spikeon/exoguitar/models/Back/Generator/photos/IMG_5319.JPEG

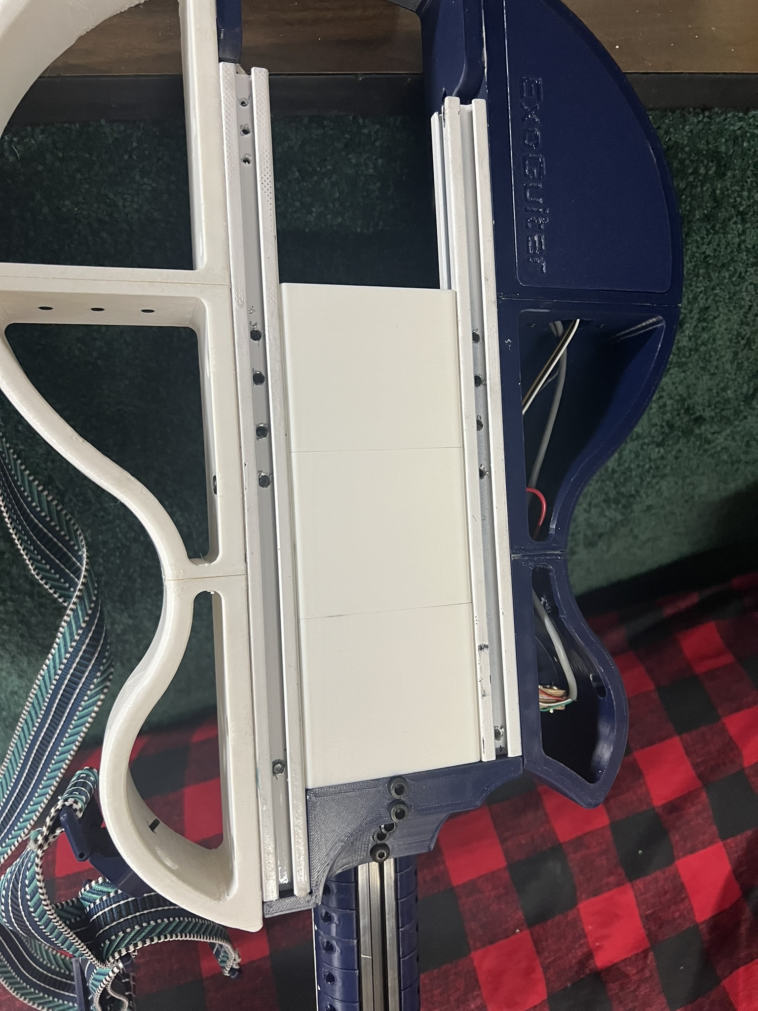
models/Back/Generator/photos/IMG_5319.JPEG
