spikeon/exoguitar/models/Bridge/Alnicov 6 Strings Saddle Headless/photos/IMG_4152.JPEG

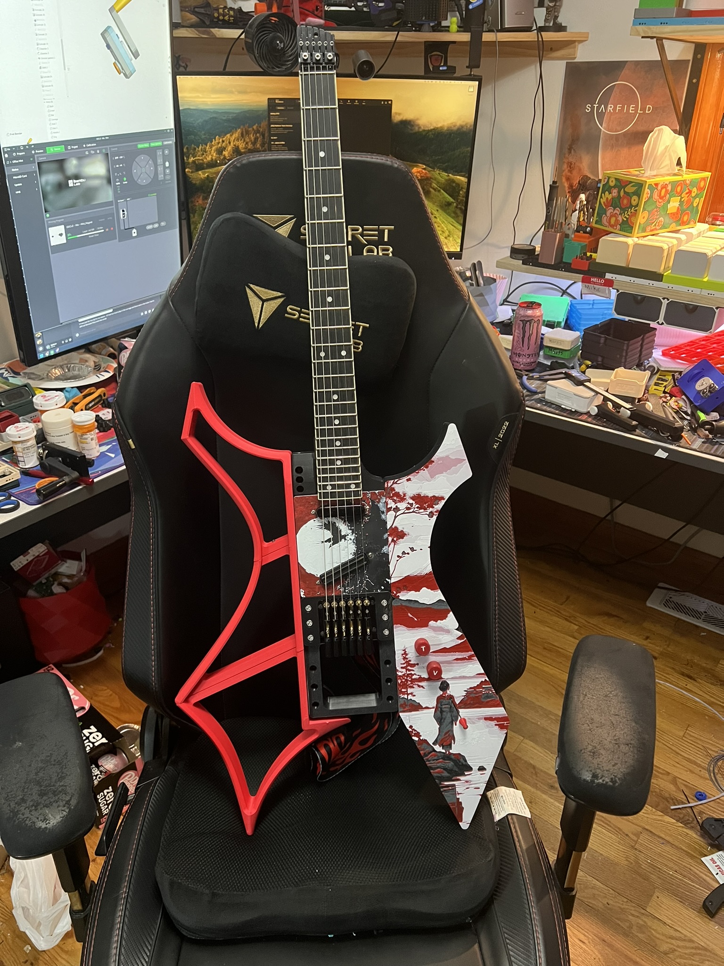
models/Bridge/Alnicov 6 Strings Saddle Headless/photos/IMG_4152.JPEG
