spikeon/exoguitar/models/Bridge/Alnicov 6 Strings Saddle Headless/photos/thumb.wide.png

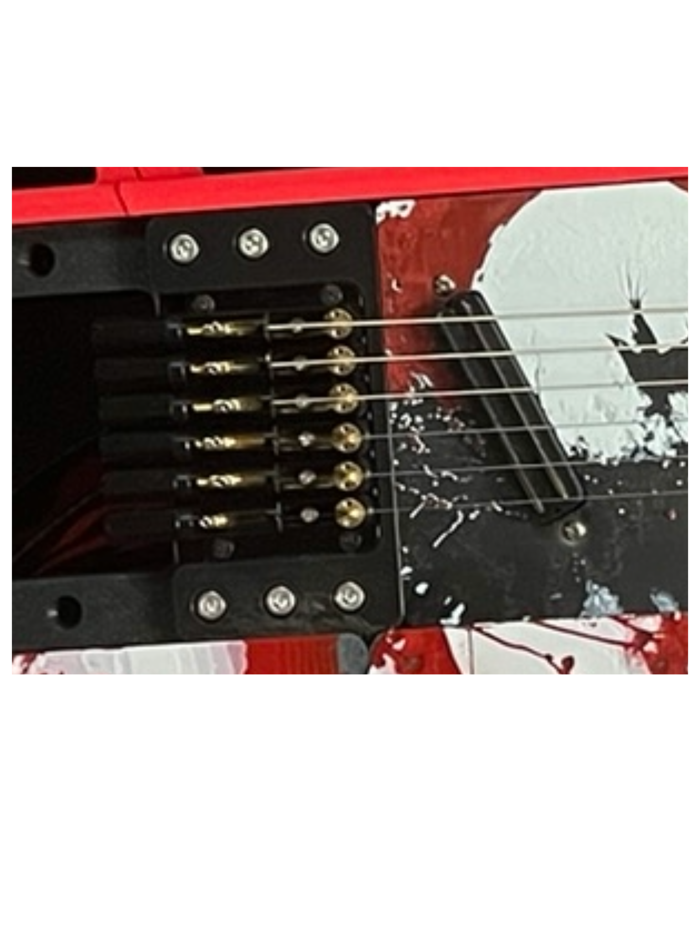
models/Bridge/Alnicov 6 Strings Saddle Headless/photos/thumb.wide.png
