spikeon/exoguitar/models/Bridge/Bearing Bridge/photos/thumb.wide.png

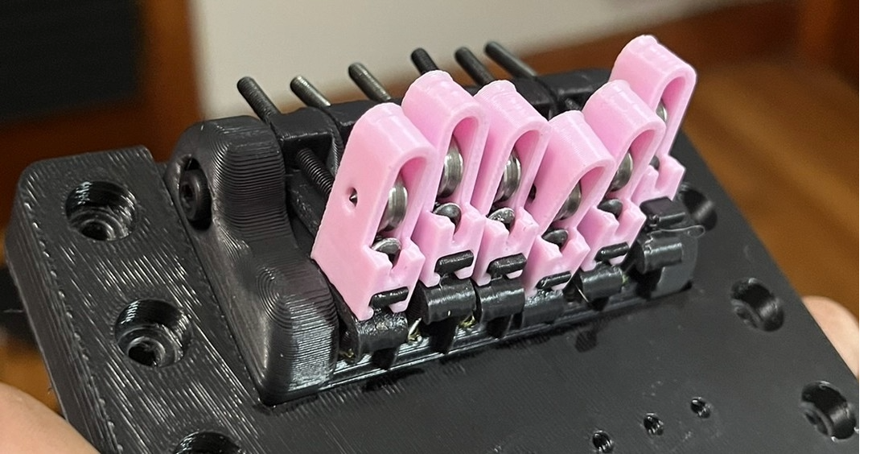
models/Bridge/Bearing Bridge/photos/thumb.wide.png
