spikeon/exoguitar/models/Bridge/Guyker Worm Bridge Plate/photos/thumb.wide.png

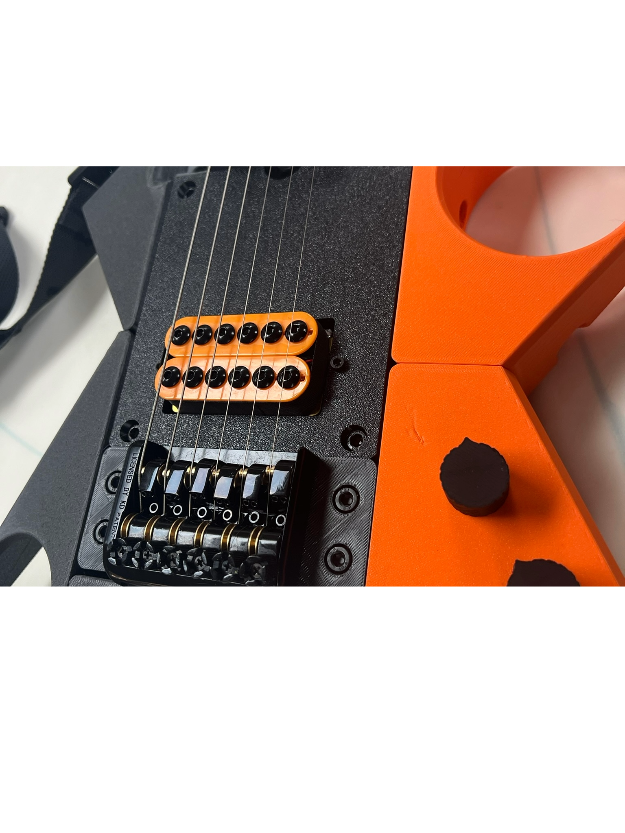
models/Bridge/Guyker Worm Bridge Plate/photos/thumb.wide.png
