spikeon/exoguitar/models/Bridge/Headless Bridge Plate/photos/thumb.wide.png

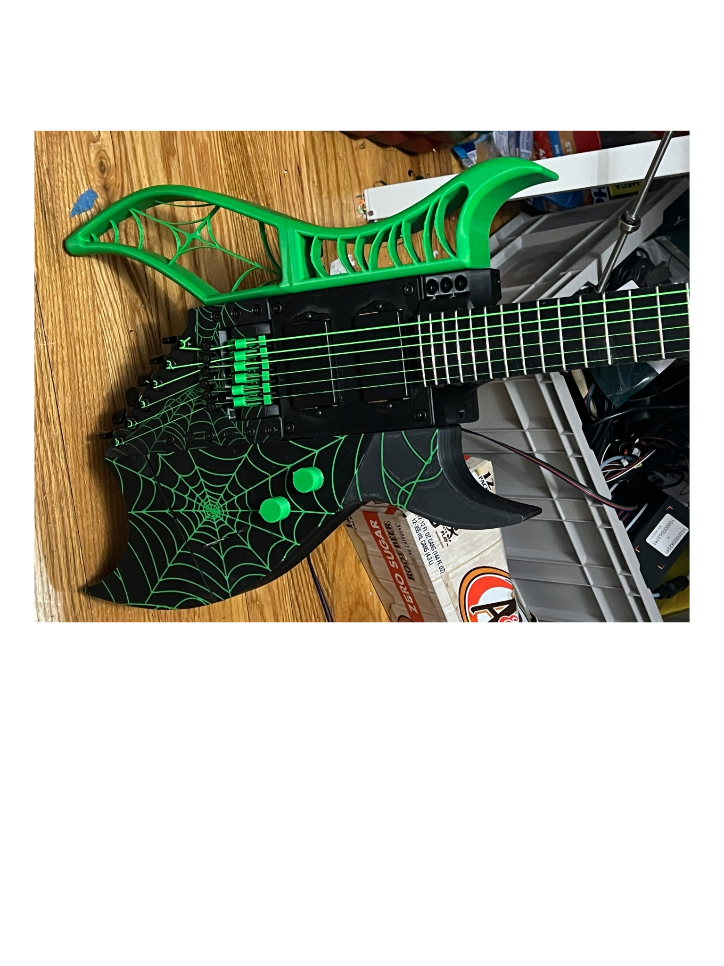
models/Bridge/Headless Bridge Plate/photos/thumb.wide.png
