spikeon/exoguitar/models/Bridge/OVSAL Headless Bridge Plate/photos/IMG_4946.JPEG

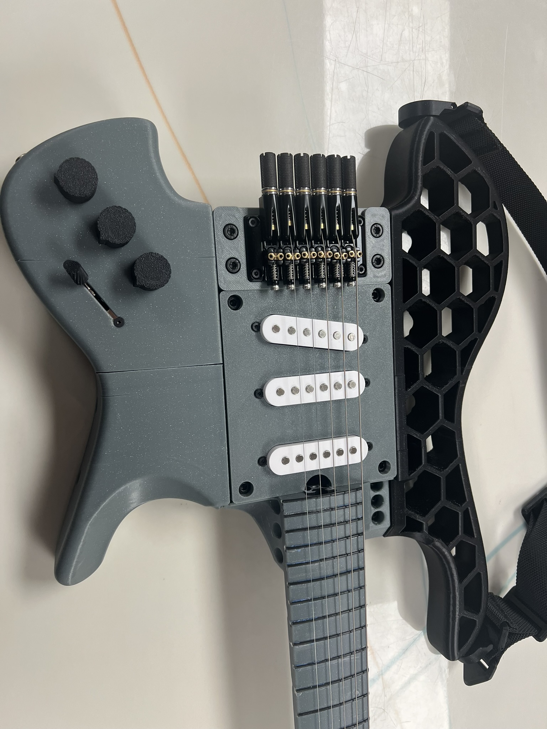
models/Bridge/OVSAL Headless Bridge Plate/photos/IMG_4946.JPEG
