spikeon/exoguitar/models/Bridge/OVSAL Headless Bridge Plate/photos/IMG_4947.JPEG

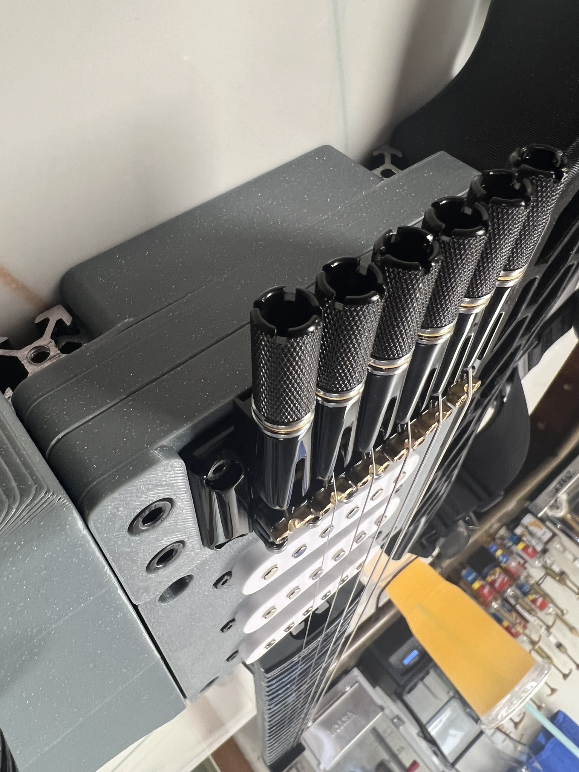
models/Bridge/OVSAL Headless Bridge Plate/photos/IMG_4947.JPEG
