spikeon/exoguitar/models/Bridge/Telecaster Plate/photos/IMG_4955 (1).JPEG

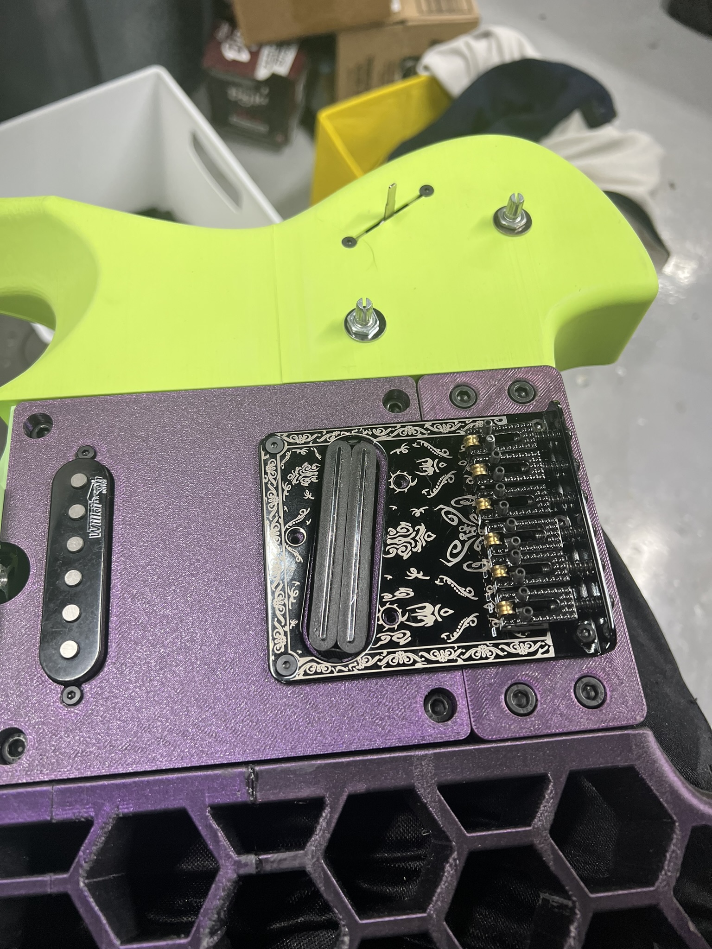
models/Bridge/Telecaster Plate/photos/IMG_4955 (1).JPEG
