spikeon/exoguitar/models/Bridge/Telecaster Plate/photos/IMG_5153.JPEG

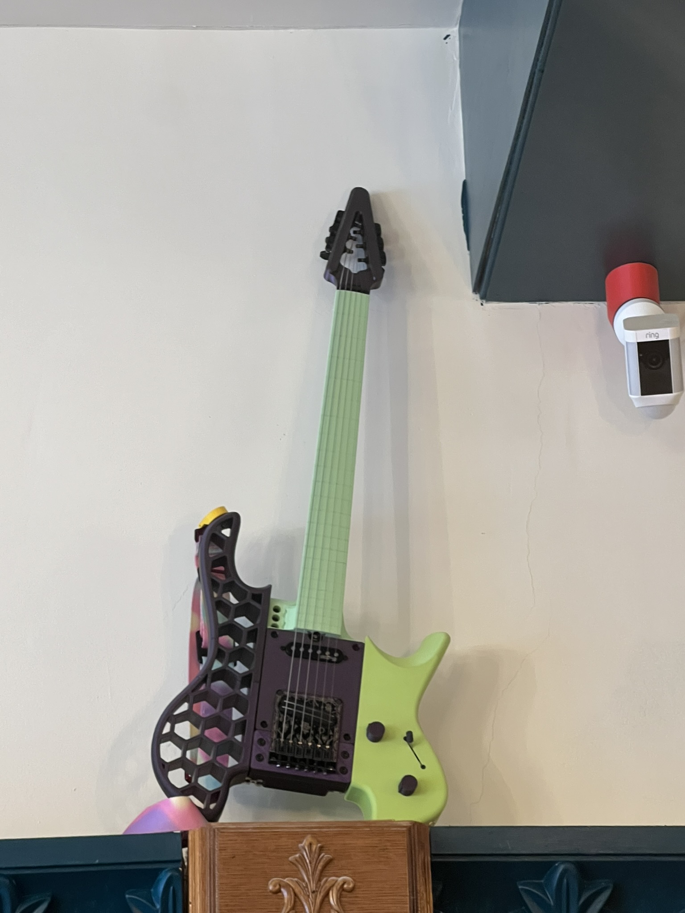
models/Bridge/Telecaster Plate/photos/IMG_5153.JPEG
