spikeon/exoguitar/models/Bridge/Tremelo/photos/IMG_4668.JPEG

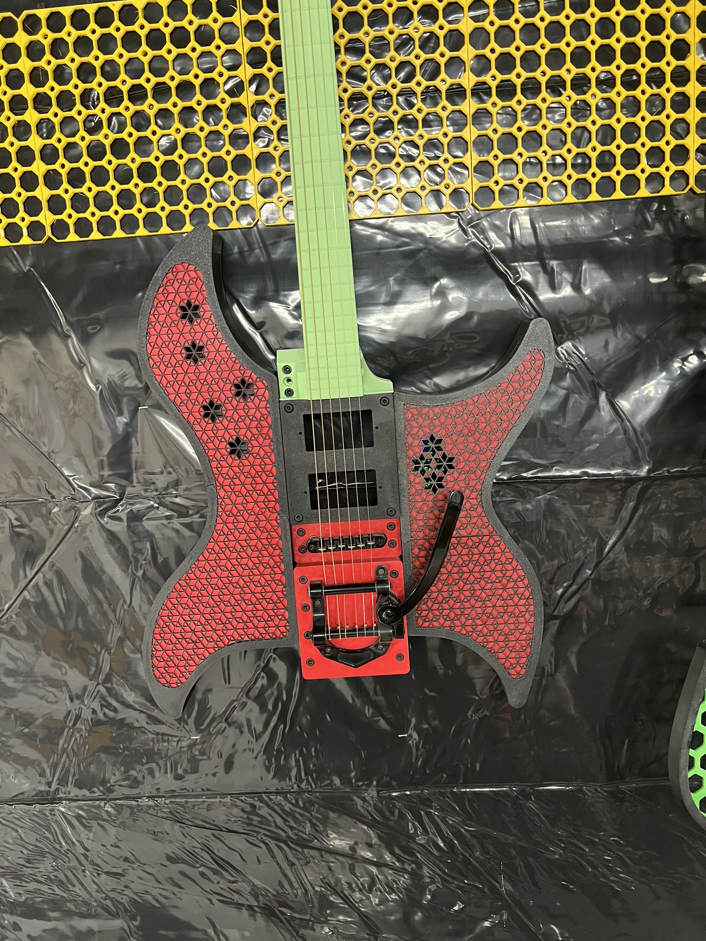
models/Bridge/Tremelo/photos/IMG_4668.JPEG
