spikeon/exoguitar/models/Bridge/Tremelo/photos/IMG_4672.JPEG

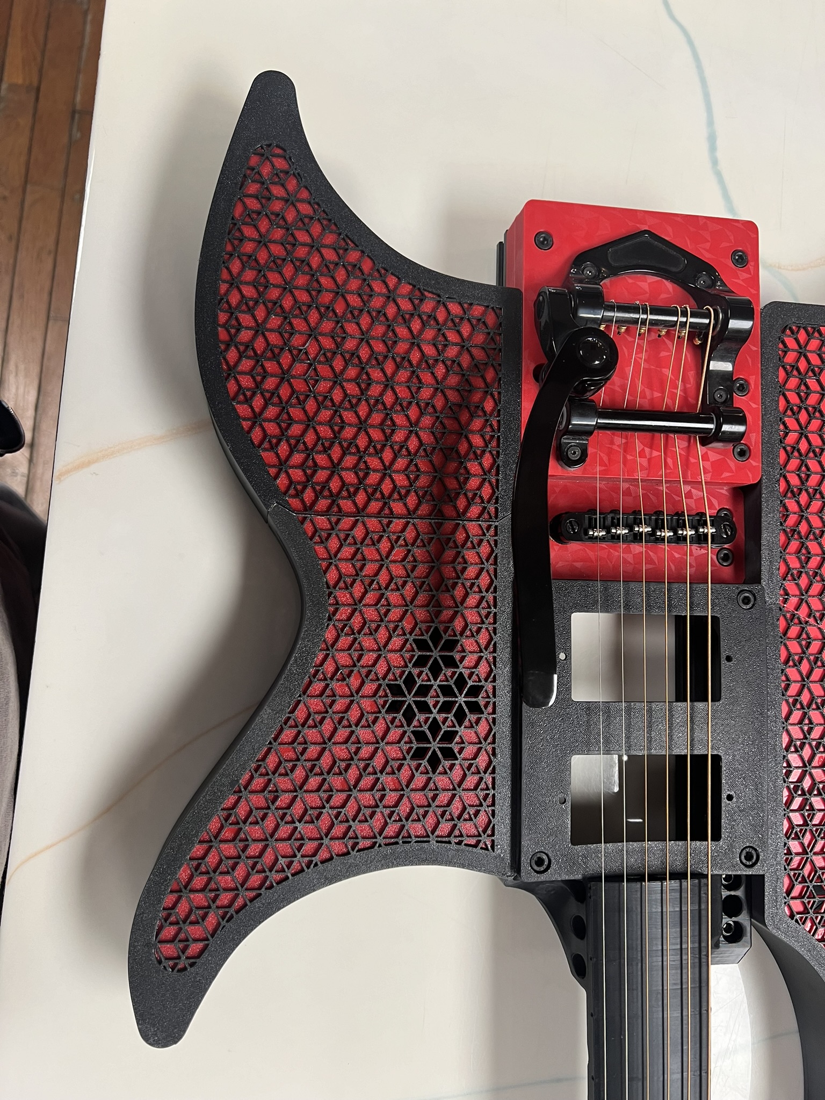
models/Bridge/Tremelo/photos/IMG_4672.JPEG
