spikeon/exoguitar/models/Bridge/Tremelo/photos/IMG_4673.JPEG

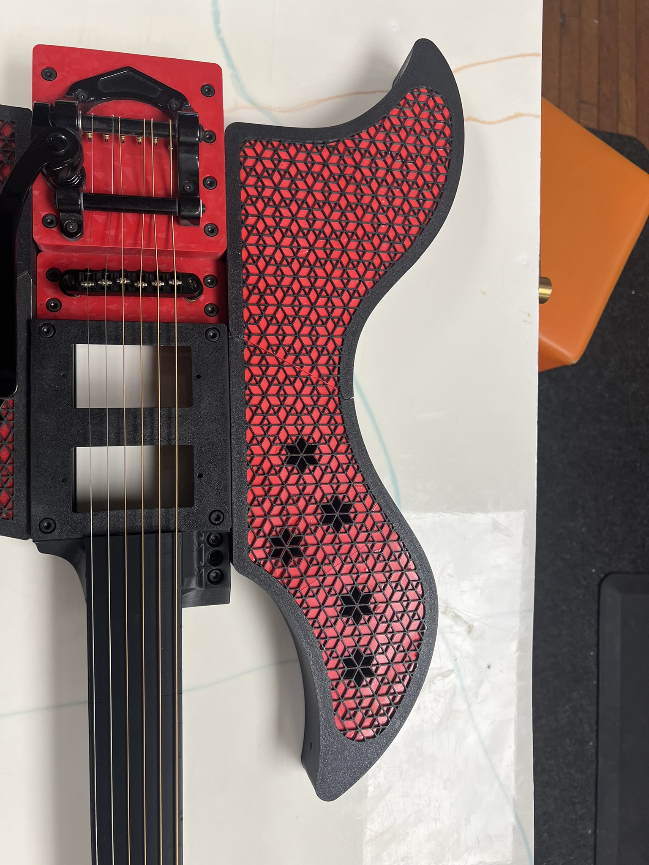
models/Bridge/Tremelo/photos/IMG_4673.JPEG
