spikeon/exoguitar/models/Bridge/Tremelo/photos/thumb.wide.png

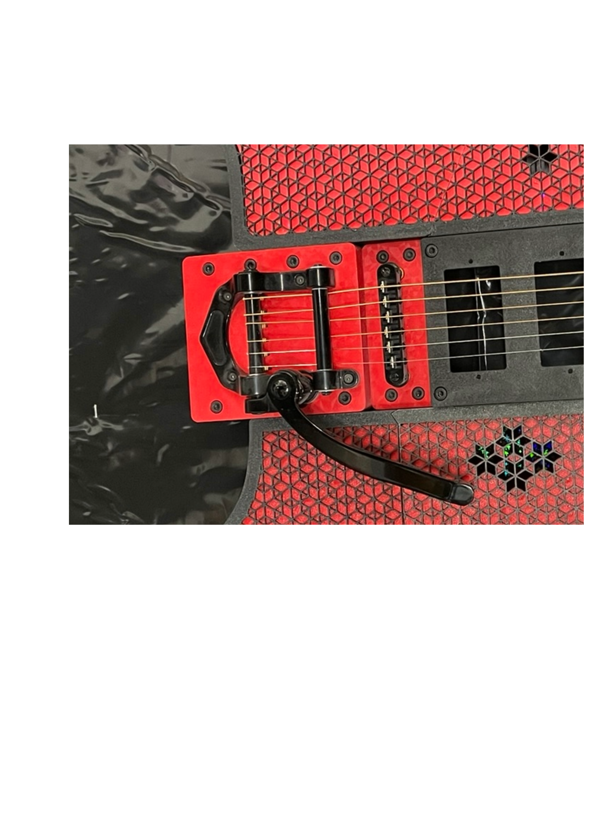
models/Bridge/Tremelo/photos/thumb.wide.png
