spikeon/exoguitar/models/Extras/Sanding Jig/photos/IMG_4849.JPEG

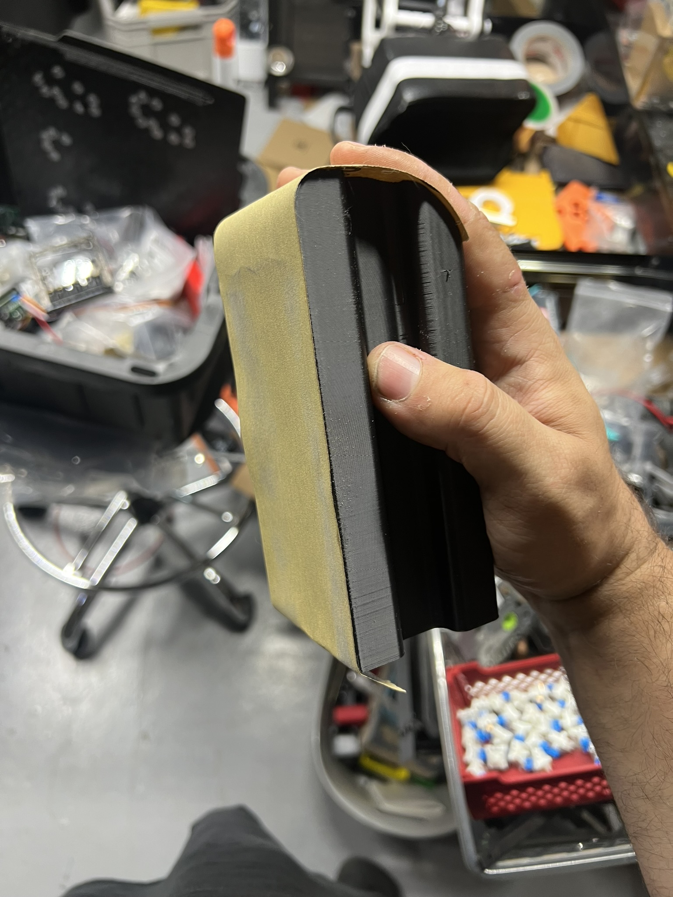
models/Extras/Sanding Jig/photos/IMG_4849.JPEG
