spikeon/exoguitar/models/Extras/Sanding Jig/photos/IMG_4850.JPEG

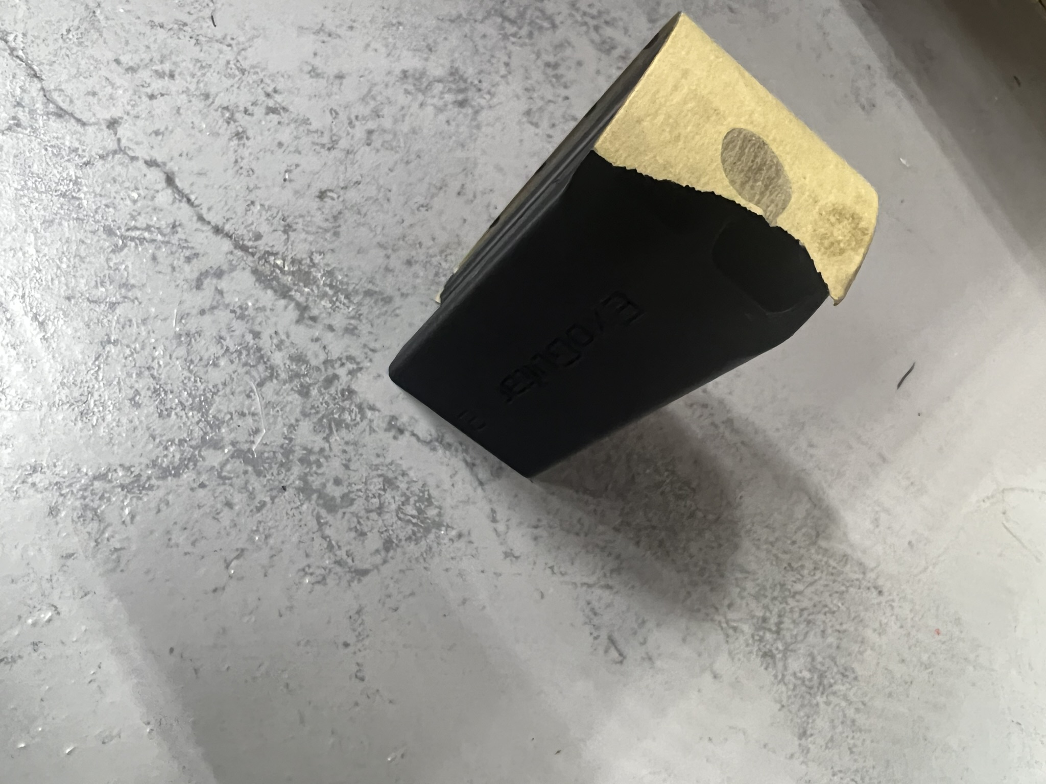
models/Extras/Sanding Jig/photos/IMG_4850.JPEG
