spikeon/exoguitar/models/Extras/Sanding Jig/photos/IMG_4852.JPEG

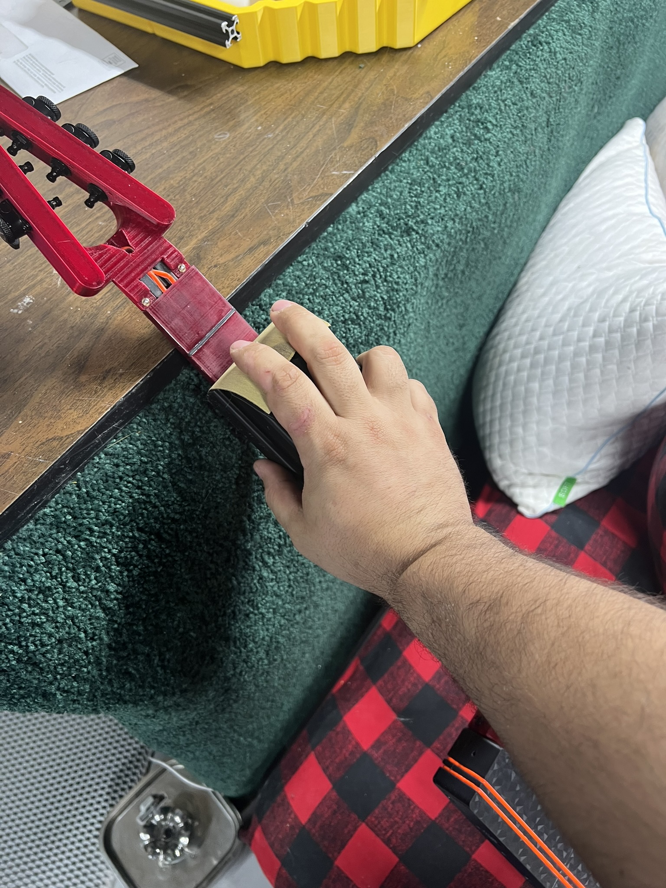
models/Extras/Sanding Jig/photos/IMG_4852.JPEG
