spikeon/exoguitar/models/Extras/Sanding Jig/photos/IMG_4853.JPEG

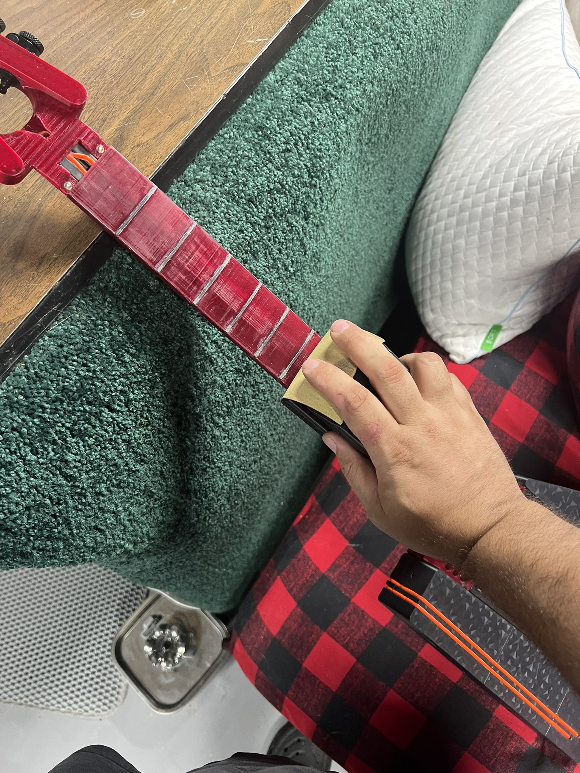
models/Extras/Sanding Jig/photos/IMG_4853.JPEG
