spikeon/exoguitar/models/Face Plates/Acoustic/ExoGuitar - Acoustic Core.png

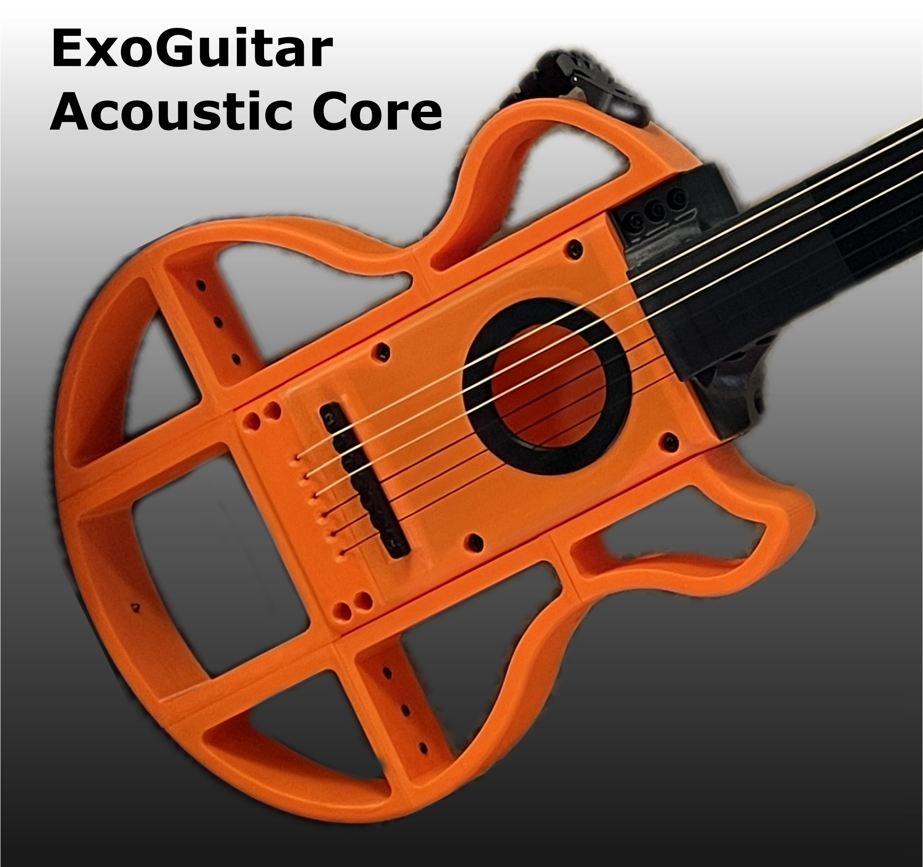
models/Face Plates/Acoustic/ExoGuitar - Acoustic Core.png
