spikeon/exoguitar/models/Face Plates/Dual Humbucker/photos/IMG_5579.JPEG

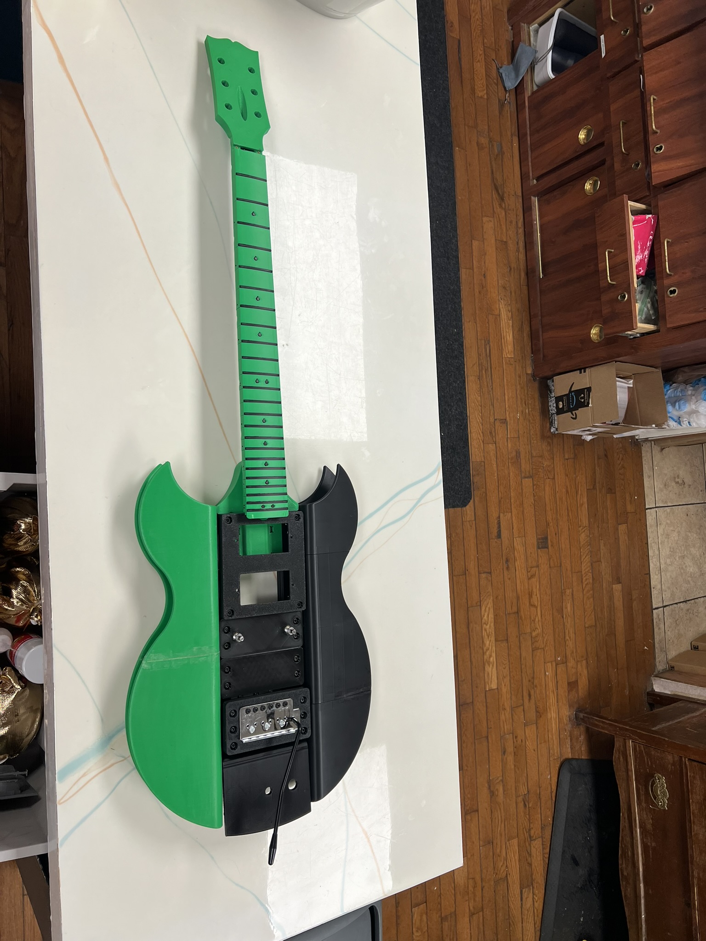
models/Face Plates/Dual Humbucker/photos/IMG_5579.JPEG
