spikeon/exoguitar/models/Face Plates/Dual Humbucker/photos/thumb.wide.png

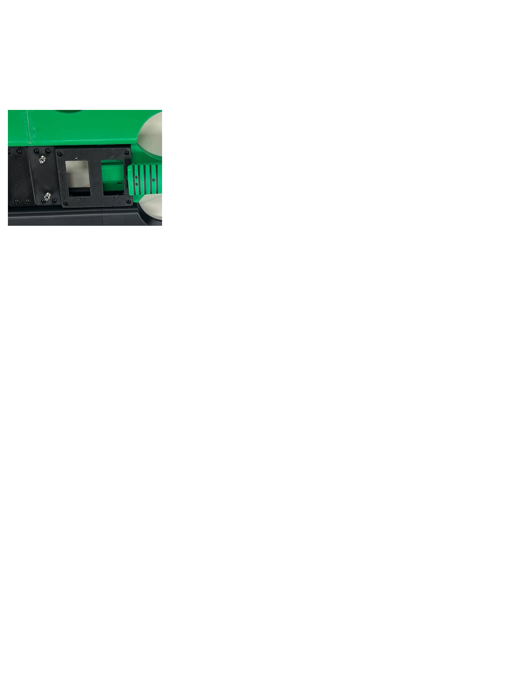
models/Face Plates/Dual Humbucker/photos/thumb.wide.png
