spikeon/exoguitar/models/Face Plates/Dual P90/photos/IMG_5286.JPEG

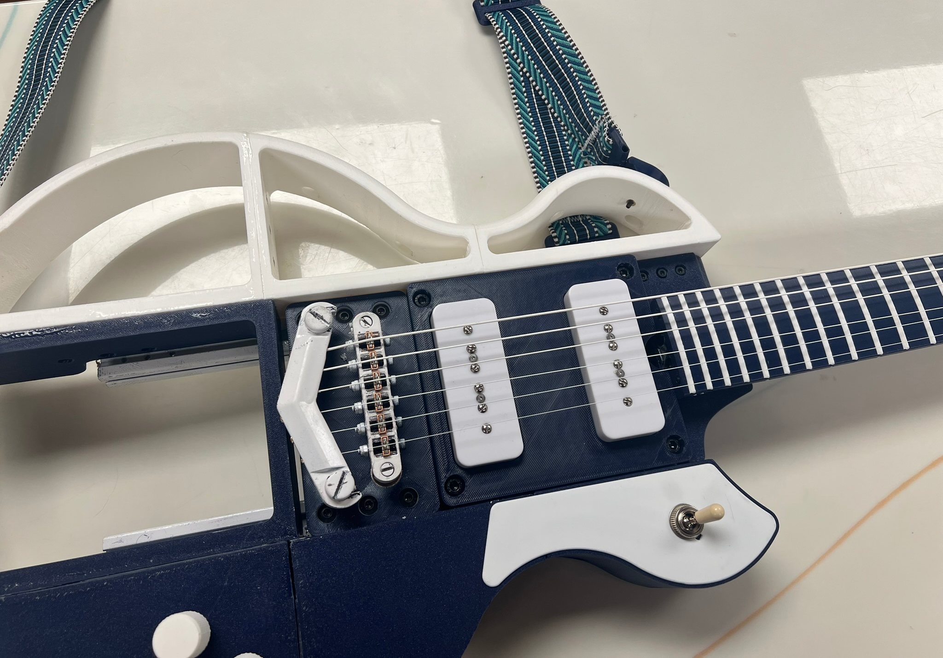
models/Face Plates/Dual P90/photos/IMG_5286.JPEG
