spikeon/exoguitar/models/Face Plates/Dual P90/photos/IMG_5287.JPEG

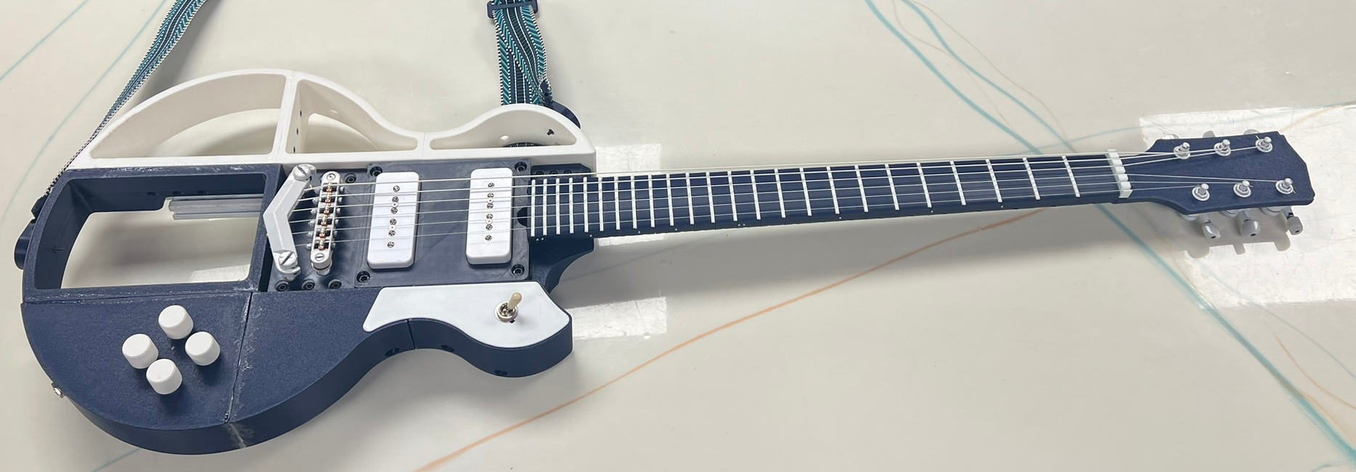
models/Face Plates/Dual P90/photos/IMG_5287.JPEG
