spikeon/exoguitar/models/Face Plates/Dual P90/photos/thumb.wide.JPEG

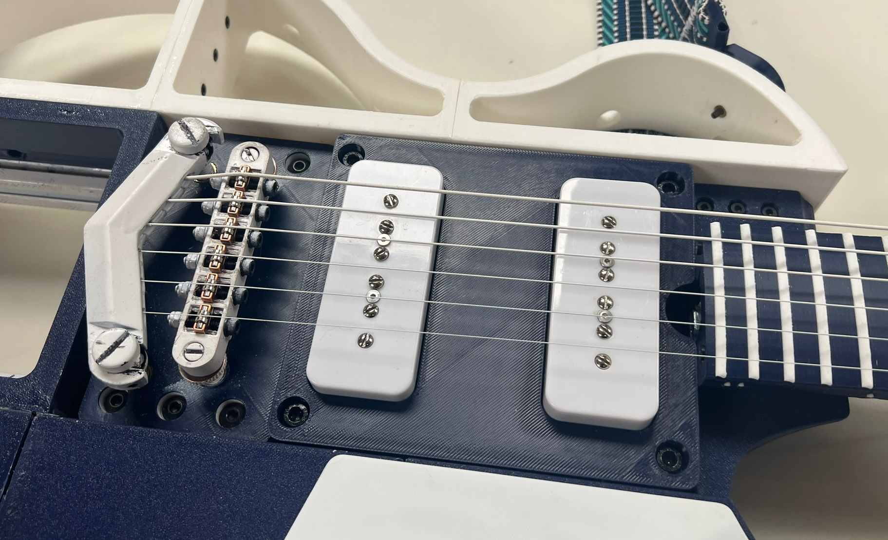
models/Face Plates/Dual P90/photos/thumb.wide.JPEG
