spikeon/exoguitar/models/Face Plates/Dual P90/photos/thumb.wide.png

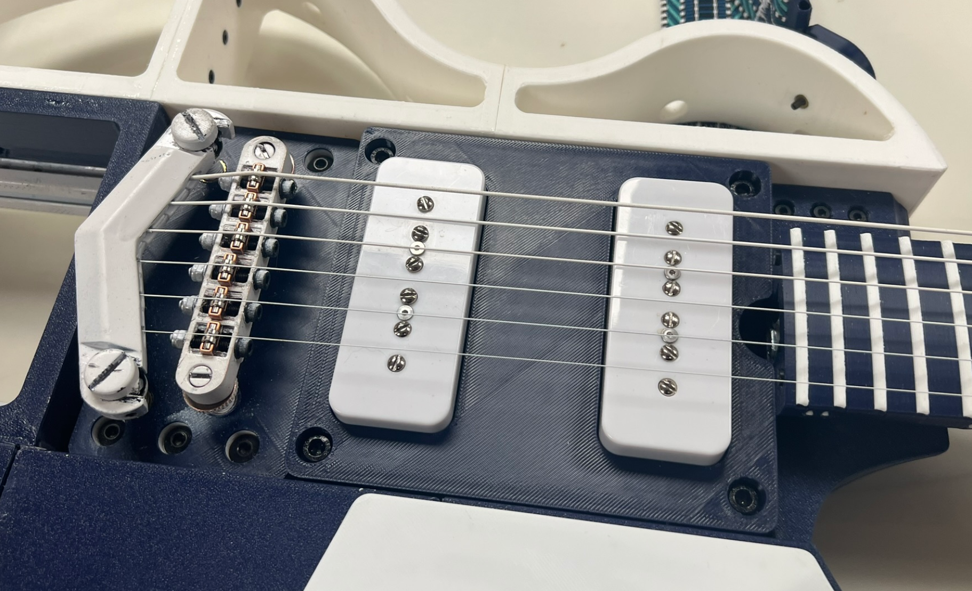
models/Face Plates/Dual P90/photos/thumb.wide.png
