spikeon/exoguitar/models/Face Plates/HSS/IMG_6287.JPEG

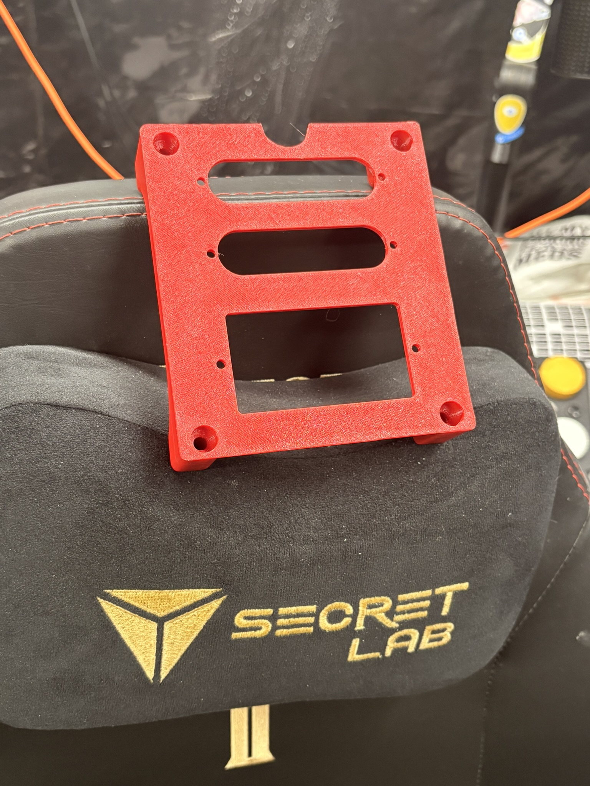
models/Face Plates/HSS/IMG_6287.JPEG
