spikeon/exoguitar/models/Face Plates/Single Humbucker - Bridge/photos/IMG_5298.JPEG

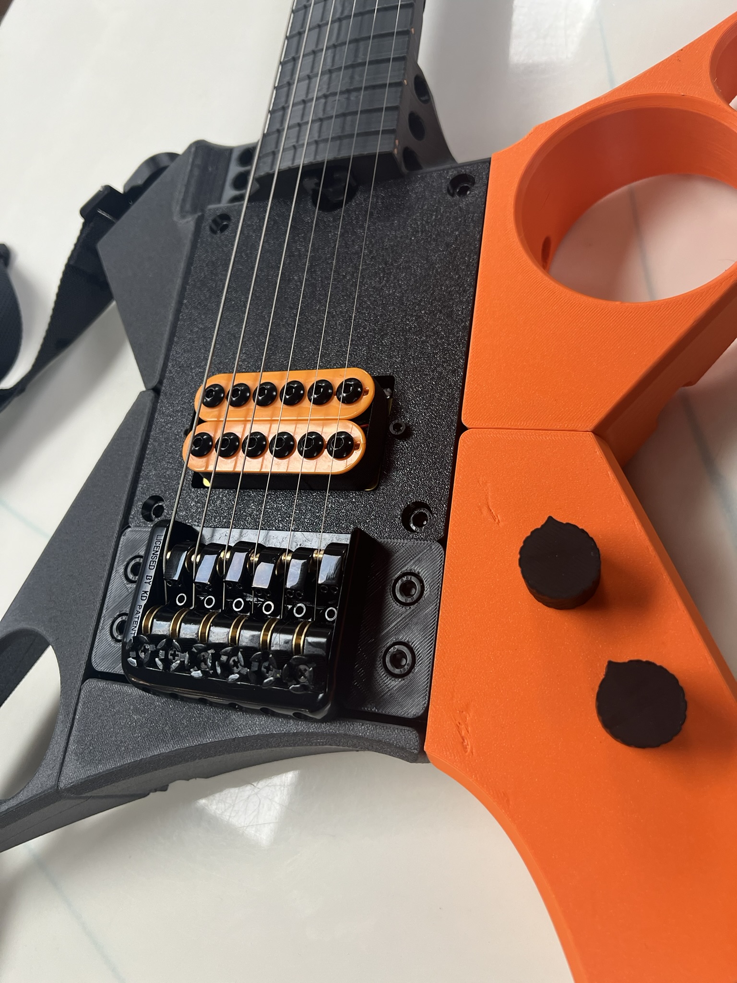
models/Face Plates/Single Humbucker - Bridge/photos/IMG_5298.JPEG
