spikeon/exoguitar/models/Face Plates/Single Humbucker - Centered/photos/IMG_5016.JPEG

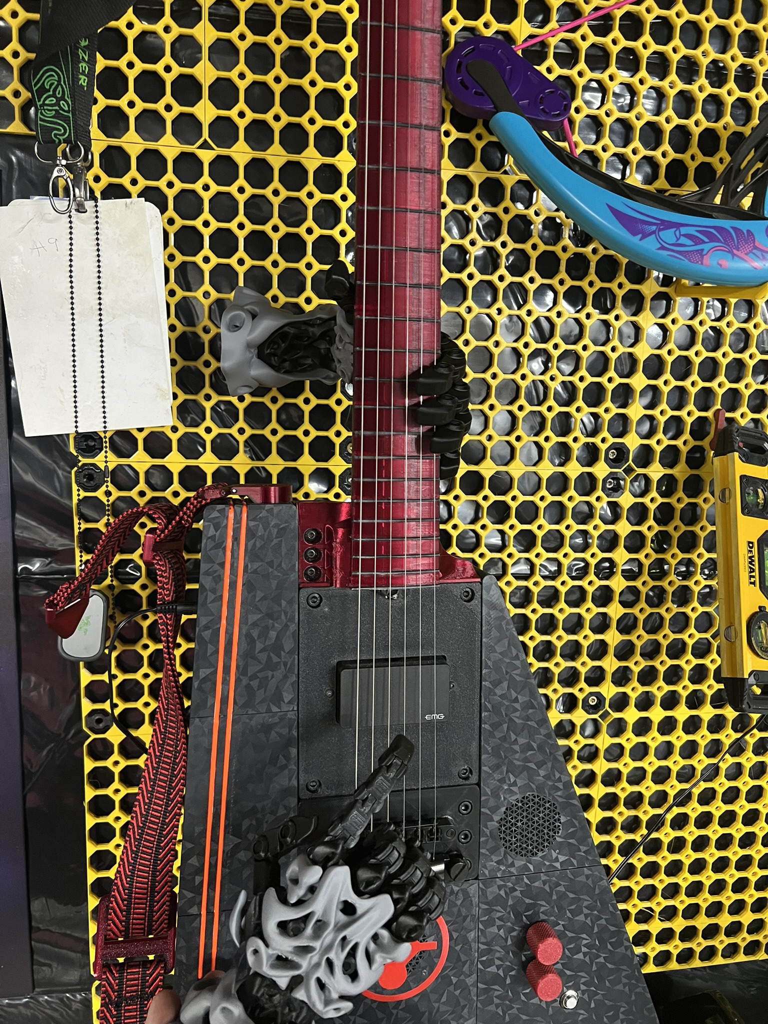
models/Face Plates/Single Humbucker - Centered/photos/IMG_5016.JPEG
