spikeon/exoguitar/models/Face Plates/Single Humbucker - Centered/photos/thumb.wide.png

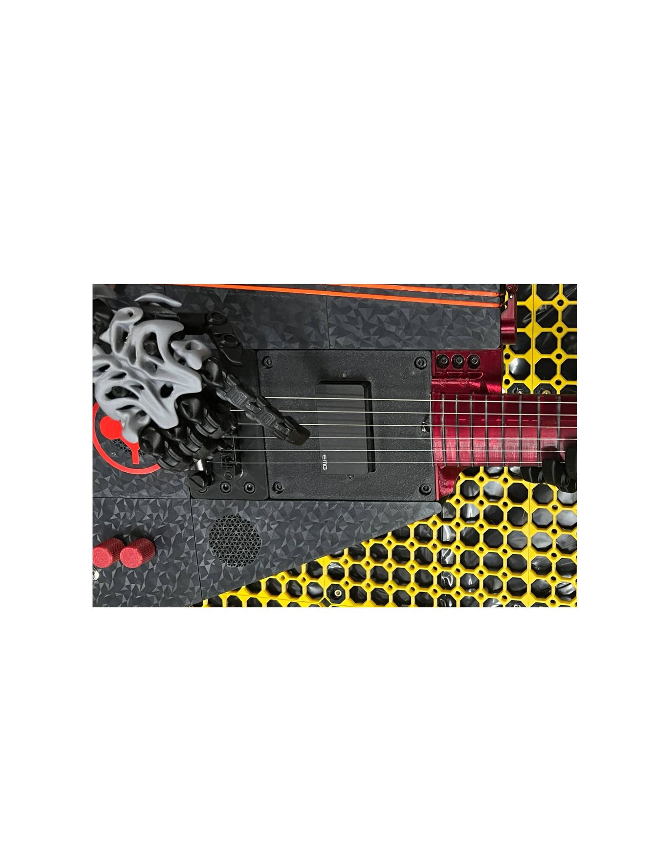
models/Face Plates/Single Humbucker - Centered/photos/thumb.wide.png
