spikeon/exoguitar/models/Face Plates/SSS/photos/IMG_4884.JPEG

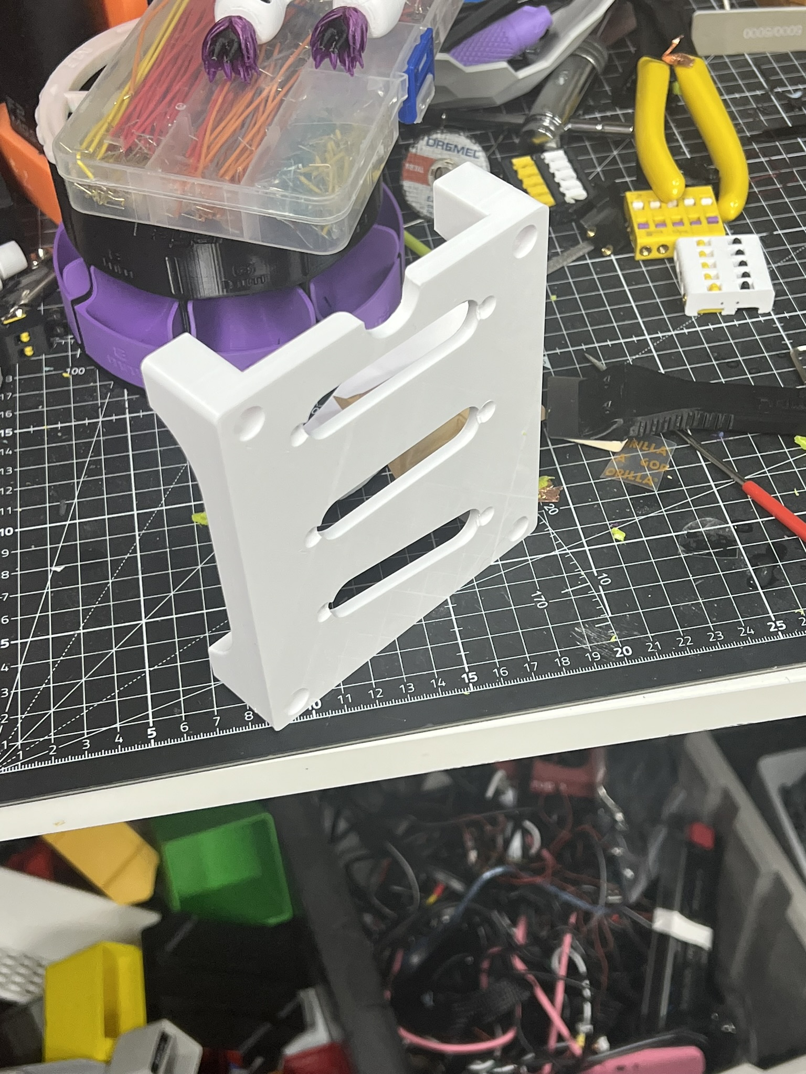
models/Face Plates/SSS/photos/IMG_4884.JPEG
