spikeon/exoguitar/models/Face Plates/Telecaster Plate/photos/IMG_4956.JPEG

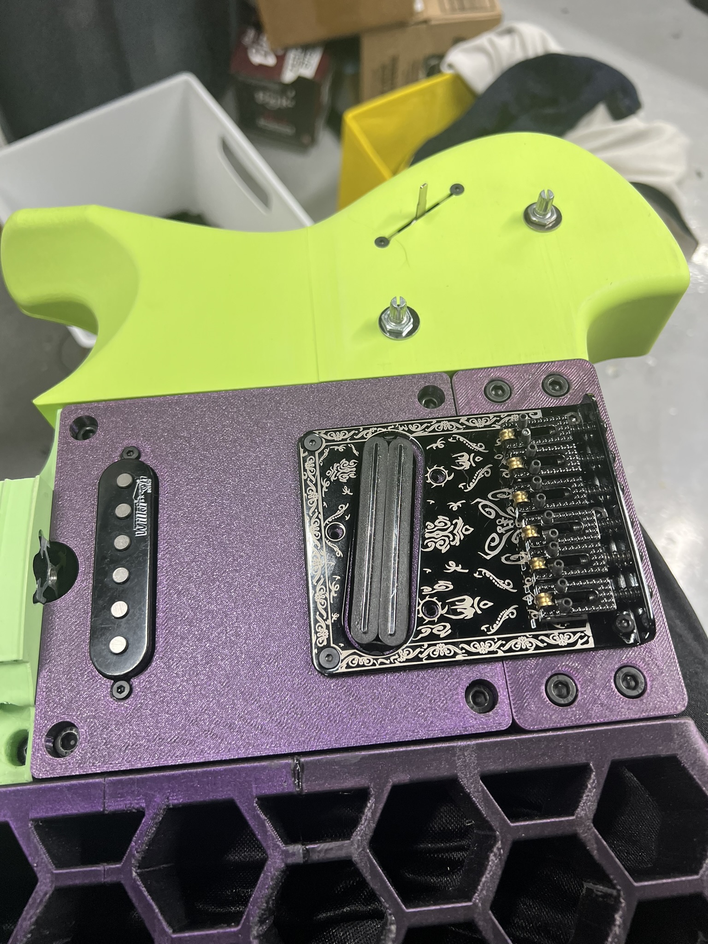
models/Face Plates/Telecaster Plate/photos/IMG_4956.JPEG
