spikeon/exoguitar/models/Face Plates/Telecaster Plate/photos/thumb.wide.png

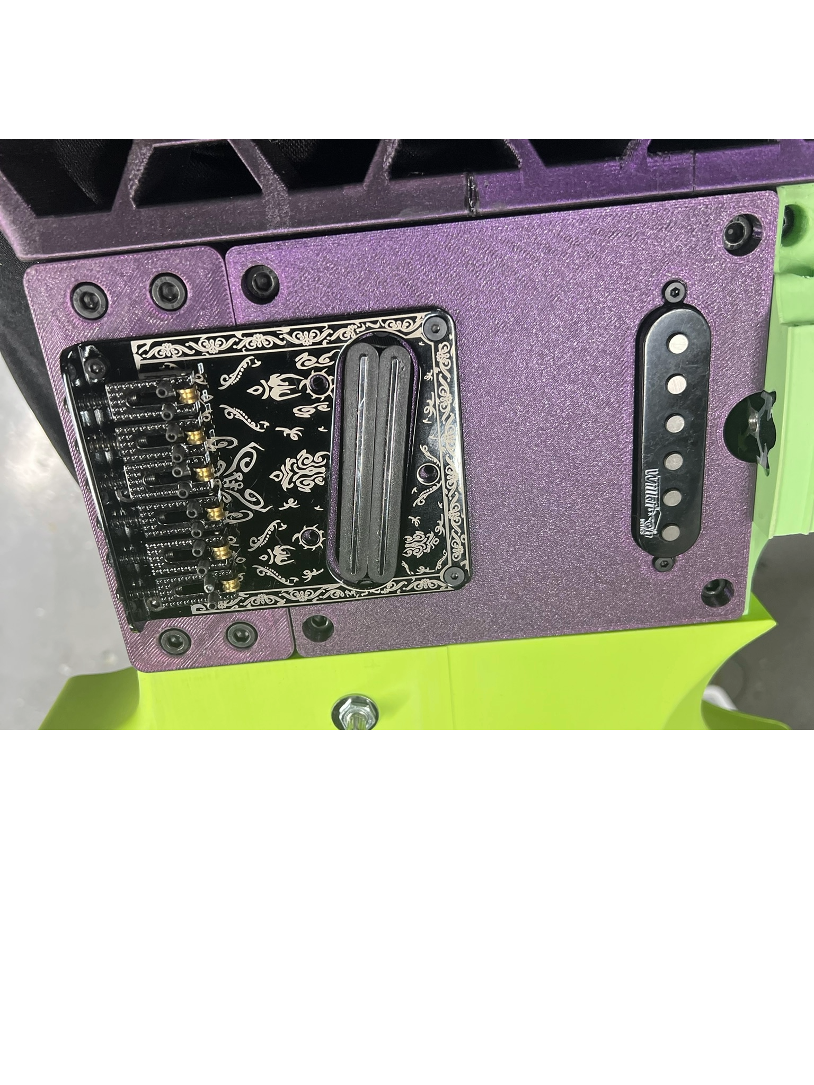
models/Face Plates/Telecaster Plate/photos/thumb.wide.png
