spikeon/exoguitar/models/Face Plates/Telecaster/photos/IMG_4152.png

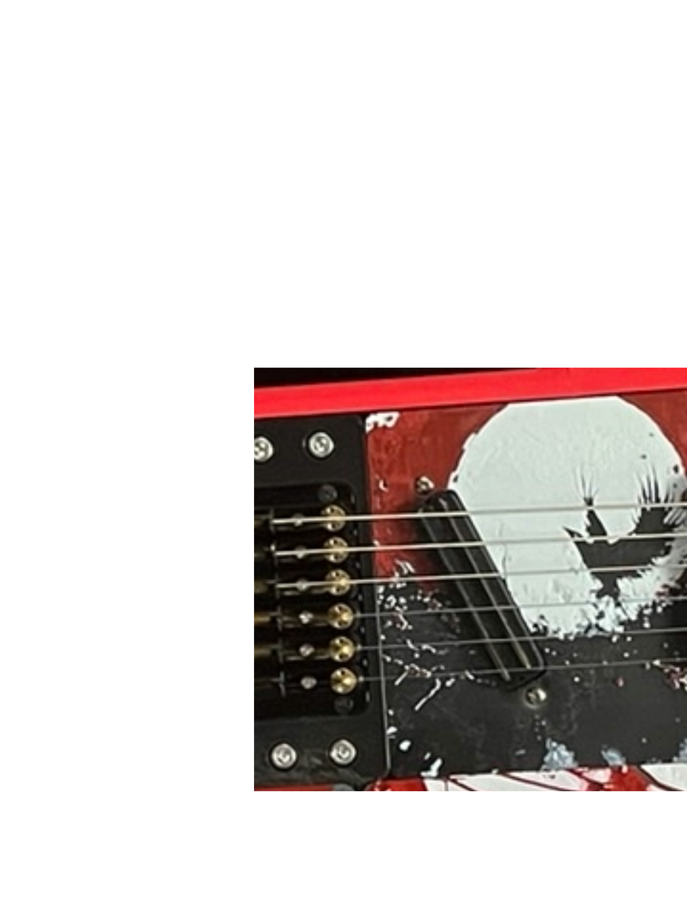
models/Face Plates/Telecaster/photos/IMG_4152.png
