spikeon/exoguitar/models/Face Plates/Telecaster/photos/thumb.wide.png

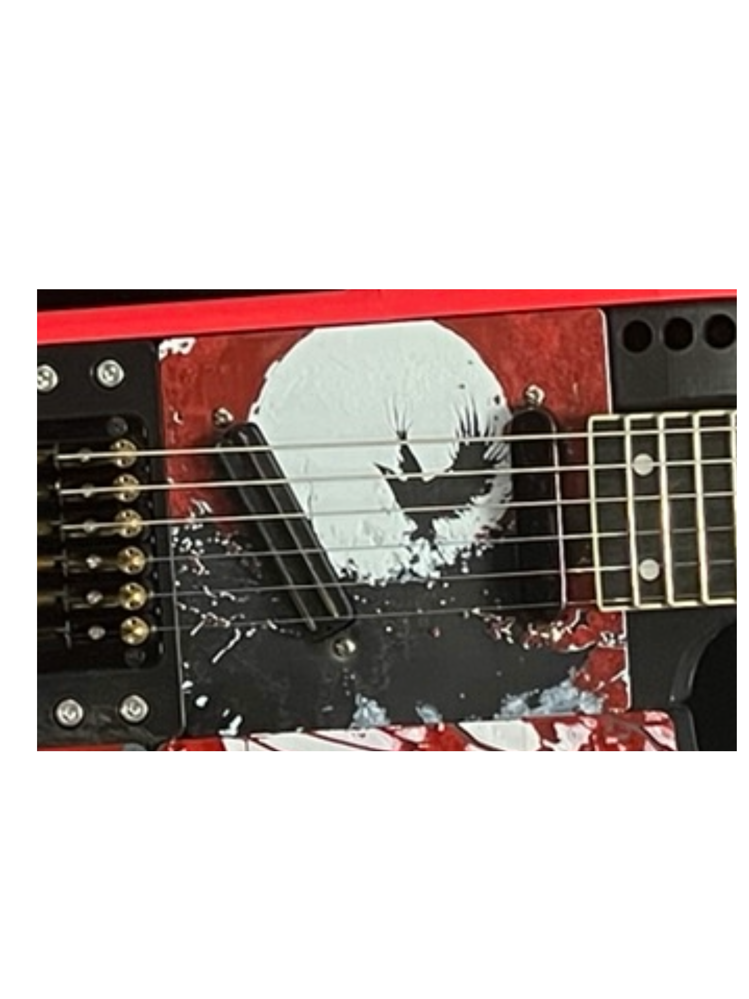
models/Face Plates/Telecaster/photos/thumb.wide.png
