spikeon/exoguitar/models/Head/Arasaka/photos/IMG_4816.JPEG

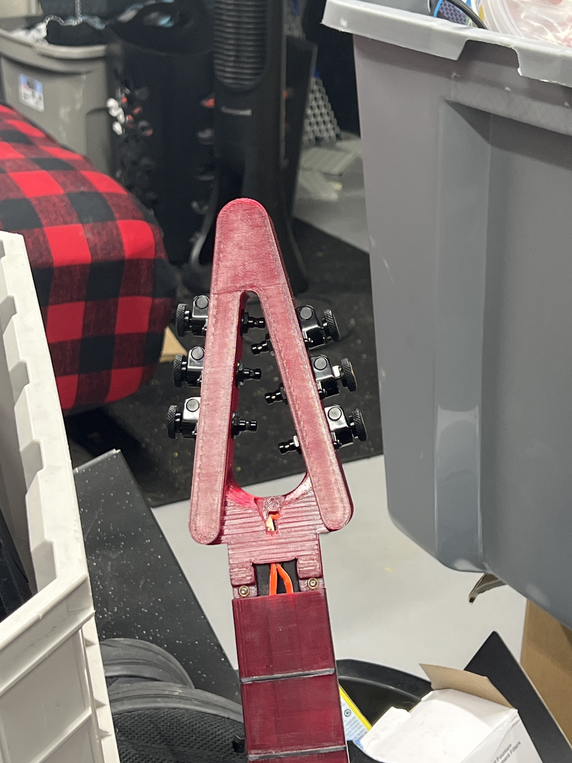
models/Head/Arasaka/photos/IMG_4816.JPEG
