spikeon/exoguitar/models/Head/Arasaka/photos/IMG_4985 (1).JPEG

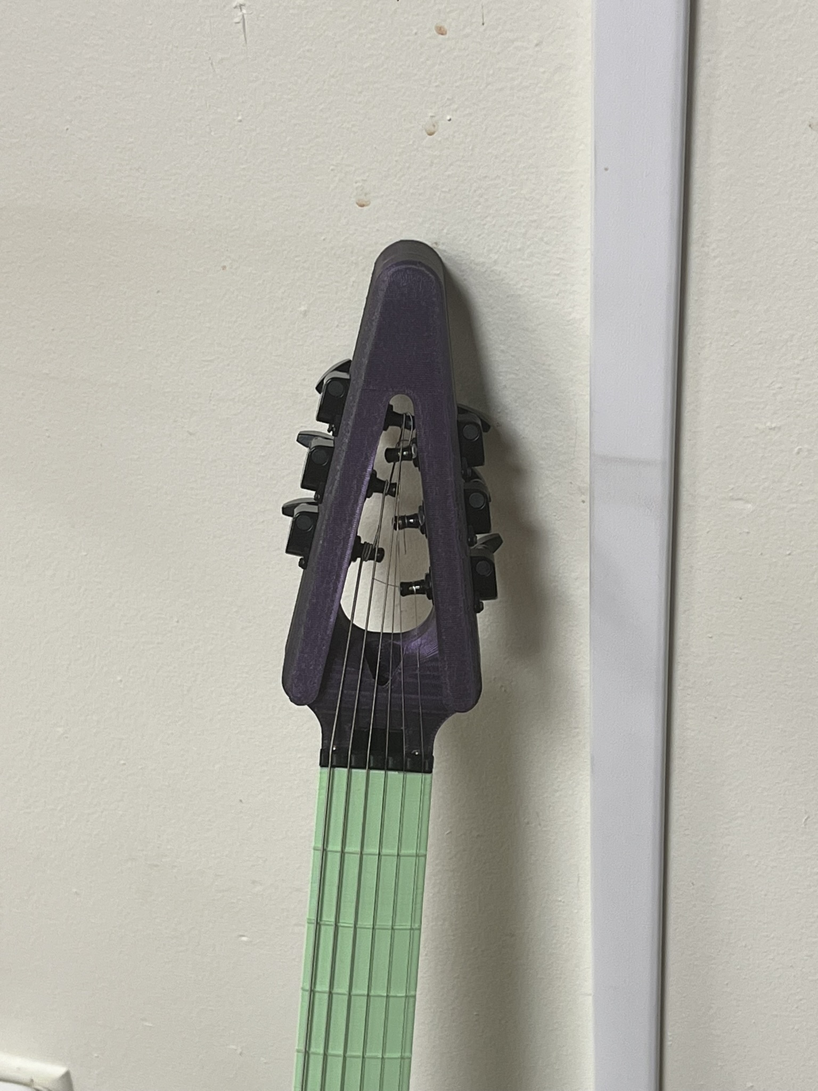
models/Head/Arasaka/photos/IMG_4985 (1).JPEG
