spikeon/exoguitar/models/Head/Arasaka/photos/IMG_4986 (1).JPEG

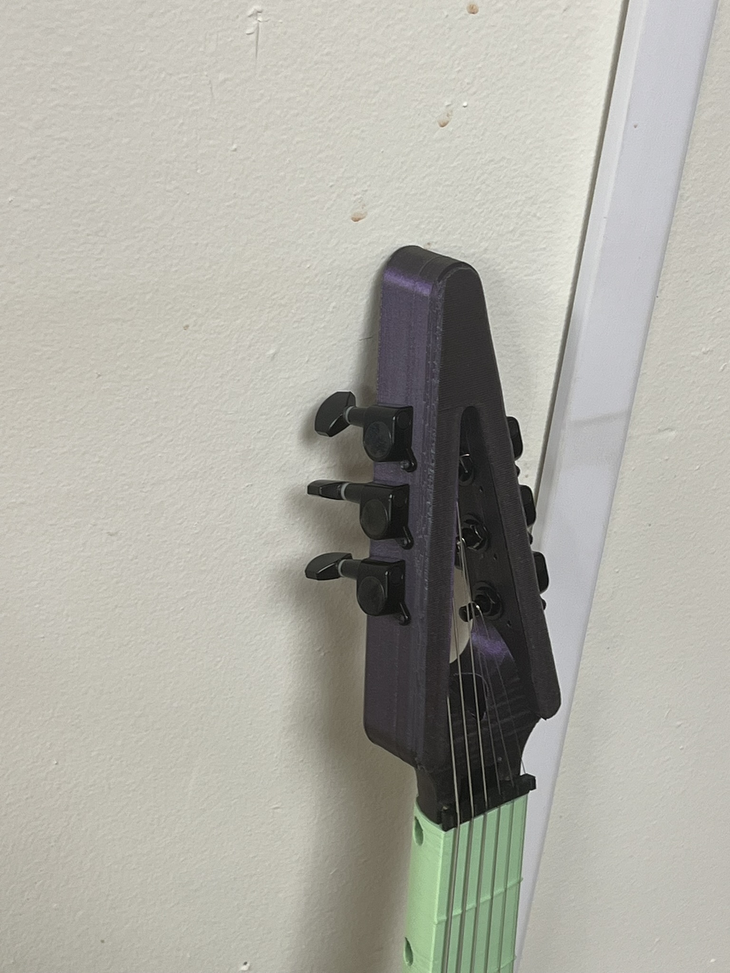
models/Head/Arasaka/photos/IMG_4986 (1).JPEG
