spikeon/exoguitar/models/Head/Arasaka/photos/IMG_5007.JPEG

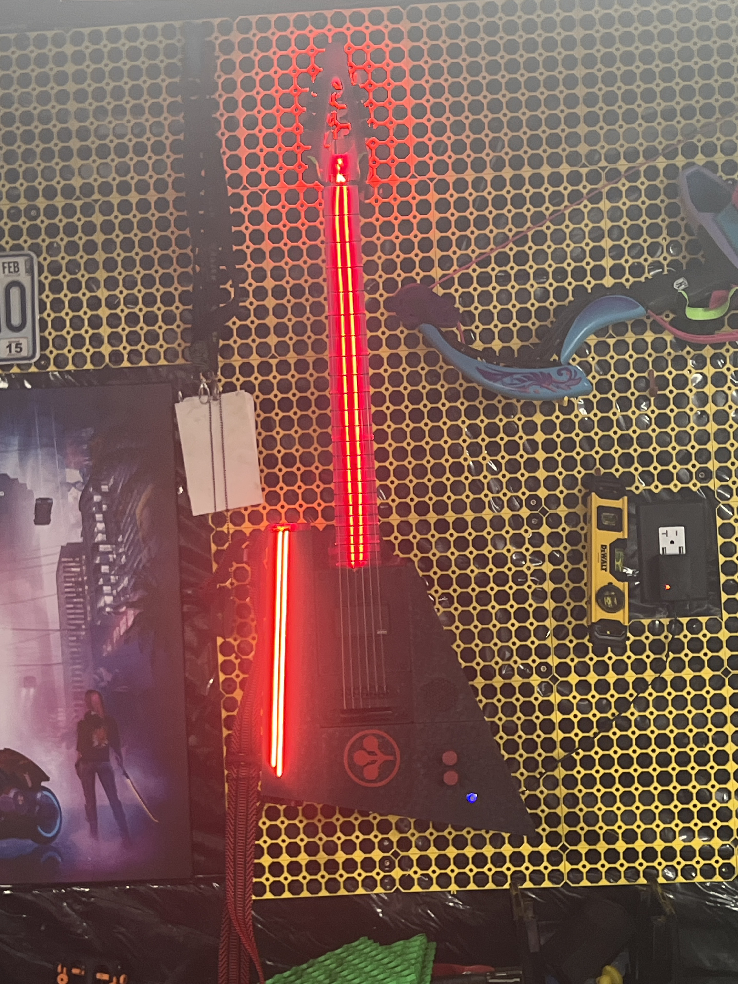
models/Head/Arasaka/photos/IMG_5007.JPEG
