spikeon/exoguitar/models/Head/Arasaka/photos/IMG_5030.JPEG

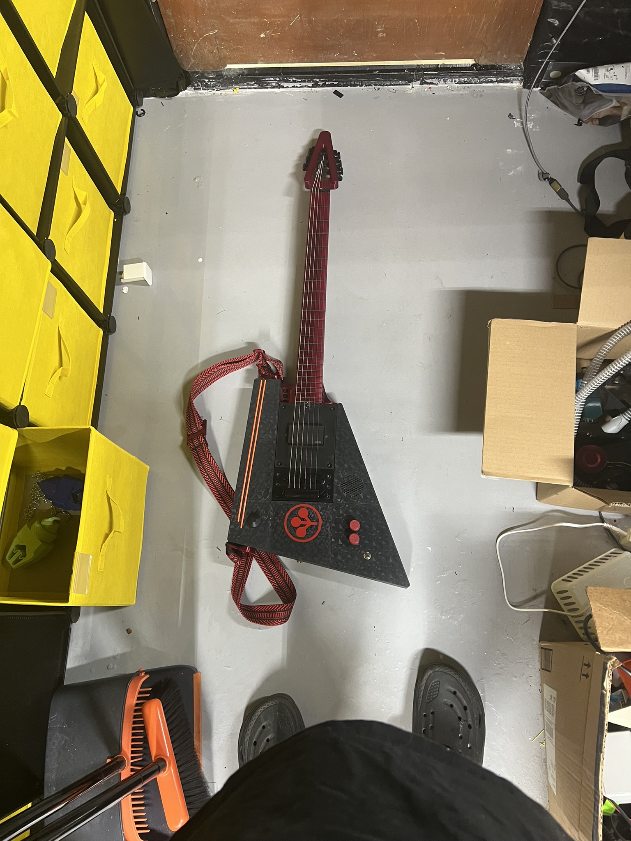
models/Head/Arasaka/photos/IMG_5030.JPEG
