spikeon/exoguitar/models/Head/Arasaka/photos/IMG_5031.JPEG

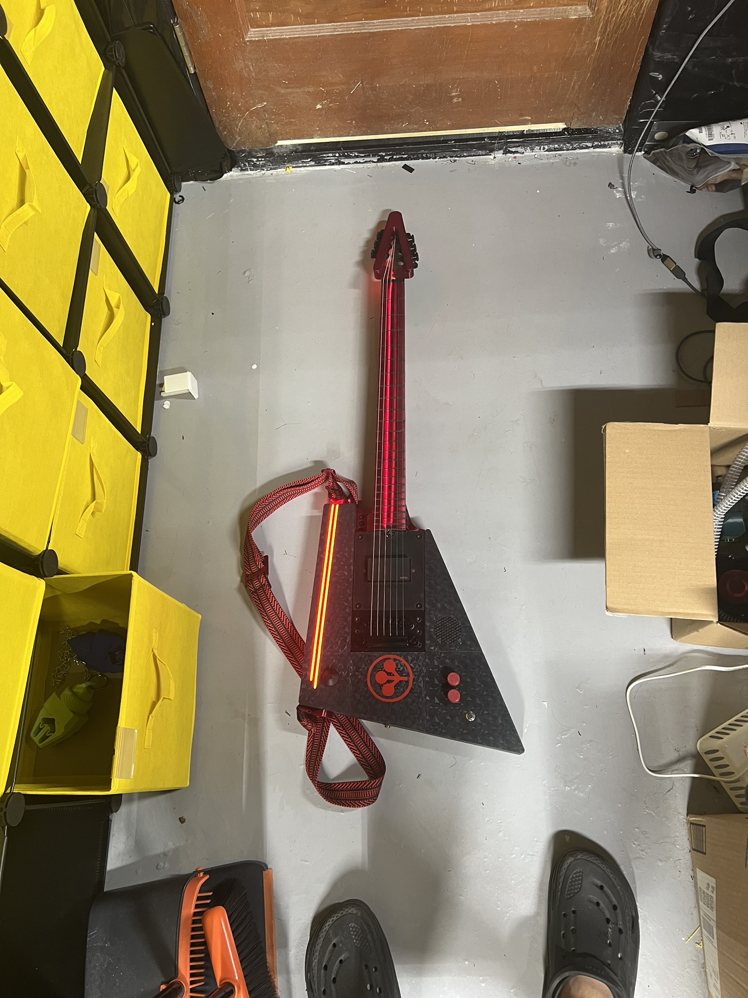
models/Head/Arasaka/photos/IMG_5031.JPEG
