spikeon/exoguitar/models/Head/Arasaka/photos/IMG_5032.JPEG

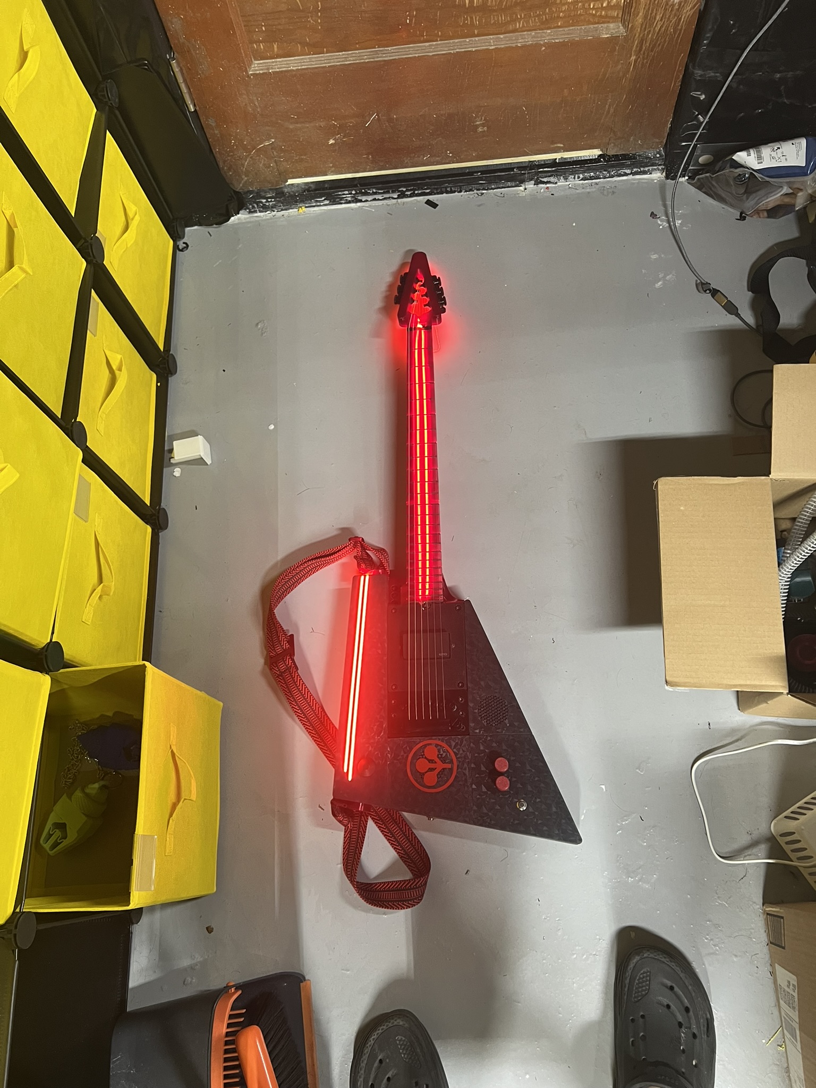
models/Head/Arasaka/photos/IMG_5032.JPEG
