spikeon/exoguitar/models/Head/Arasaka/photos/thumb.tall.png

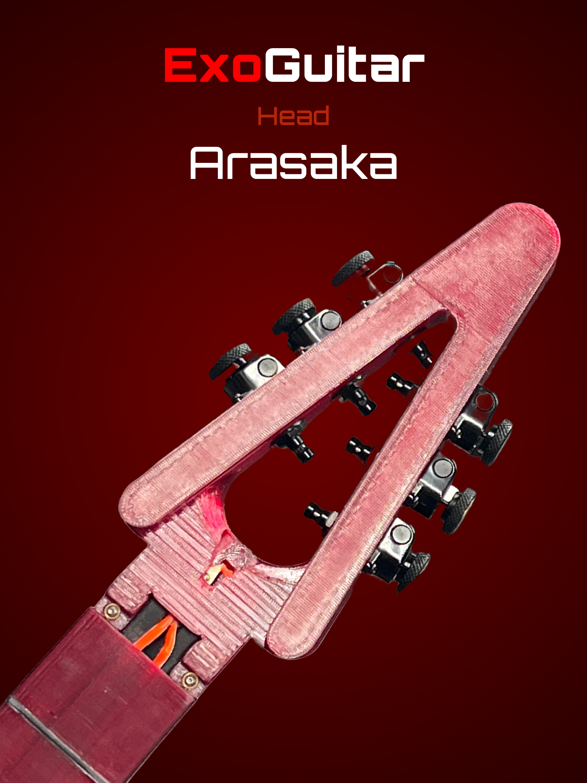
models/Head/Arasaka/photos/thumb.tall.png
