spikeon/exoguitar/models/Head/Arasaka/photos/thumb.wide.png

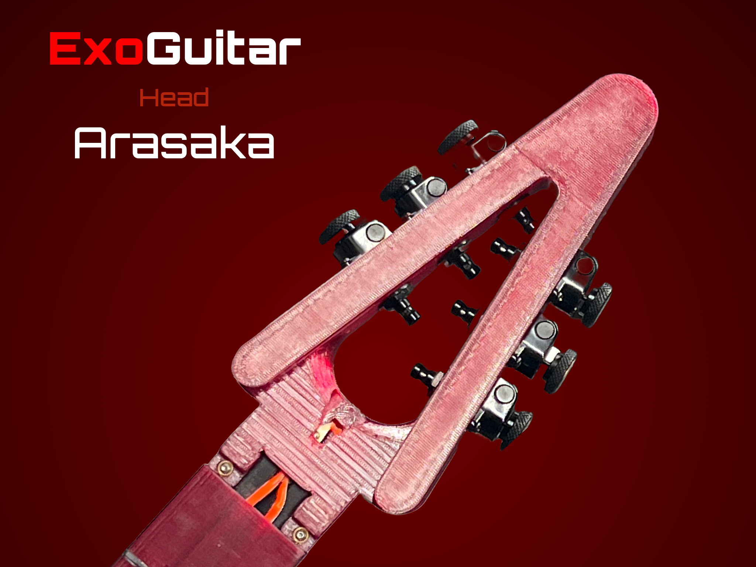
models/Head/Arasaka/photos/thumb.wide.png
