spikeon/exoguitar/models/Head/Firebird/photos/IMG_4457.JPEG

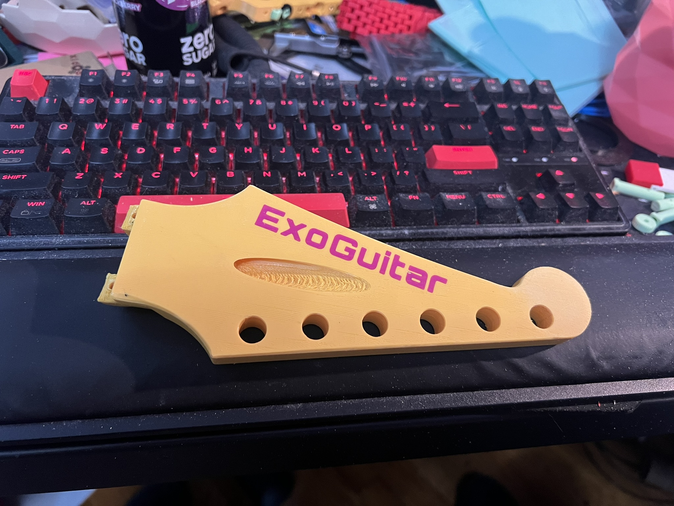
models/Head/Firebird/photos/IMG_4457.JPEG
