spikeon/exoguitar/models/Head/Firebird/photos/IMG_4458.JPEG

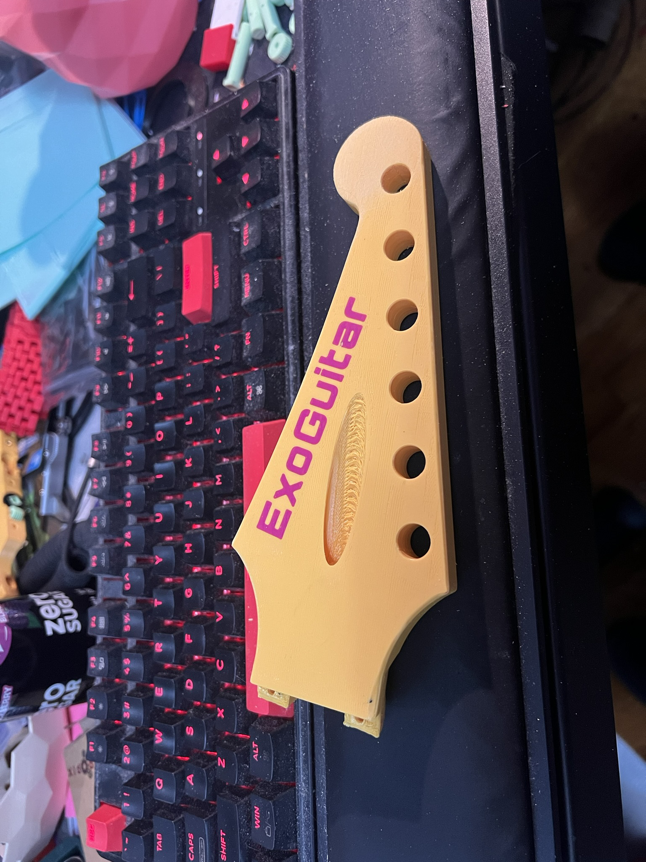
models/Head/Firebird/photos/IMG_4458.JPEG
