spikeon/exoguitar/models/Head/Firebird/photos/IMG_4459.JPEG

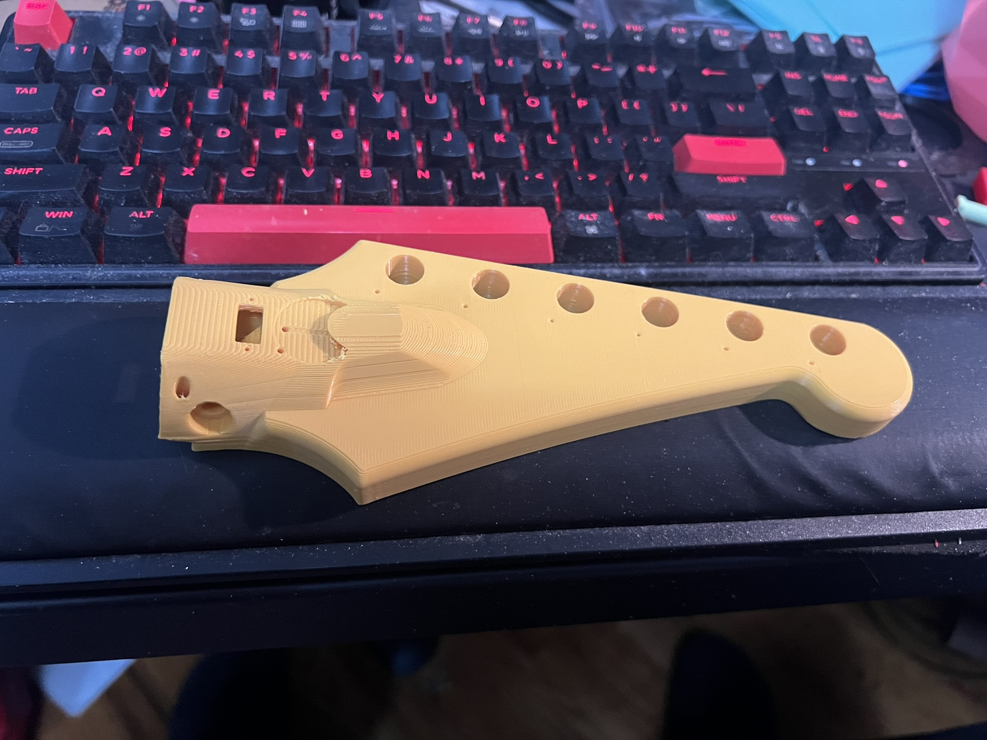
models/Head/Firebird/photos/IMG_4459.JPEG
