spikeon/exoguitar/models/Head/Headless - OVSAL String Lock/photos/IMG_4959.JPEG

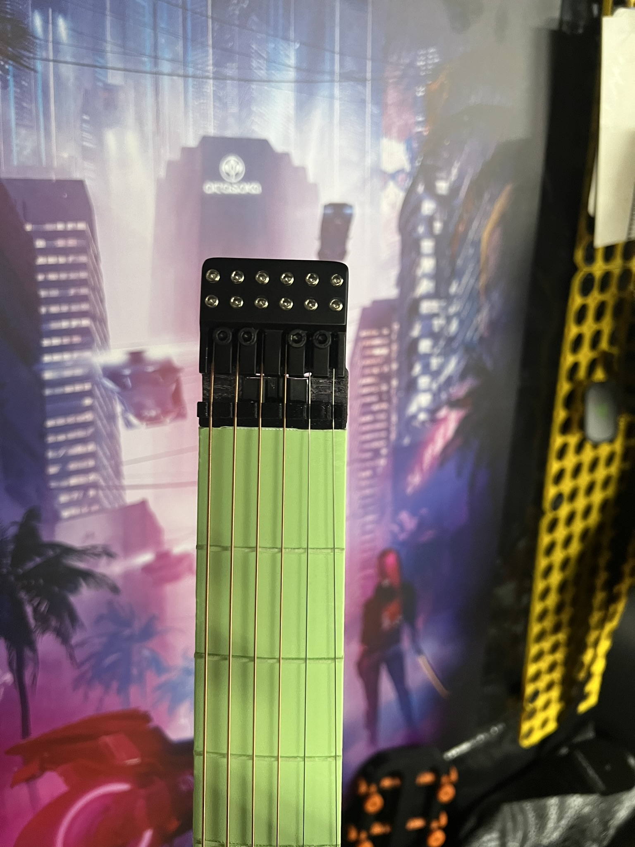
models/Head/Headless - OVSAL String Lock/photos/IMG_4959.JPEG
