spikeon/exoguitar/models/Head/Headless - OVSAL String Lock/photos/IMG_4960.JPEG

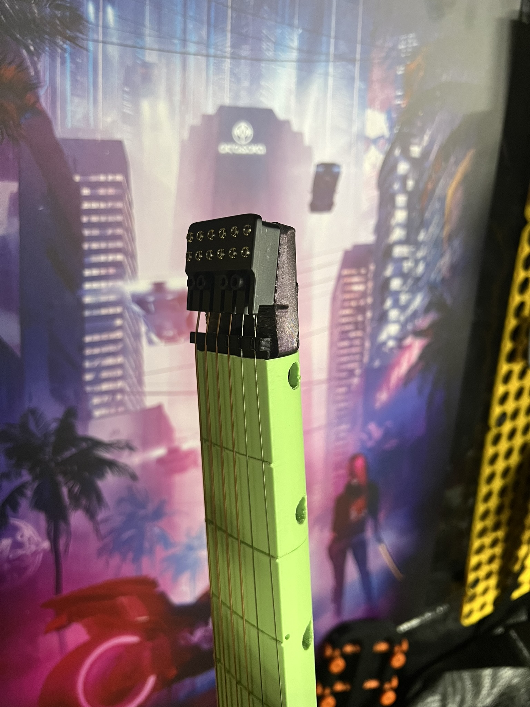
models/Head/Headless - OVSAL String Lock/photos/IMG_4960.JPEG
