spikeon/exoguitar/models/Head/Headless - OVSAL String Lock/photos/IMG_4961.JPEG

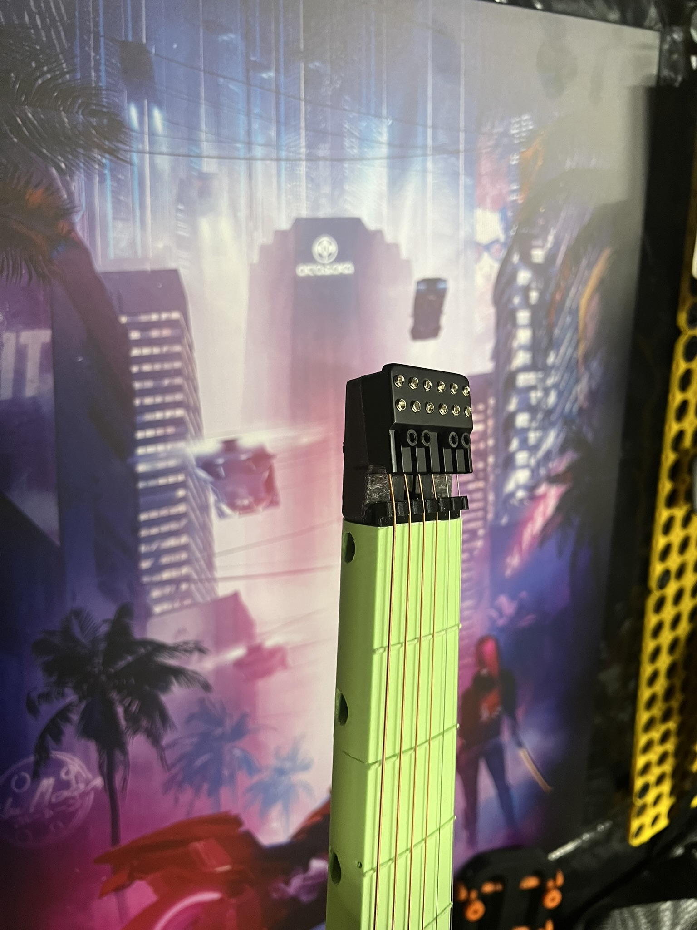
models/Head/Headless - OVSAL String Lock/photos/IMG_4961.JPEG
