spikeon/exoguitar/models/Head/Headless - String Lock/photos/IMG_4943.JPEG

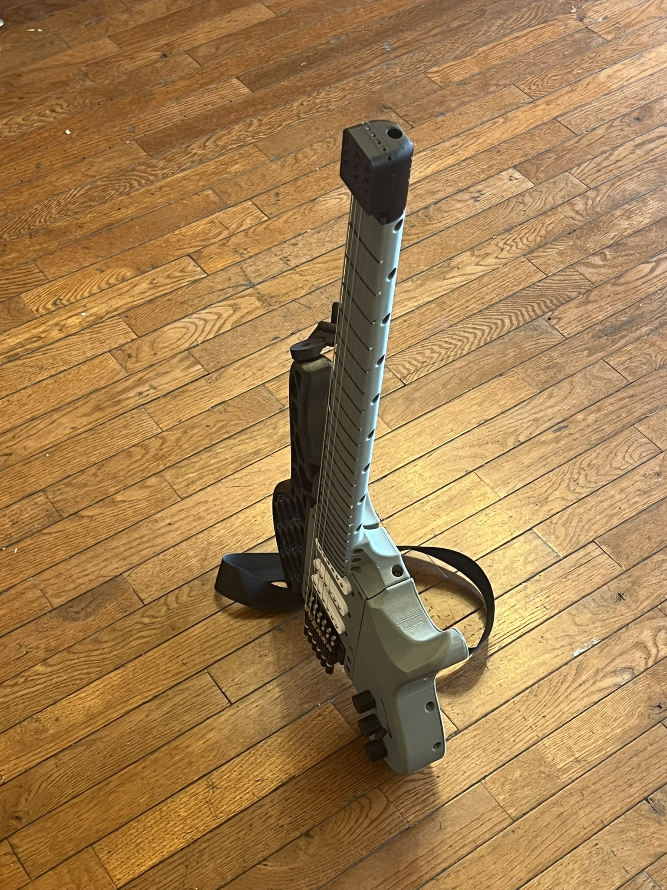
models/Head/Headless - String Lock/photos/IMG_4943.JPEG
