spikeon/exoguitar/models/Head/Headless - String Lock/photos/IMG_4944.JPEG

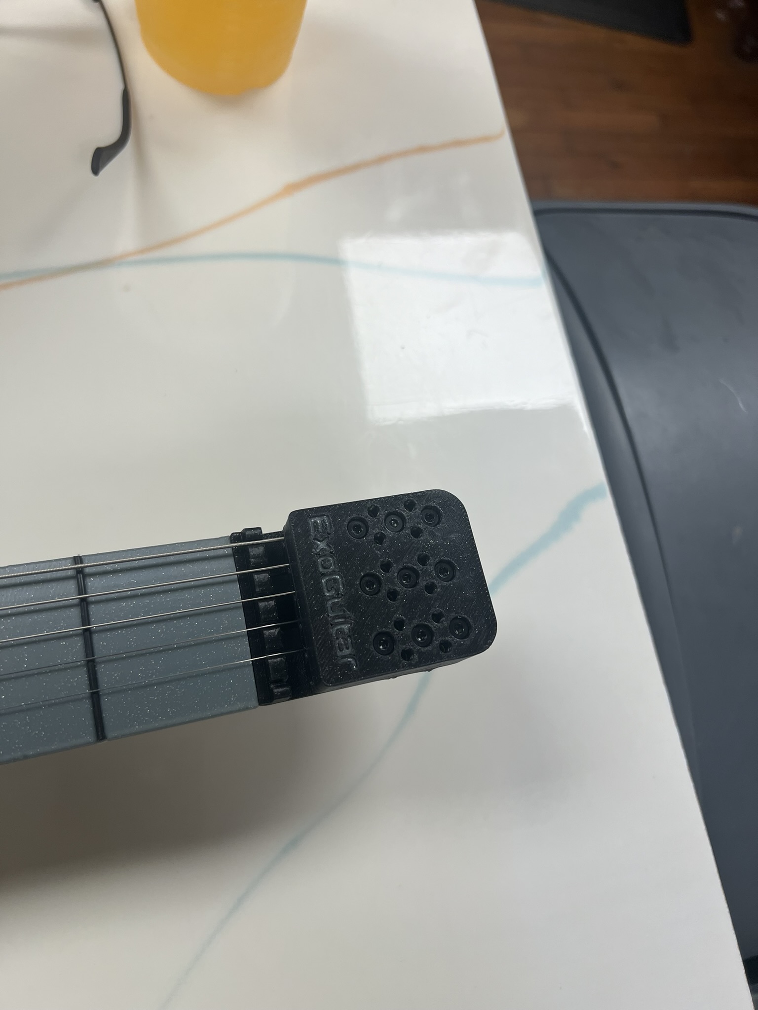
models/Head/Headless - String Lock/photos/IMG_4944.JPEG
