spikeon/exoguitar/models/Head/Headless - String Lock/photos/IMG_4952.JPEG

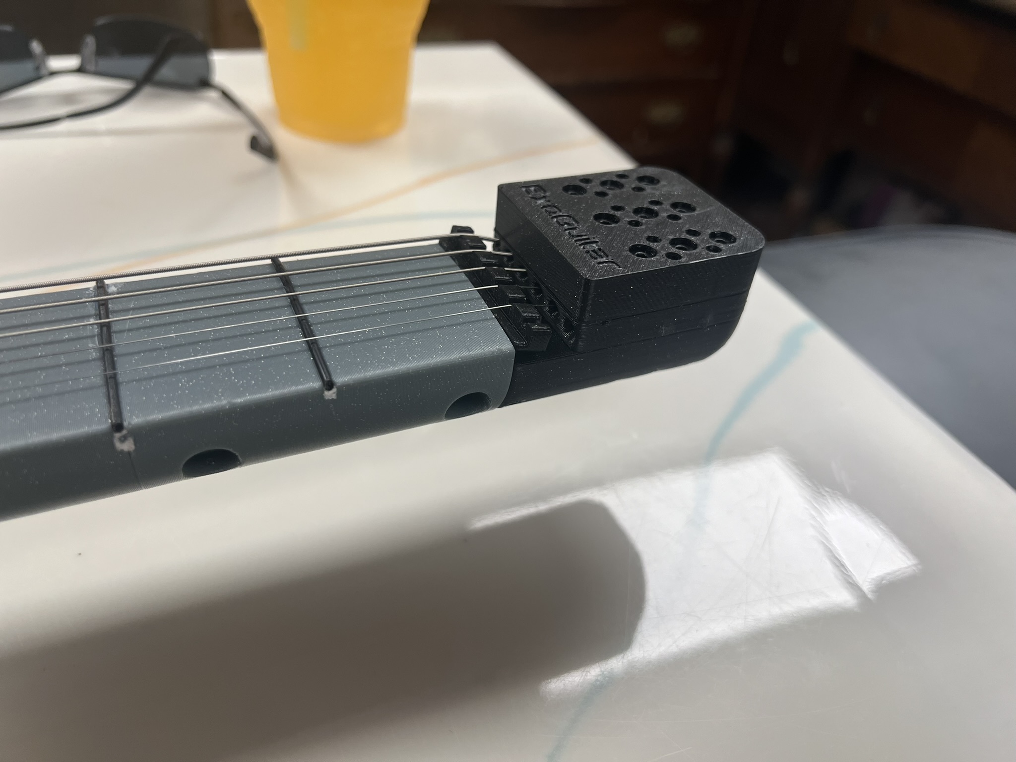
models/Head/Headless - String Lock/photos/IMG_4952.JPEG
