spikeon/exoguitar/models/Head/Headless v2/Face Plates/Plastic X/photos/IMG_5300.JPEG

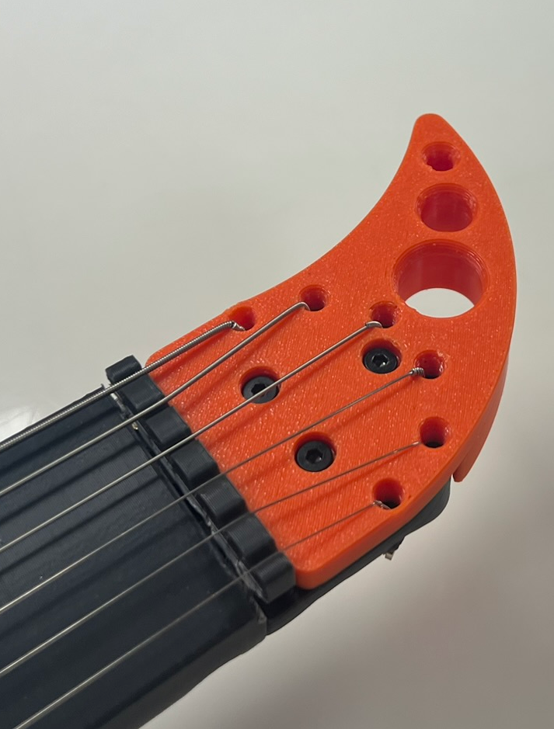
models/Head/Headless v2/Face Plates/Plastic X/photos/IMG_5300.JPEG
