spikeon/exoguitar/models/Head/Headless v2/Face Plates/Plastic X/photos/thumb.tall.png

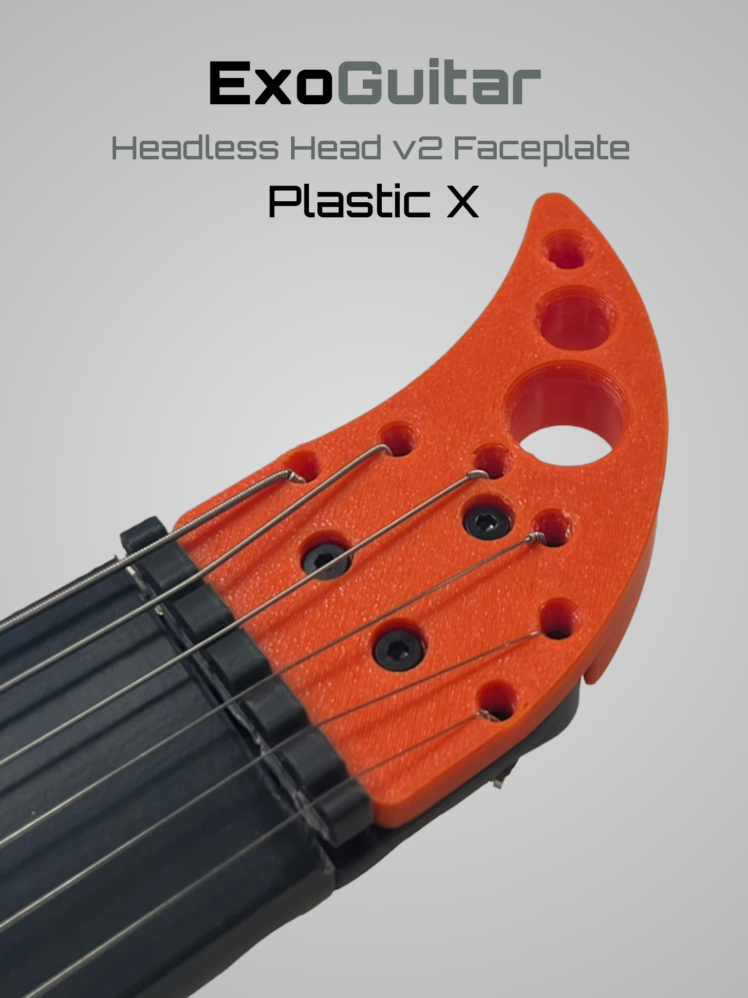
models/Head/Headless v2/Face Plates/Plastic X/photos/thumb.tall.png
