spikeon/exoguitar/models/Head/Headless v2/photos/IMG_5322.JPEG

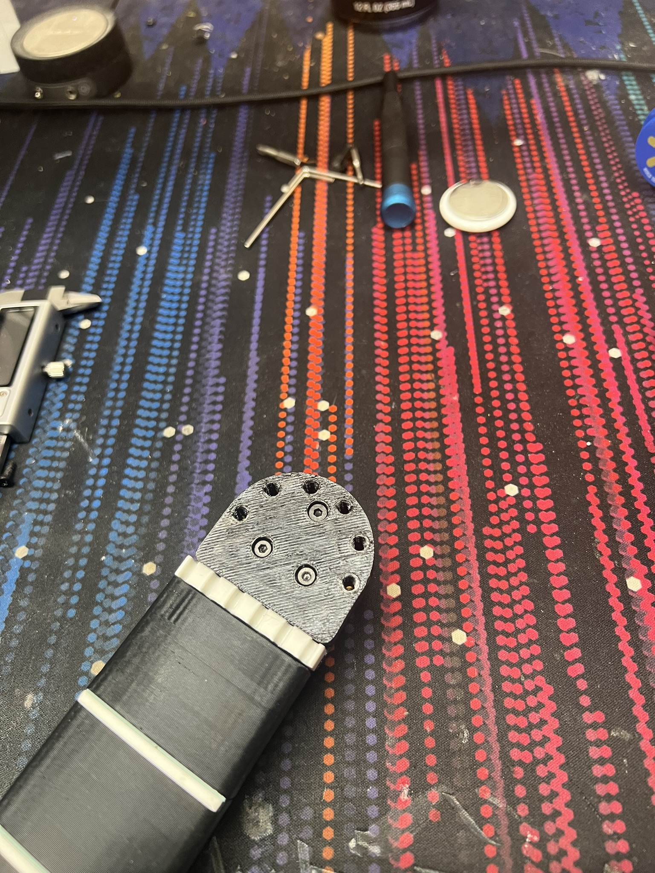
models/Head/Headless v2/photos/IMG_5322.JPEG
