spikeon/exoguitar/models/Head/Headless v2/photos/IMG_5323.JPEG

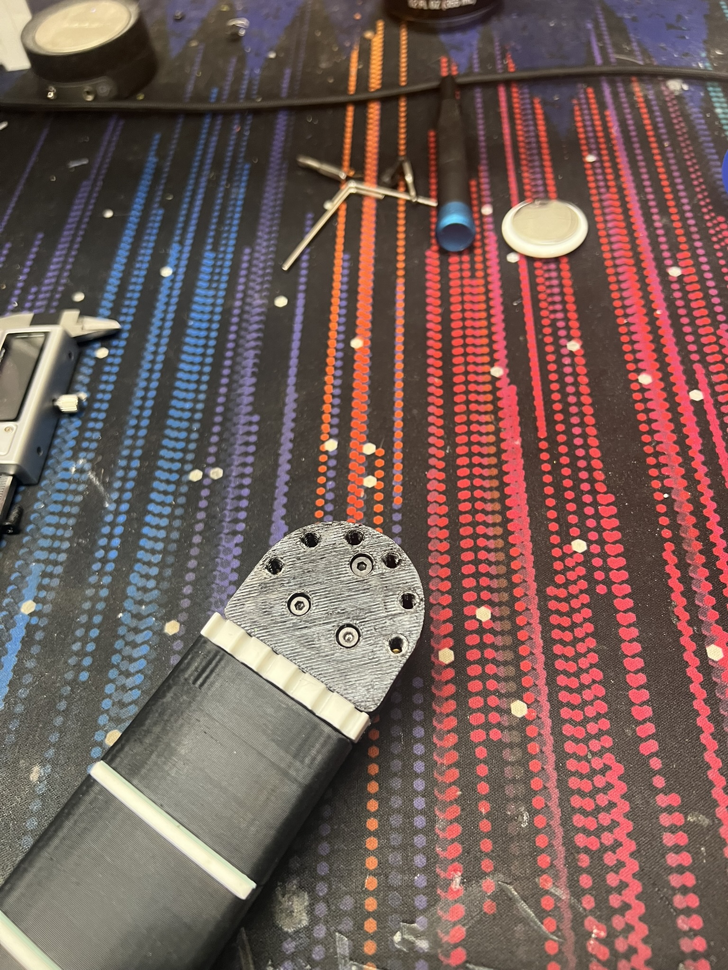
models/Head/Headless v2/photos/IMG_5323.JPEG
