spikeon/exoguitar/models/Head/Headless v2/photos/thumb.tall.png

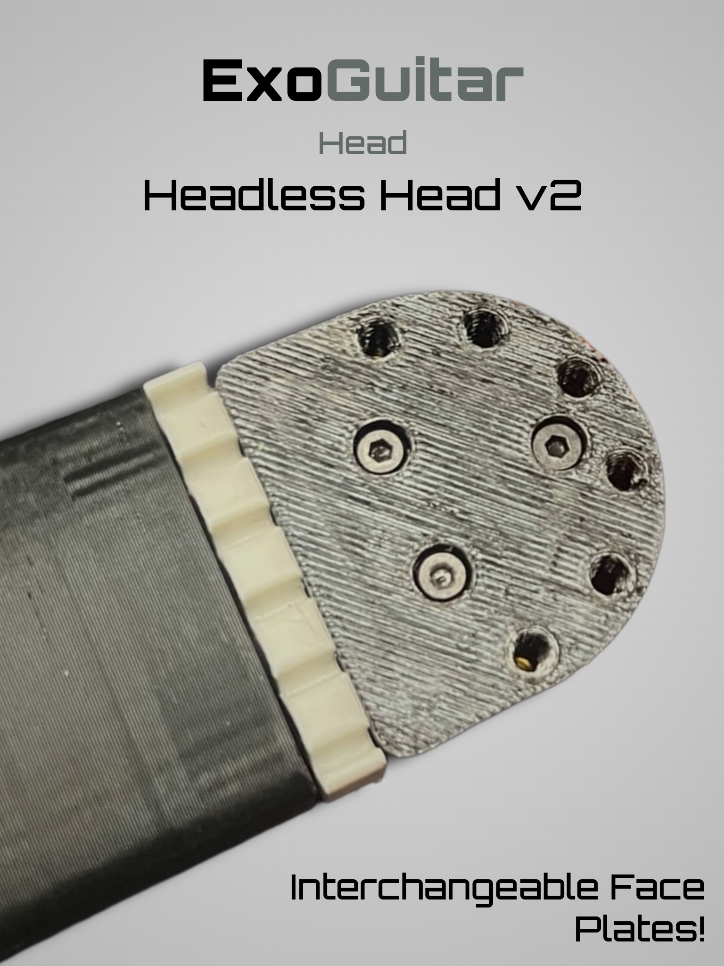
models/Head/Headless v2/photos/thumb.tall.png
