spikeon/exoguitar/models/Head/Headless v2/photos/thumb.wide.png

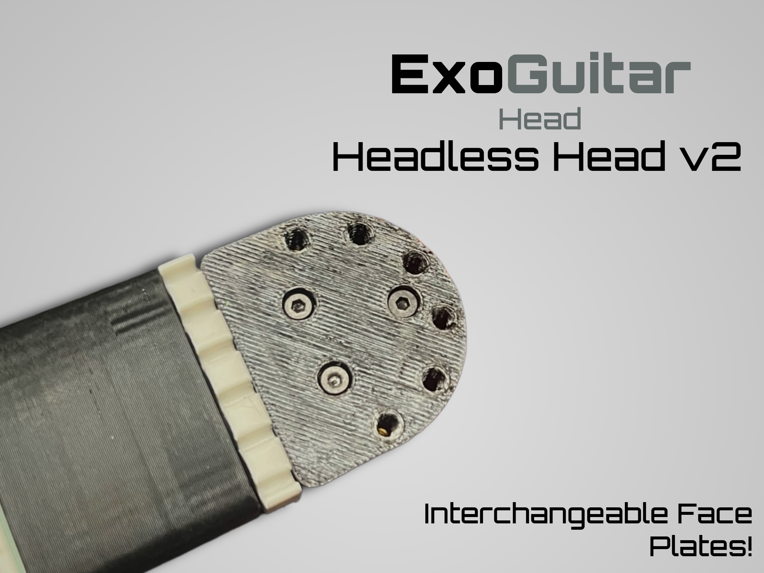
models/Head/Headless v2/photos/thumb.wide.png
