spikeon/exoguitar/models/Head/Headless/photos/IMG_3782.JPEG

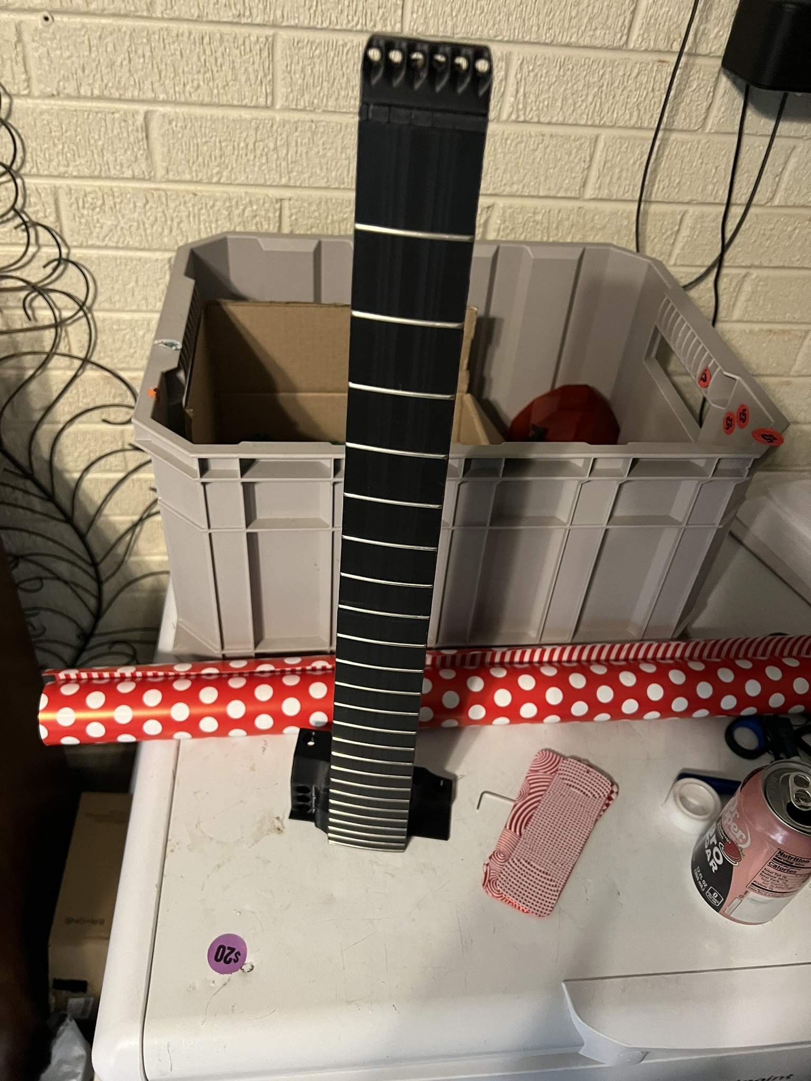
models/Head/Headless/photos/IMG_3782.JPEG
