spikeon/exoguitar/models/Head/Headless/photos/IMG_3788.JPEG

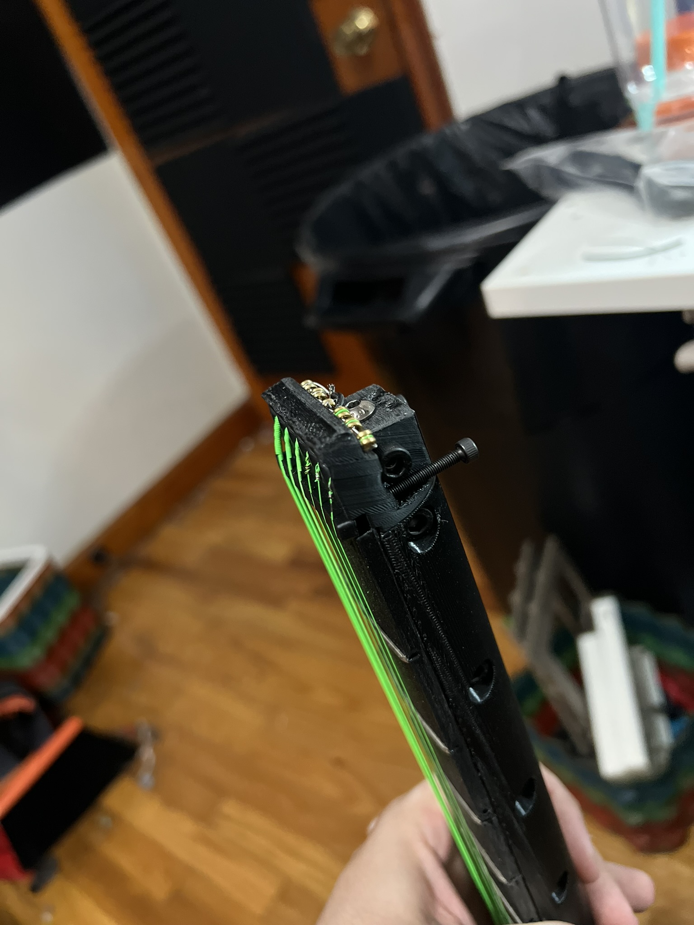
models/Head/Headless/photos/IMG_3788.JPEG
