spikeon/exoguitar/models/Head/Horny/photos/IMG_6310.JPEG

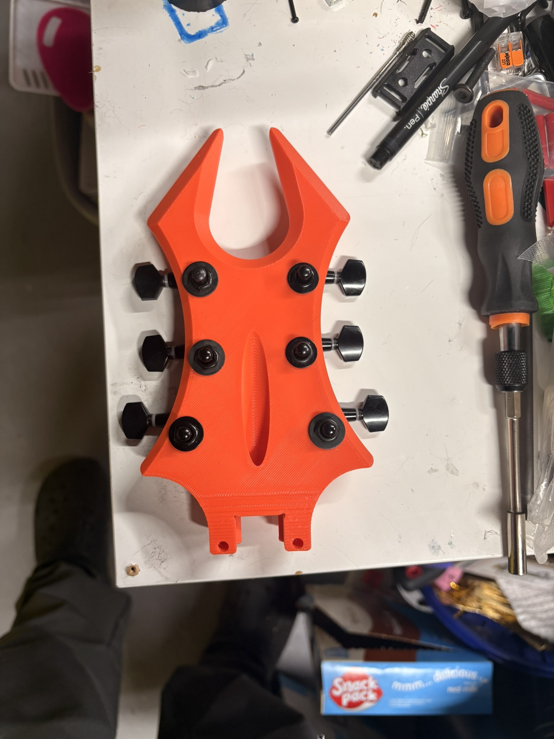
models/Head/Horny/photos/IMG_6310.JPEG
