spikeon/exoguitar/models/Head/Horny/photos/thumb.tall.png

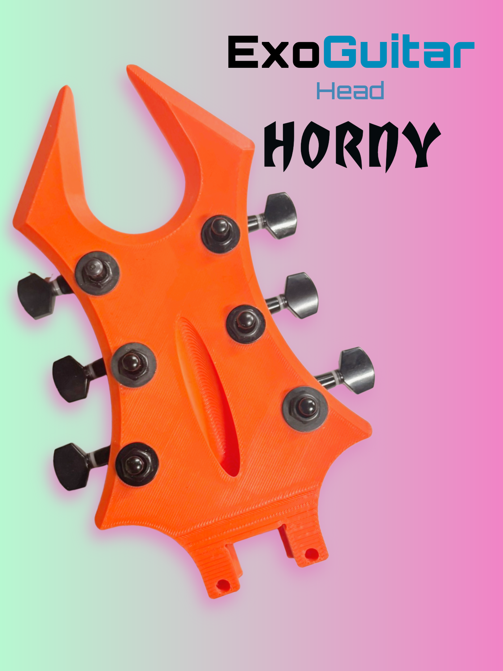
models/Head/Horny/photos/thumb.tall.png
