spikeon/exoguitar/models/Head/Horny/photos/thumb.wide.png

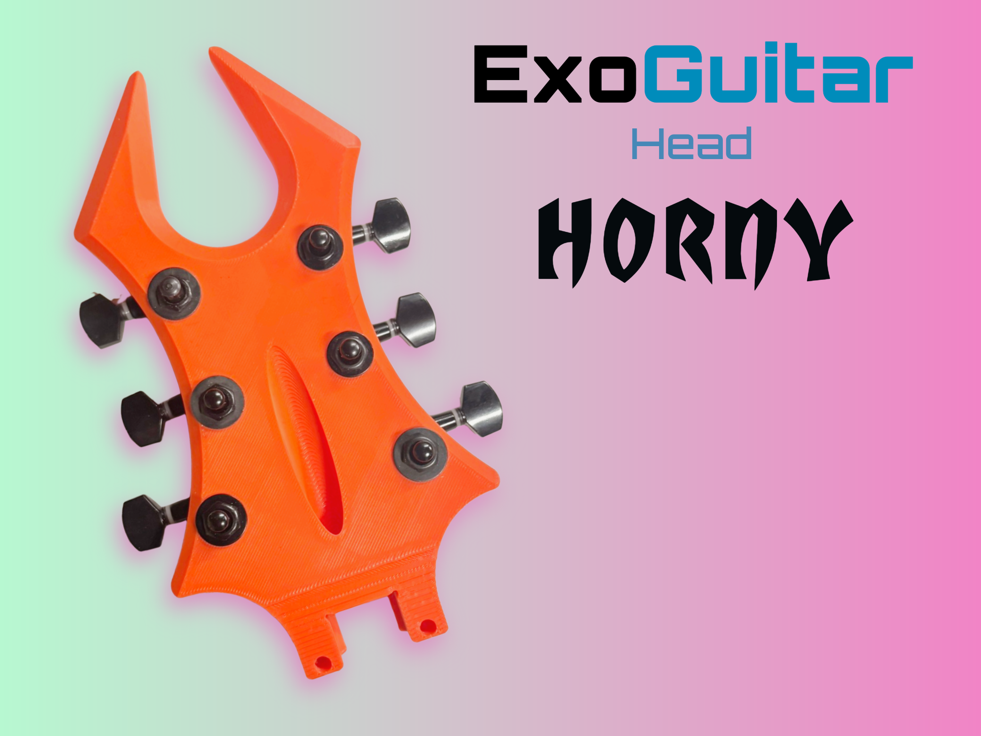
models/Head/Horny/photos/thumb.wide.png
