spikeon/exoguitar/models/Head/Jack's Son/photos/IMG_4430.JPEG

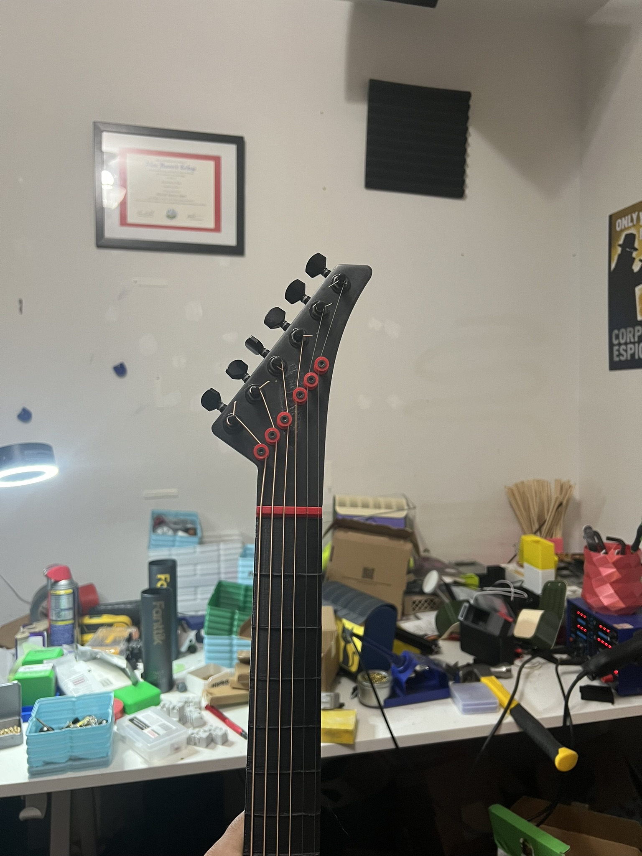
models/Head/Jack's Son/photos/IMG_4430.JPEG
