spikeon/exoguitar/models/Head/Jack's Son/photos/IMG_4431.JPEG

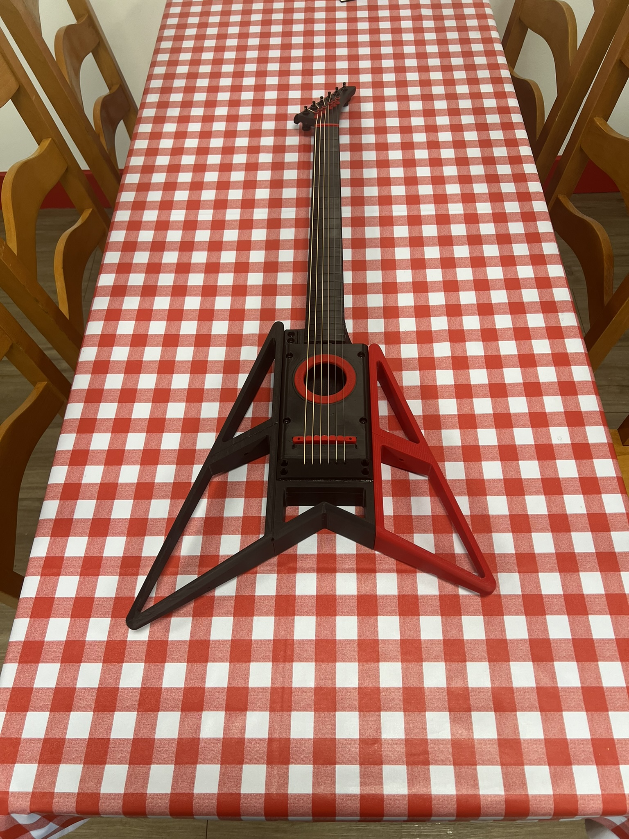
models/Head/Jack's Son/photos/IMG_4431.JPEG
