spikeon/exoguitar/models/Head/Jack's Son/photos/IMG_4436.JPEG

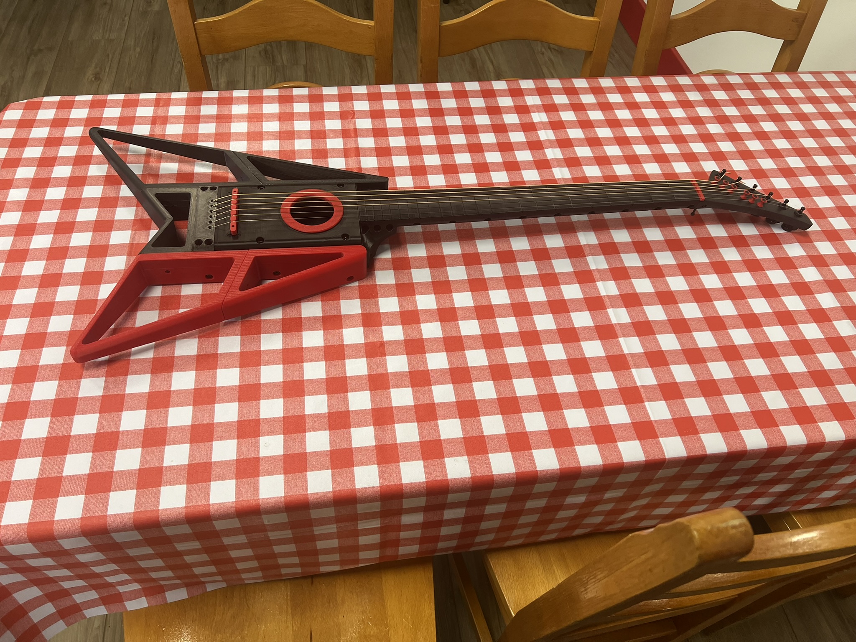
models/Head/Jack's Son/photos/IMG_4436.JPEG
