spikeon/exoguitar/models/Head/Jack's Son/photos/IMG_4437.JPEG

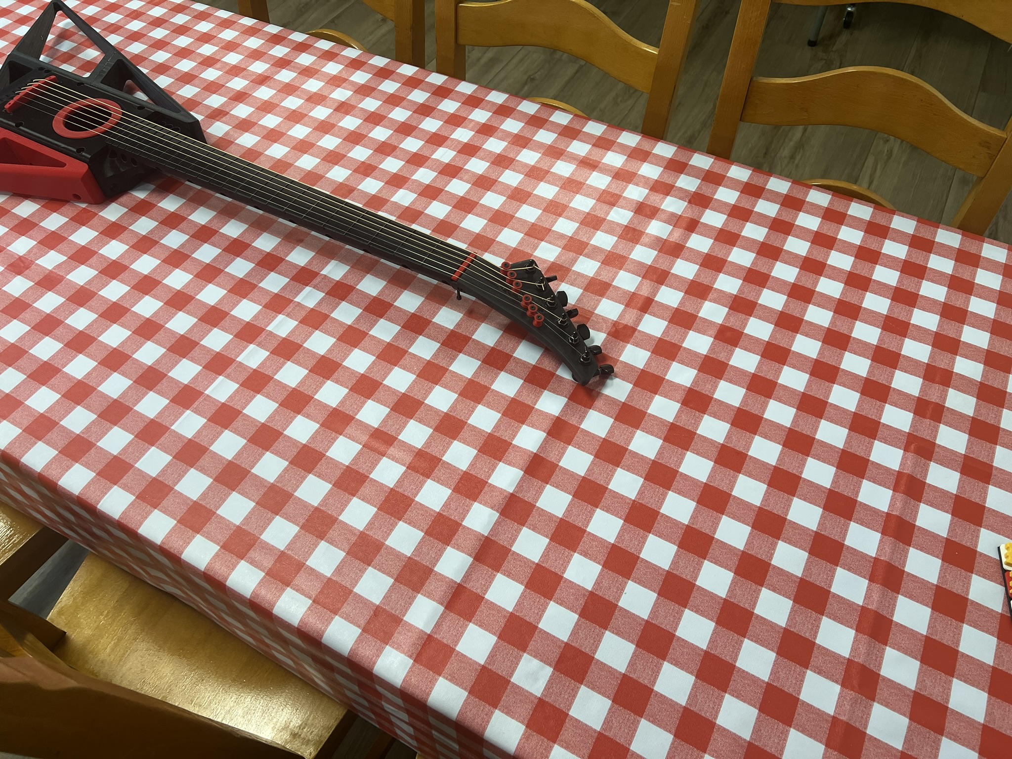
models/Head/Jack's Son/photos/IMG_4437.JPEG
