spikeon/exoguitar/models/Head/Jack's Son/photos/IMG_4438.JPEG

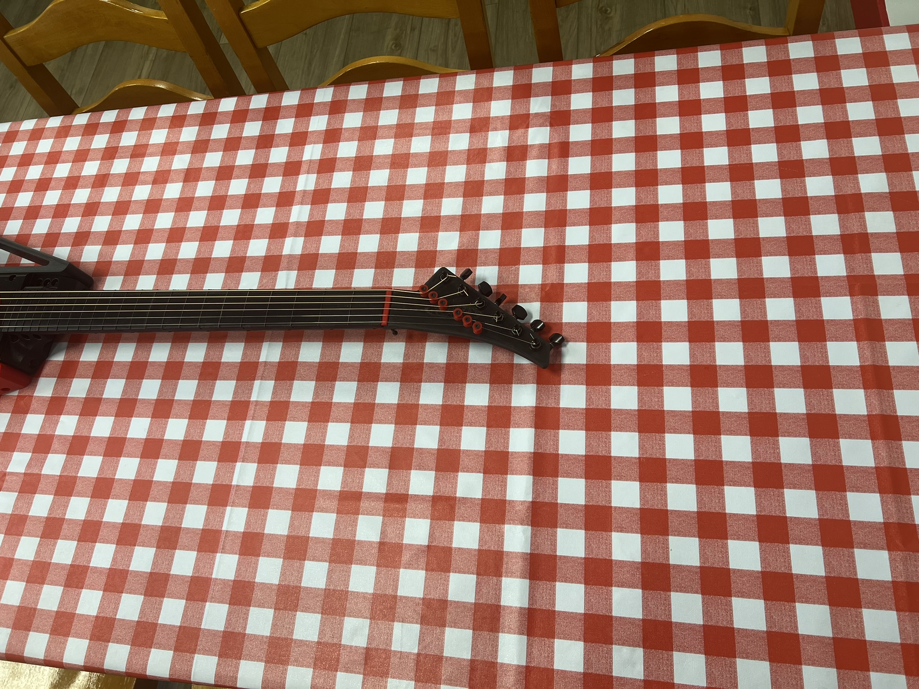
models/Head/Jack's Son/photos/IMG_4438.JPEG
