spikeon/exoguitar/models/Head/Jack's Son/photos/IMG_4439.JPEG

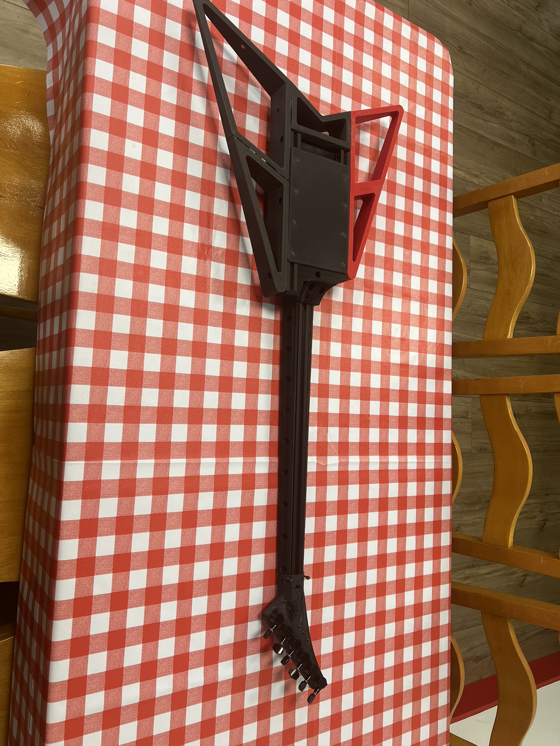
models/Head/Jack's Son/photos/IMG_4439.JPEG
