spikeon/exoguitar/models/Head/King Paul/photos/2025-05-11_6acdf5ecc2dd4.webp

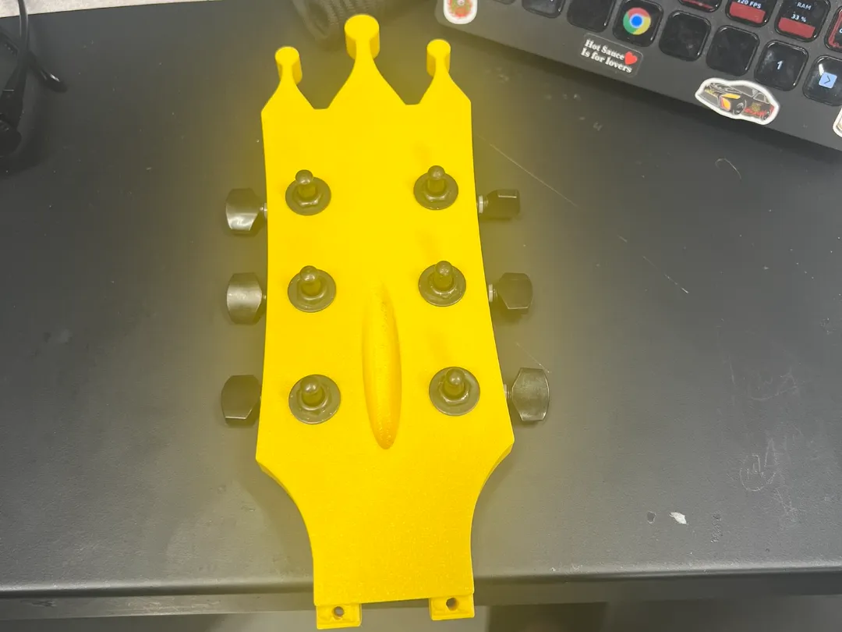
models/Head/King Paul/photos/2025-05-11_6acdf5ecc2dd4.webp
