spikeon/exoguitar/models/Head/Loop/Photos/IMG_4972.JPEG

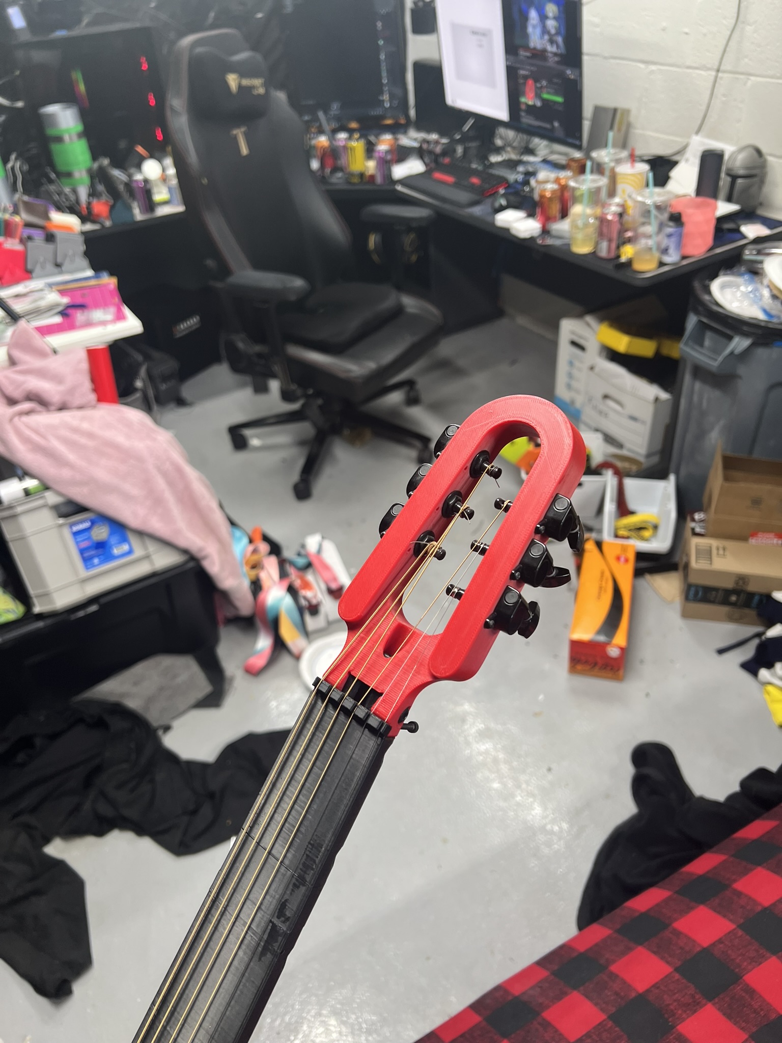
models/Head/Loop/Photos/IMG_4972.JPEG
