spikeon/exoguitar/models/Head/Loop/Photos/IMG_4973.JPEG

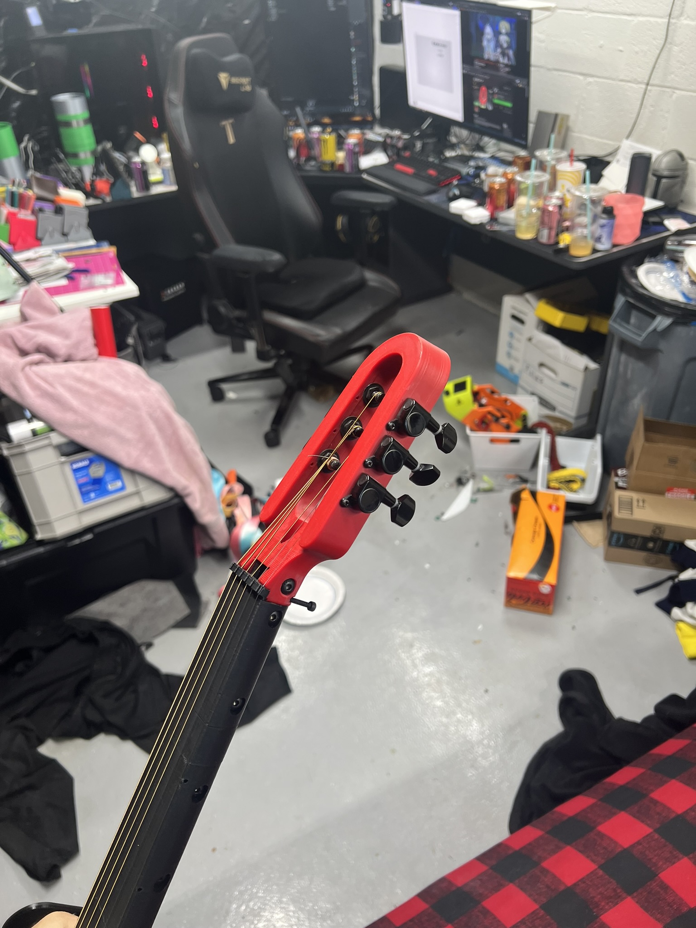
models/Head/Loop/Photos/IMG_4973.JPEG
