spikeon/exoguitar/models/Head/Loop/Photos/IMG_4974.JPEG

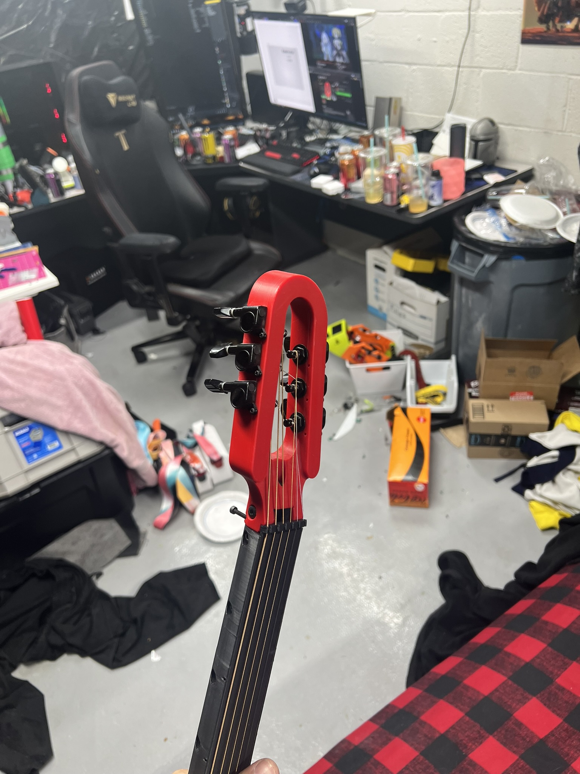
models/Head/Loop/Photos/IMG_4974.JPEG
