spikeon/exoguitar/models/Head/Loop/Photos/IMG_4975.JPEG

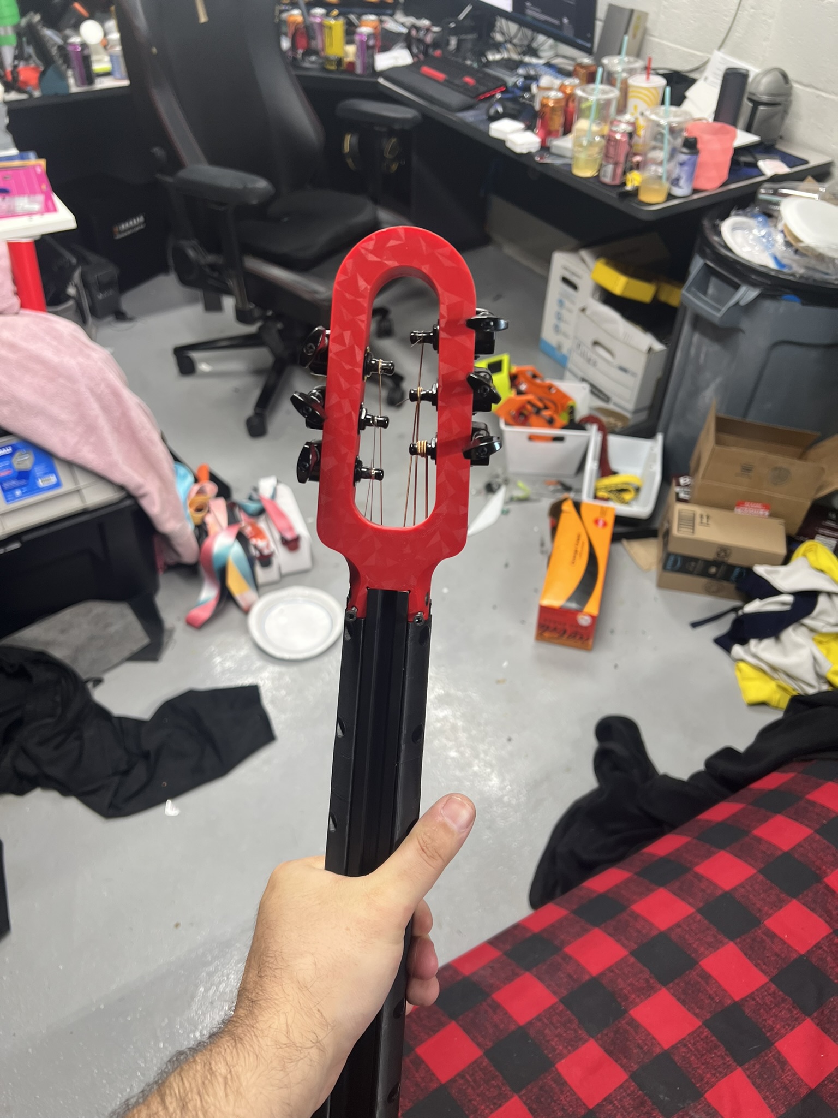
models/Head/Loop/Photos/IMG_4975.JPEG
