spikeon/exoguitar/models/Head/Lowes Paul/photos/IMG_5283.JPEG

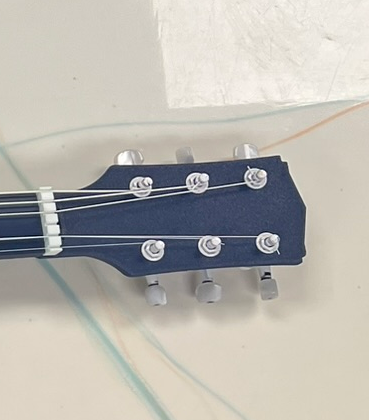
models/Head/Lowes Paul/photos/IMG_5283.JPEG
