spikeon/exoguitar/models/Head/Lowes Paul/photos/thumb.tall.png

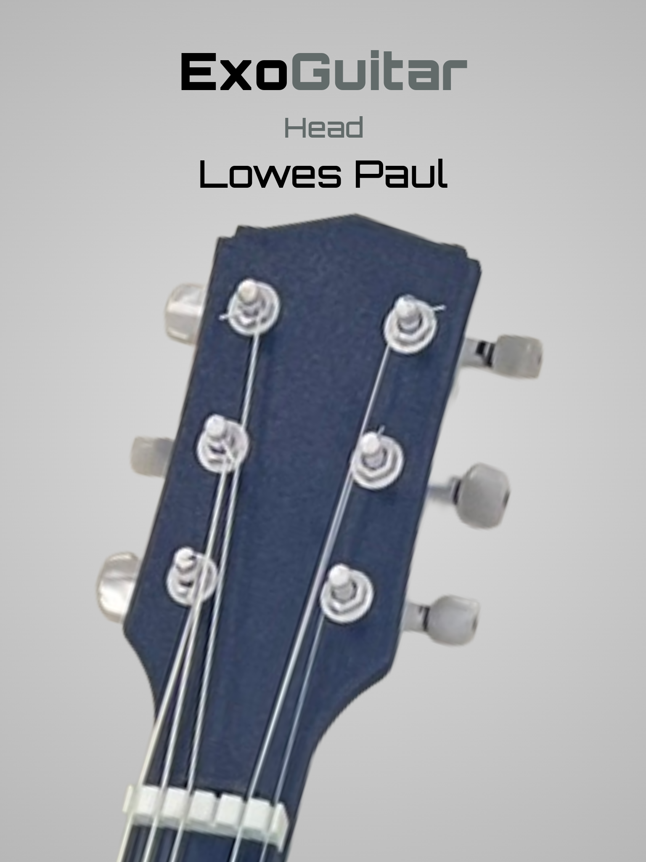
models/Head/Lowes Paul/photos/thumb.tall.png
