spikeon/exoguitar/models/Head/Lowes Paul/photos/thumb.wide.png

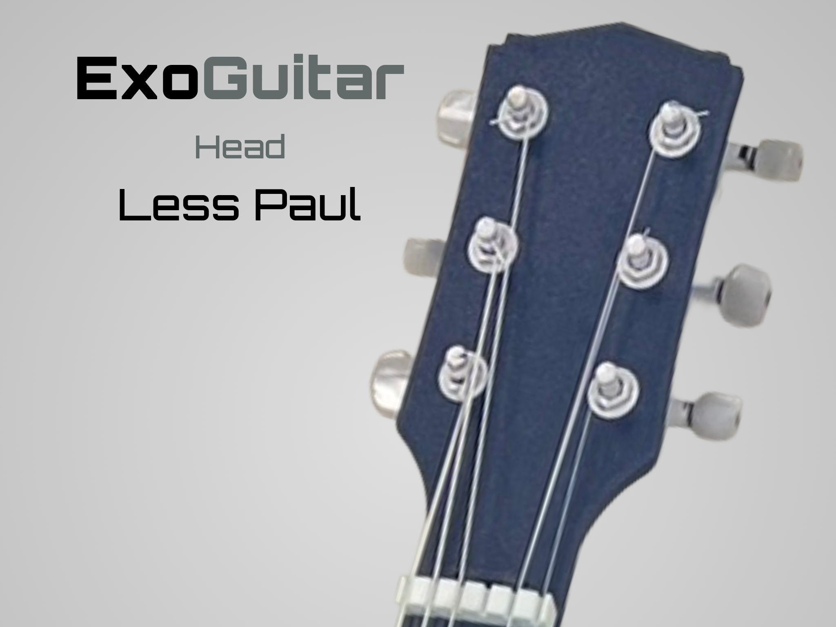
models/Head/Lowes Paul/photos/thumb.wide.png
