spikeon/exoguitar/models/Head/Sharky/photos/IMG_6103.JPEG

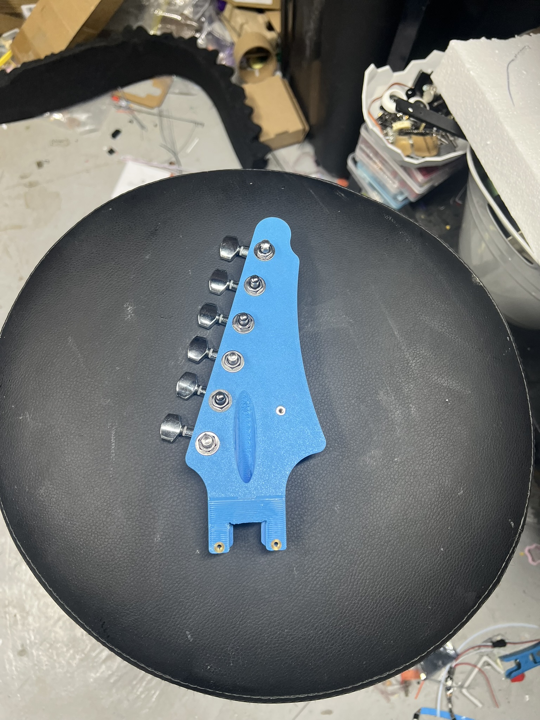
models/Head/Sharky/photos/IMG_6103.JPEG
