spikeon/exoguitar/models/Neck/Neck v3/photos/IMG_8149.jpg

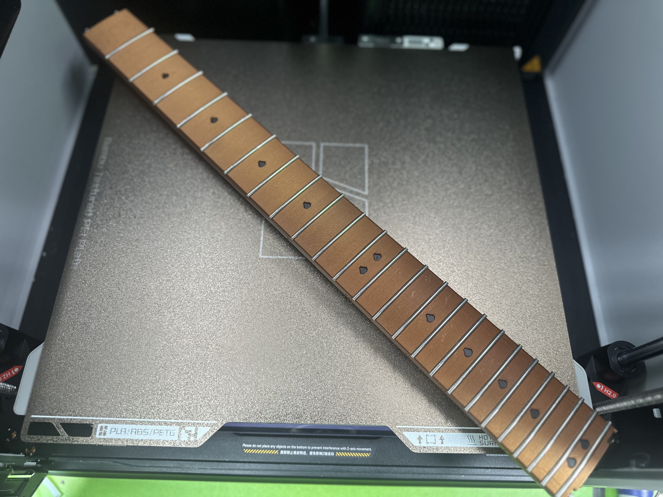
models/Neck/Neck v3/photos/IMG_8149.jpg
