spikeon/exoguitar/models/Neck/Neck v3/photos/thumb.tall.png

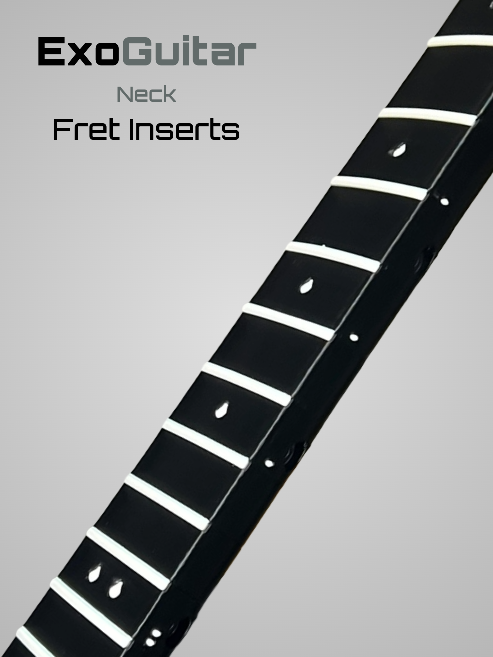
models/Neck/Neck v3/photos/thumb.tall.png
