spikeon/exoguitar/models/Neck/Neck v3/photos/thumb.wide.png

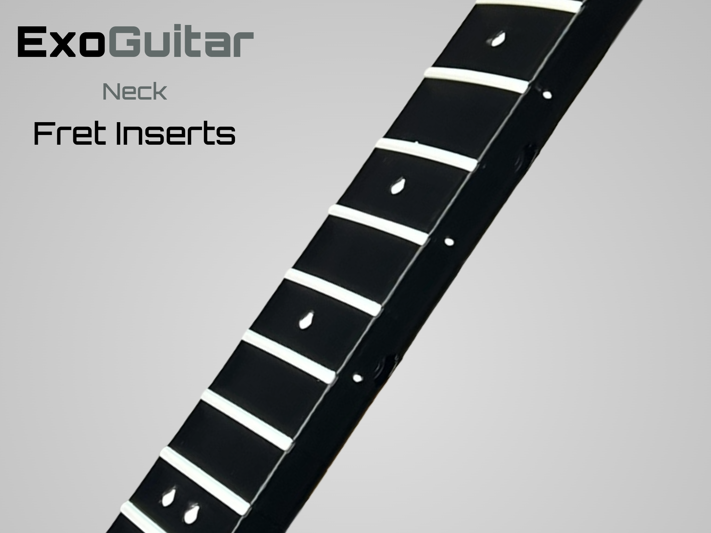
models/Neck/Neck v3/photos/thumb.wide.png
