spikeon/exoguitar/models/Nut/photos/thumb.tall.png

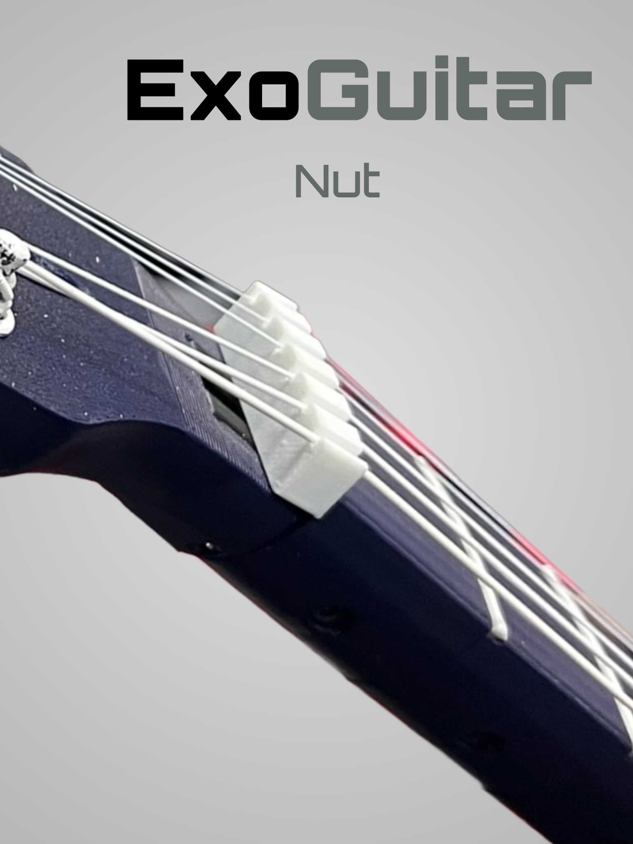
models/Nut/photos/thumb.tall.png
