spikeon/exoguitar/models/Nut/photos/thumb.wide.png

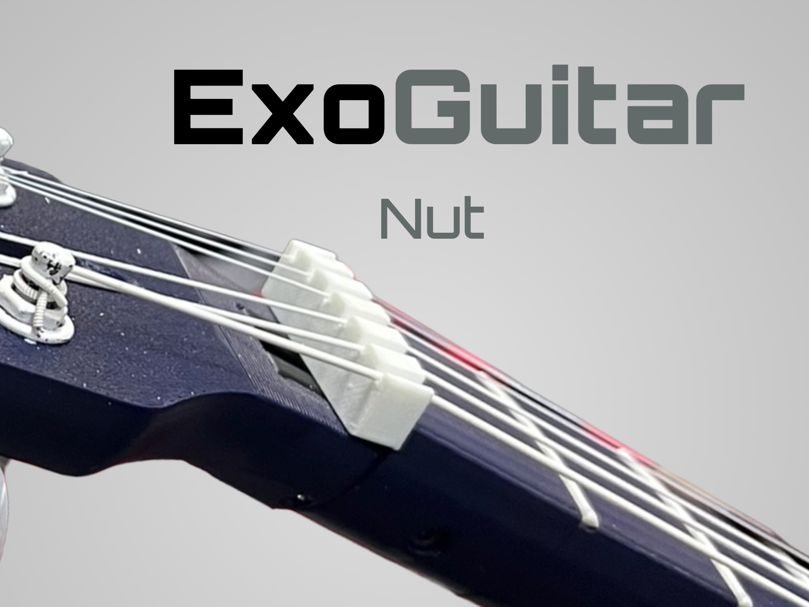
models/Nut/photos/thumb.wide.png
