spikeon/exoguitar/models/Shoulders/Double Cut/photos/thumb.tall.png

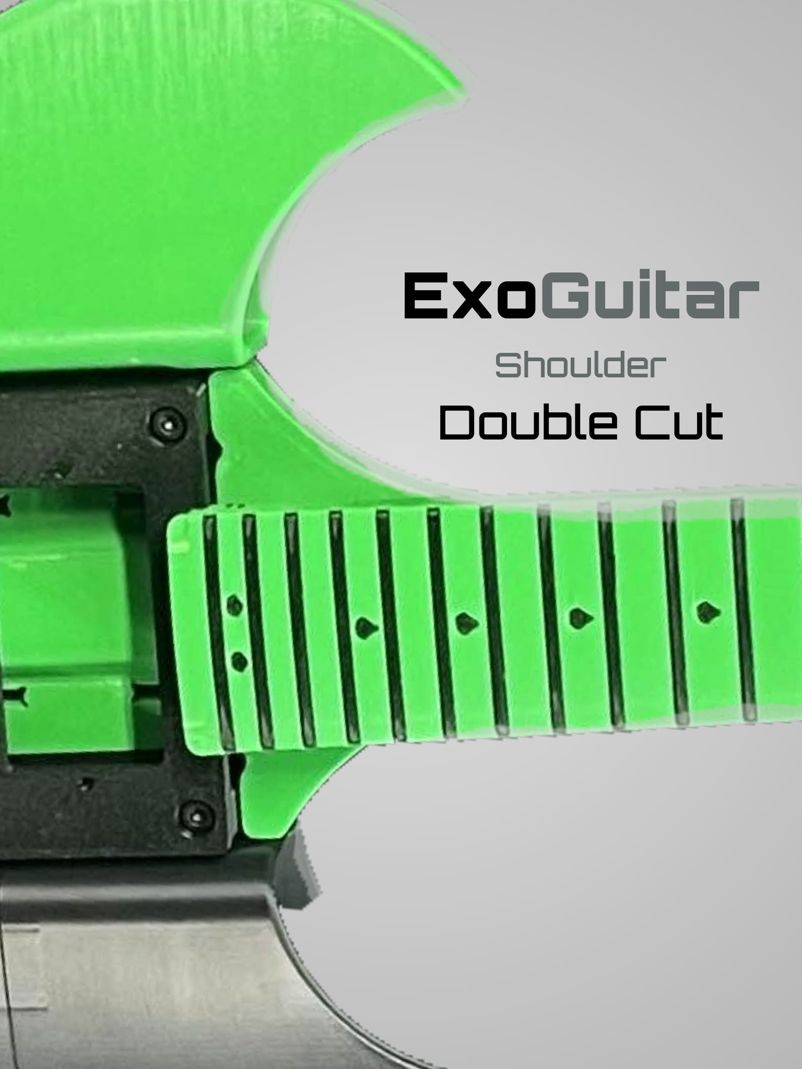
models/Shoulders/Double Cut/photos/thumb.tall.png
