spikeon/exoguitar/models/Shoulders/Double Cut/photos/thumb.wide.png

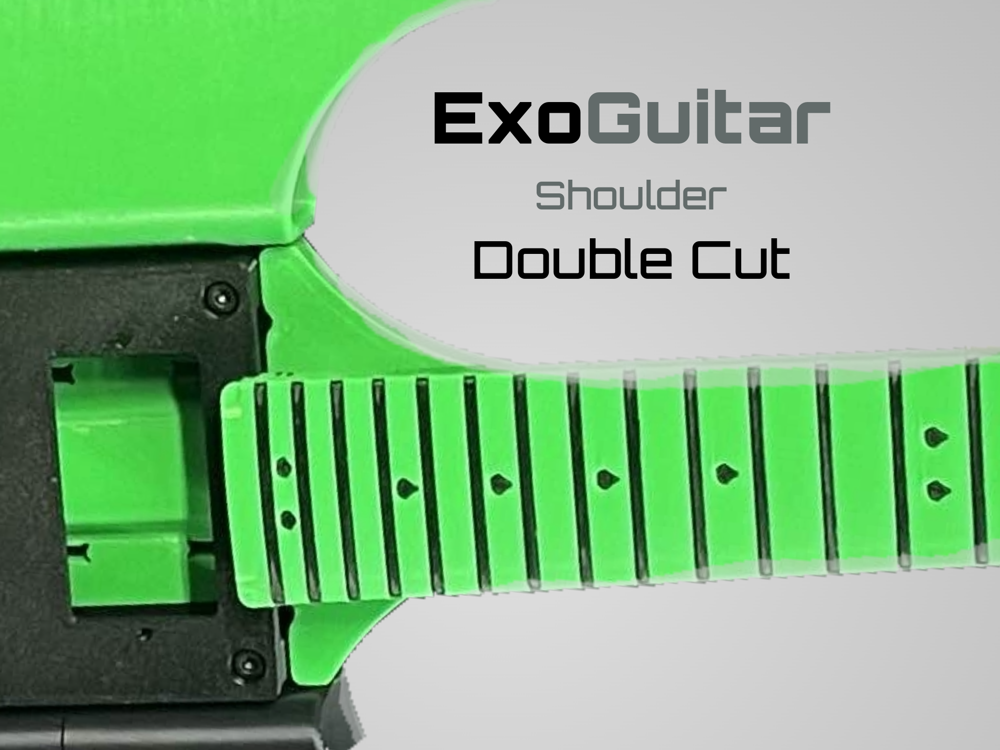
models/Shoulders/Double Cut/photos/thumb.wide.png
