spikeon/exoguitar/models/Shoulders/Single Cut/photos/Shoulder-1-Tall.png

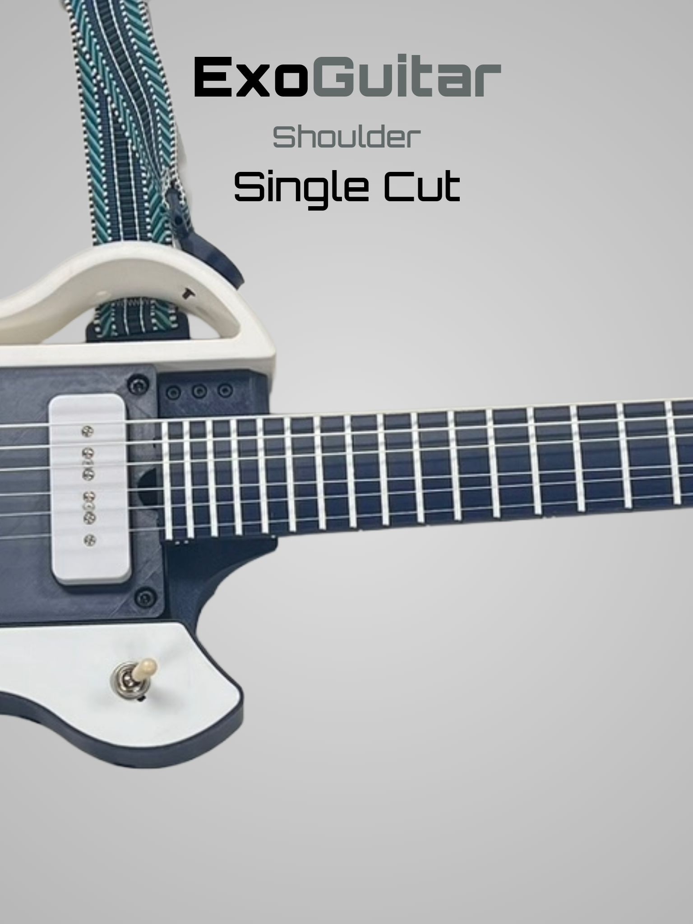
models/Shoulders/Single Cut/photos/Shoulder-1-Tall.png
