spikeon/exoguitar/models/Shoulders/Single Cut/photos/Shoulder-2-Wide.png

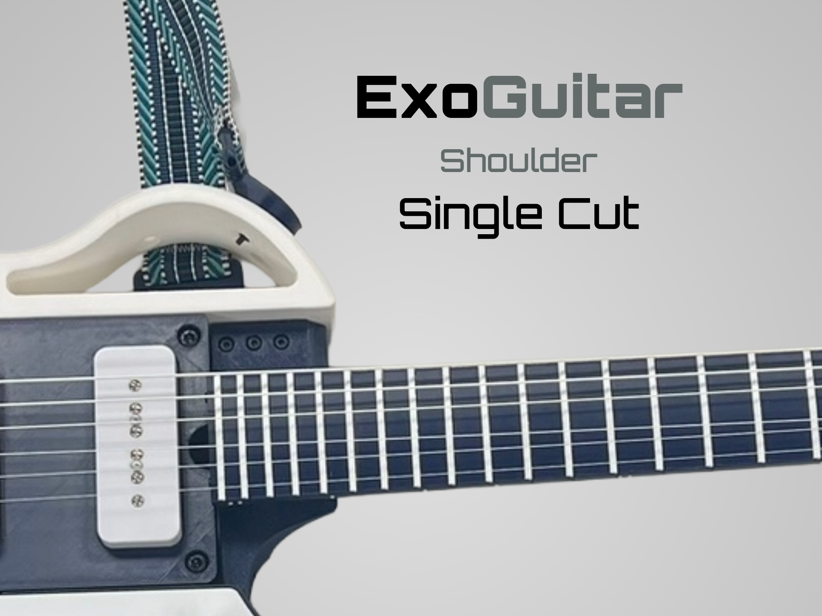
models/Shoulders/Single Cut/photos/Shoulder-2-Wide.png
