spikeon/exoguitar/models/Strap/Clip Strap/photos/IMG_5751 (1).JPEG

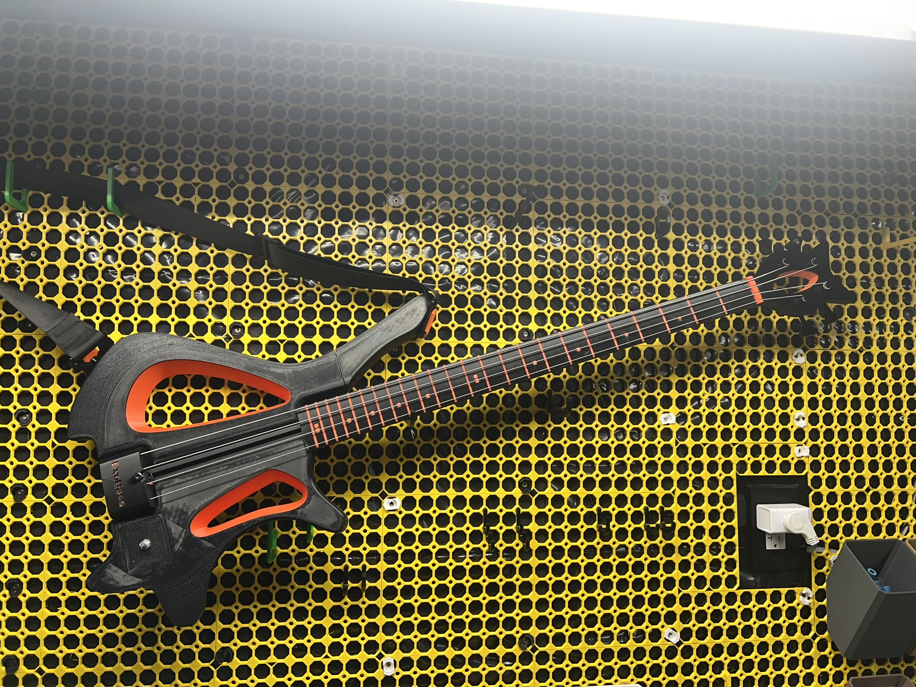
models/Strap/Clip Strap/photos/IMG_5751 (1).JPEG
