spikeon/exoguitar/models/Strap/Clip Strap/photos/IMG_5753.JPEG

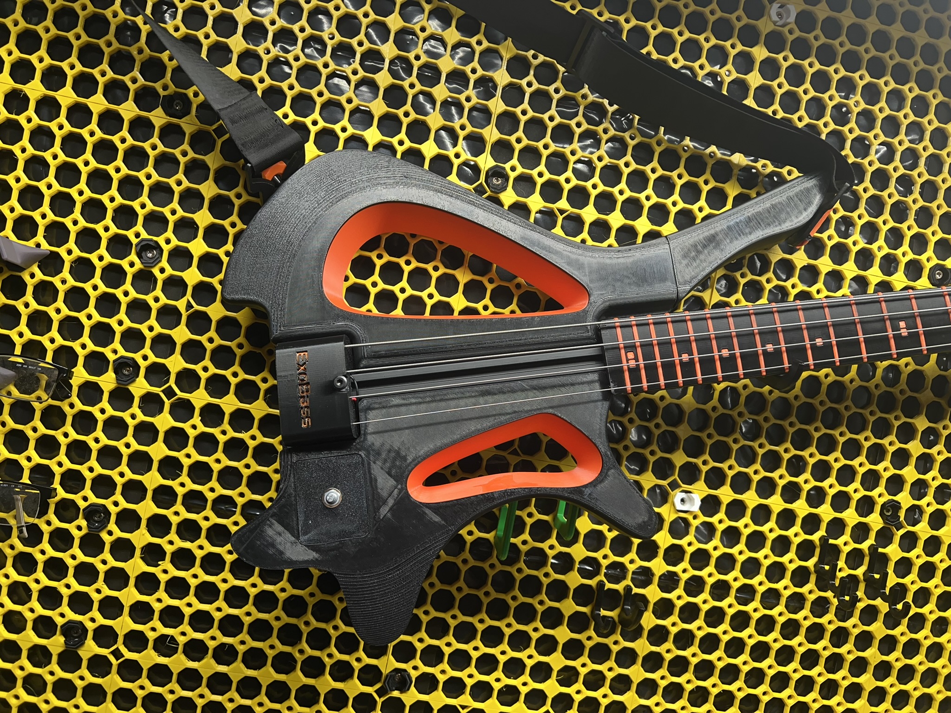
models/Strap/Clip Strap/photos/IMG_5753.JPEG
