spikeon/exoguitar/models/Wing Sets/Arasaka/photos/IMG_4993.JPEG

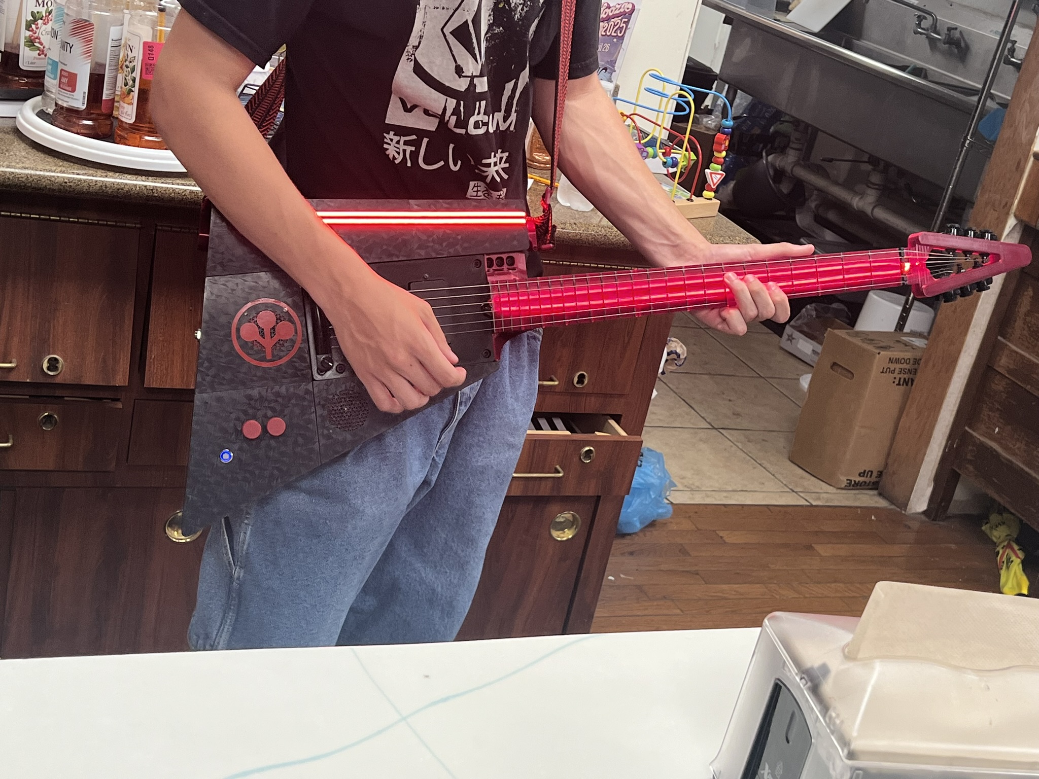
models/Wing Sets/Arasaka/photos/IMG_4993.JPEG
