spikeon/exoguitar/models/Wing Sets/Arasaka/photos/IMG_4995.JPEG

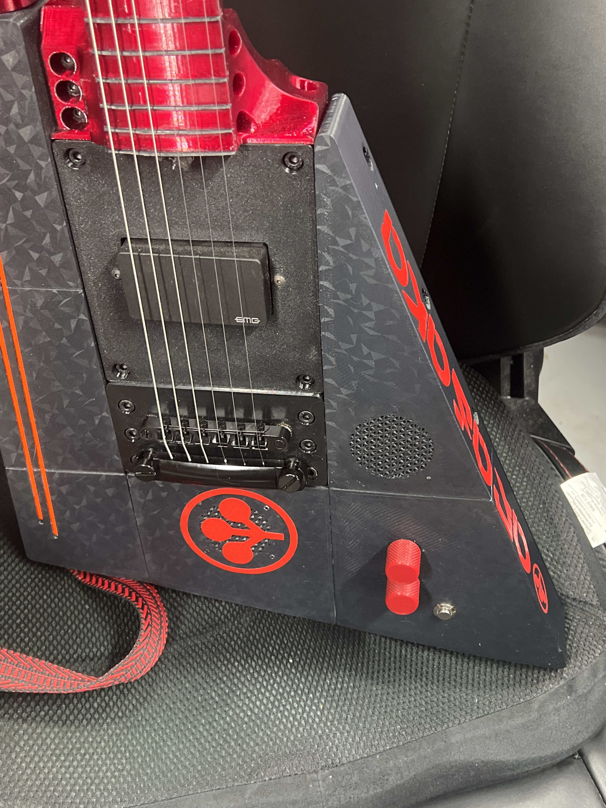
models/Wing Sets/Arasaka/photos/IMG_4995.JPEG
