spikeon/exoguitar/models/Wing Sets/Arasaka/photos/IMG_5017.JPEG

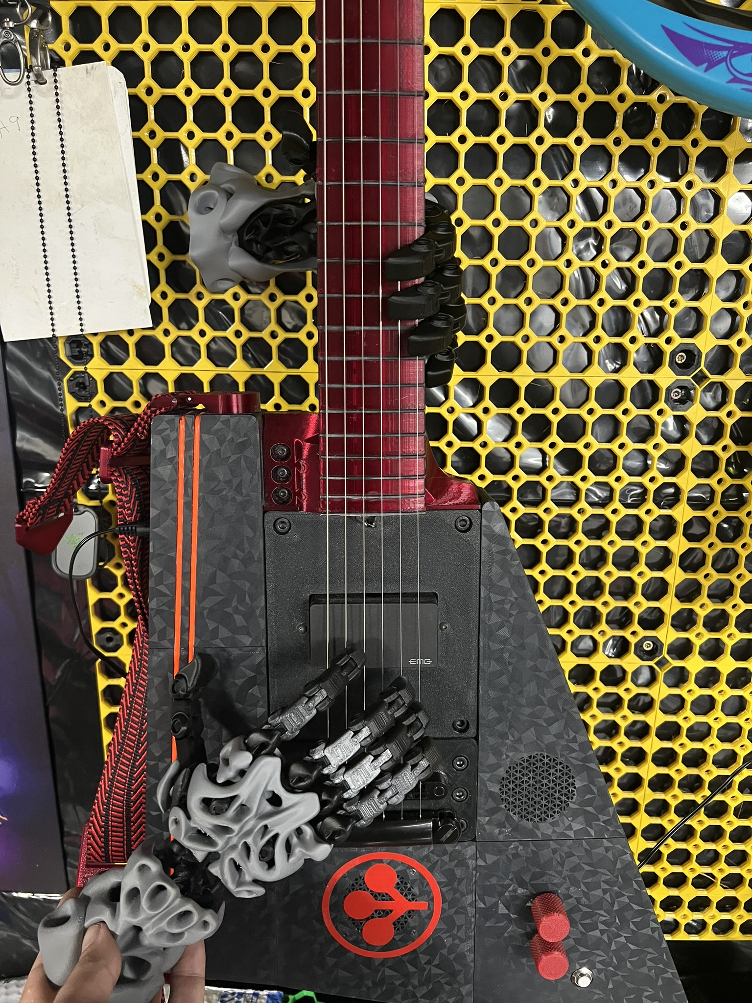
models/Wing Sets/Arasaka/photos/IMG_5017.JPEG
