spikeon/exoguitar/models/Wing Sets/BanjNo/exploded views/Screenshot 2025-02-27 225633.png

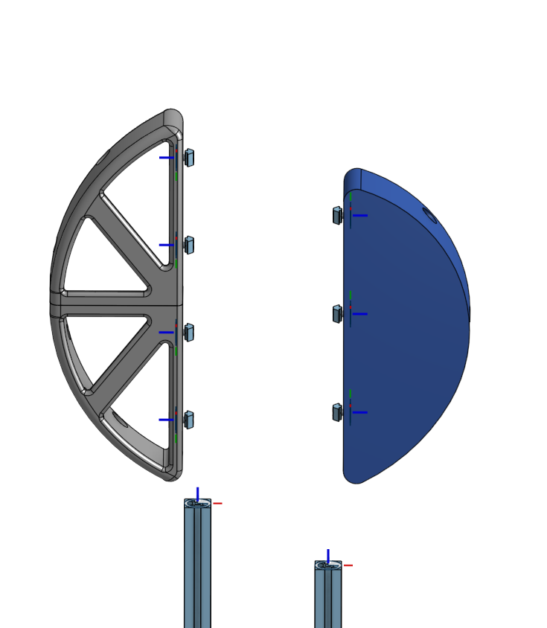
models/Wing Sets/BanjNo/exploded views/Screenshot 2025-02-27 225633.png
