spikeon/exoguitar/models/Wing Sets/BanjNo/pictures/IMG_4247.jpg

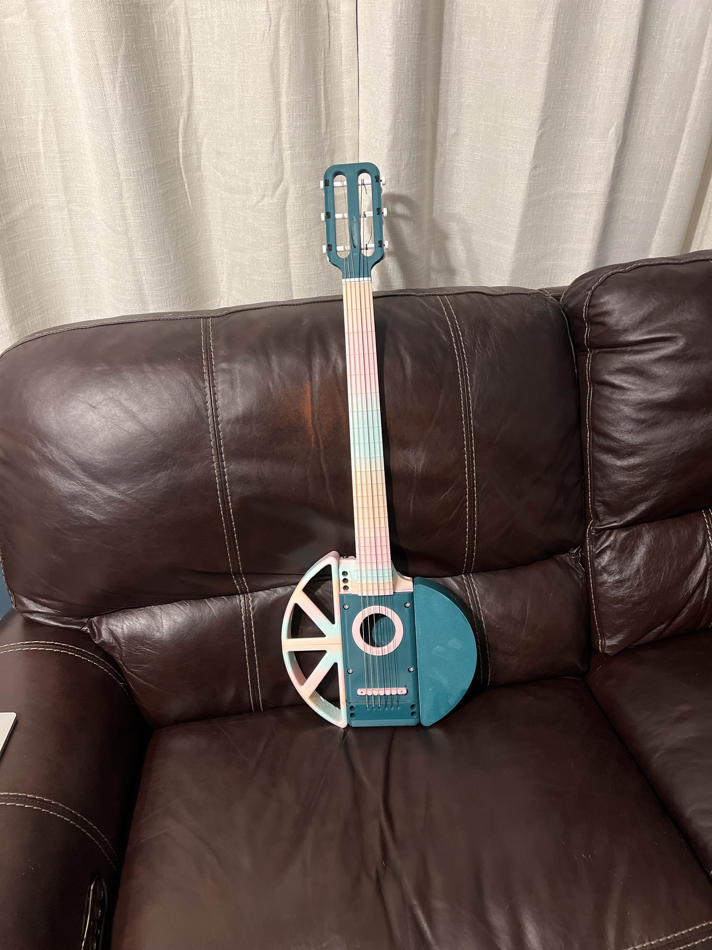
models/Wing Sets/BanjNo/pictures/IMG_4247.jpg
