spikeon/exoguitar/models/Wing Sets/BanjNo/pictures/IMG_4302.JPEG

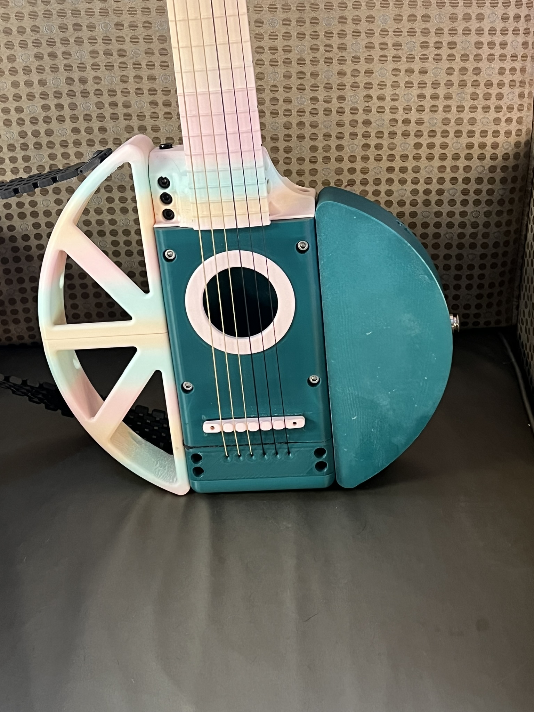
models/Wing Sets/BanjNo/pictures/IMG_4302.JPEG
