spikeon/exoguitar/models/Wing Sets/BanjNo/pictures/IMG_4303.JPEG

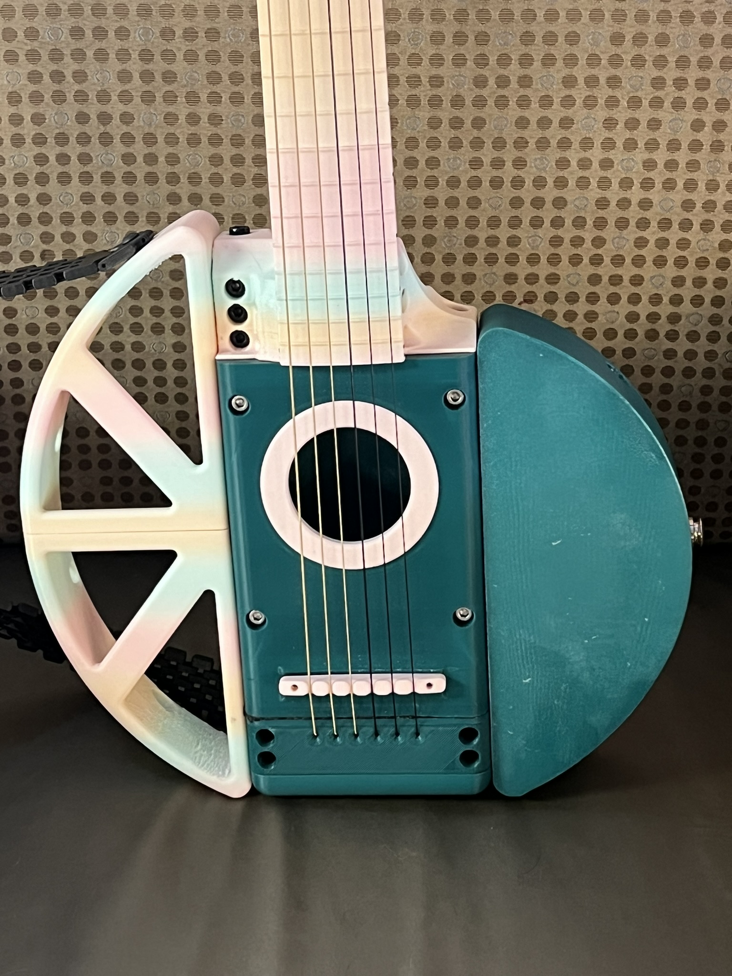
models/Wing Sets/BanjNo/pictures/IMG_4303.JPEG
