spikeon/exoguitar/models/Wing Sets/CigTar/photos/thumb.tall.png

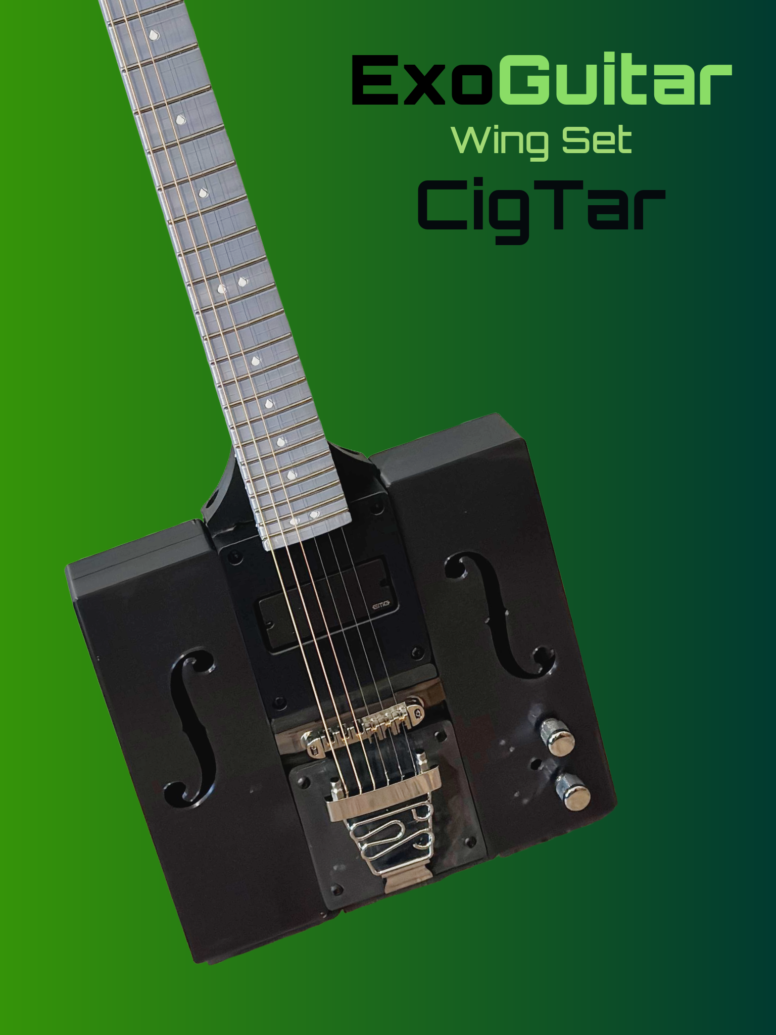
models/Wing Sets/CigTar/photos/thumb.tall.png
