spikeon/exoguitar/models/Wing Sets/CigTar/photos/thumb.wide.png

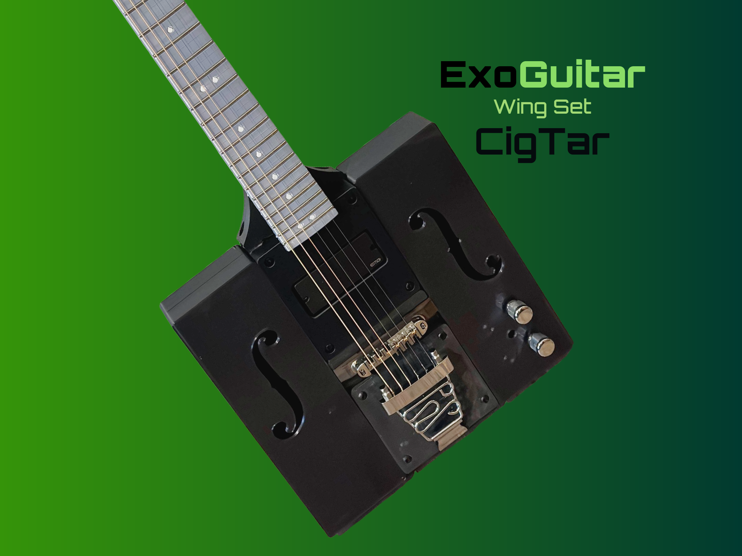
models/Wing Sets/CigTar/photos/thumb.wide.png
