spikeon/exoguitar/models/Wing Sets/Firebird/photos/IMG_4026.jpg

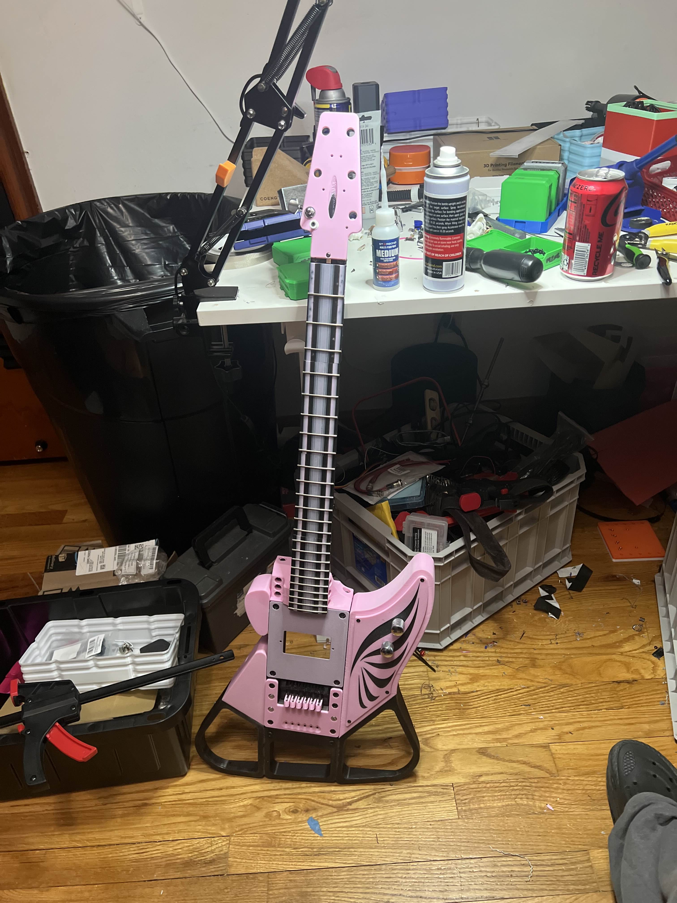
models/Wing Sets/Firebird/photos/IMG_4026.jpg
