spikeon/exoguitar/models/Wing Sets/Firebird/photos/IMG_4041.jpg

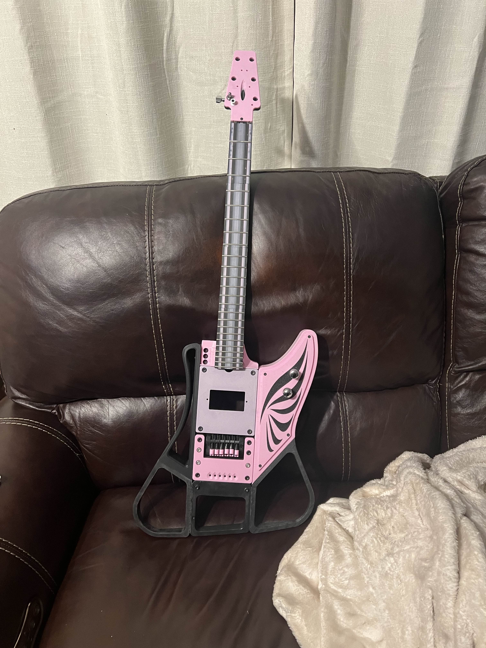
models/Wing Sets/Firebird/photos/IMG_4041.jpg
