spikeon/exoguitar/models/Wing Sets/Heart/photos/IMG_5375.jpg

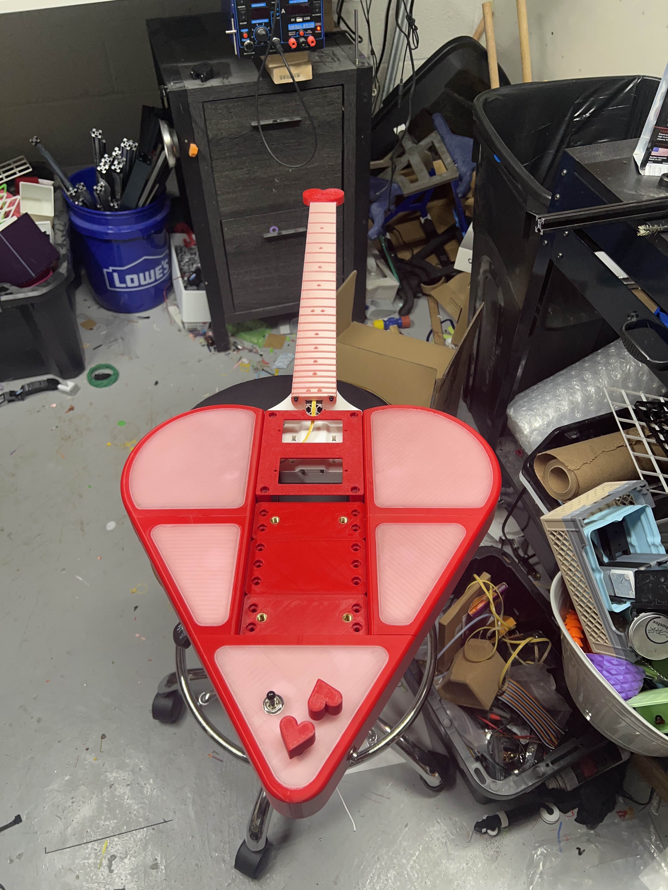
models/Wing Sets/Heart/photos/IMG_5375.jpg
