spikeon/exoguitar/models/Wing Sets/Heart/photos/thumb.tall.png

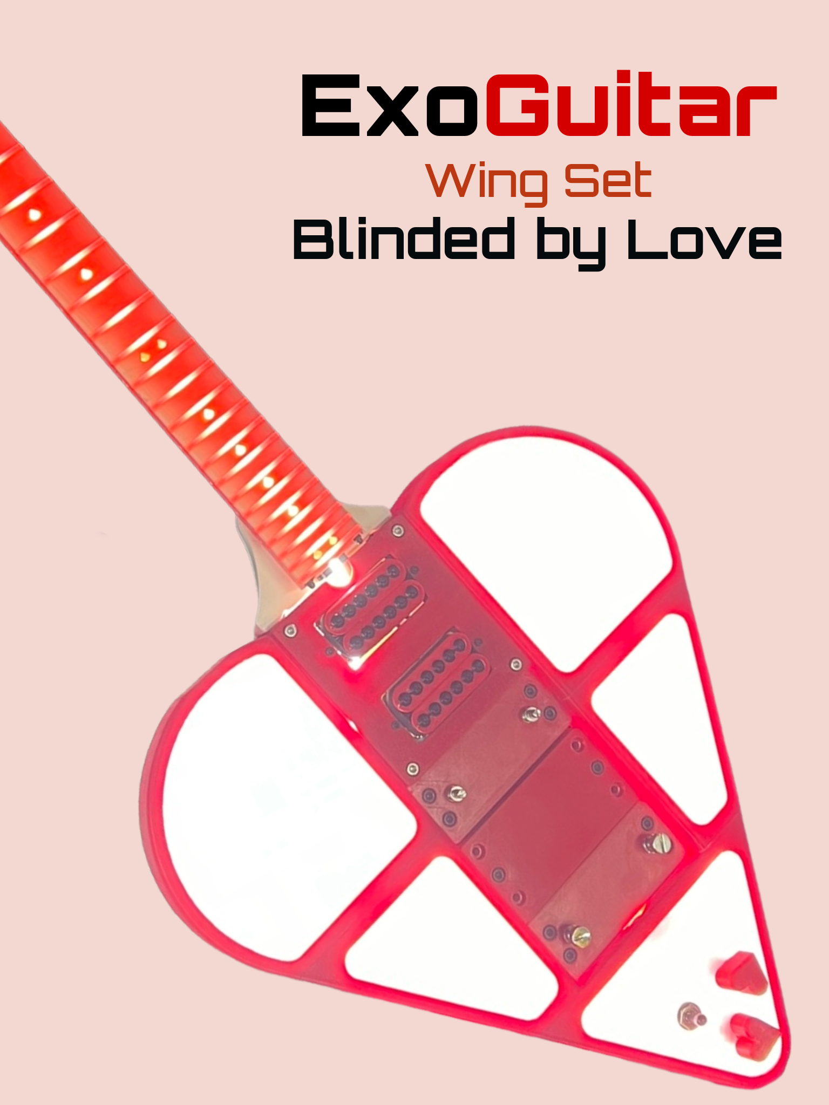
models/Wing Sets/Heart/photos/thumb.tall.png
