spikeon/exoguitar/models/Wing Sets/Heart/photos/thumb.wide.png

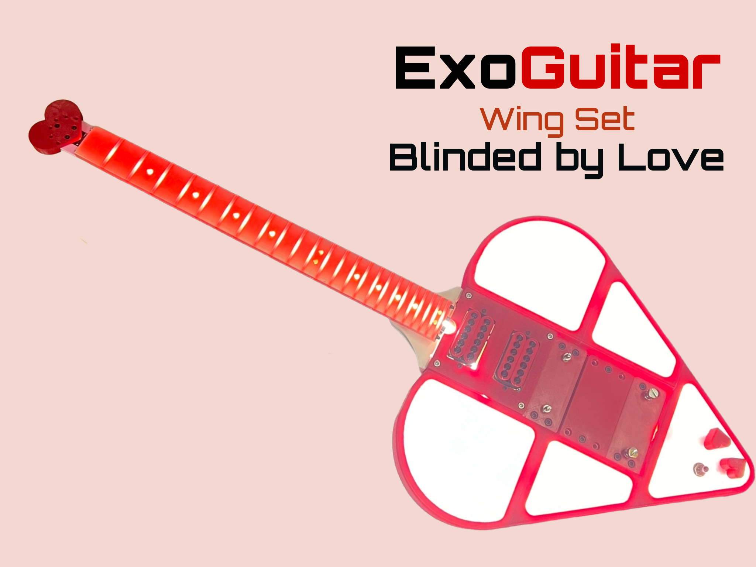
models/Wing Sets/Heart/photos/thumb.wide.png
