spikeon/exoguitar/models/Wing Sets/Ichiban Ezu/photos/IMG_4926.JPEG

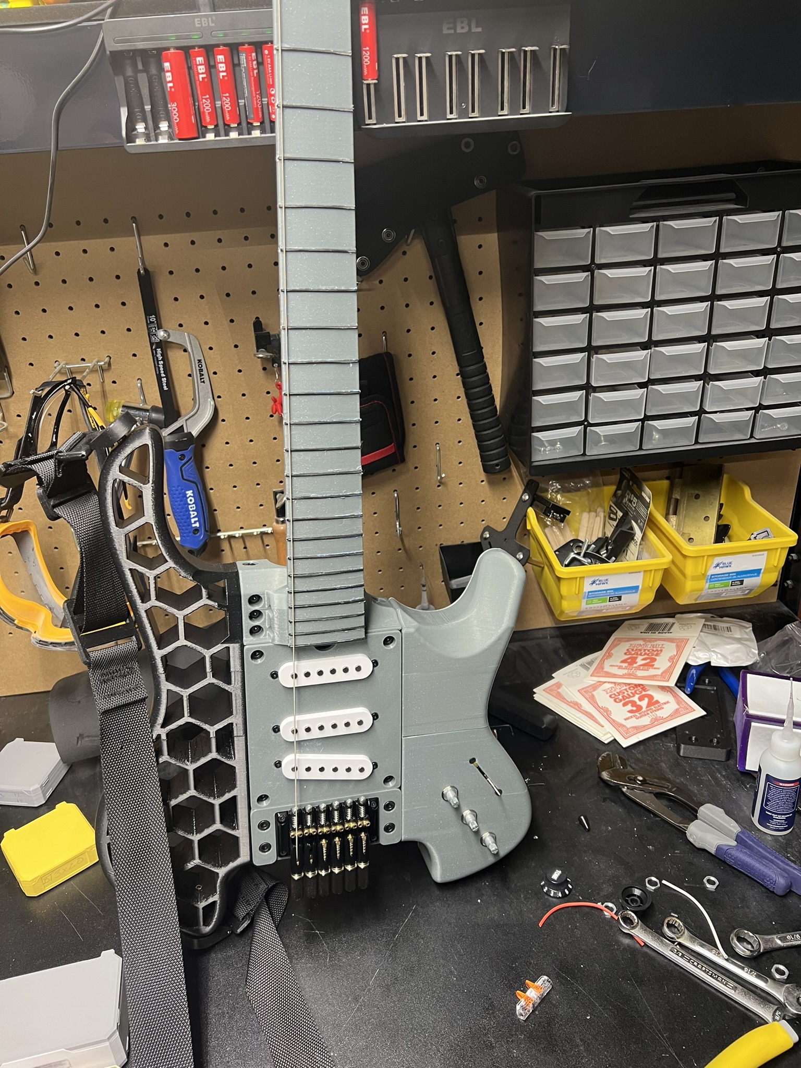
models/Wing Sets/Ichiban Ezu/photos/IMG_4926.JPEG
