spikeon/exoguitar/models/Wing Sets/Ichiban Ezu/photos/IMG_4939.JPEG

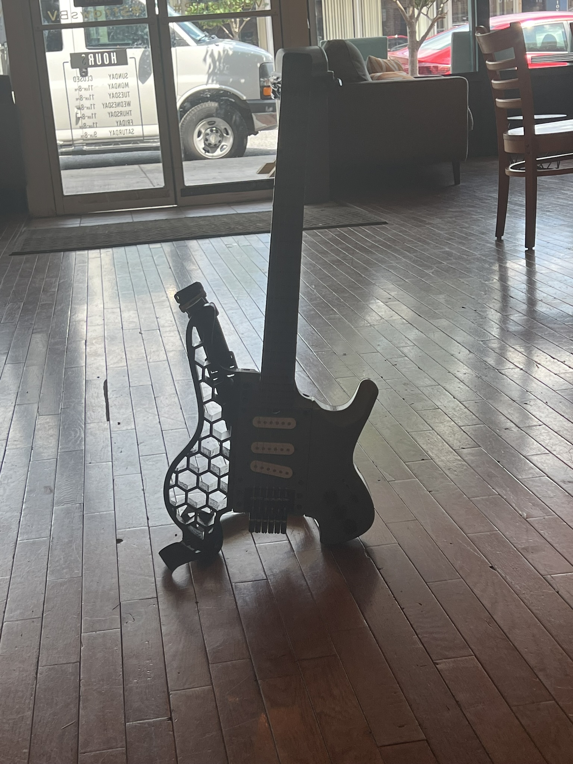
models/Wing Sets/Ichiban Ezu/photos/IMG_4939.JPEG
