spikeon/exoguitar/models/Wing Sets/Ichiban Ezu/photos/IMG_4946.JPEG

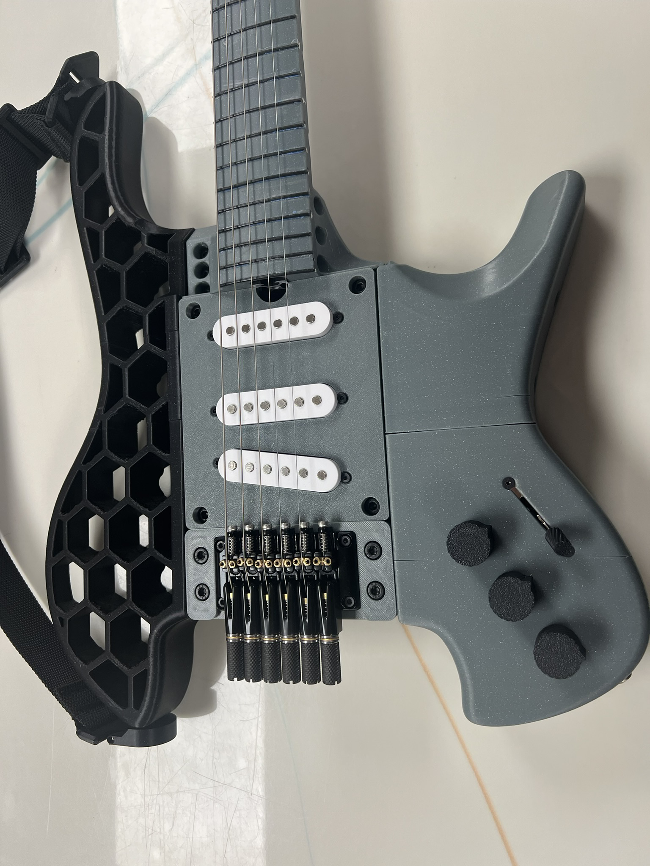
models/Wing Sets/Ichiban Ezu/photos/IMG_4946.JPEG
