spikeon/exoguitar/models/Wing Sets/Ichiban Ezu/photos/IMG_4953.JPEG

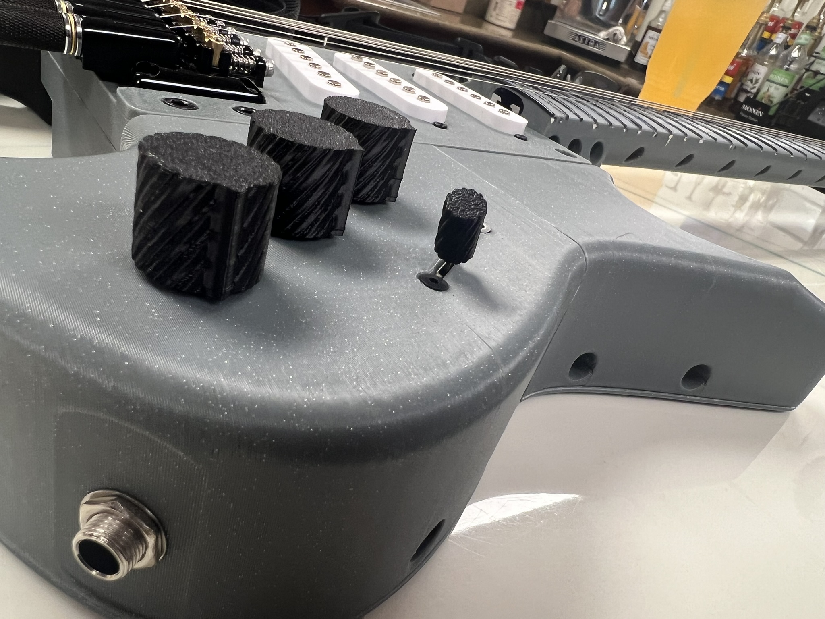
models/Wing Sets/Ichiban Ezu/photos/IMG_4953.JPEG
