spikeon/exoguitar/models/Wing Sets/Ichiban Ezu/photos/IMG_4954 (1).JPEG

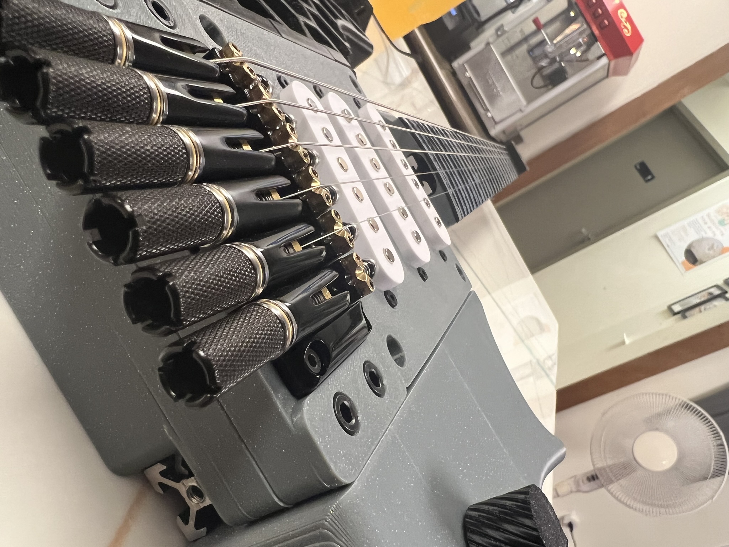
models/Wing Sets/Ichiban Ezu/photos/IMG_4954 (1).JPEG
