spikeon/exoguitar/models/Wing Sets/Jack's Son/pictures/IMG_4432.JPEG

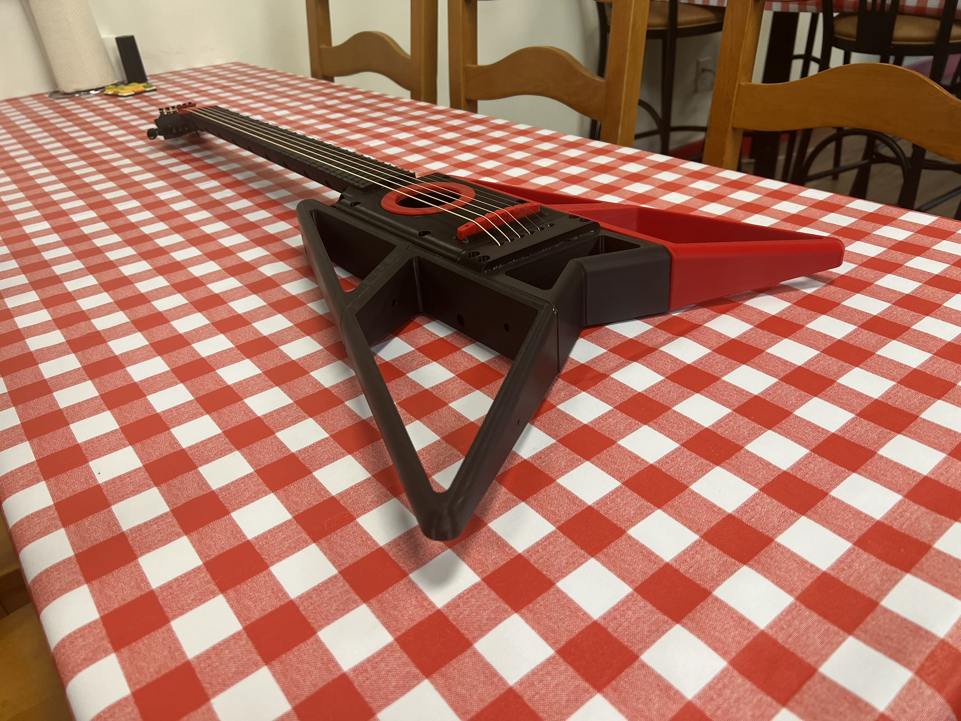
models/Wing Sets/Jack's Son/pictures/IMG_4432.JPEG
