spikeon/exoguitar/models/Wing Sets/Jack's Son/pictures/IMG_4433.JPEG

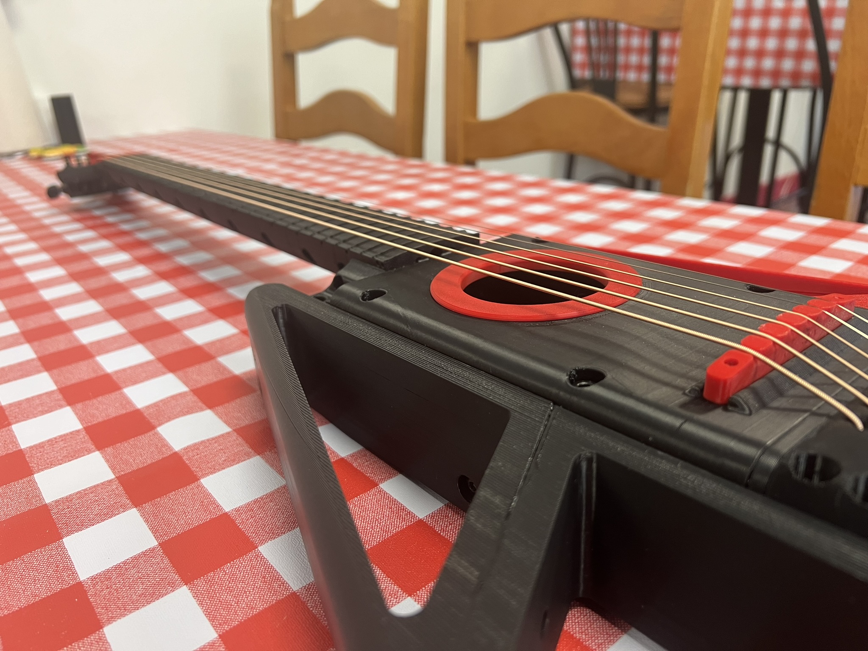
models/Wing Sets/Jack's Son/pictures/IMG_4433.JPEG
