spikeon/exoguitar/models/Wing Sets/Jack's Son/pictures/IMG_4434.JPEG

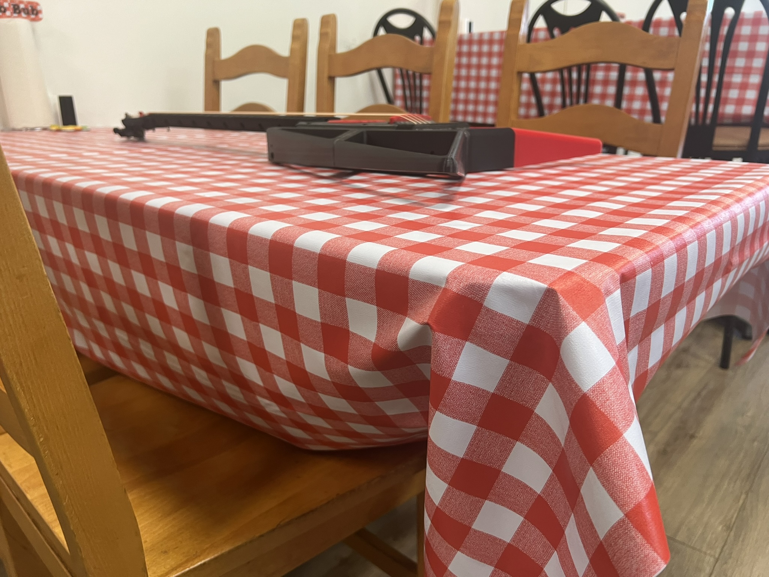
models/Wing Sets/Jack's Son/pictures/IMG_4434.JPEG
