spikeon/exoguitar/models/Wing Sets/Jack's Son/pictures/IMG_4435.JPEG

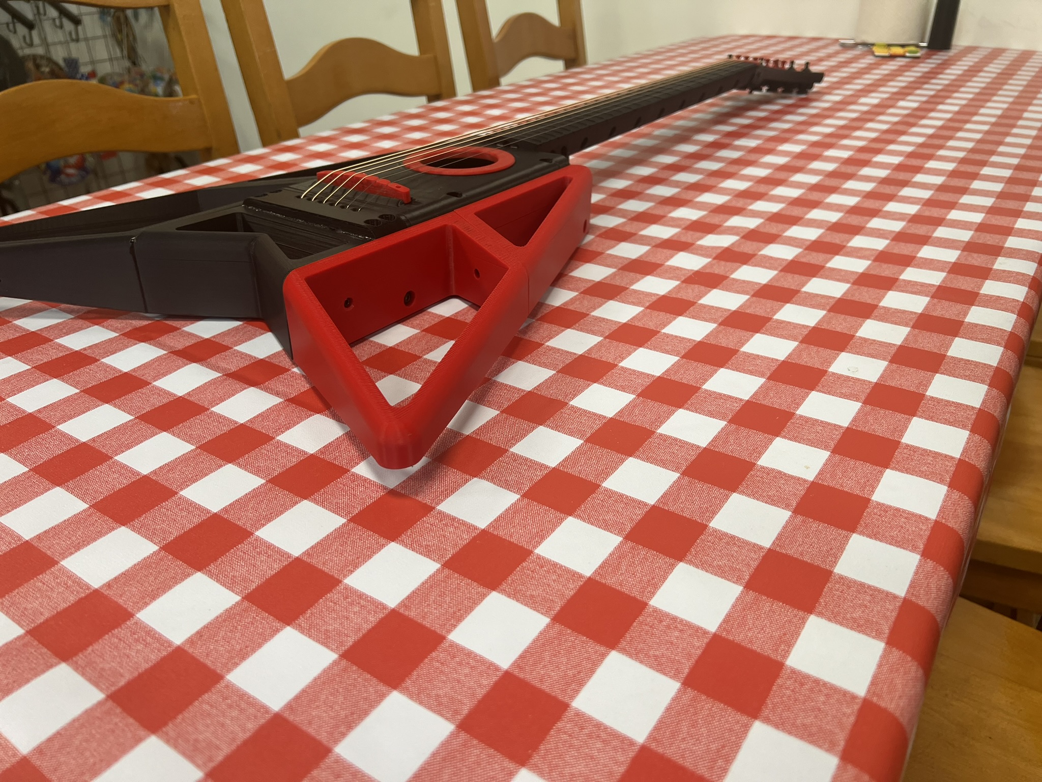
models/Wing Sets/Jack's Son/pictures/IMG_4435.JPEG
