spikeon/exoguitar/models/Wing Sets/Kumiko/photos/IMG_4674.JPEG

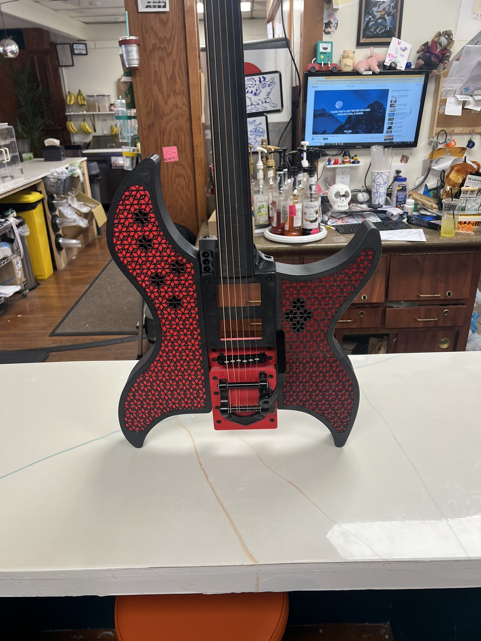
models/Wing Sets/Kumiko/photos/IMG_4674.JPEG
