spikeon/exoguitar/models/Wing Sets/Kumiko/photos/IMG_7210.jpg

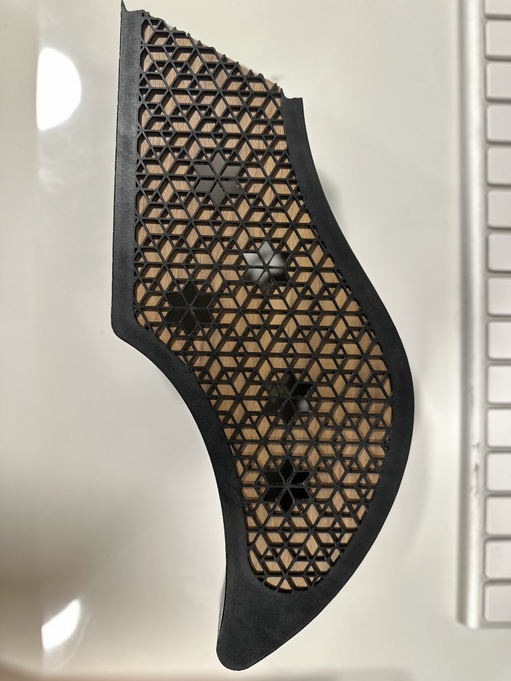
models/Wing Sets/Kumiko/photos/IMG_7210.jpg
