spikeon/exoguitar/models/Wing Sets/Kumiko/photos/IMG_7211.jpg

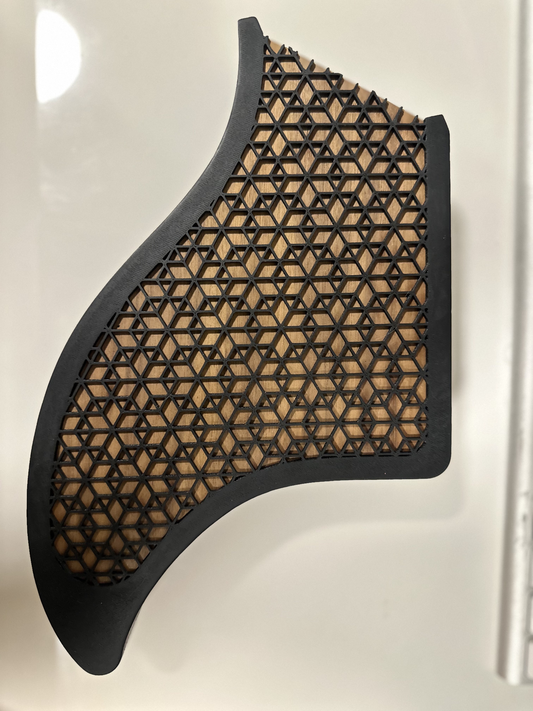
models/Wing Sets/Kumiko/photos/IMG_7211.jpg
