spikeon/exoguitar/models/Wing Sets/Kumiko/photos/IMG_7212.jpg

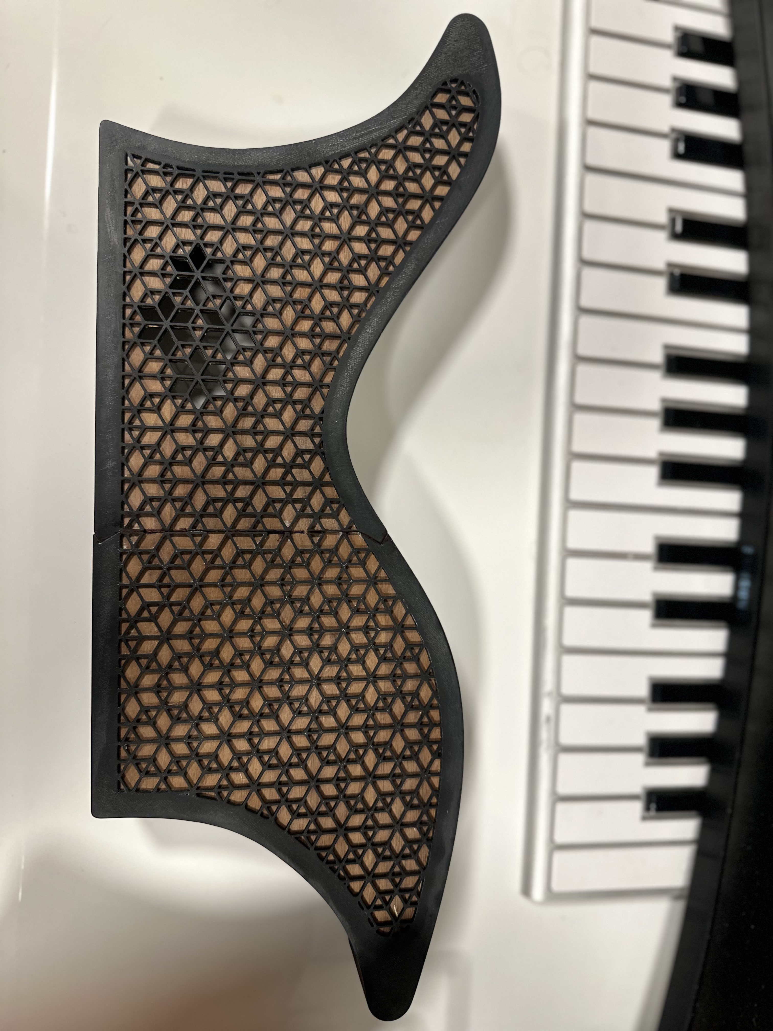
models/Wing Sets/Kumiko/photos/IMG_7212.jpg
