spikeon/exoguitar/models/Wing Sets/Kumiko/photos/IMG_7213.jpg

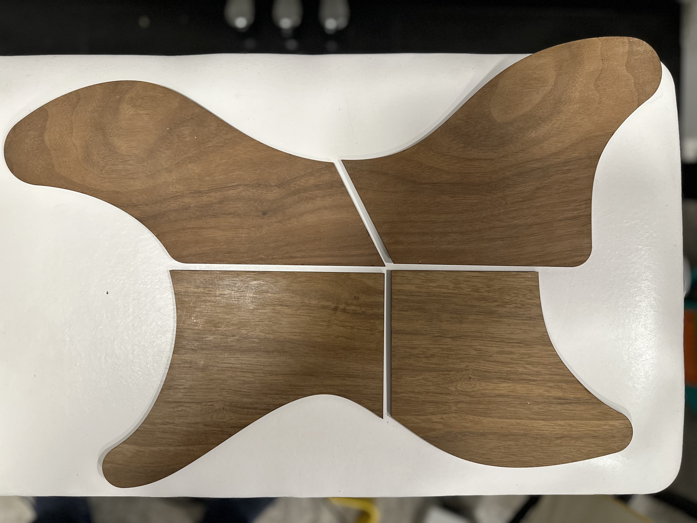
models/Wing Sets/Kumiko/photos/IMG_7213.jpg
