spikeon/exoguitar/models/Wing Sets/Less Paul/photos/IMG_4284.JPEG

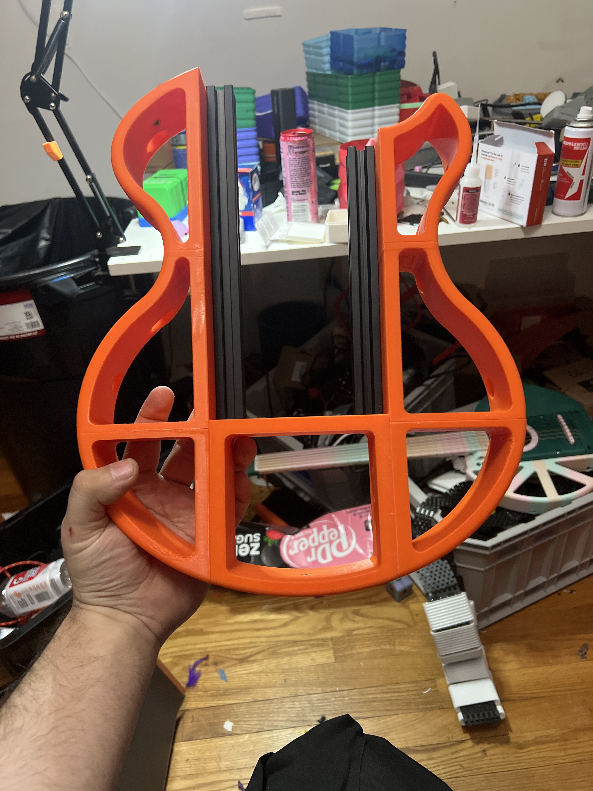
models/Wing Sets/Less Paul/photos/IMG_4284.JPEG
