spikeon/exoguitar/models/Wing Sets/More Paul/photos/IMG_4337.JPEG

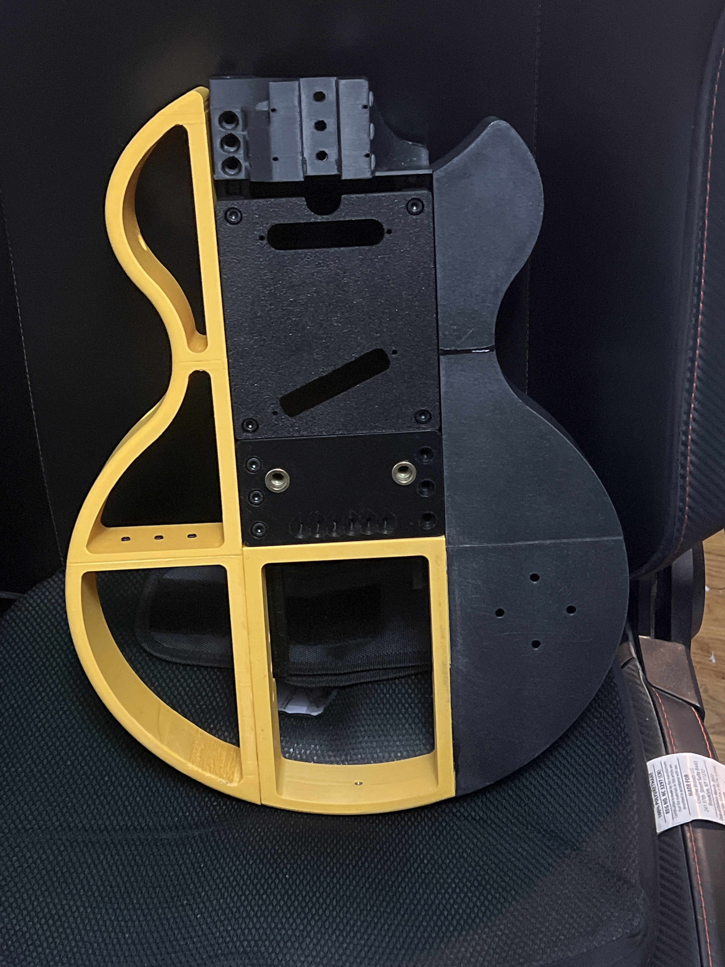
models/Wing Sets/More Paul/photos/IMG_4337.JPEG
