spikeon/exoguitar/models/Wing Sets/More Paul/photos/IMG_4338.JPEG

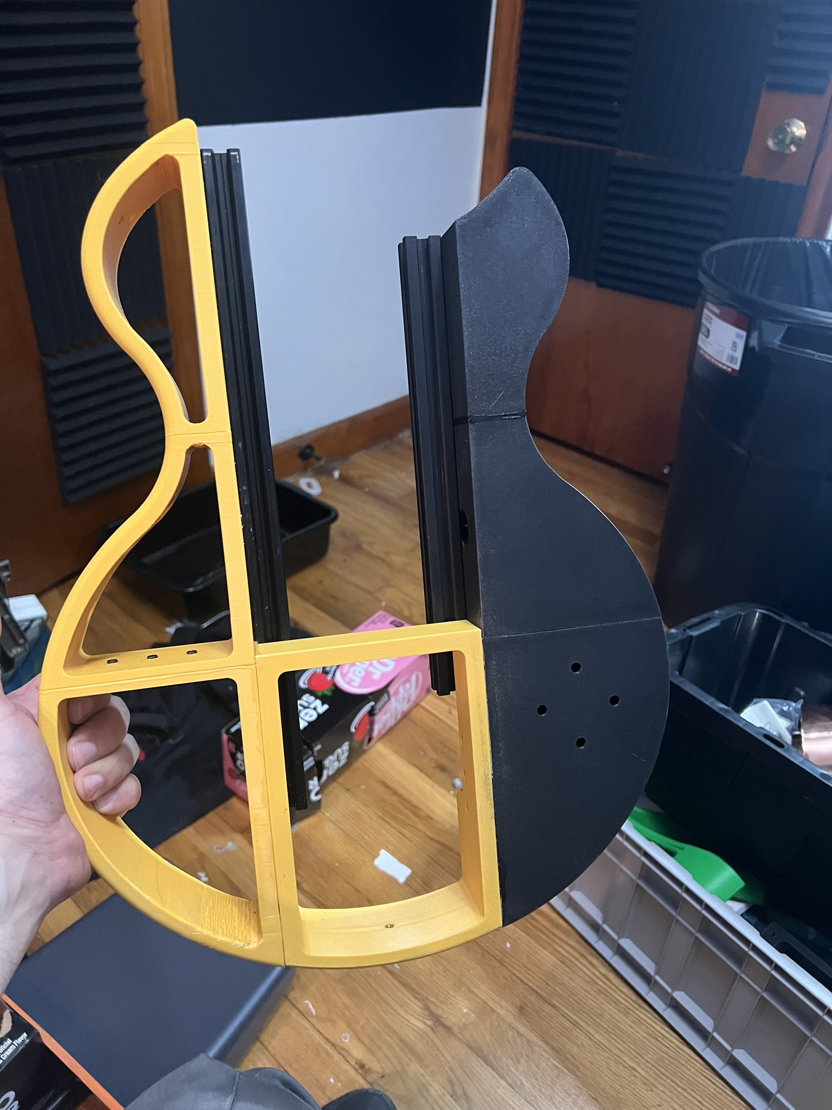
models/Wing Sets/More Paul/photos/IMG_4338.JPEG
