spikeon/exoguitar/models/Wing Sets/More Paul/photos/IMG_4339.JPEG

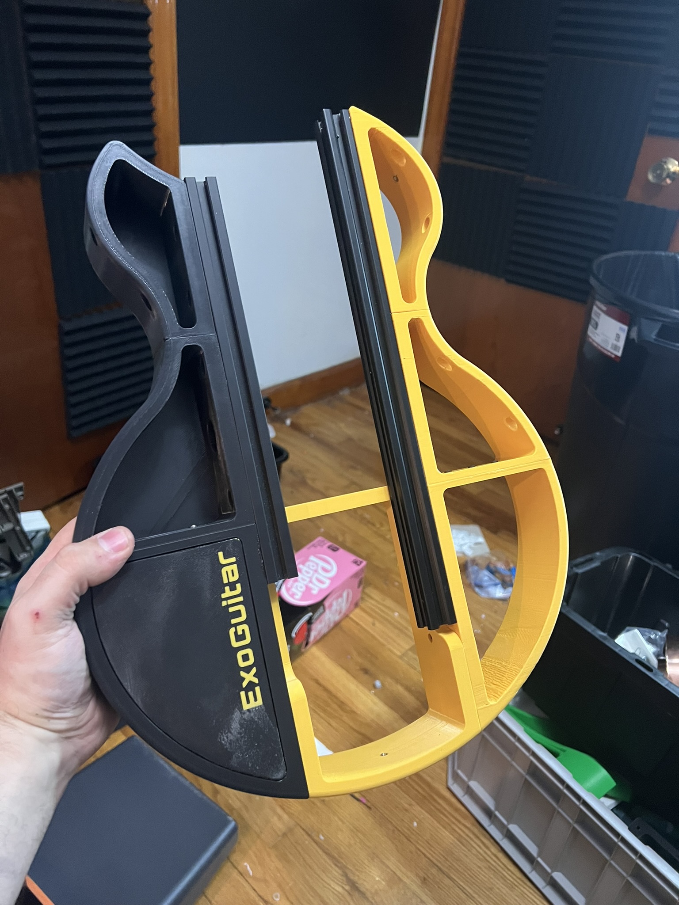
models/Wing Sets/More Paul/photos/IMG_4339.JPEG
