spikeon/exoguitar/models/Wing Sets/More Paul/photos/IMG_4340.JPEG

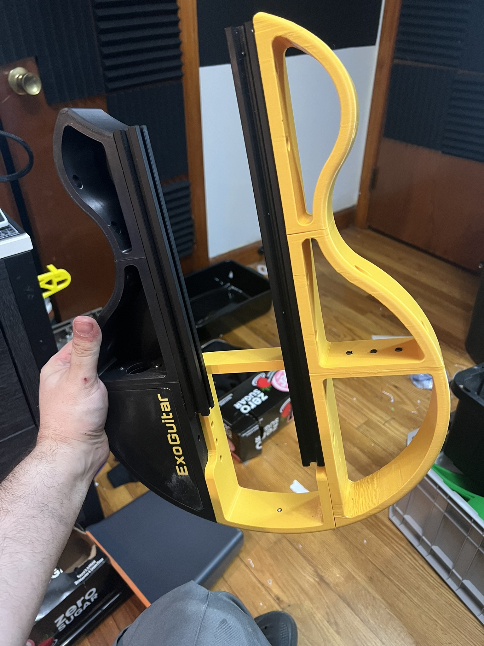
models/Wing Sets/More Paul/photos/IMG_4340.JPEG
