spikeon/exoguitar/models/Wing Sets/More Paul/photos/IMG_4341.JPEG

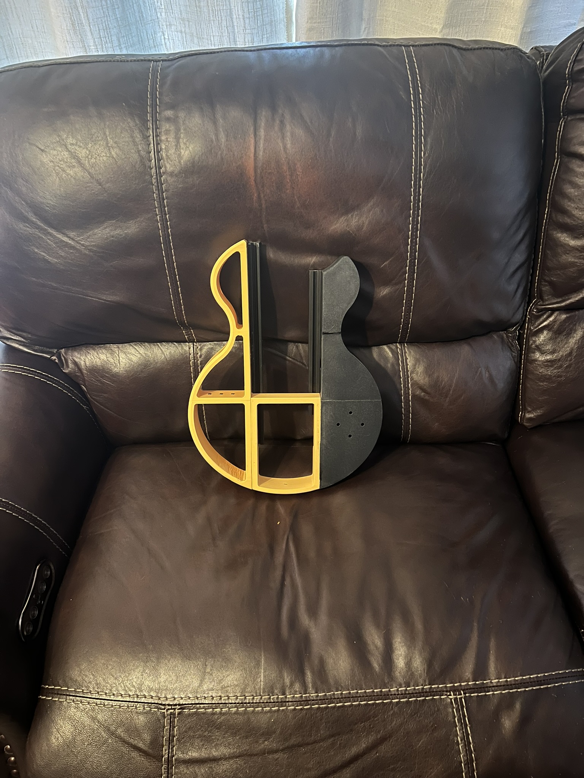
models/Wing Sets/More Paul/photos/IMG_4341.JPEG
