spikeon/exoguitar/models/Wing Sets/More Paul/photos/thumb.tall.png

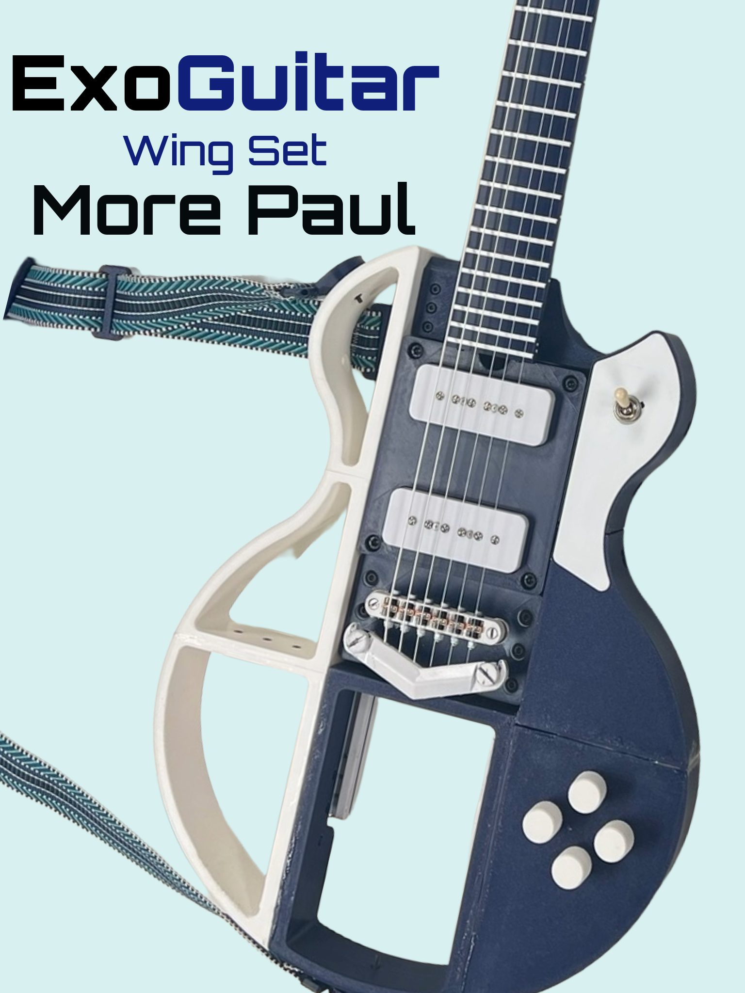
models/Wing Sets/More Paul/photos/thumb.tall.png
