spikeon/exoguitar/models/Wing Sets/More Paul/photos/thumb.wide.png

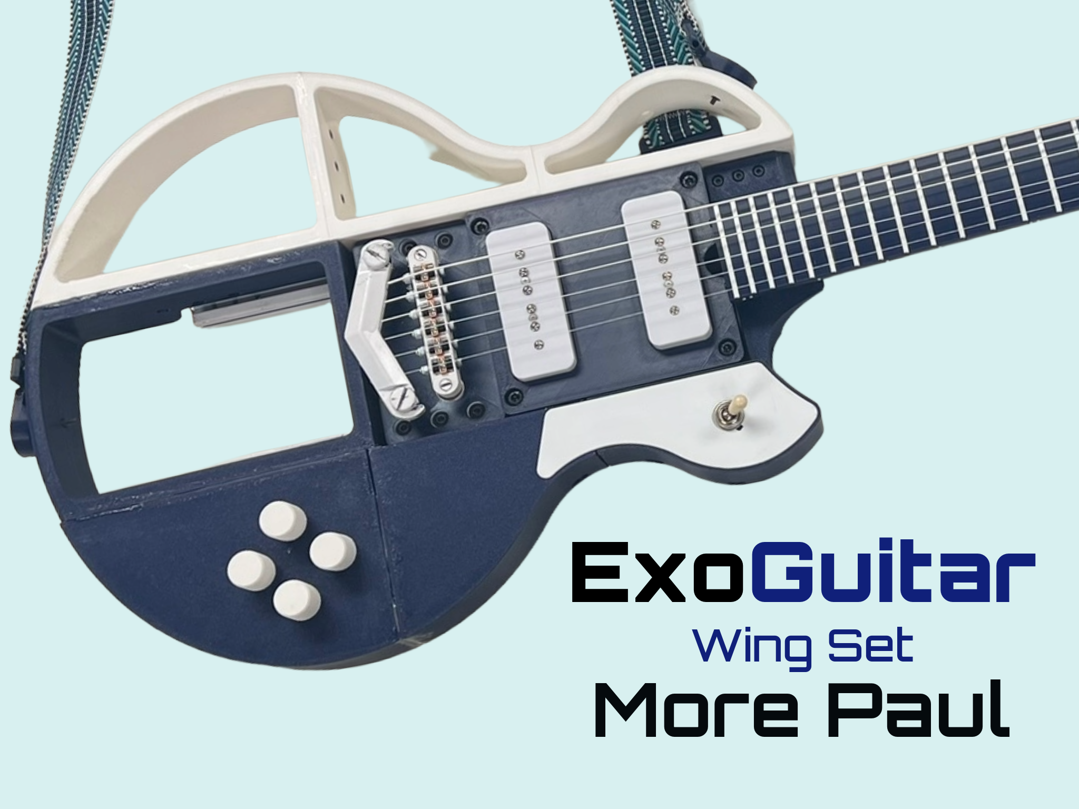
models/Wing Sets/More Paul/photos/thumb.wide.png
