spikeon/exoguitar/models/Wing Sets/Plastic X/photos/IMG_5270.JPEG

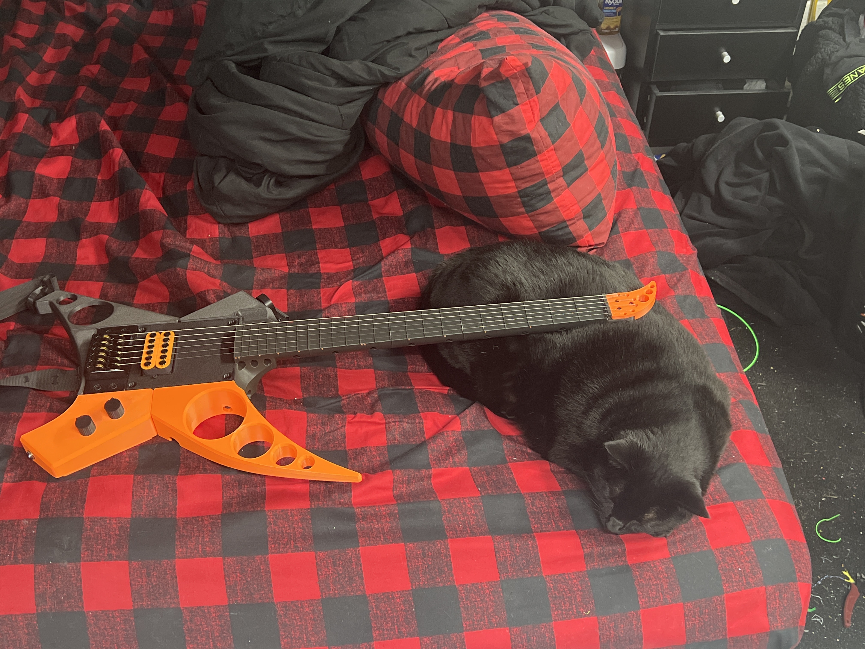
models/Wing Sets/Plastic X/photos/IMG_5270.JPEG
