spikeon/exoguitar/models/Wing Sets/Plastic X/photos/IMG_5296.JPEG

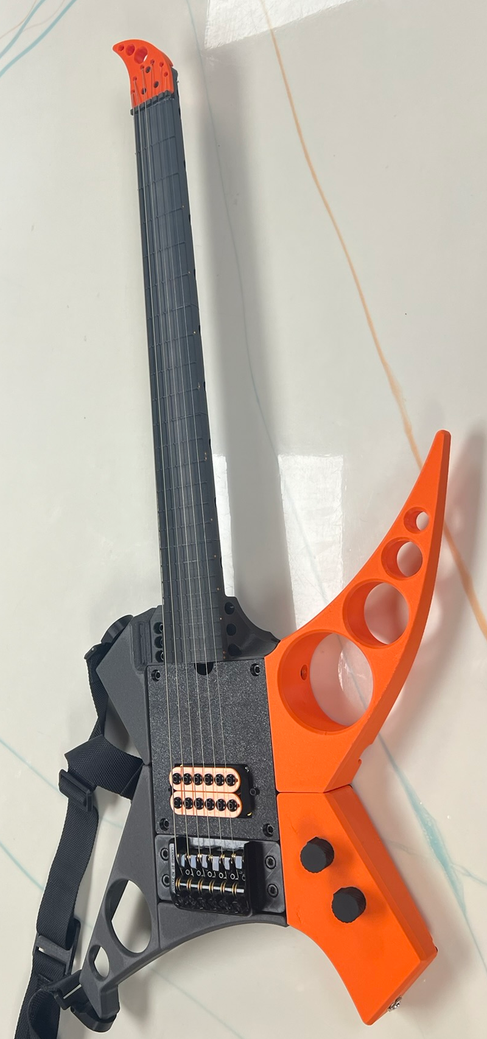
models/Wing Sets/Plastic X/photos/IMG_5296.JPEG
