spikeon/exoguitar/models/Wing Sets/Plastic X/photos/IMG_5297.JPEG

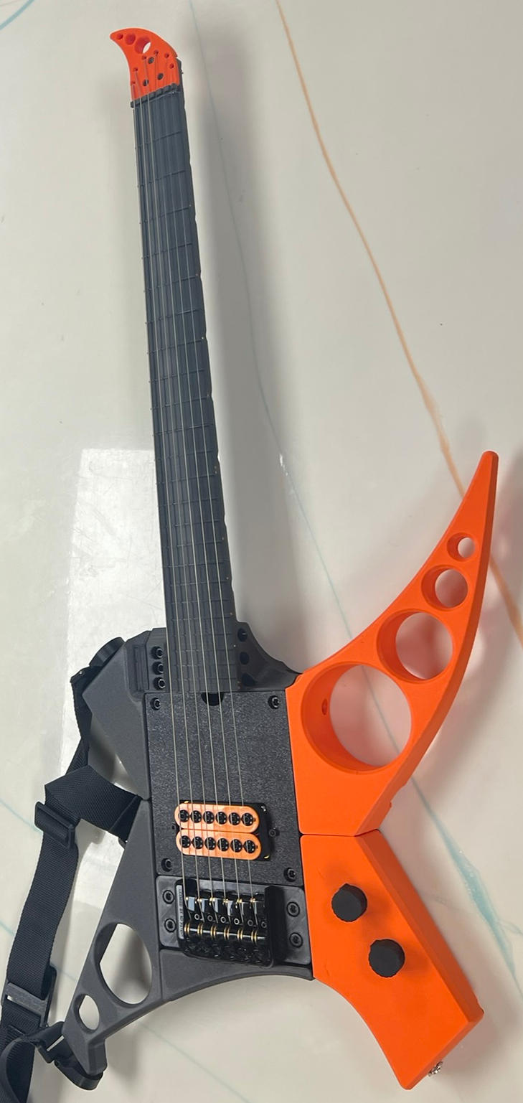
models/Wing Sets/Plastic X/photos/IMG_5297.JPEG
