spikeon/exoguitar/models/Wing Sets/Plastic X/photos/IMG_5299.JPEG

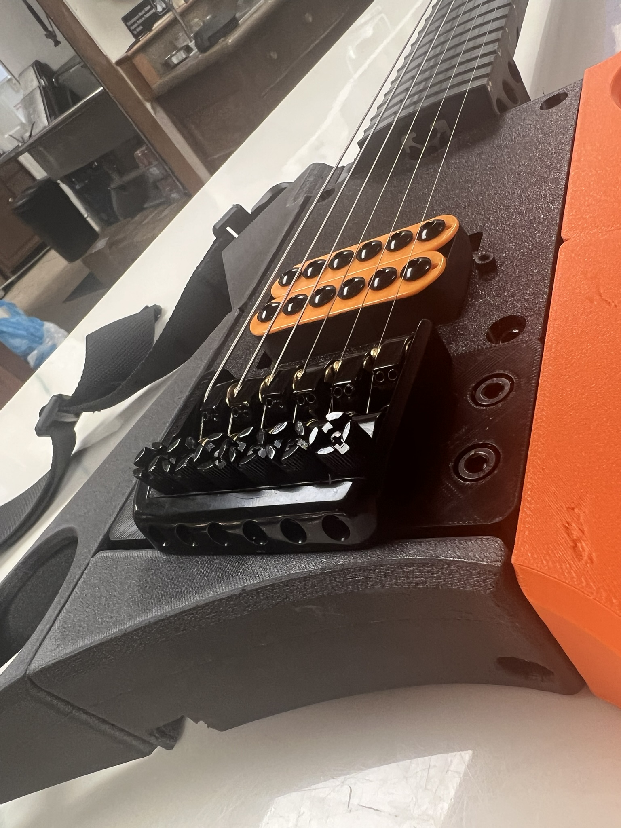
models/Wing Sets/Plastic X/photos/IMG_5299.JPEG
