spikeon/exoguitar/models/Wing Sets/Plastic X/photos/IMG_5302.JPEG

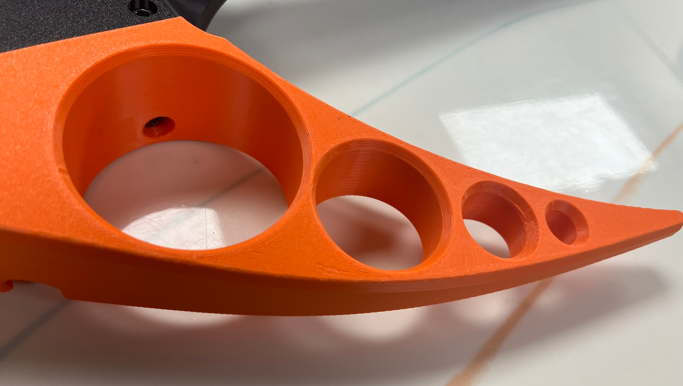
models/Wing Sets/Plastic X/photos/IMG_5302.JPEG
