spikeon/exoguitar/models/Wing Sets/Plastic X/photos/IMG_5303.JPEG

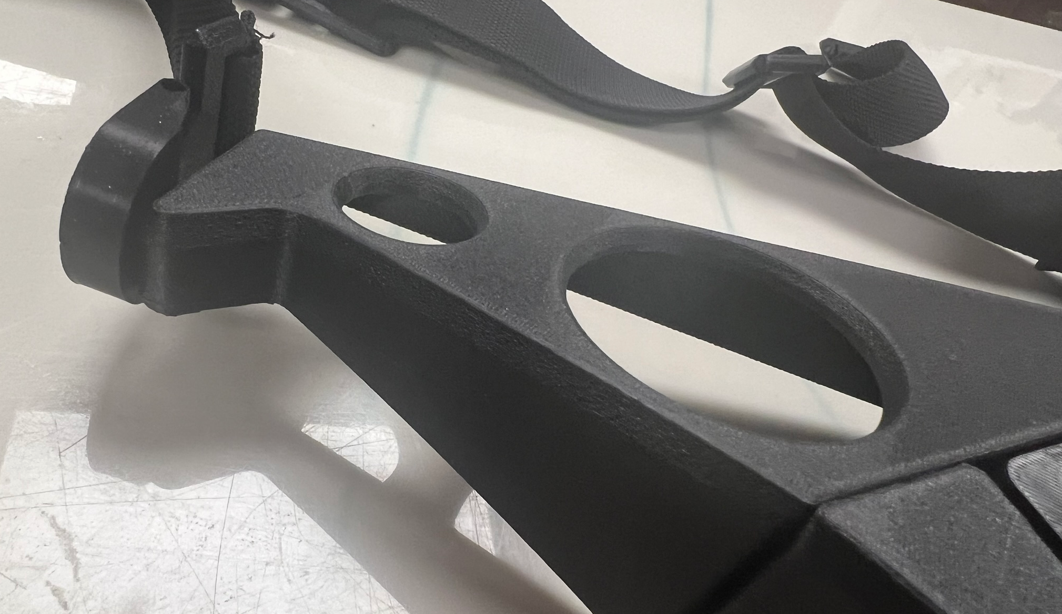
models/Wing Sets/Plastic X/photos/IMG_5303.JPEG
