spikeon/exoguitar/models/Wing Sets/Plastic X/photos/thumb.tall.png

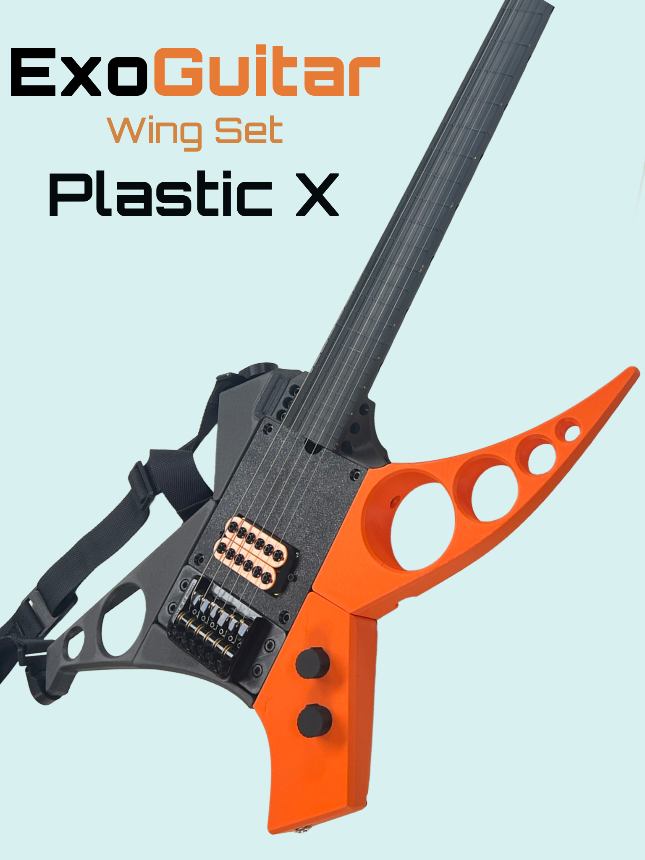
models/Wing Sets/Plastic X/photos/thumb.tall.png
