spikeon/exoguitar/models/Wing Sets/Plastic X/photos/thumb.wide.png

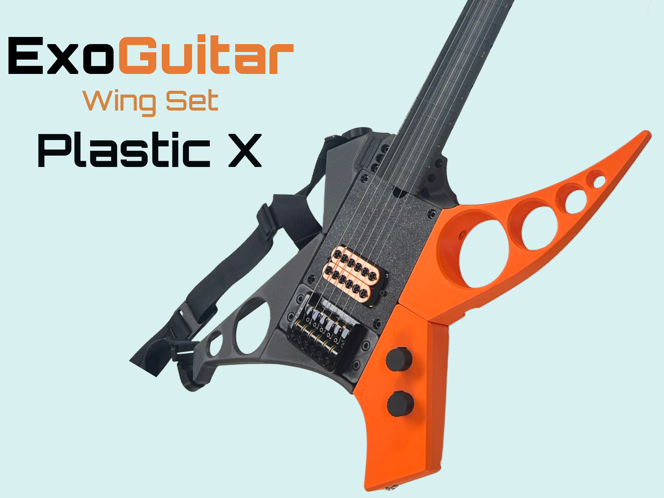
models/Wing Sets/Plastic X/photos/thumb.wide.png
