spikeon/exoguitar/models/Wing Sets/Symmertrical Guitar/photos/IMG_5572.jpg

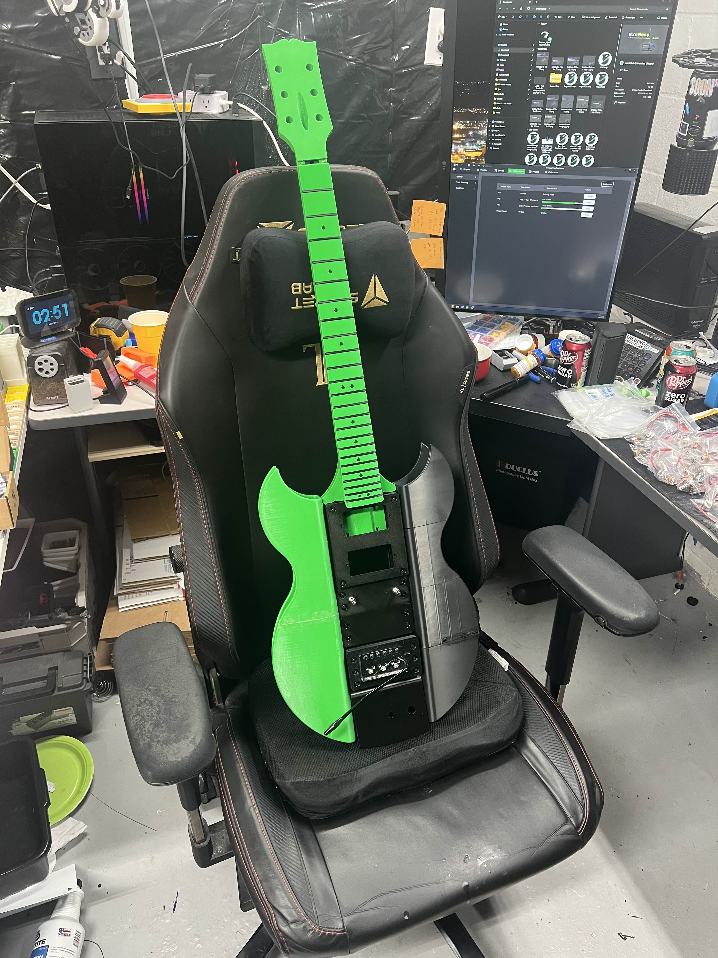
models/Wing Sets/Symmertrical Guitar/photos/IMG_5572.jpg
