spikeon/exoguitar/models/Wing Sets/Symmertrical Guitar/photos/IMG_5573.jpg

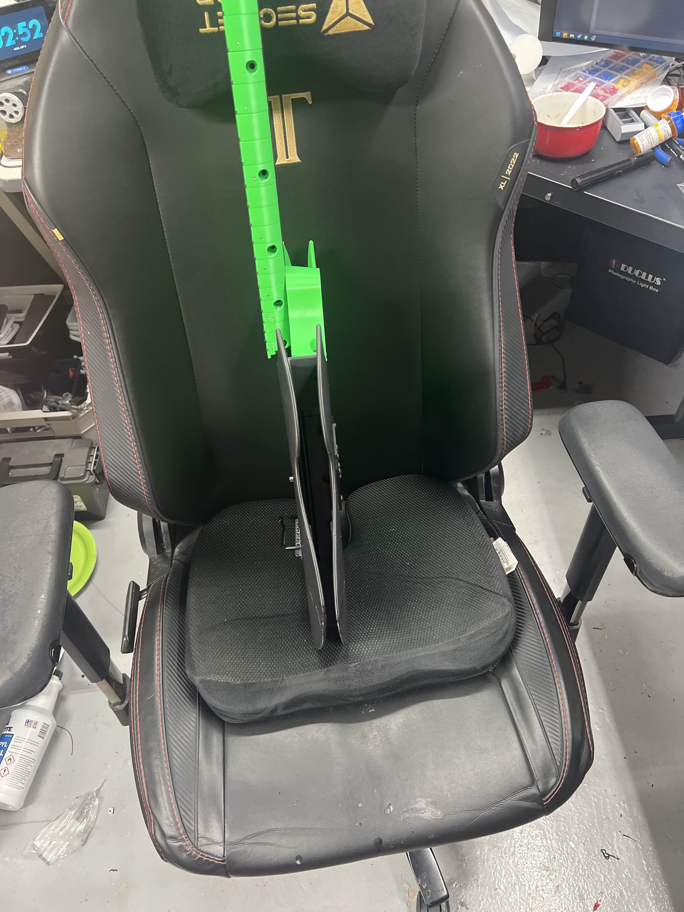
models/Wing Sets/Symmertrical Guitar/photos/IMG_5573.jpg
