spikeon/exoguitar/models/Wing Sets/Symmertrical Guitar/photos/IMG_5574.jpg

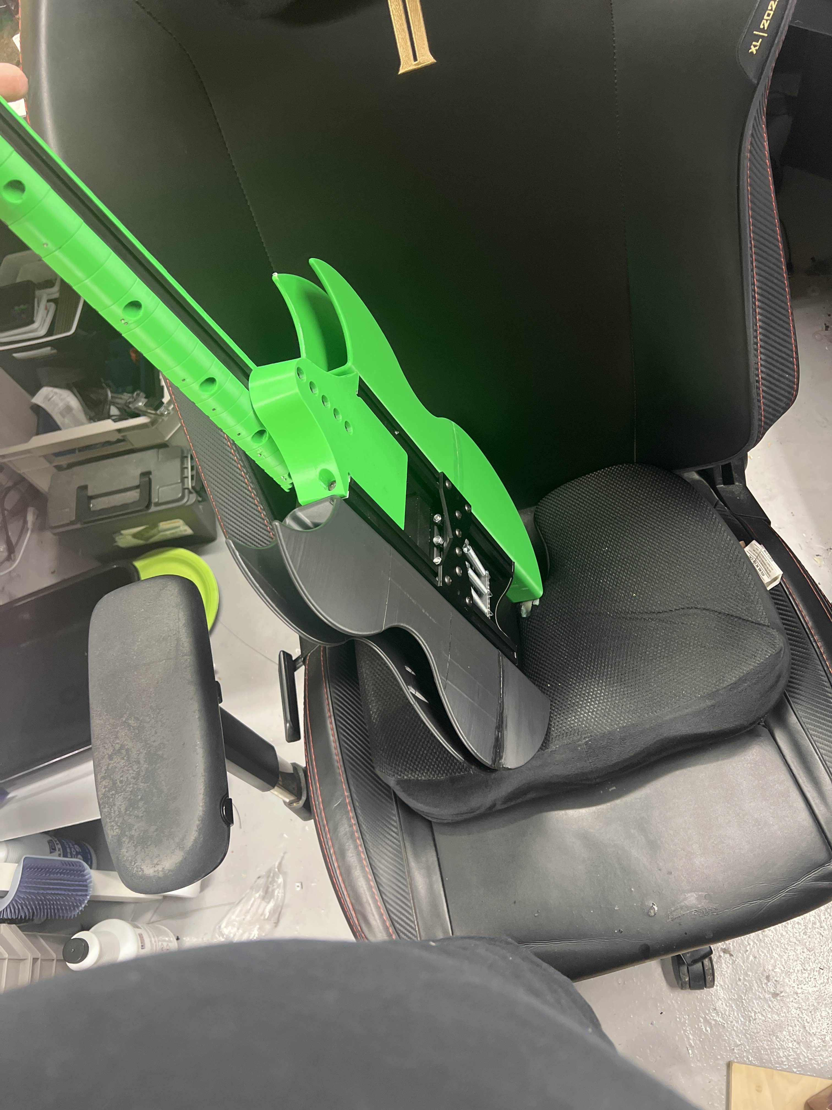
models/Wing Sets/Symmertrical Guitar/photos/IMG_5574.jpg
