spikeon/exoguitar/models/Wing Sets/Symmertrical Guitar/photos/thumb.tall.png

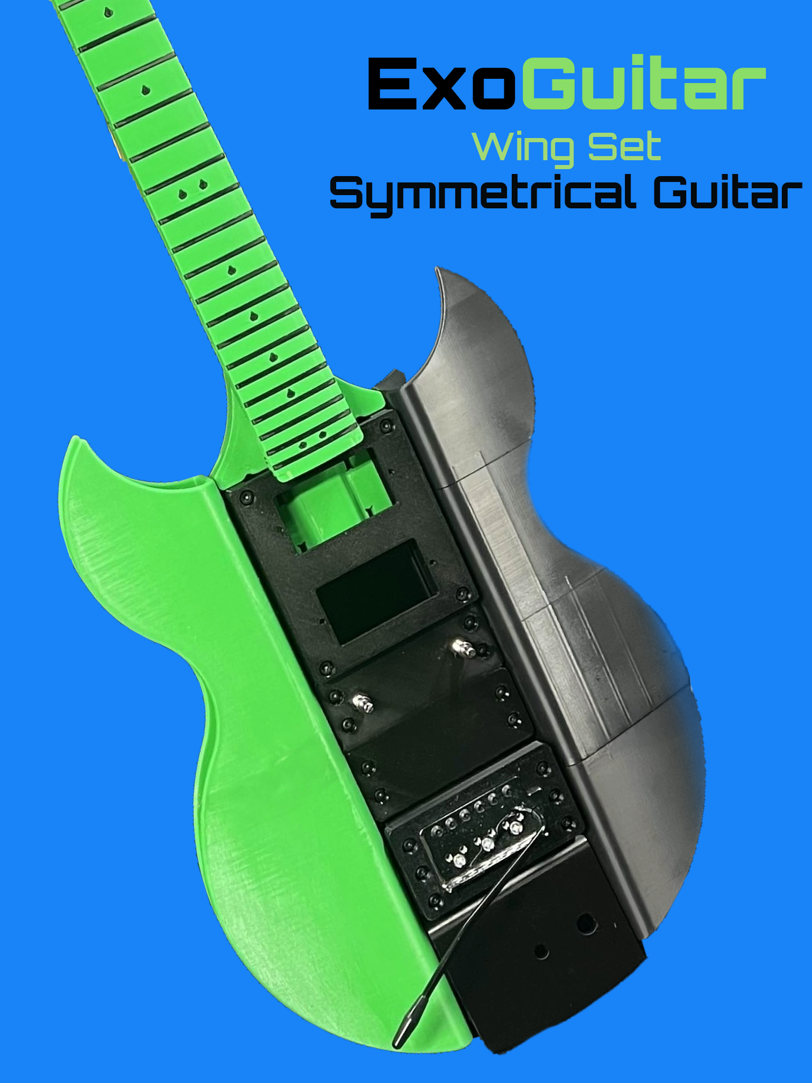
models/Wing Sets/Symmertrical Guitar/photos/thumb.tall.png
