spikeon/exoguitar/models/Wing Sets/Symmertrical Guitar/photos/thumb.wide.png

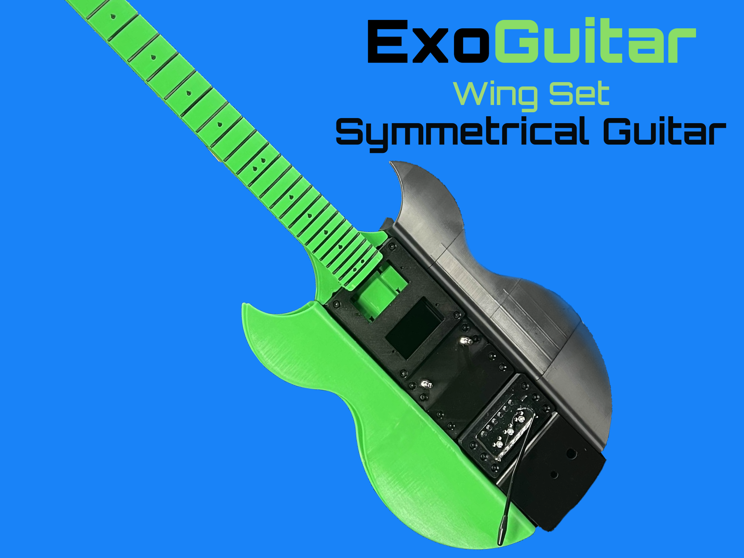
models/Wing Sets/Symmertrical Guitar/photos/thumb.wide.png
