spikeon/exoguitar/models/Wing Sets/Venom/photos/IMG_3787.JPEG

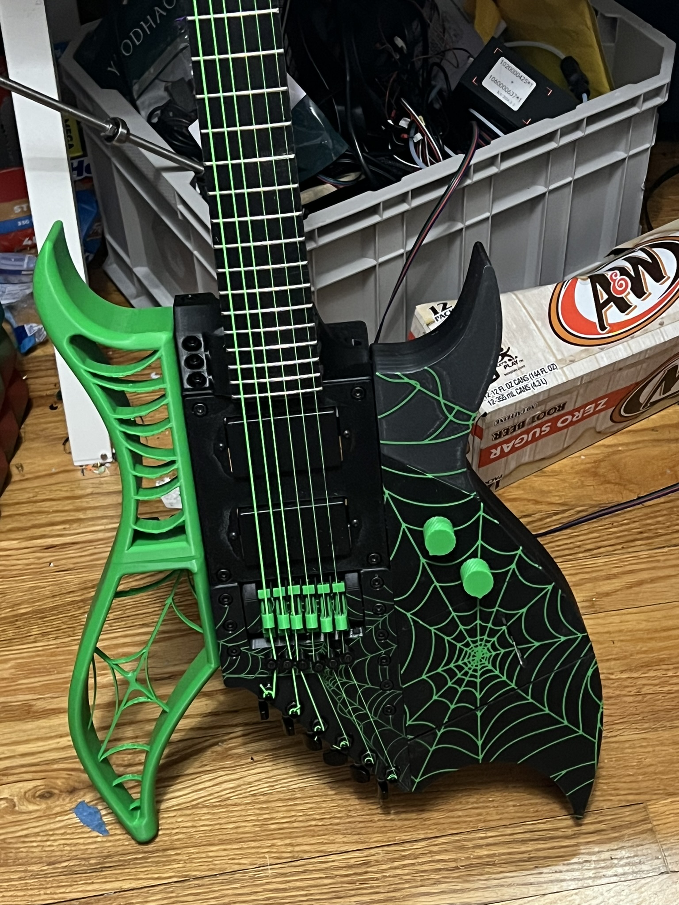
models/Wing Sets/Venom/photos/IMG_3787.JPEG
