spikeon/exoguitar/models/Wing Sets/Warlock/photos/IMG_4169 (1).JPEG

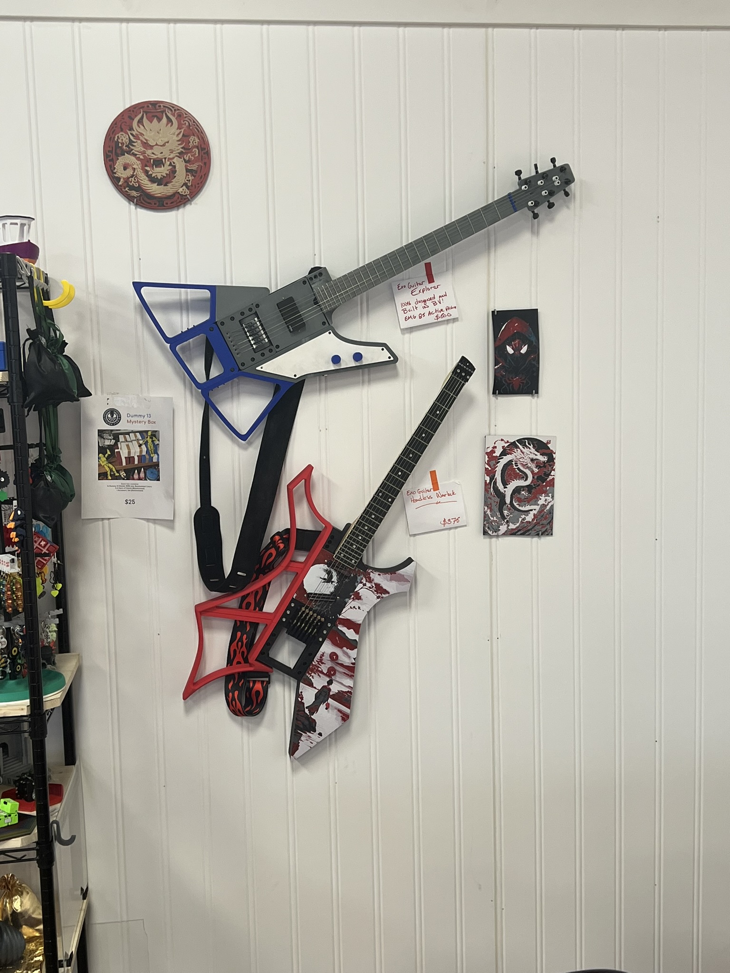
models/Wing Sets/Warlock/photos/IMG_4169 (1).JPEG
