spikeon/exoguitar/models/Strap/Clip Strap/BOM.txt

Qty   Name                     Url                      Optional
   1  2in Nylon Strap          https://amzn.to/4nahPe9  false
   2  https://amzn.to/3KKWysY                           false
