spikeon/exoguitar/models/Wing Sets/Heart/BOM.txt

Qty   Name            Url                      Optional
   1  5mm COB LED     https://amzn.to/4fJ2lee  false
   1  12v 1a Battery  https://amzn.to/3Zx7X4g  false
   1  12v LED Dimmer  https://amzn.to/4lsrOK4  false
