spikeon/exoguitar/models/Wing Sets/Plastic X/BOM.txt

Qty   Name   Url                                                                                                        Optional
   6  BT3x8  https://us.store.bambulab.com/products/bt3-socket-head-cap-self-tapping-screws-shcs-new?id=42382271611016  false
