spikeon/exoguitar/models/Extras/Guitar Bow/BOM.txt

Qty   Name   Url                      Optional
   1  Rosin  https://amzn.to/43BsGqF  false
