spikeon/exoguitar/models/Extras/Sanding Jig/BOM.txt

Qty   Name                       Url                      Optional
   1  Sandpaper Roll - 400 Grit  https://amzn.to/4dRJHQp  false
