spikeon/exoguitar/models/Neck/ExoGuitar - Neck - Fretless 1.step

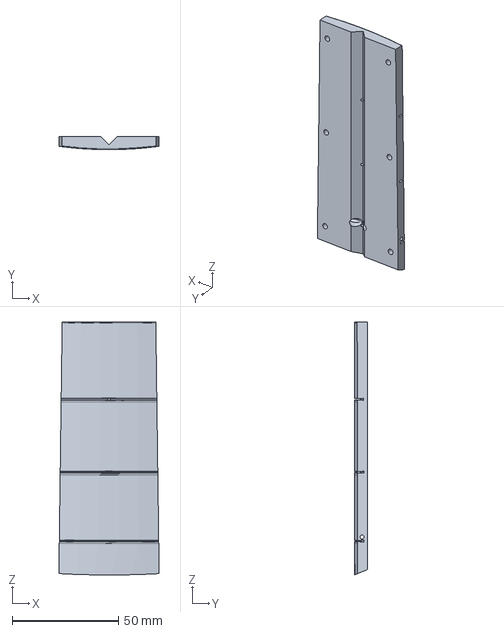
[picture p144: CAD file, 2025-01-11]
models/Neck/ExoGuitar - Neck - Fretless 1.step
47.2 x 6.30 x 119.0 mm
