spikeon/exoguitar/models/Wing Sets/BanjNo/BanjNo.3mf

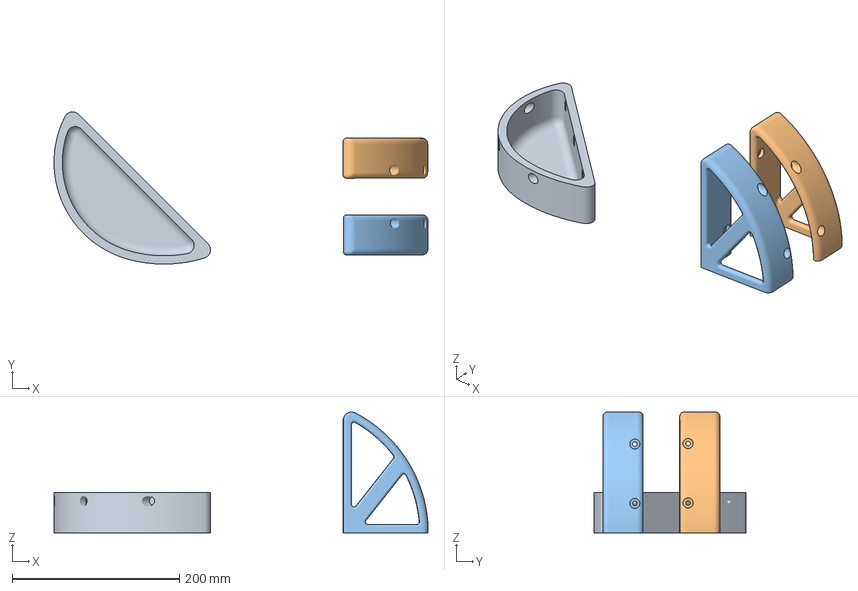
[picture p145: CAD file, 2025-02-13]
models/Wing Sets/BanjNo/BanjNo.3mf
447.2 x 182.0 x 144.4 mm
