spikeon/exoguitar/models/Wing Sets/Kumiko/Kumiko Wings - Right Wing - Bottom - Front - 2 Pot & Switch.dxf

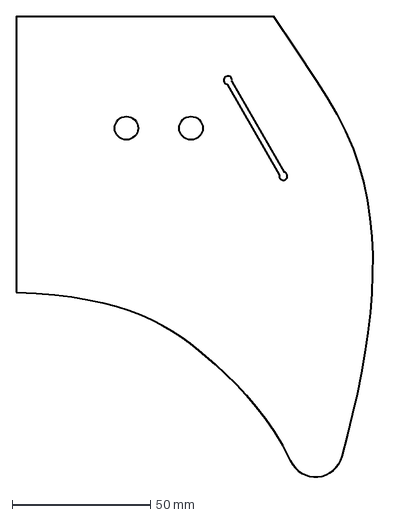
[picture p146: CAD file, 2025-06-17]
models/Wing Sets/Kumiko/Kumiko Wings - Right Wing - Bottom - Front - 2 Pot & Switch.dxf
134.1 x 166.7 mm
