spikeon/exoguitar/models/Wing Sets/Venom/ExoGuitar - Venom.3mf

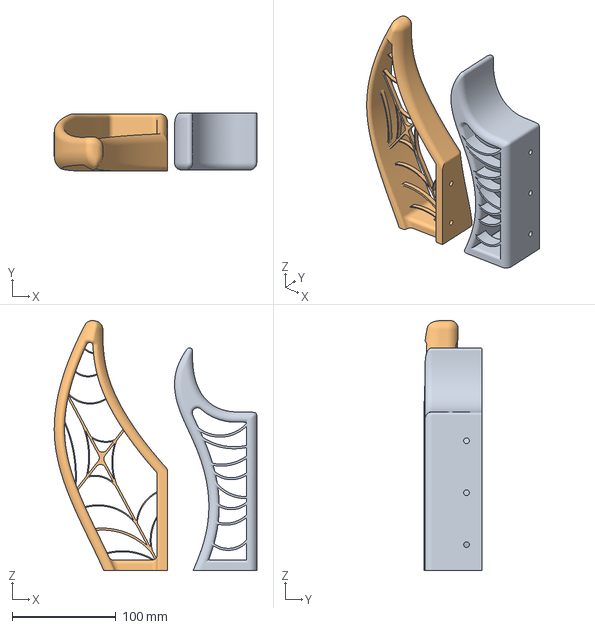
[picture p147: CAD file, 2025-01-05]
models/Wing Sets/Venom/ExoGuitar - Venom.3mf
195.1 x 56.1 x 240.9 mm
ExoGuitar - Top Fang.step
ExoGuitar Main - Headless - Body - Bottom Left.step
