spikeon/exoguitar/models/Neck/ExoGuitar  - Neck - Fretless 4.step

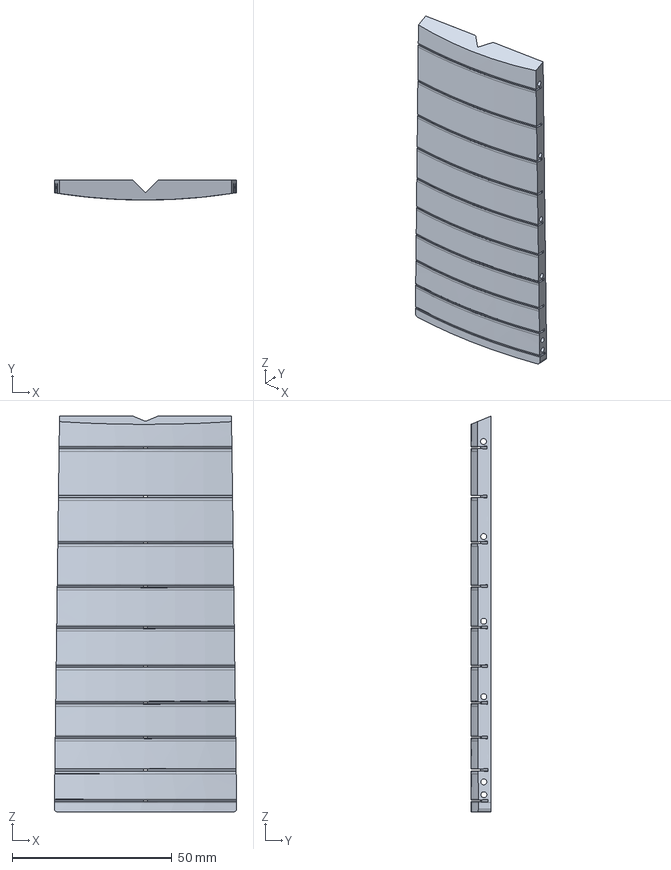
[picture p148: CAD file, 2025-01-11]
models/Neck/ExoGuitar - Neck - Fretless 4.step
57.0 x 6.31 x 123.8 mm
