spikeon/exoguitar/models/Wing Sets/Arasaka/Arasaka.3mf

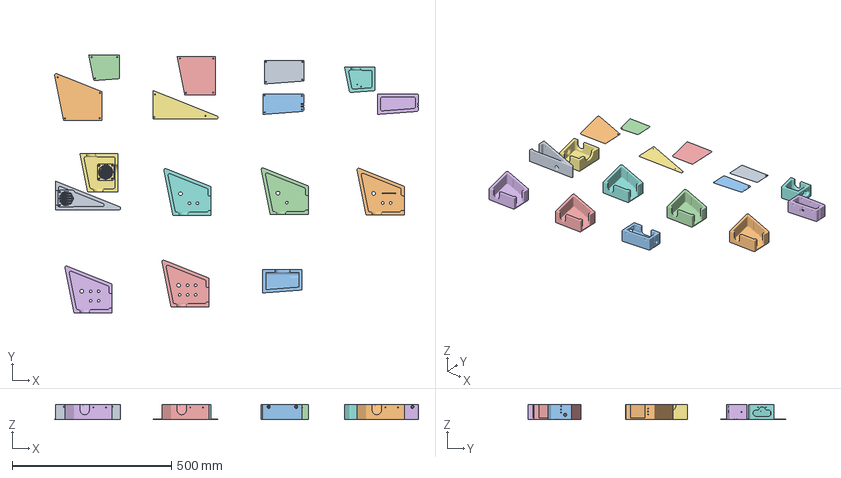
[picture p149: CAD file, 2025-06-05]
models/Wing Sets/Arasaka/Arasaka.3mf
1141.3 x 808.3 x 47.5 mm
Right Top Front
Right Bottom Back
Left Middle Front
Left Bottom Back
Center Back
Left Top Front
Right Top Back
Left Bottom Front
Left Middle Back
Right Bottom Front x 5
Left Top Back
Center Front
