spikeon/exoguitar/models/Wing Sets/Kumiko/Kumiko Wings - Left Wing - Bottom - Front.dxf

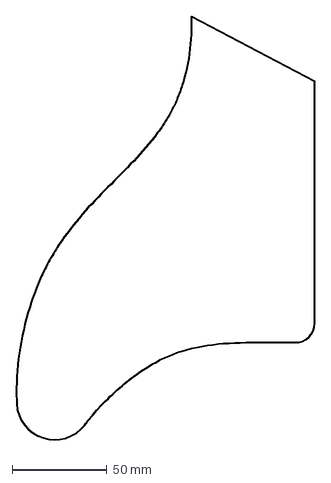
[picture p150: CAD file, 2025-06-17]
models/Wing Sets/Kumiko/Kumiko Wings - Left Wing - Bottom - Front.dxf
157.2 x 224.7 mm
