spikeon/exoguitar/models/Neck/ExoGuitar - Neck - Middle Left.step

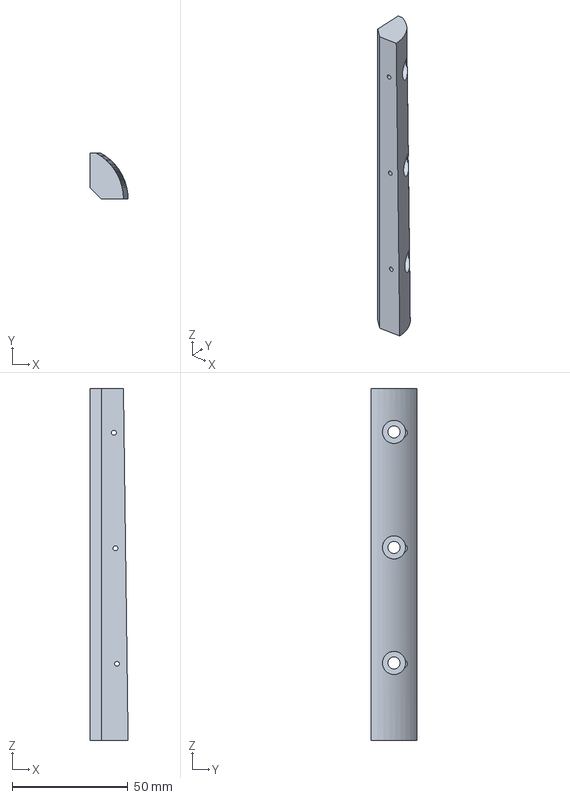
[picture p151: CAD file, 2025-01-11]
models/Neck/ExoGuitar - Neck - Middle Left.step
16.6 x 20.0 x 152.3 mm
