spikeon/exoguitar/models/Wing Sets/Kumiko/Kumiko Wings - Right Wing - Bottom - Back.dxf

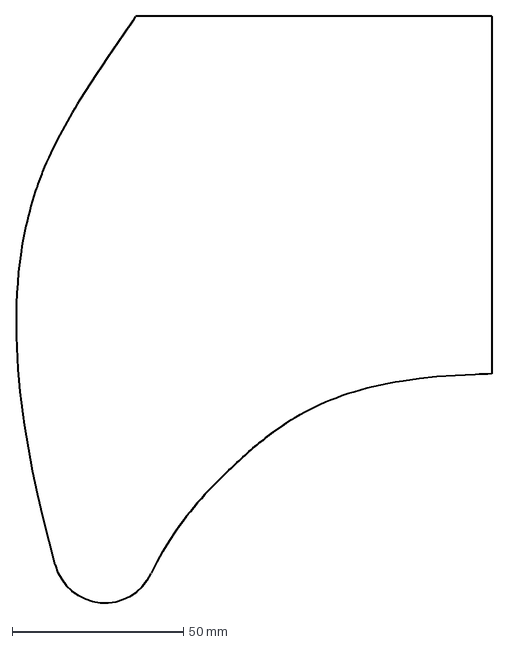
[picture p152: CAD file, 2025-06-17]
models/Wing Sets/Kumiko/Kumiko Wings - Right Wing - Bottom - Back.dxf
138.9 x 171.8 mm
