spikeon/exoguitar/models/Wing Sets/Plastic X/Plastic X.3mf

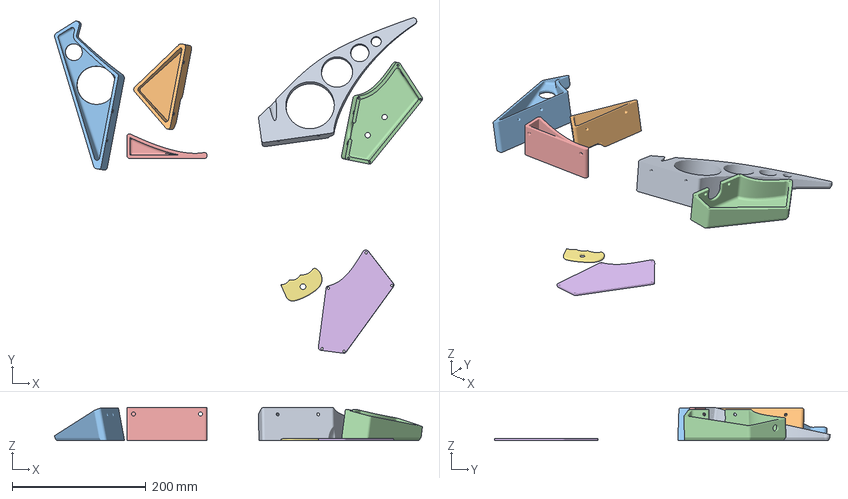
[picture p153: CAD file, 2025-07-07]
models/Wing Sets/Plastic X/Plastic X.3mf
550.2 x 501.8 x 50.0 mm
Top Right
Top Left
Bottom Left
Bottom Right - Front
Bottom Middle
Bottom Right - Back
TURBO 32 v17.stl
