spikeon/exoguitar/models/Neck/ExoGuitar - Neck - Bottom Left - Shouldered.step

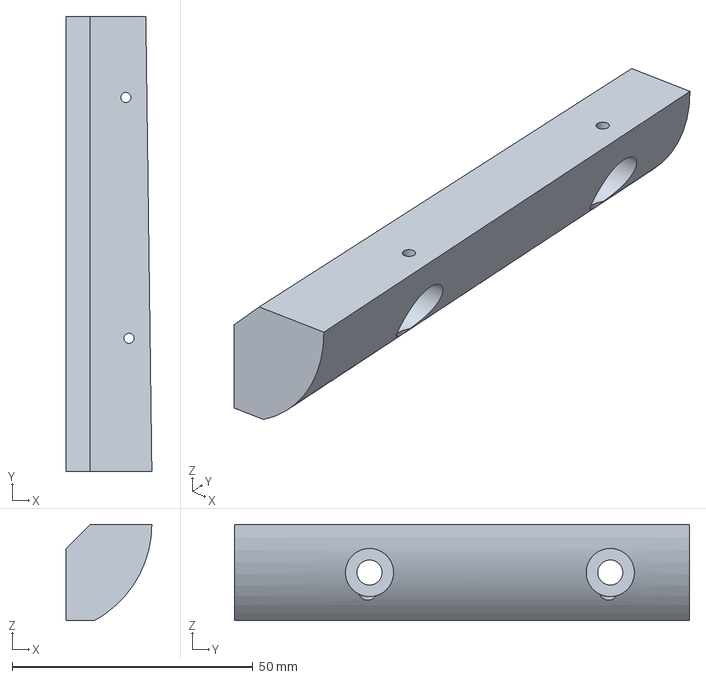
[picture p154: CAD file, 2025-01-11]
models/Neck/ExoGuitar - Neck - Bottom Left - Shouldered.step
17.8 x 94.5 x 20.0 mm
