spikeon/exoguitar/models/Wing Sets/Kumiko/Kumiko Wings - Right Wing - Bottom - Front - 1 Pot.dxf

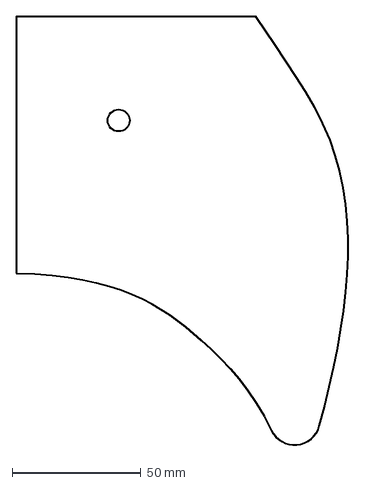
[picture p155: CAD file, 2025-06-17]
models/Wing Sets/Kumiko/Kumiko Wings - Right Wing - Bottom - Front - 1 Pot.dxf
134.1 x 166.7 mm
