spikeon/exoguitar/models/Strap/Clip Strap/ASSEMBLY.md

# Clip Strap Assembly

For the purposes of this assembly, please ignore any precieved lengths of the strap, it has been greatly reduced to allow for visualization of steps.

## Step 0: Prepare parts

Cut 2in Nylon strap to 1.5 meters.
Using a torch, singe the ends so they don't fray. 

## Step 1: Position end of Nylon Strap

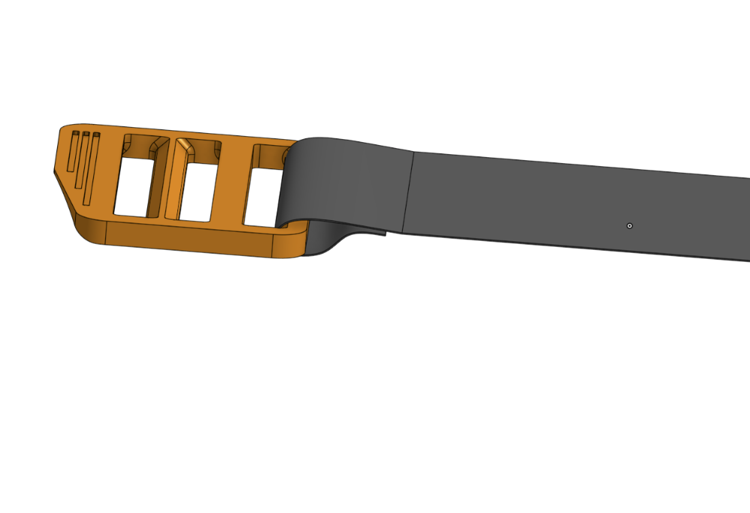
[picture p156: models/Strap/Clip Strap/exploded views/Step 1 - Position end A of nylon strap.png]


The strap should overlap itself 1-2 inches. 

## Step 2: Sew

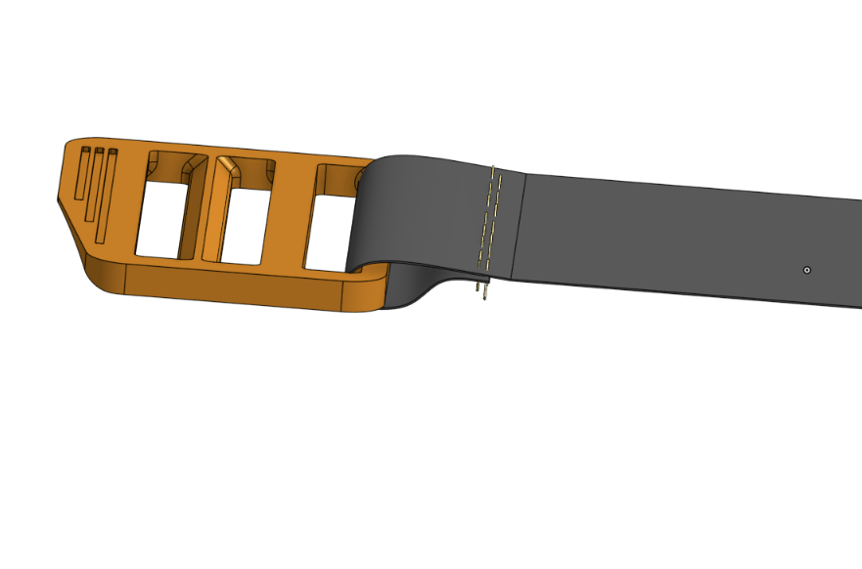
[picture p157: models/Strap/Clip Strap/exploded views/Step 2 - Sew.png]


Using a sewing machine and strong thread, sew a thick Zig-Zag line where the above image is marked, making sure to go forward all the way and then reverse all the way back. 

## Step 3: Weave Nylon Strap through parts

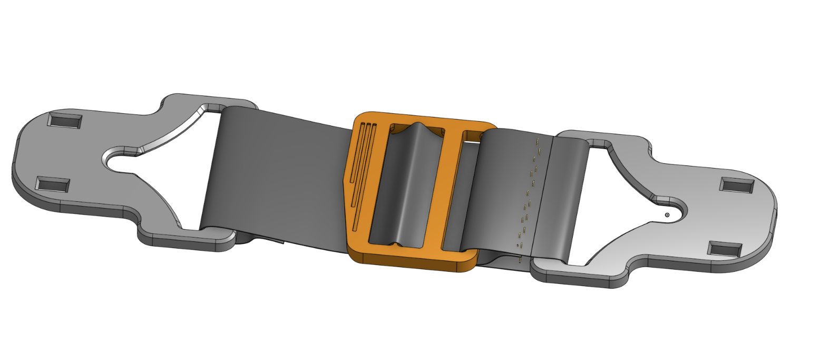
[picture p158: models/Strap/Clip Strap/exploded views/Step 3 - Weave Nylon strap through all parts.png]


## Step 4: Sew

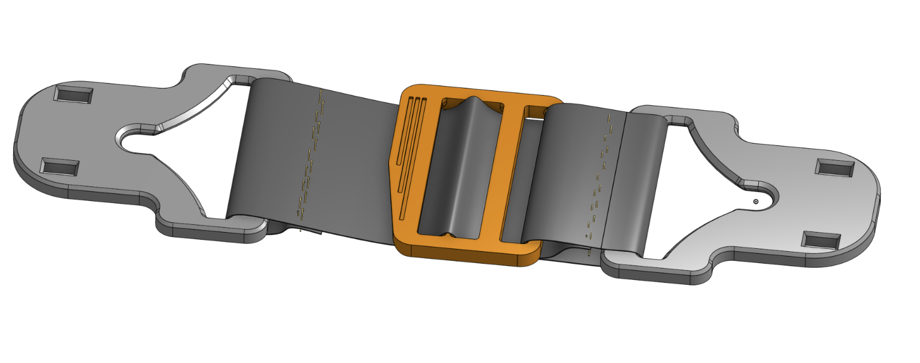
[picture p159: models/Strap/Clip Strap/exploded views/Step 4 - Sew.png]


Using a sewing machine and strong thread, sew a thick Zig-Zag line where the above image is marked, making sure to go forward all the way and then reverse all the way back. 

## Step 5: Add Hinges

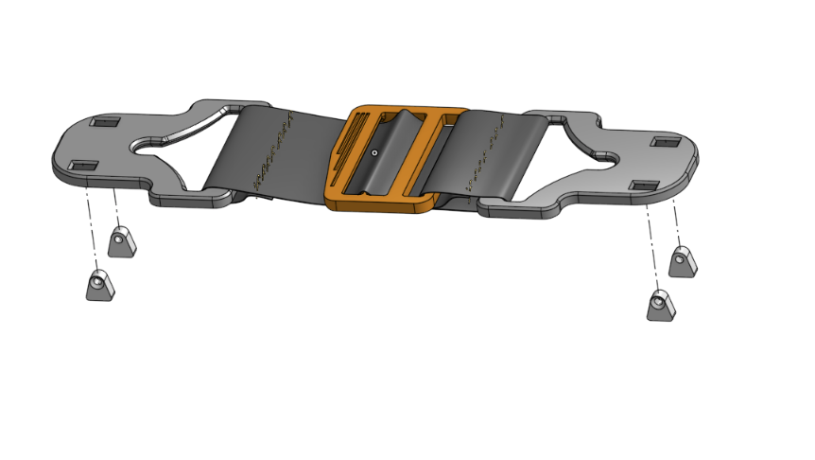
[picture p160: models/Strap/Clip Strap/exploded views/Step 5 - Add hinges.png]


## Step 6: Add Clips

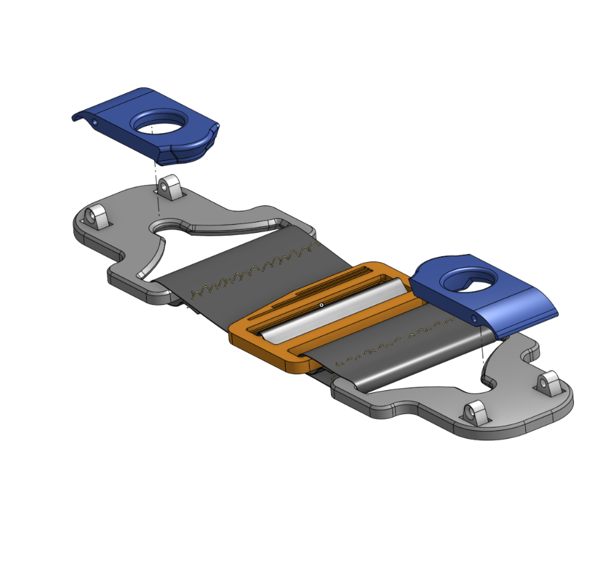
[picture p161: models/Strap/Clip Strap/exploded views/Step 6 - Add clips.png]


## Step 7: Add Pins

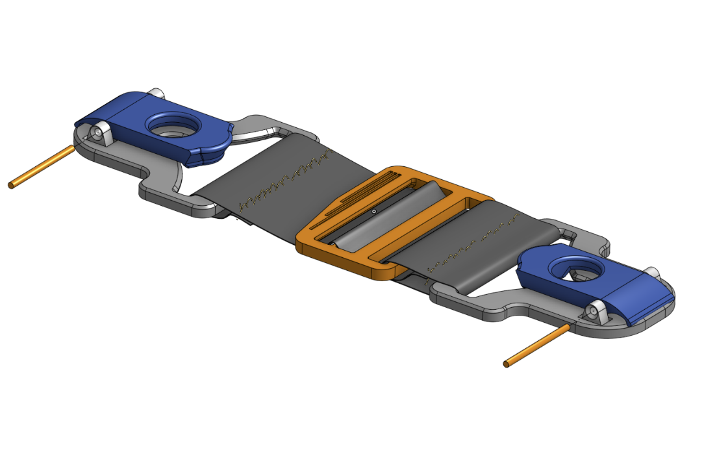
[picture p162: models/Strap/Clip Strap/exploded views/Step 7 - Add Pins (glue).png]


## Step 8: Glue

Put a drop of thick CA glue on the end of each pin to affix it to the hinge
