spikeon/exoguitar/models/Head/Headless v2/ASSEMBLY.md

# Assembly for Headless Head v2

1. Insert Heat Set Inserts
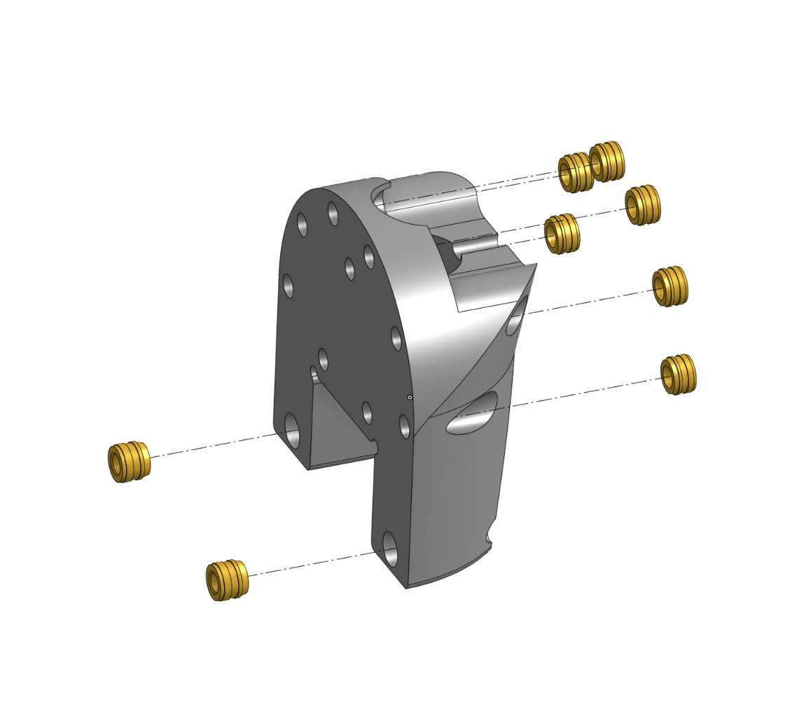
[picture p164: models/Head/Headless v2/exploded views/Step 1 - Insert Heat Inserts - Front.png]

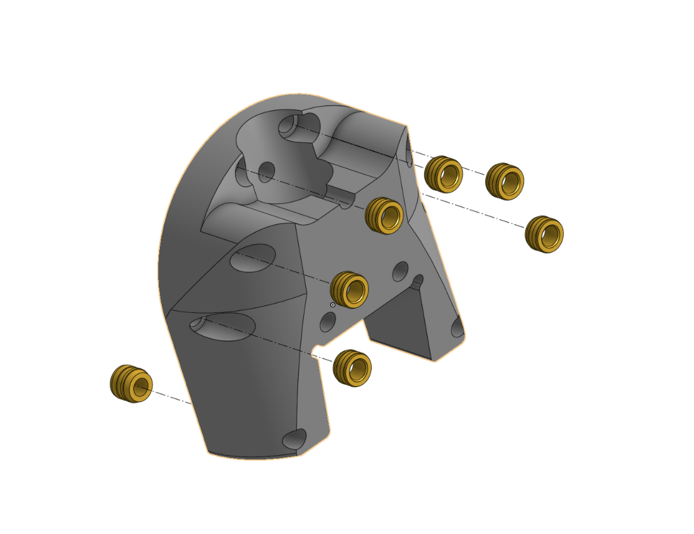
[picture p165: models/Head/Headless v2/exploded views/Step 1 - Insert Heat Inserts - Back.png]


2. Insert M3x16 Grub Screws
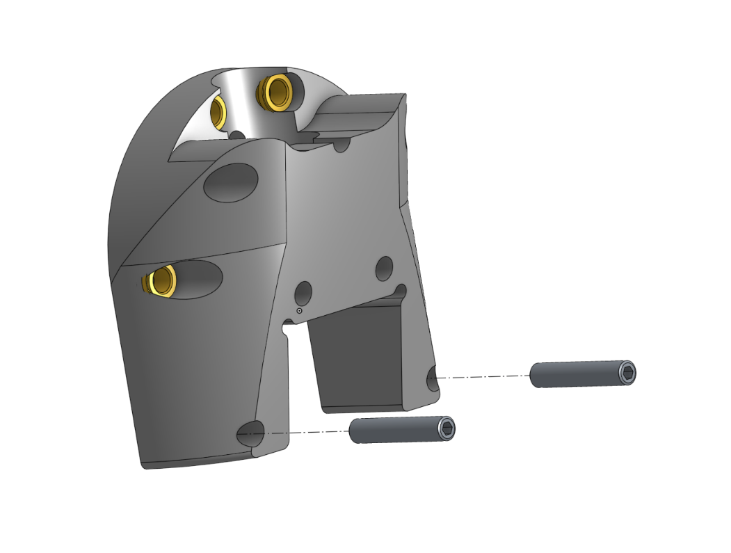
[picture p166: models/Head/Headless v2/exploded views/Step 2 - Insert Grub Screws.png]


3. Attach Face Plate
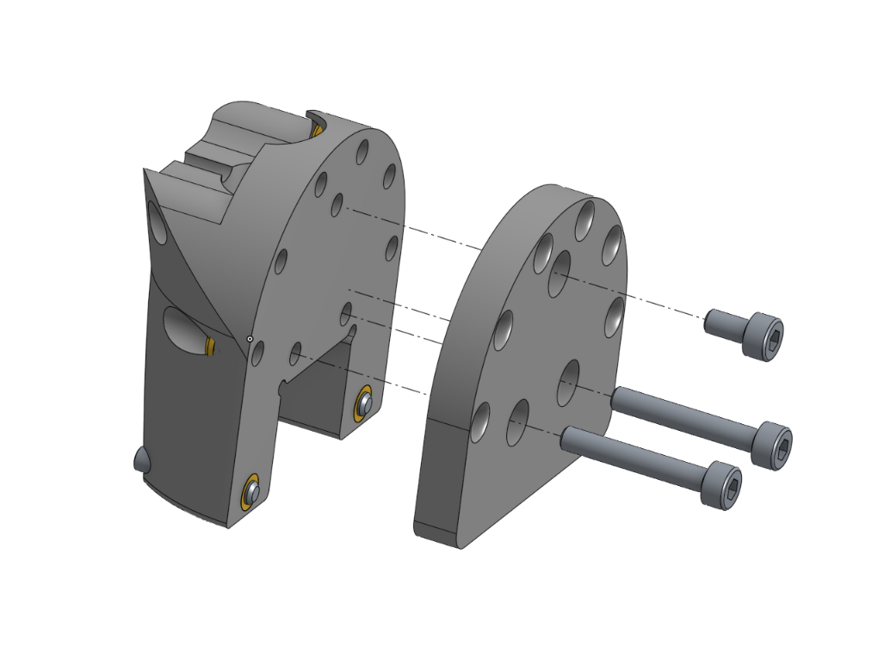
[picture p167: models/Head/Headless v2/exploded views/Step 3 - Attach Face Plate.png]
