spikeon/exoguitar/models/Back/Generator/ASSEMBLY.md

# Assembly for Generated Back 

1. Slide back pieces into 2020
