spikeon/exoguitar/models/Head/Arasaka/ASSEMBLY.md

# Assembly - Arasaka Head

While the images may show the Loop Head, the assembly is the same for both of these heads. 

## Step 1: Install Heat Set Inserts
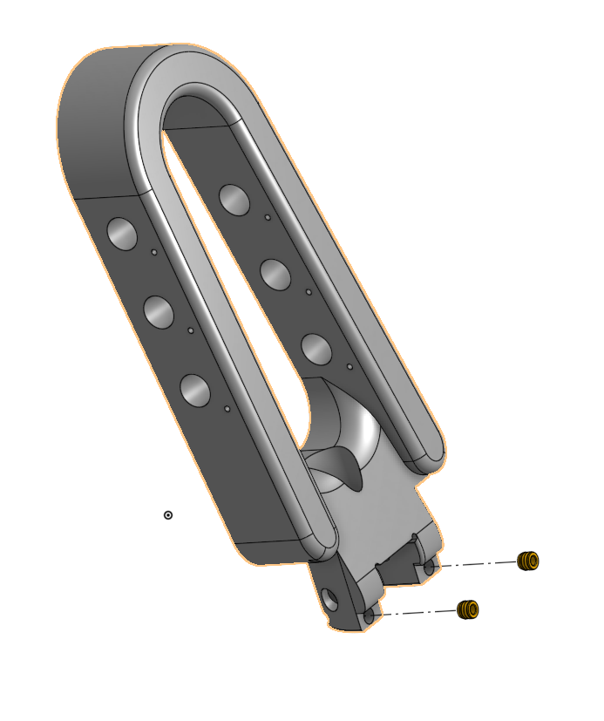
[picture p168: models/Head/Arasaka/exploded views/Step 1 - Insert Heat Set Inserts.png]


## Step 2: Install Adjustment Screws
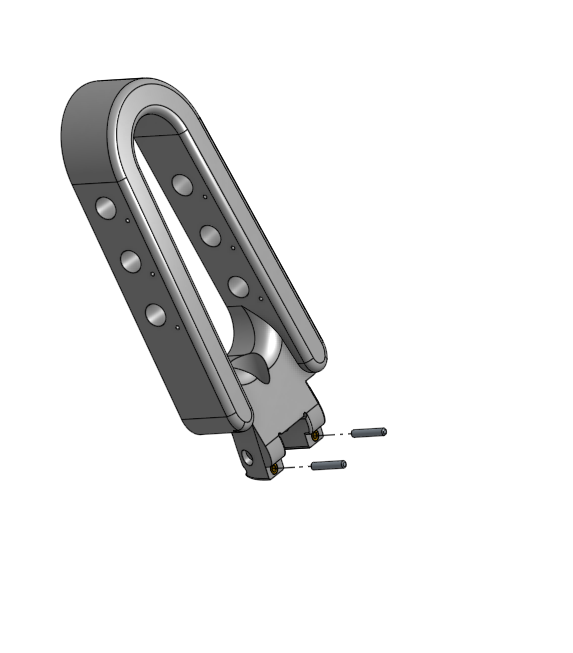
[picture p169: models/Head/Arasaka/exploded views/Step 2 - Insert adjustment screws.png]


# Step 3: Install Tuners
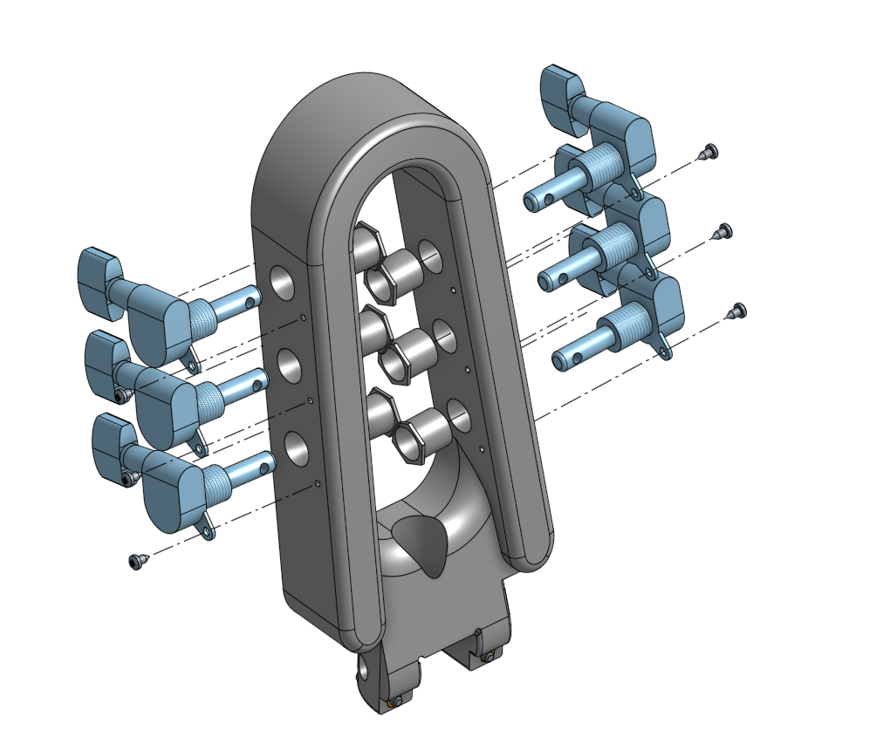
[picture p170: models/Head/Arasaka/exploded views/Step 3 - Install Tuners.png]
