spikeon/exoguitar/models/Bridge/Tune O' Matic - Single Plate/ASSEMBLY.md

# Assembly for Tune O' Matic Bridge Plate

## Step 1 - Insert M8 Heat Set Inserts
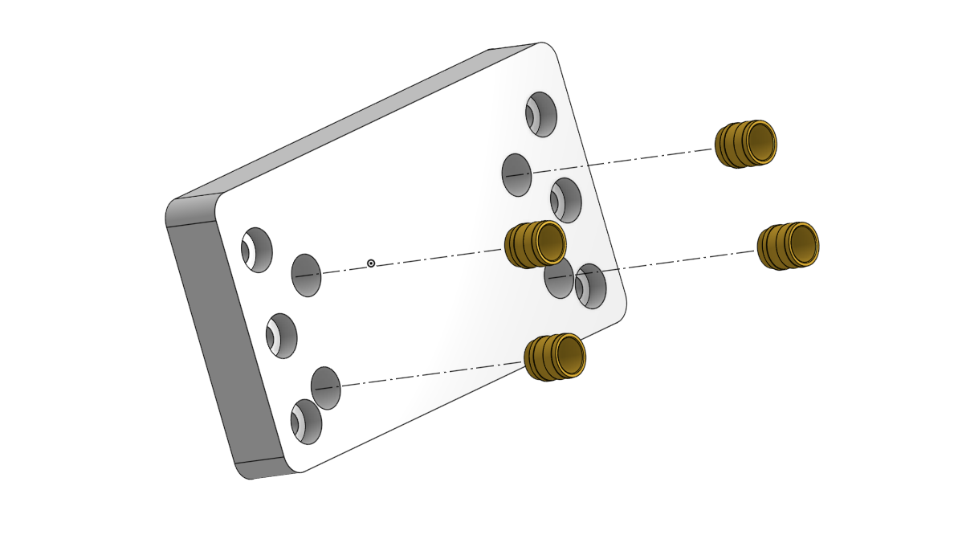
[picture p171: models/Bridge/Tune O' Matic - Single Plate/exploded views/Step 1 - Add Heat Set Inserts.png]


While you are doing this, Strip 2 inches of a wire and wrap that around the outside of one of the heat set inserts.  This will be your bridge ground wire. 

## Step 2 - Insert M5 Slide In Nuts to 2020 extrusion
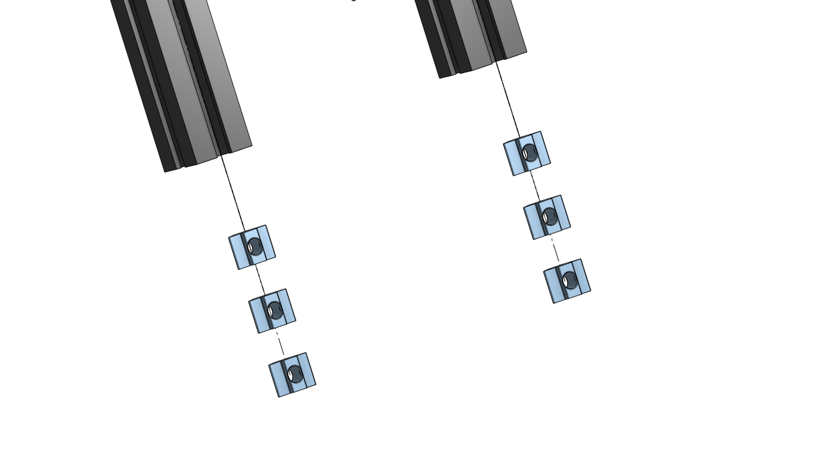
[picture p172: models/Bridge/Tune O' Matic - Single Plate/exploded views/Step 2 - Insert M5 2020 Slide In Nuts.png]


## Step 3 - Attach Bridge Plate to 2020 with M5x30 bolts
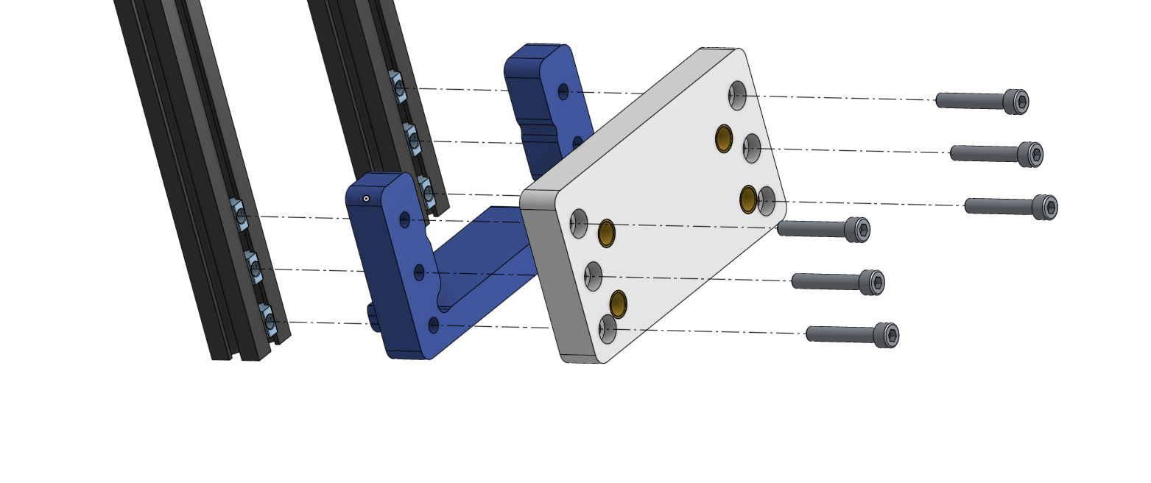
[picture p173: models/Bridge/Tune O' Matic - Single Plate/exploded views/Step 3- Attach bridge to 2020 .png]


## Step 4 - Attach Tune O' Matic 
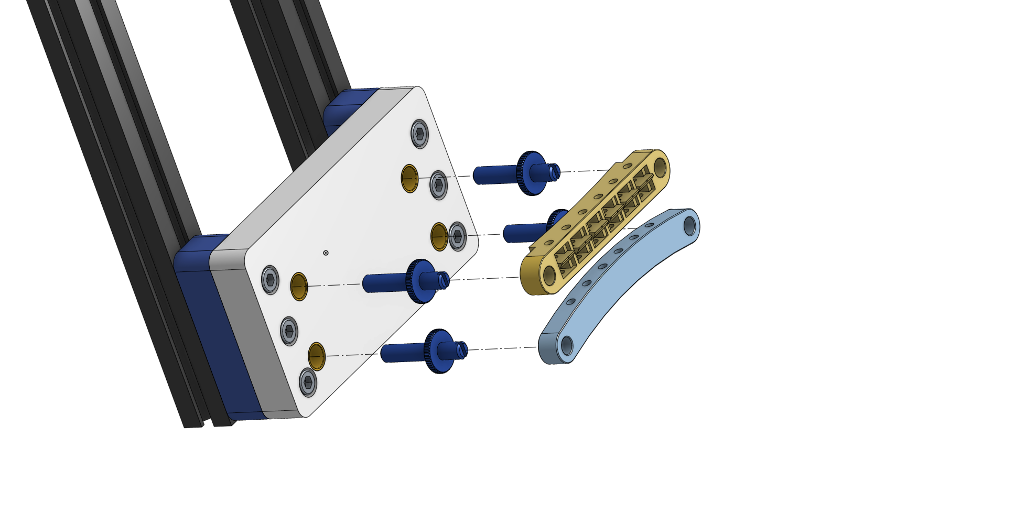
[picture p174: models/Bridge/Tune O' Matic - Single Plate/exploded views/Step 4 - Attach Tune O' Matic.png]
