spikeon/exoguitar/models/Bridge/OVSAL Headless Bridge Plate/ASSEMBLY.md

# Assembly for OVSAL Headless Bridge Plate
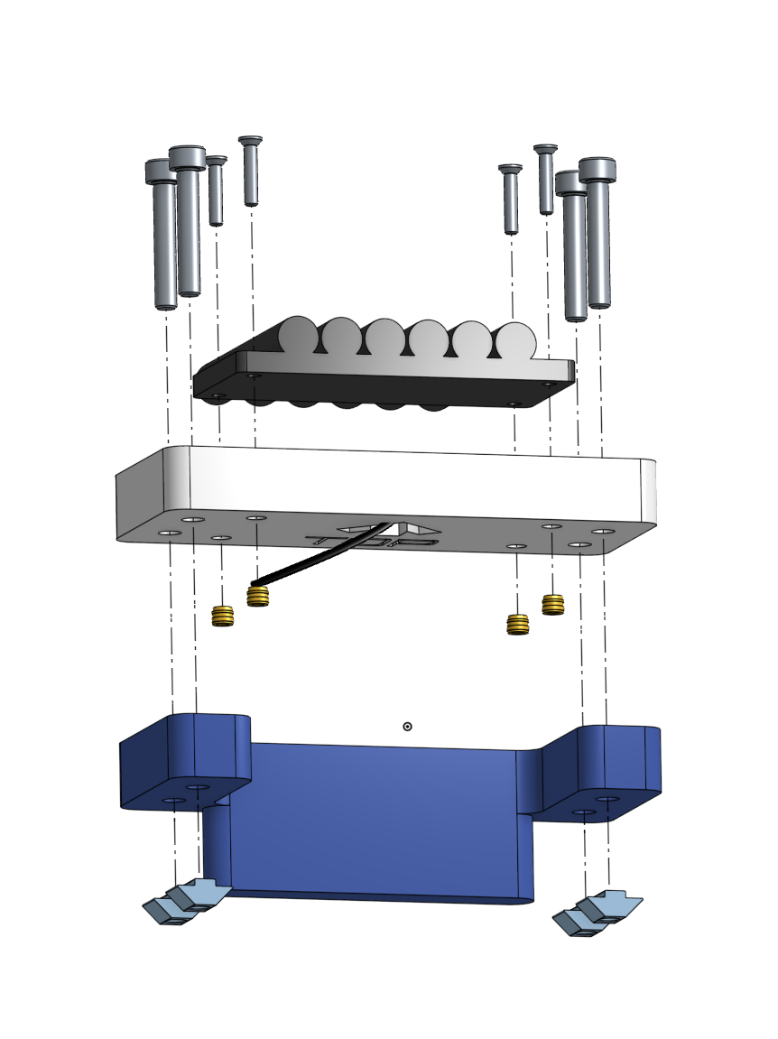
[picture p175: models/Bridge/OVSAL Headless Bridge Plate/exploded views/Full Assembly.png]


# Step 1: Insert Heat Set Inserts

# Step 2: Insert Slide In Nuts to 2020

# Step 3: Secure Skirt and Plate to 2020 with M5x30 Screws

# Step 4: Run ground wire through arrow shaped hole

# Step 5: Secure Bridge to plate with M3x16 FHCS
Make sure that the wire is pinched between the plate and the bridge
