spikeon/exoguitar/models/Head/Headless - String Lock/ASSEMBLY.md

# Assembly for Head - Headless - String Lock
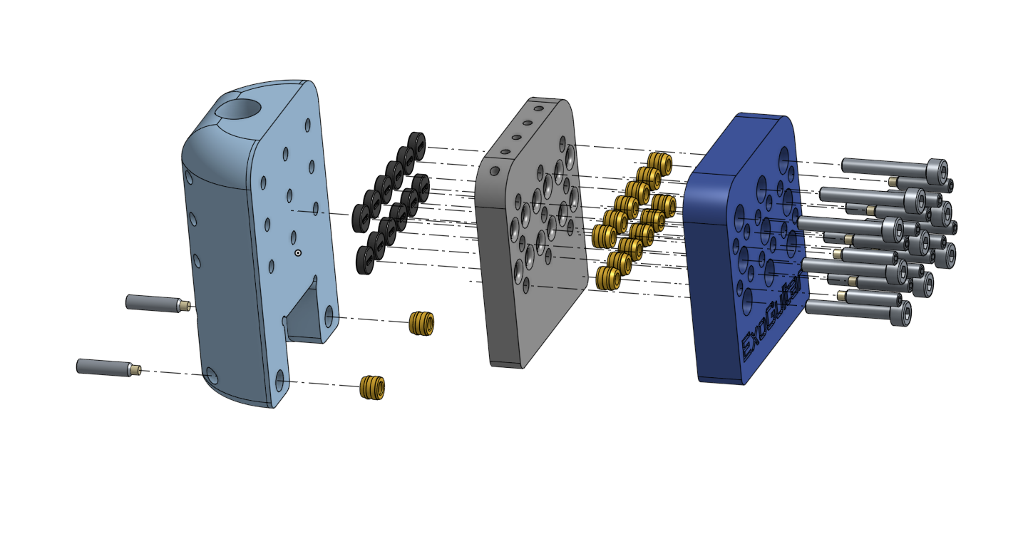
[picture p176: models/Head/Headless - String Lock/exploded views/Full Assembly.png]
Full Assembly


## Step 1: Insert Heat Set Inserts

### Step 1a: Insert Back Heat Set Inserts

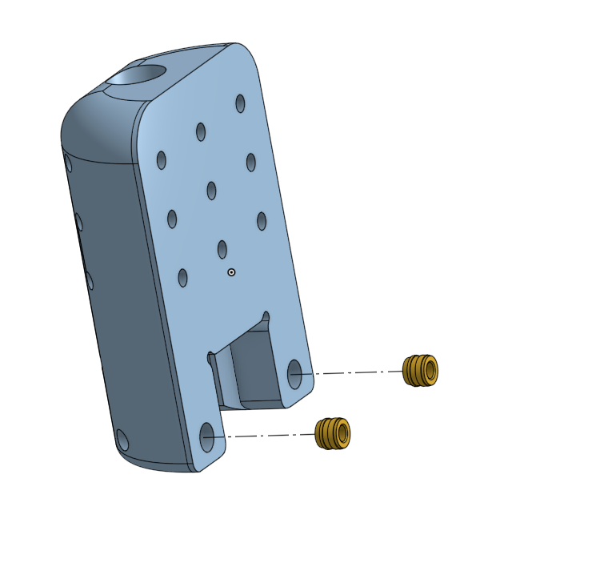
[picture p177: models/Head/Headless - String Lock/exploded views/Step 1a - Insert Back Heat Set Inserts.png]


### Step 1b: Insert Face Heat Set Inserts

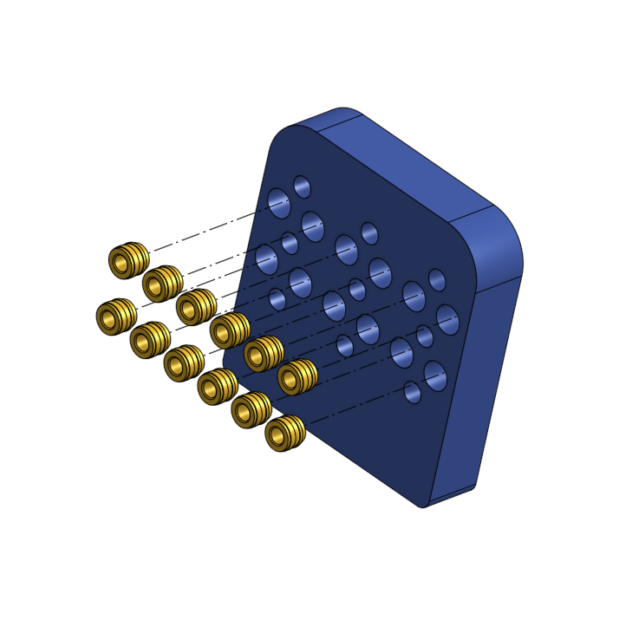
[picture p178: models/Head/Headless - String Lock/exploded views/Step 1b - Inserts Face Heat Set Inserts.png]


## Step 2: Insert Magnets / Rubber pads

You can use either 6x2 magnets or 6x2mm rubber feet.  

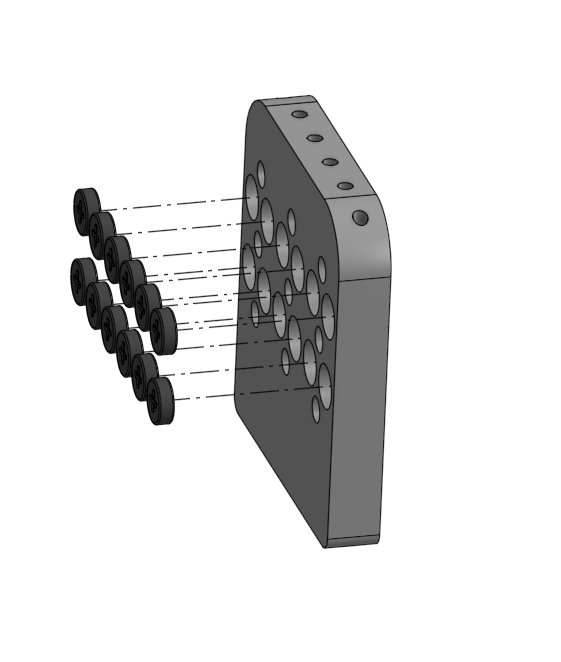
[picture p179: models/Head/Headless - String Lock/exploded views/Step 2 - Insert Magnets.png]


## Step 3: Combine Assemblies

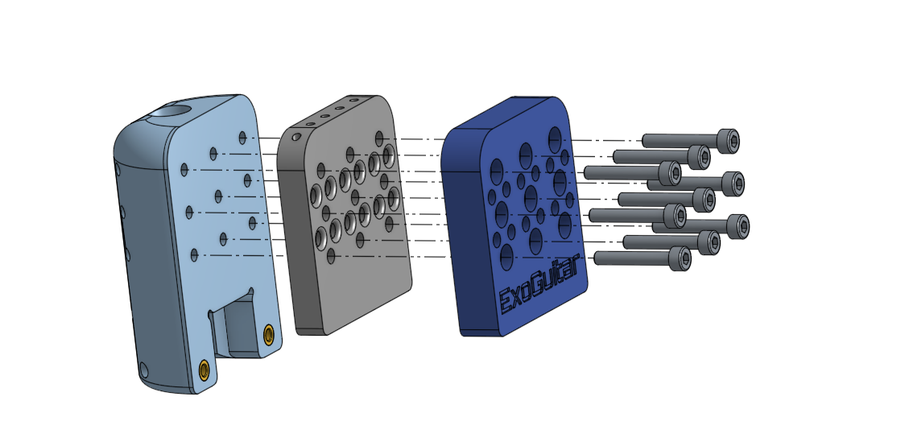
[picture p180: models/Head/Headless - String Lock/exploded views/Step 3 - Combine Assemblies.png]


## Step 4: Insert Set Screws

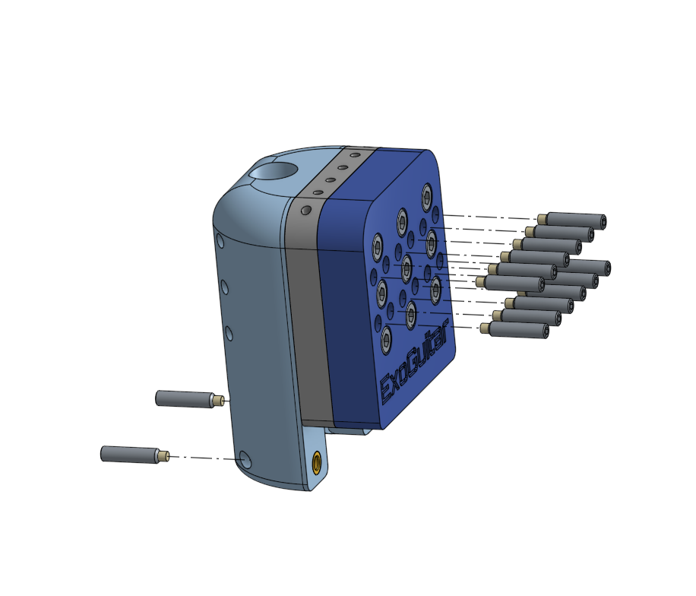
[picture p181: models/Head/Headless - String Lock/exploded views/Step 4 - Insert Set Screws.png]


## Step 5: Attach to Neck

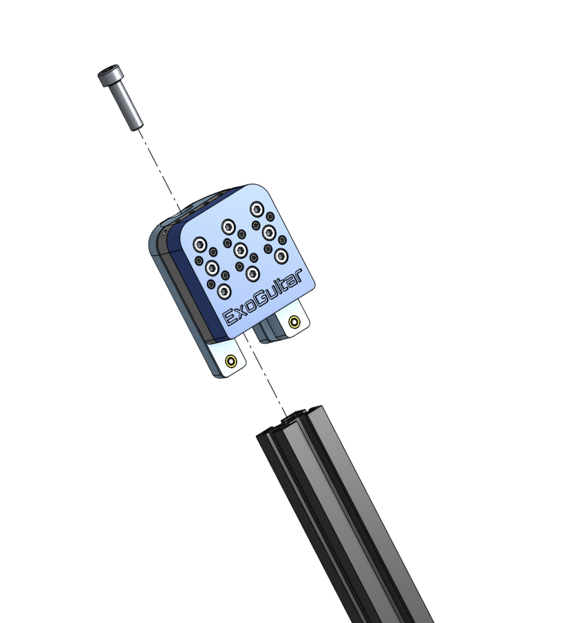
[picture p182: models/Head/Headless - String Lock/exploded views/Step 5 - Attach to Neck.png]
