spikeon/exoguitar/models/Head/Headless - OVSAL String Lock/ASSEMBLY.md

# Assembly for Head - Headless - OVSAL String Lock

## Step 1 - Insert Heat Set Inserts
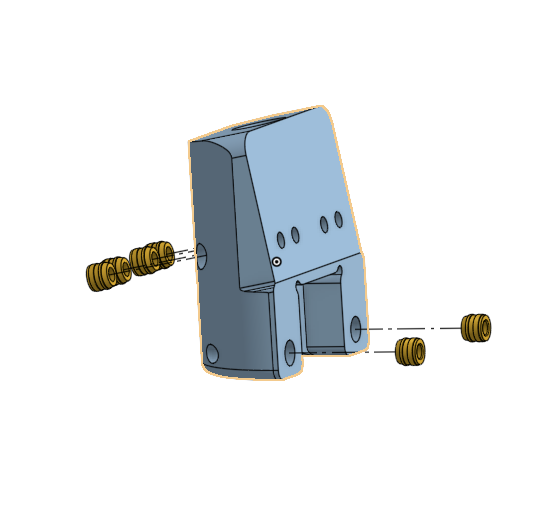
[picture p183: models/Head/Headless - OVSAL String Lock/exploded views/Step 1 - Insert Heat Set Inserts.png]


## Step 2 - Attach OVSAL String Lock
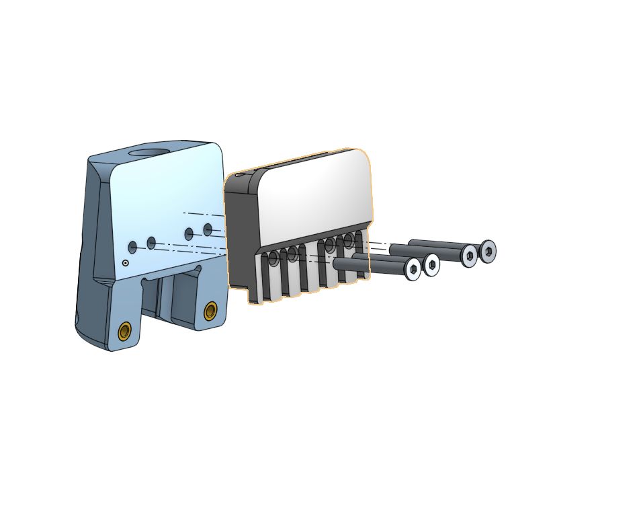
[picture p184: models/Head/Headless - OVSAL String Lock/exploded views/Step 2 - Attach OSVAL String Lock.png]


## Step 3 - Attach assembly to neck 2020
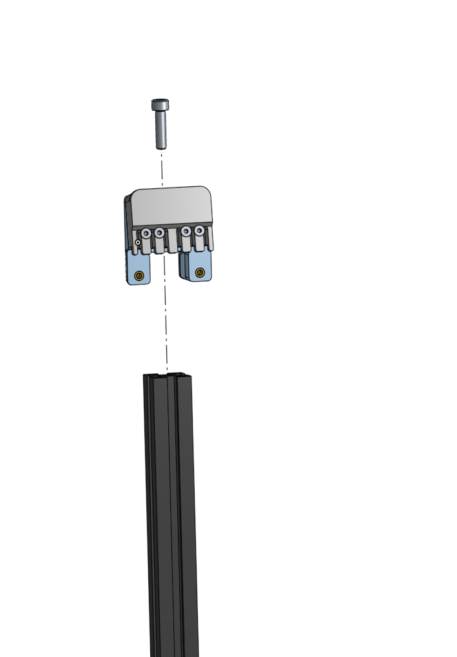
[picture p185: models/Head/Headless - OVSAL String Lock/exploded views/Step 3 - Attach assembly to neck 2020.png]
