spikeon/exoguitar/models/Wing Sets/Kumiko/ASSEMBLY.md

# Assembly - Kumiko Wings

This one involves more glue than the rest

## Step 1: Glue face plates to Front Panels

## Step 2: Proceed as if this was any other wing set

Mount to 2020 using M5x10 screws and slide-in nuts.  
Glue pieces together as you connect them to the 2020. 
Put in all electronics.
Make sure all electronics work (because you're gluing this shut)

## Step 3: Glue on back panels
