spikeon/exoguitar/models/Face Plates/Acoustic/OPTIONAL_ASSEMBLY_PIEZO.md

# Optional Assembly Step: Piezo Mic

If you are building an acoustic and you don't want to install pezio mics, your build is now complete!

If you ARE building an acoustic and you want to install Pezio Mics, remove the back panel and place the microphones on the inside of the face plate.  

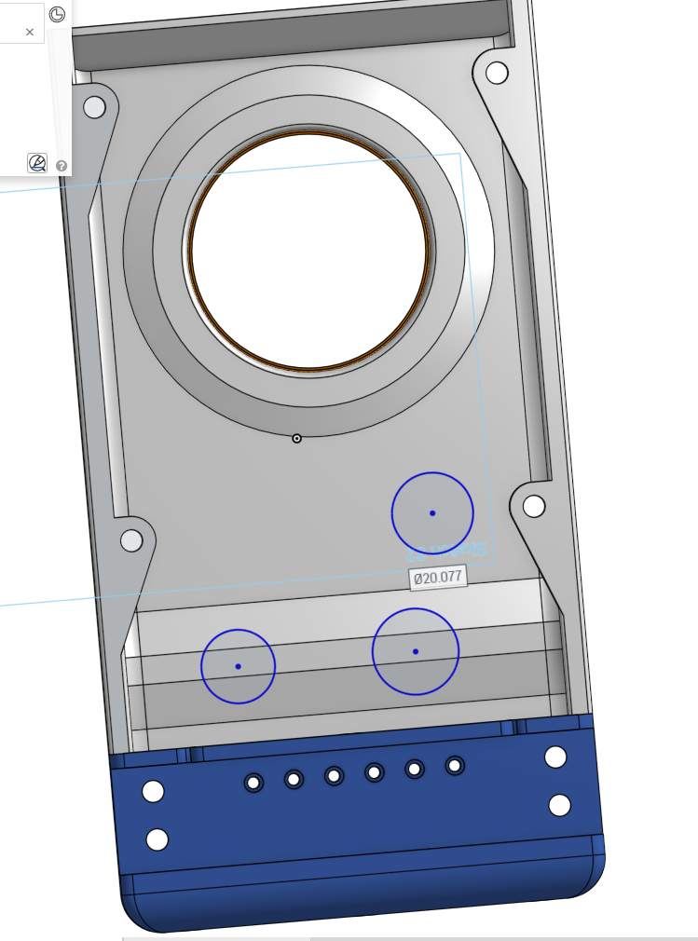
[picture p186: models/Face Plates/Acoustic/exploded views/Pezio Locations.png]
These are some suggested locations:  

This will give you Highs, Lows, and taps (if you tap on the guitar body).  

If you don't want taps, you can just put all three of them in a line across the thick part.  I have found that a single Mic in the center also works pretty well. ~~~~
