spikeon/exoguitar/models/Head/Classical/ASSEMBLY.md

# Assembly

After printing, make sure you clean out ALL support material.  The smallest amount in the gearboxes can cause interference, the tollerances are very tight.  

## Step 1: Put in Heat Set Inserts

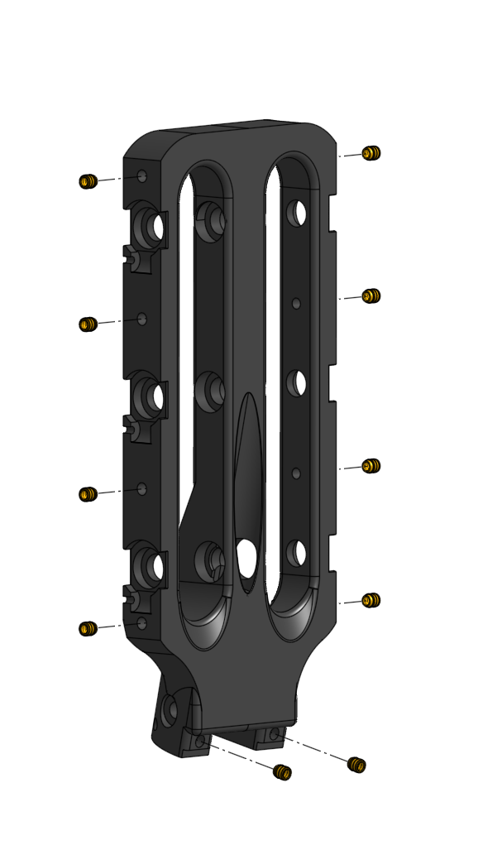
[picture p187: models/Head/Classical/exploded views/Step 1 - Heat Set Inserts.png]
Heat Inserts - Exploded View


## Step 2: Put in Bearings

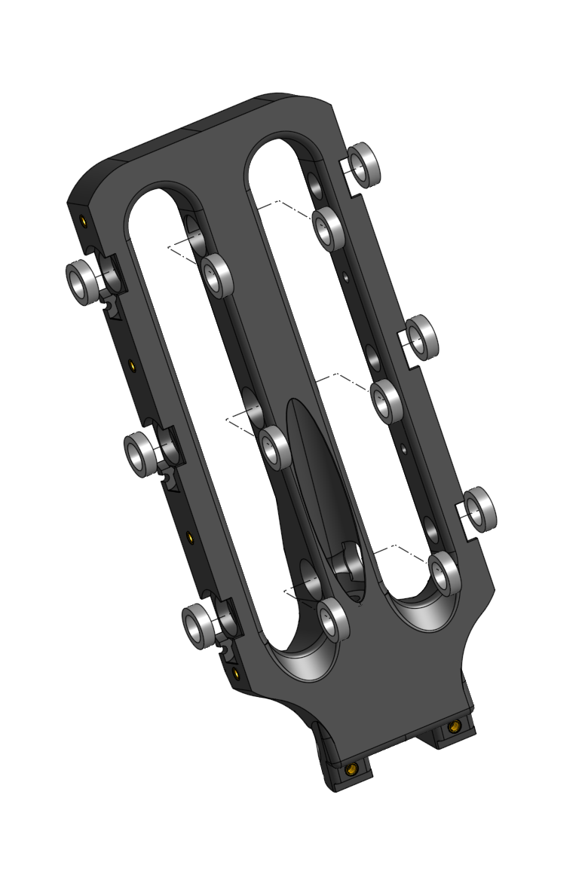
[picture p188: models/Head/Classical/exploded views/Step 2 - Bearings.png]
Bearings - Exploded View


## Step 3: Assemble 6 Tensioners

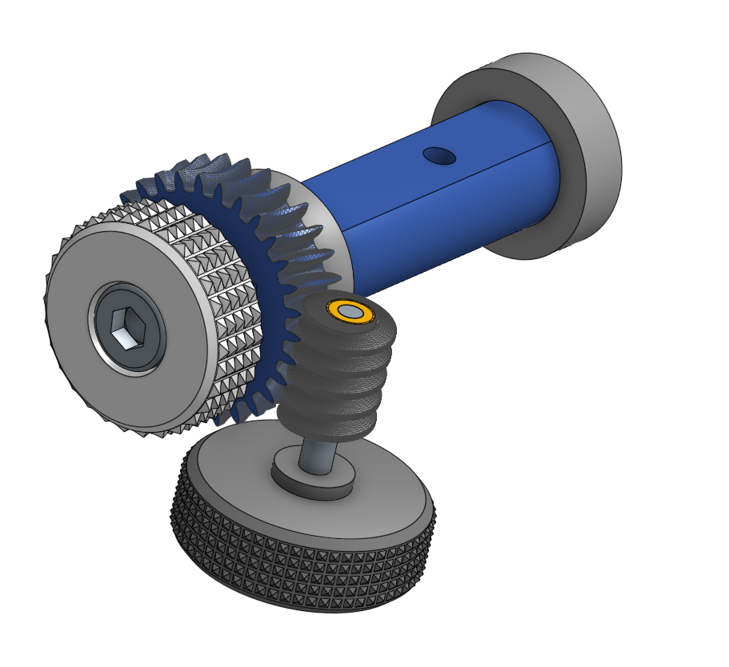
[picture p189: models/Head/Classical/exploded views/Tensioner Assembled.png]
tensioners


#### Step 3a: Cut TPU Filament Stubs

Cut 6x 5mm long pieces of TPU filament.  A model for a jig to cut these to size easily is included [here](./ExoGuitar%20-%20TPU%20Cutting%20Jig.3mf)

#### Step 3b: Assemble Shaft 

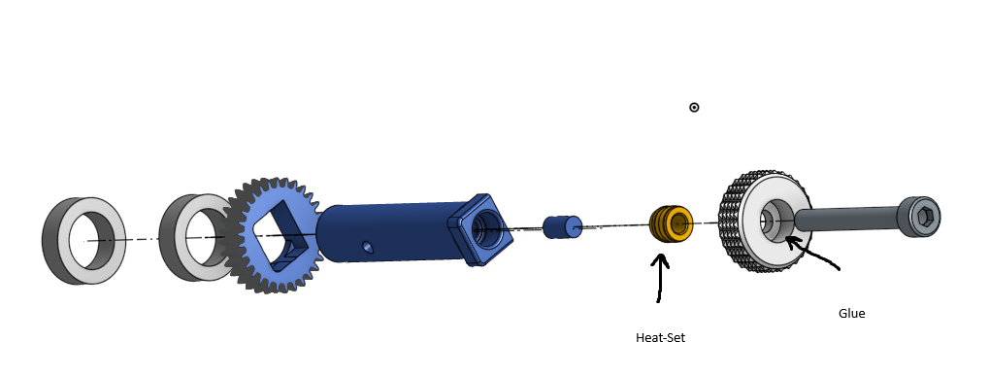
[picture p190: models/Head/Classical/exploded views/Step 3a - Tensioner Shaft x6.png]
Shaft


Note that the TPU filament piece is inserted BEFORE the heat set insert is installed. 

#### Step 3e: Prep Worm gear
 
Using a 3/32 drill bit, remove 3mm of material from one side of the worm gear hole.  Then install the heat set insert into that hole.  BE CAREFUL and make sure you go in straight and that you don't melt the gear teeth. 

#### Step 3f: Assemble Knob

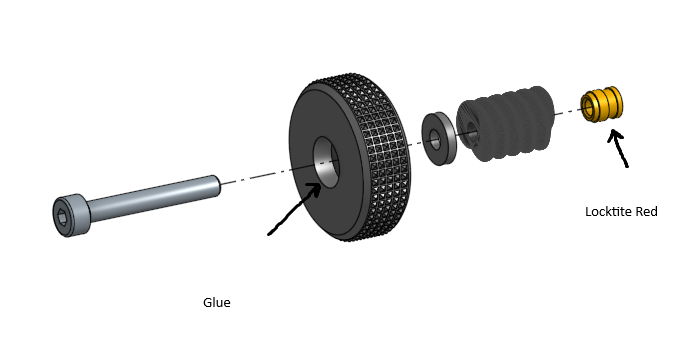
[picture p191: models/Head/Classical/exploded views/Step 3b - Tensioner Knob x6.png]


The screw should go right up to the end of the worm gear but not stick out of it.   
Use locktite or super glue to lock the screw into the gear.  I recommend Locktite Red

#### Step 3r: Install Tensioners

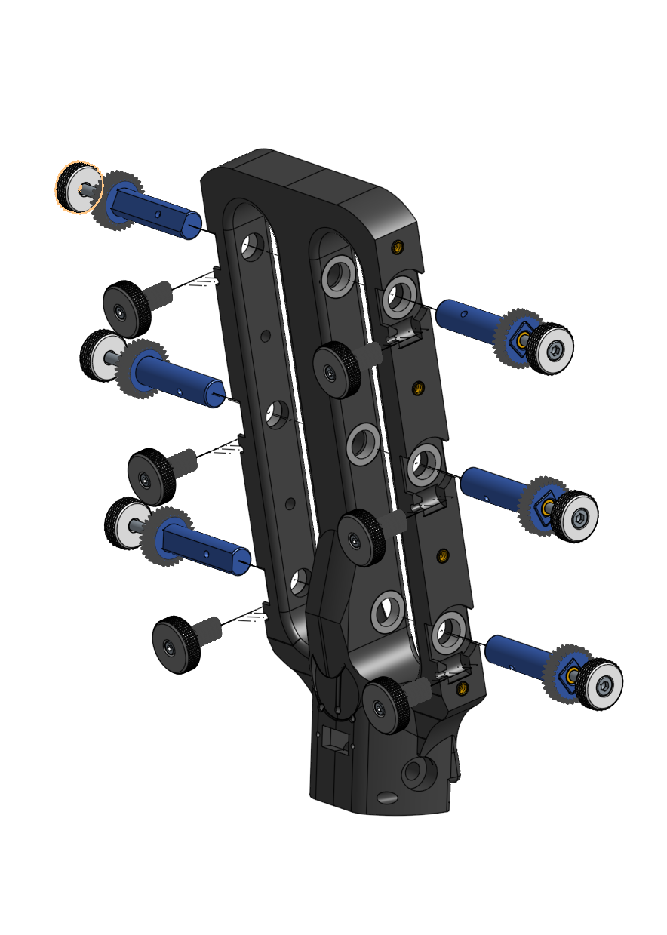
[picture p192: models/Head/Classical/exploded views/Step 3c - Tensioners.png]
Tension


#### Step 3f: Lubricate gears with Synthetic Grease

## Step 4: Install Side Panels

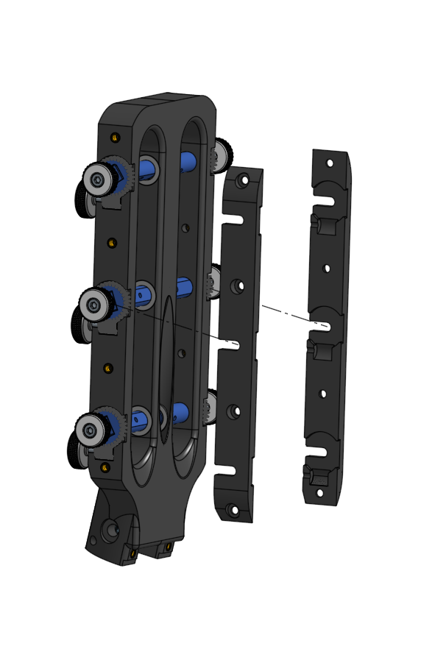
[picture p193: models/Head/Classical/exploded views/Step 4 - Side Panels.png]
Side Panels


## Step 5: Put in all the screws!

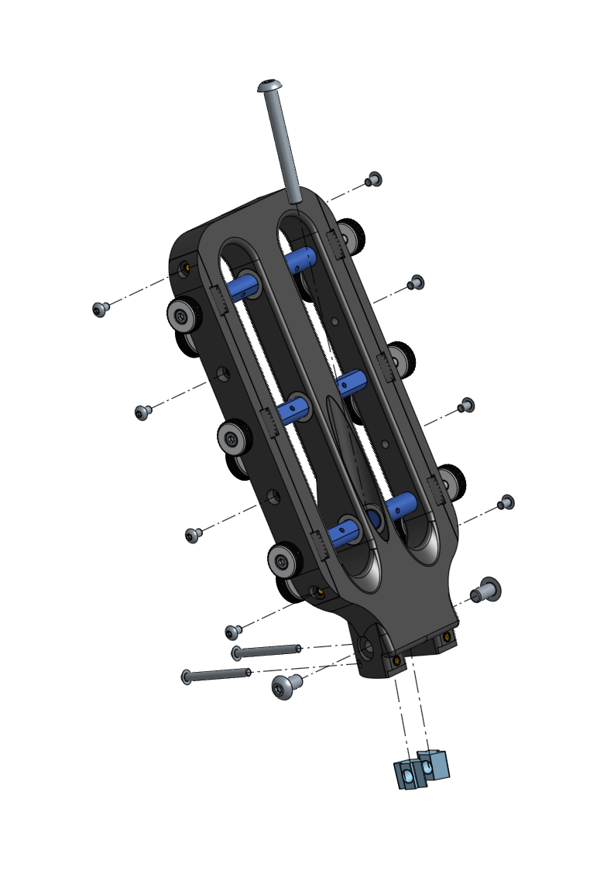
[picture p194: models/Head/Classical/exploded views/Step 5 - Final Screws.png]
Screw Screw Screw
