spikeon/exoguitar/models/Head/Explorer/ASSEMBLY.md

# Assembly for Explorer Head

Note: Views feature the shape of the Jack's Son's Head, but the instructions remain the same. 

## Step 1: Install Heat Set Inserts
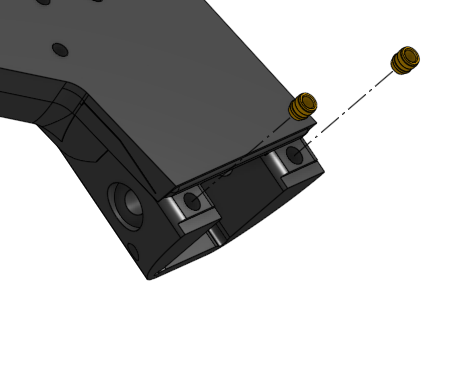
[picture p195: models/Head/Explorer/exploded views/Step 1b - Insert Nut Heat Insert.png]
Nut Inserts


## Step 2: Attach Head to Neck using M5x45
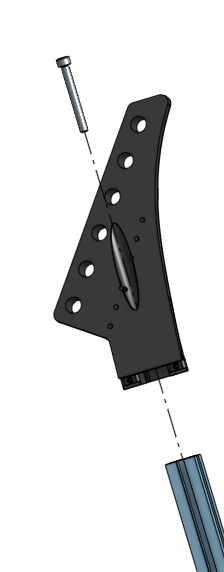
[picture p196: models/Head/Explorer/exploded views/Step 2 - Attach M5x45.png]


## Step 3: Insert Slide In Nuts
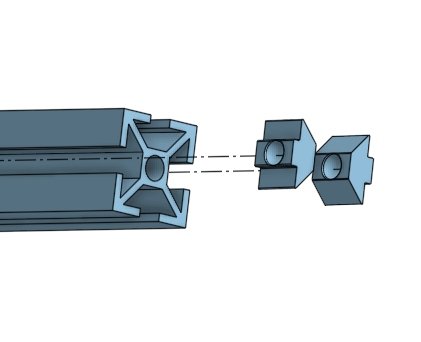
[picture p197: models/Head/Explorer/exploded views/Step 3 - Insert Slide In Nuts.png]


## Step 4: Insert Screws
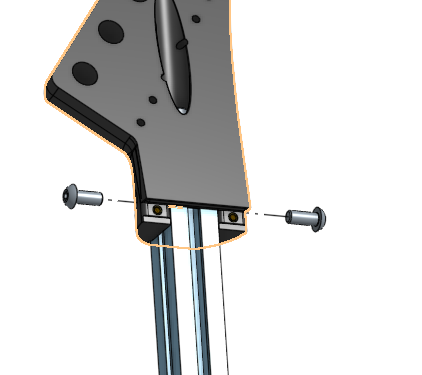
[picture p198: models/Head/Explorer/exploded views/Step 4 - Insert Screws.png]


## Step 5: Glue in Plug
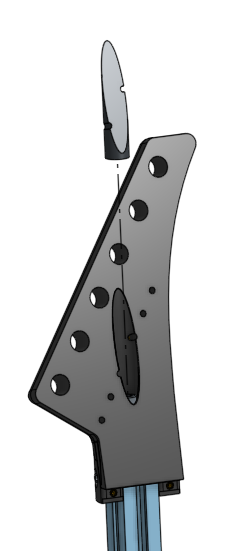
[picture p199: models/Head/Explorer/exploded views/Step 5 - Glue In Plug.png]


## Step 6: Install Tuners
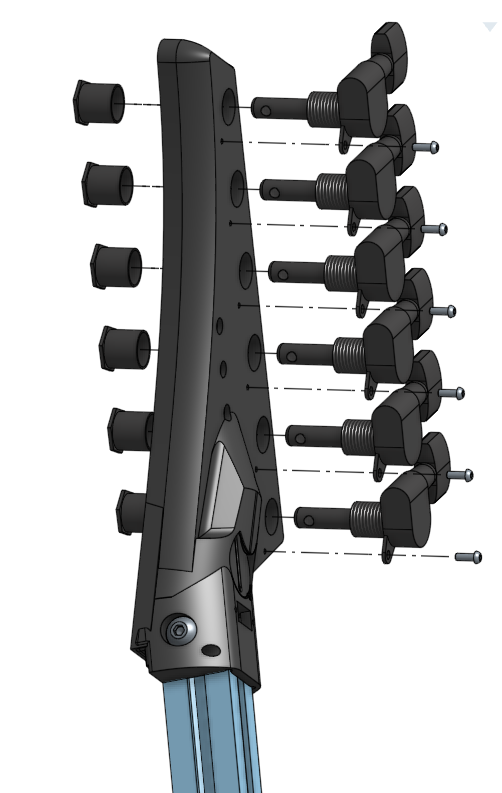
[picture p200: models/Head/Explorer/exploded views/Step 6 - Install Tuners.png]
