spikeon/exoguitar/models/Head/King Paul/ASSEMBLY.md

# Assembly

Note: Instructions feature the shape of the Arrow Head, but the instructions remain the same. 

## Step 1: Put in Heat Set Inserts
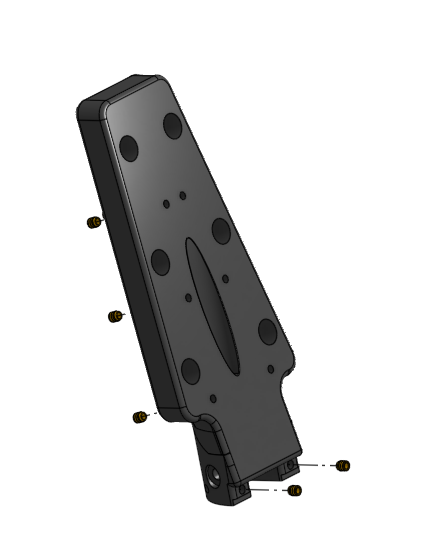
[picture p201: models/Head/King Paul/exploded views/Step 1 - Insert Heat Set Inserts Front.png]
Heat Inserts - Front Exploded View


## Step 2: Put in Tuning Pegs
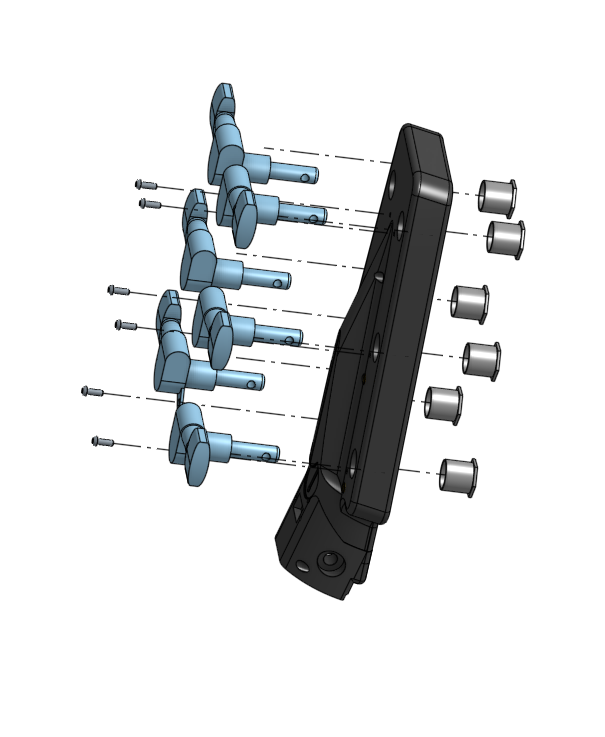
[picture p202: models/Head/King Paul/exploded views/Step 2 - Insert Tuning Pegs.png]
Bearings - Exploded View


## Step 4: Put in Nut Adjusment Screws
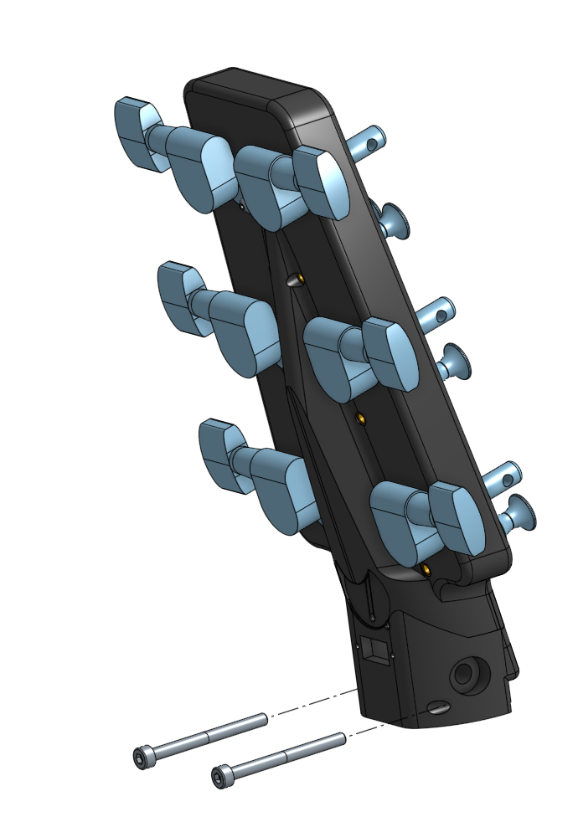
[picture p203: models/Head/King Paul/exploded views/Step 4 - Install Nut Adjusters.png]
Nut Adjusters


## Step 5: Attach 2020
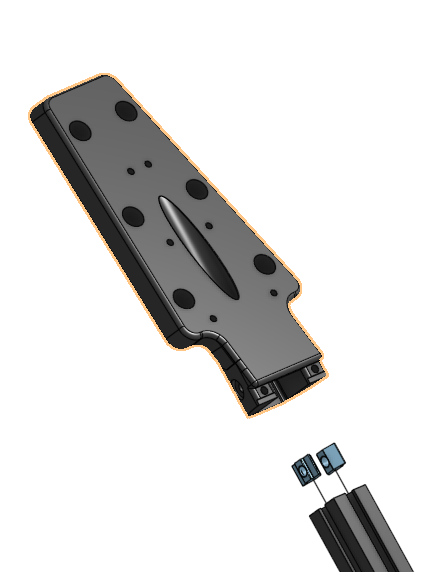
[picture p204: models/Head/King Paul/exploded views/Step 5 - Attach 2020.png]


## Step 6: Attach 2020 Screws
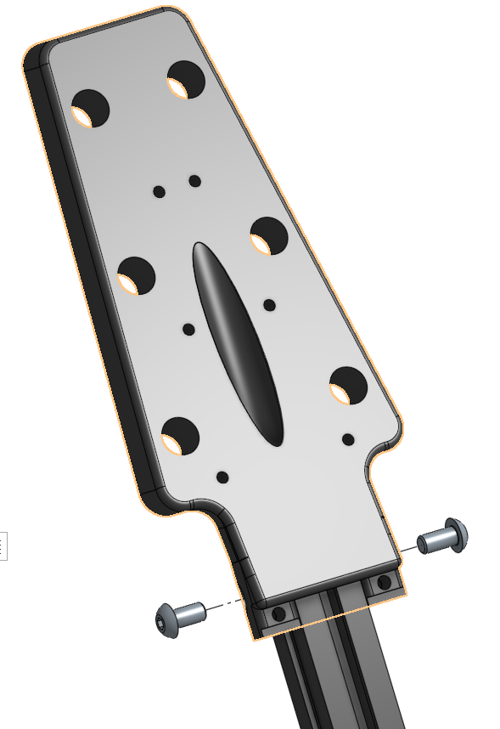
[picture p205: models/Head/King Paul/exploded views/Step 6 - Install 2020 Screws.png]
2020 Screws


## Step 7: Put in M5x45 Screws
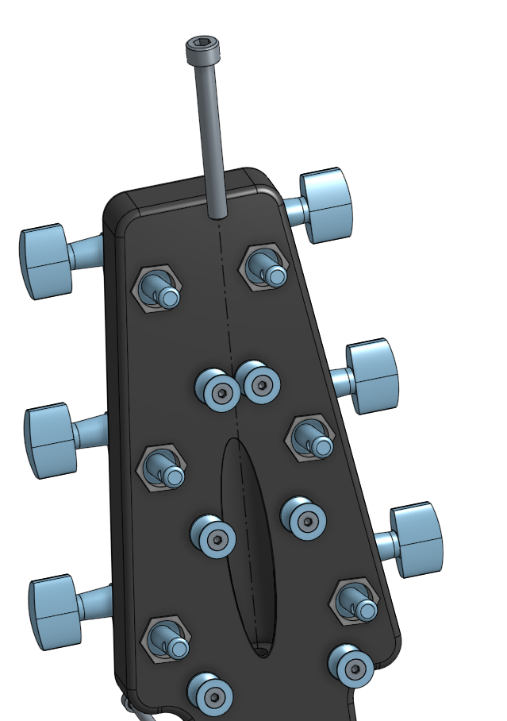
[picture p206: models/Head/King Paul/exploded views/Step 7 - Attach M5x45 Screw.png]
M5x45
