spikeon/exoguitar/models/Wing Sets/Jack's Son/ASSEMBLY.md

# Assembly

## Step 1: Combine Wing Segments

Use glue and M3 screws to combine the pieces of the wings together

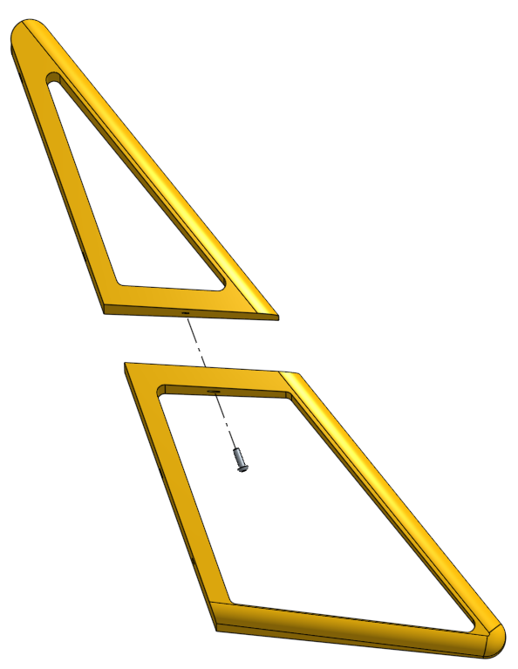
[picture p207: models/Wing Sets/Jack's Son/exploded views/Step 1a - Merge Left WIng.png]


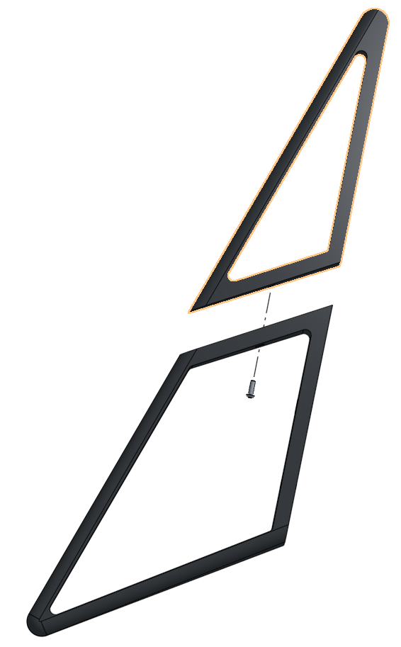
[picture p208: models/Wing Sets/Jack's Son/exploded views/Step 1b - Merge Right Wing.png]


## Step 2: Install Heat Set Inserts

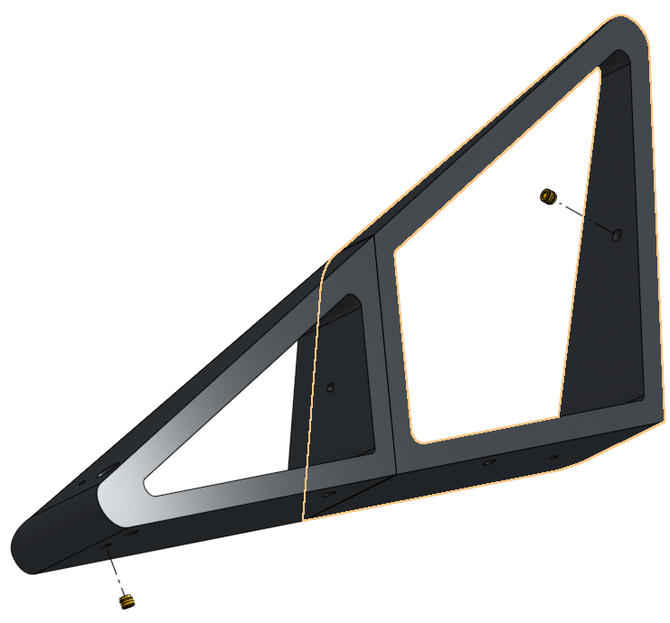
[picture p209: models/Wing Sets/Jack's Son/exploded views/Step 2 - Install Heat Set Inserts.png]


## Step 3: Attach Wings to Body

### Step 3a: Insert Heat Inserts

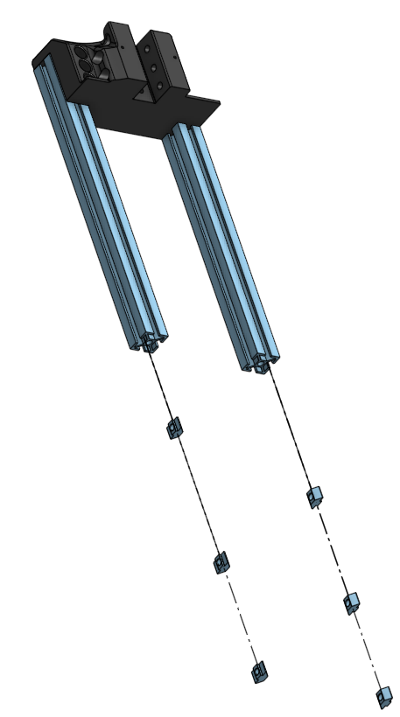
[picture p210: models/Wing Sets/Jack's Son/exploded views/Step 3a - Insert Slide In Nuts.png]


### Step 3b: Attach Left Wing

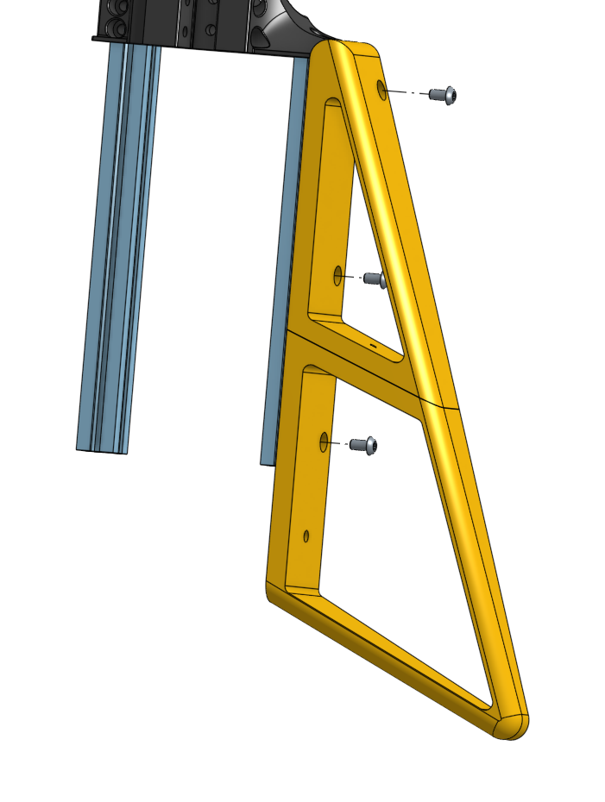
[picture p211: models/Wing Sets/Jack's Son/exploded views/Step 3b - Attach Left Wing.png]


### Step 3c: Attach Wing Middle

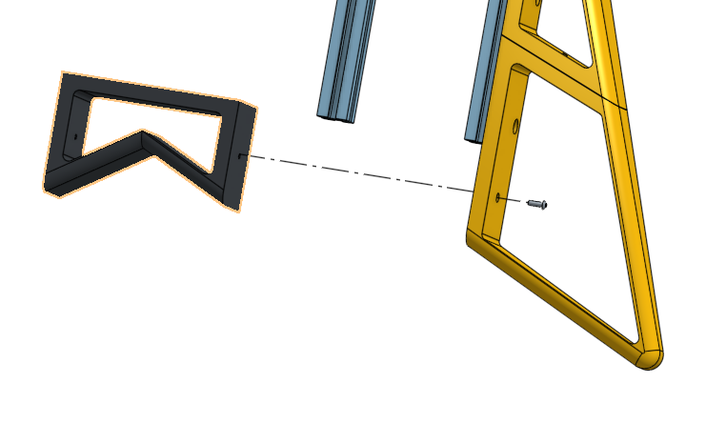
[picture p212: models/Wing Sets/Jack's Son/exploded views/Step 3c - Attach Wing Center Piece.png]


### Step 3d: Attach Right Wing

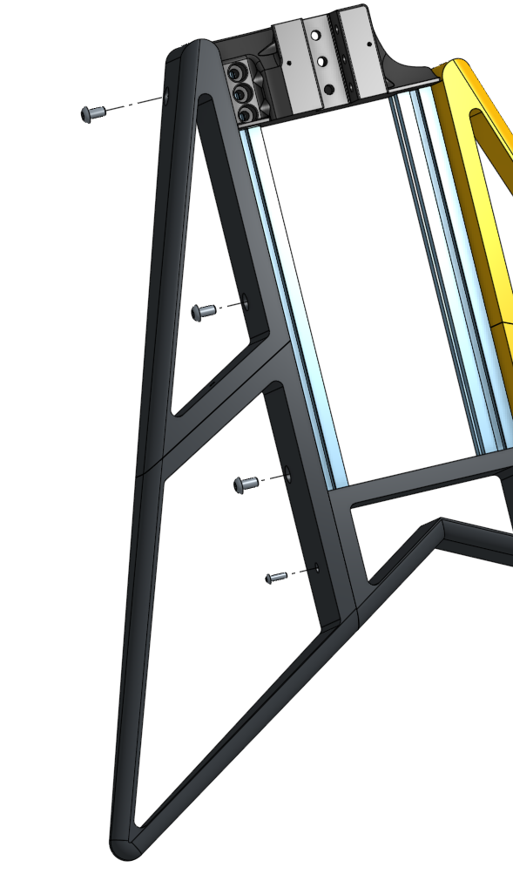
[picture p213: models/Wing Sets/Jack's Son/exploded views/Step 3d - Attach Right Wing.png]


### Step 4: Install Magnets

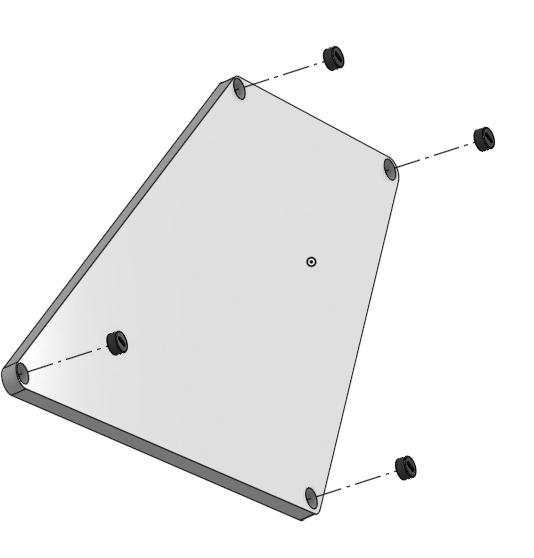
[picture p214: models/Wing Sets/Jack's Son/exploded views/Step 4a - Insert Panel Magnets.png]


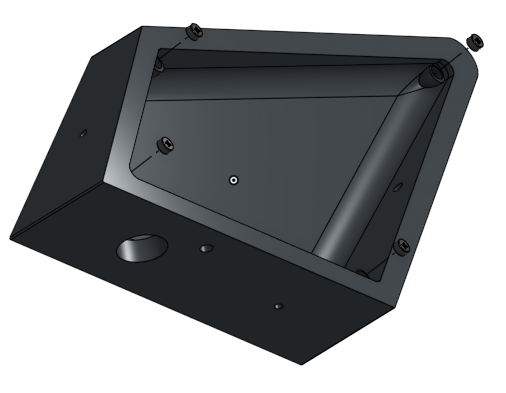
[picture p215: models/Wing Sets/Jack's Son/exploded views/Step 4b - Insert Wing Magnets.png]
