spikeon/exoguitar/models/Head/Jack's Son/ASSEMBLY.md

# Assembly for Jack's Son's Head

## Step 1: Install Heat Set Inserts
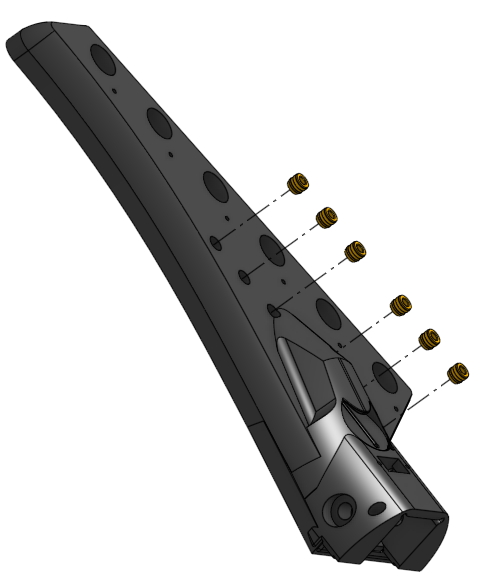
[picture p216: models/Head/Jack's Son/exploded views/Step 1a - Insert Tree Heat Inserts.png]
Tree Inserts

Nut Inserts

## Step 2: Attach Head to Neck using M5x45


## Step 3: Insert Slide In Nuts


## Step 4: Insert Screws


## Step 5: Glue in Plug


## Step 6: Install Tuners


## Step 7: Install Trees
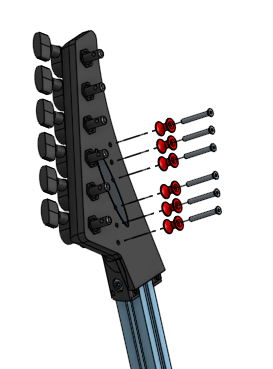
[picture p217: models/Head/Jack's Son/exploded views/Step 7 - Install Trees.png]
