spikeon/exoguitar/models/Bridge/Headless Bridge Plate/ASSEMBLY.md

# Assembly

## Step 1: Insert Heat Set Inserts

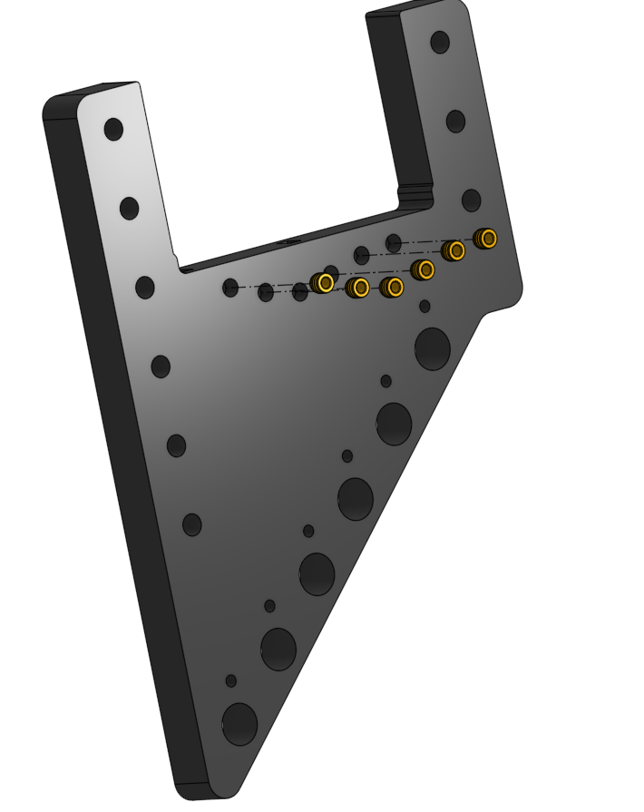
[picture p218: models/Bridge/Headless Bridge Plate/exploded views/Step 1a - Insert Tree Heat Set Inserts.png]


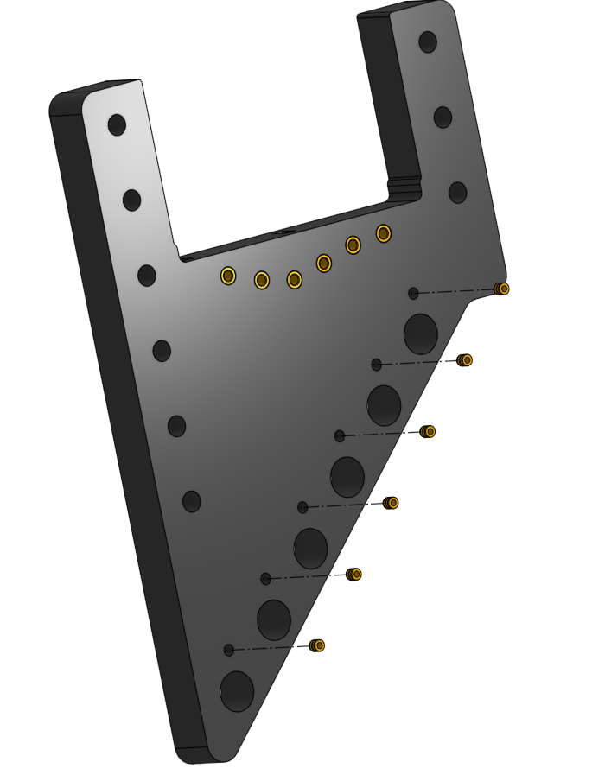
[picture p219: models/Bridge/Headless Bridge Plate/exploded views/Step 1b - Insert Tuner Heat Set Inserts.png]


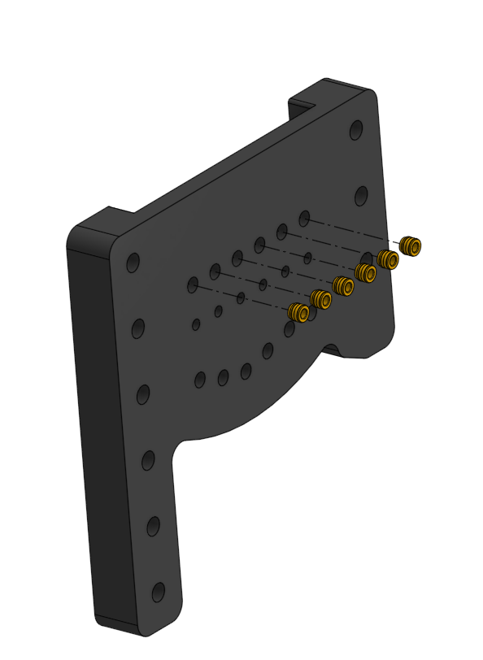
[picture p220: models/Bridge/Headless Bridge Plate/exploded views/Step 1c - Insert Bridge Heat Set Inserts.png]


## Step 2: Install Tuners

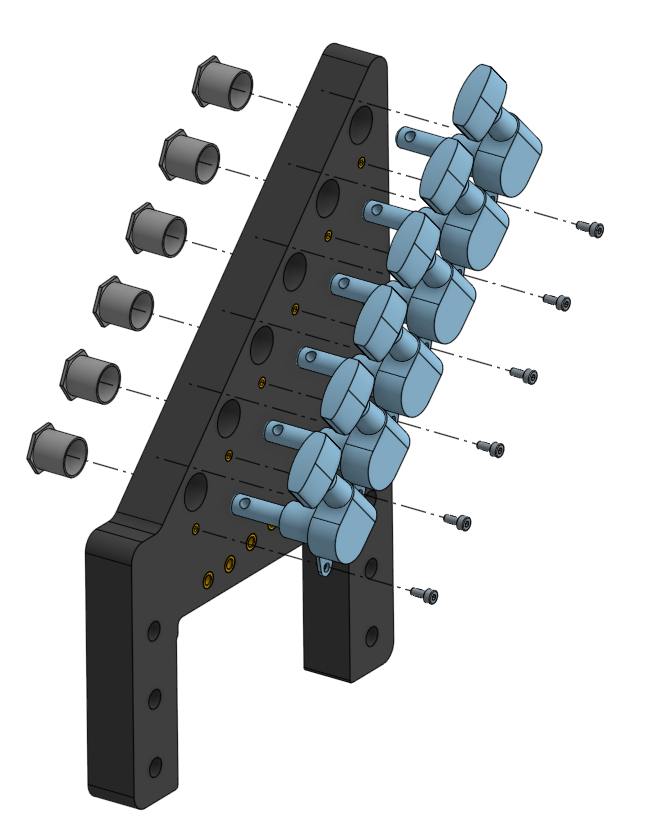
[picture p221: models/Bridge/Headless Bridge Plate/exploded views/Step 2 - Install Tuners.png]


## Step 3: Install Carbon Fiber Rods

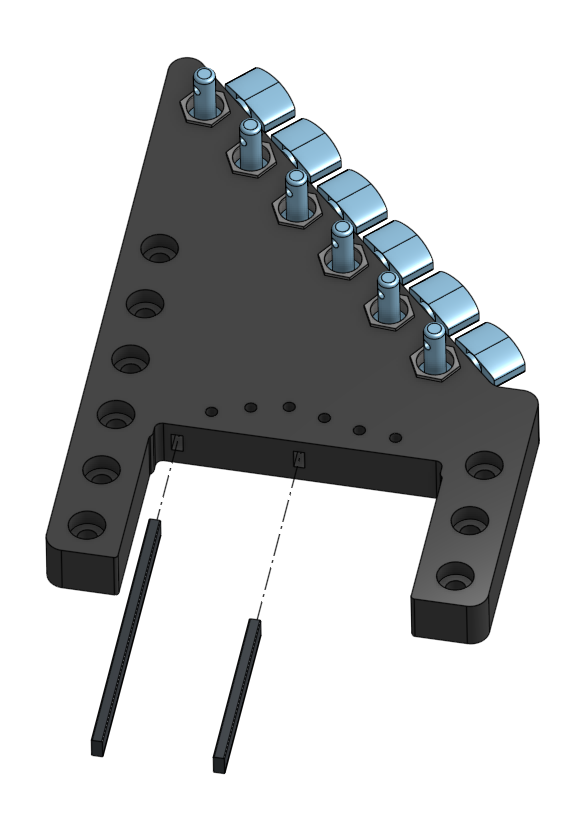
[picture p222: models/Bridge/Headless Bridge Plate/exploded views/Step 3 - Install Carbon Fiber Rods.png]


## Step 4: Install Trees

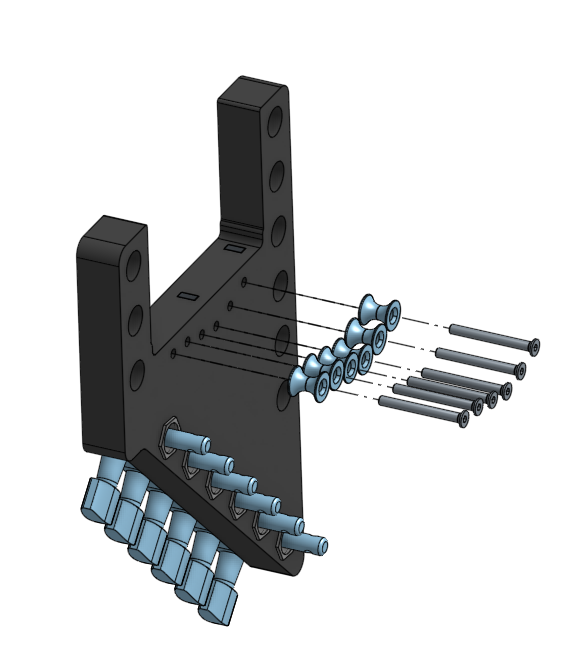
[picture p223: models/Bridge/Headless Bridge Plate/exploded views/Step 4 - Install Trees.png]


## Step 5: Install Bearing Bridge Assembly

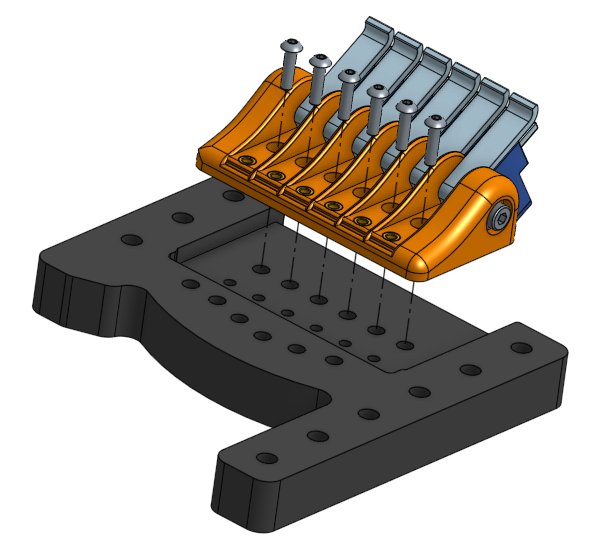
[picture p224: models/Bridge/Headless Bridge Plate/exploded views/Step 5 - Install Bearing Bridge.png]


## Step 6: Install Vertical Adjustment Screws

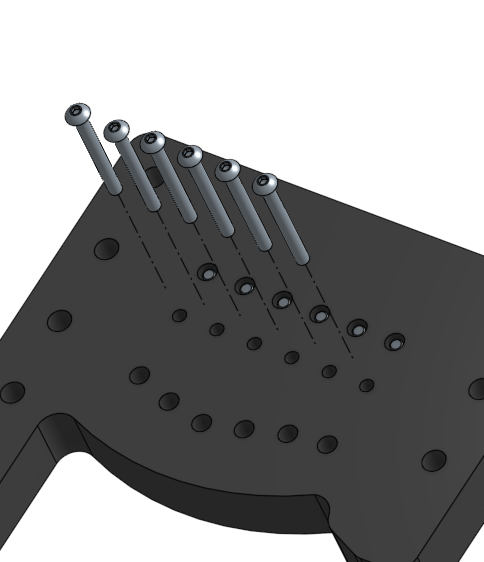
[picture p225: models/Bridge/Headless Bridge Plate/exploded views/Step 6 - Install Vertical Adjustment Screws.png]


## Step 7: Insert Slide In Nuts

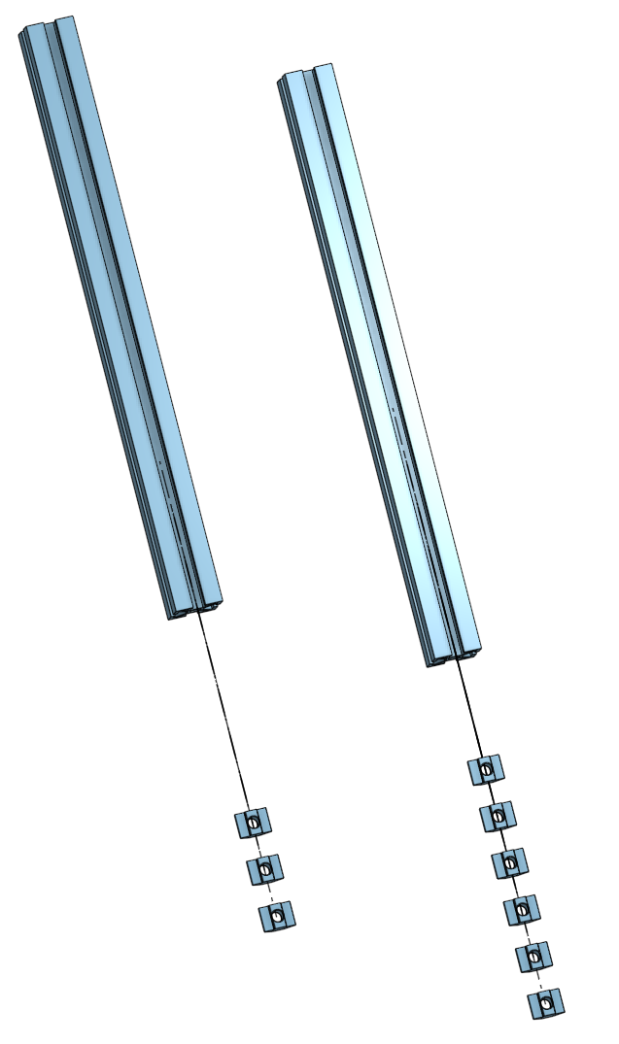
[picture p226: models/Bridge/Headless Bridge Plate/exploded views/Step 7 - Insert Slide-In Nuts.png]


## Step 8: Install Bottom Plate

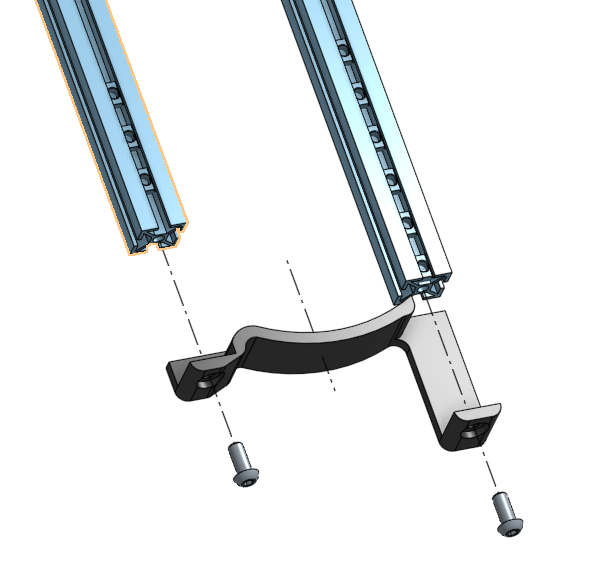
[picture p227: models/Bridge/Headless Bridge Plate/exploded views/Step 8 - Install Bottom Plate.png]


## Step 9: Install Footer onto 2020

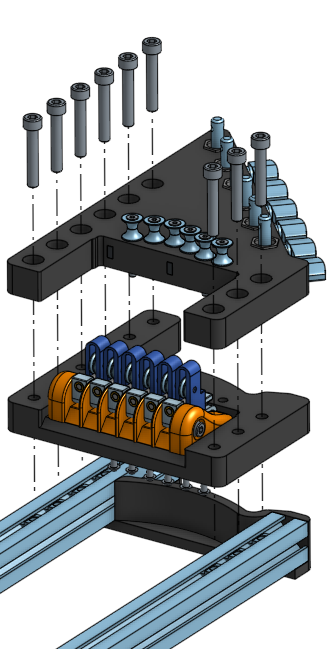
[picture p228: models/Bridge/Headless Bridge Plate/exploded views/Step 9 - Install Footer onto 2020.png]
