spikeon/exoguitar/models/Bridge/Thru-Body Bridge Plate - Bearing Bridge/ASSEMBLY.md

# Assembly for Thru Body Bridge Plate with Bearing Bridge

## Step 1: Insert Heat Set Inserts
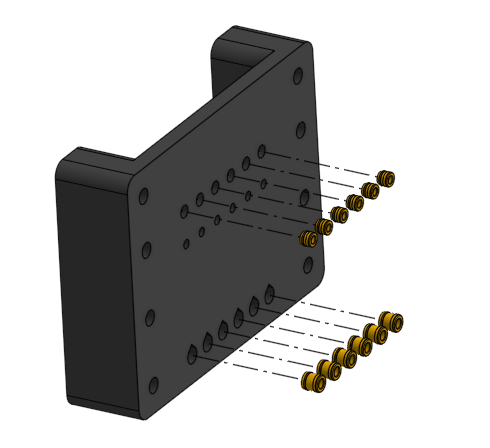
[picture p229: models/Bridge/Thru-Body Bridge Plate - Bearing Bridge/exploded views/Step 1 - Insert Heat Set Inserts.png]


## Step 2: Attach Bearing Bridge
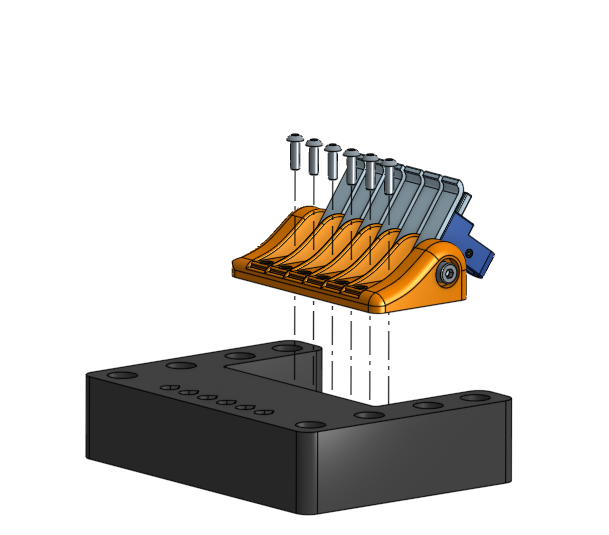
[picture p230: models/Bridge/Thru-Body Bridge Plate - Bearing Bridge/exploded views/Step 2 - Attach Bearing Bridge.png]


## Step 3: Attach Vertical Adjustment Screws
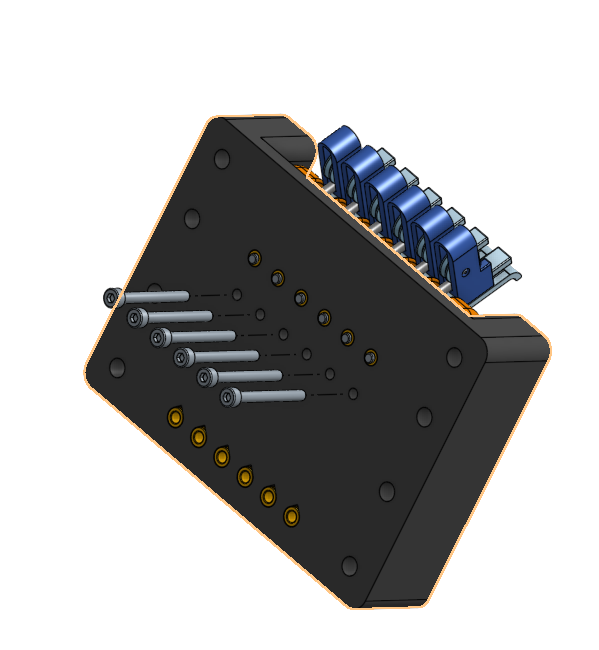
[picture p231: models/Bridge/Thru-Body Bridge Plate - Bearing Bridge/exploded views/Step 3 - Attach Vertical Adjustment Screws.png]


They should be sticking out of the top
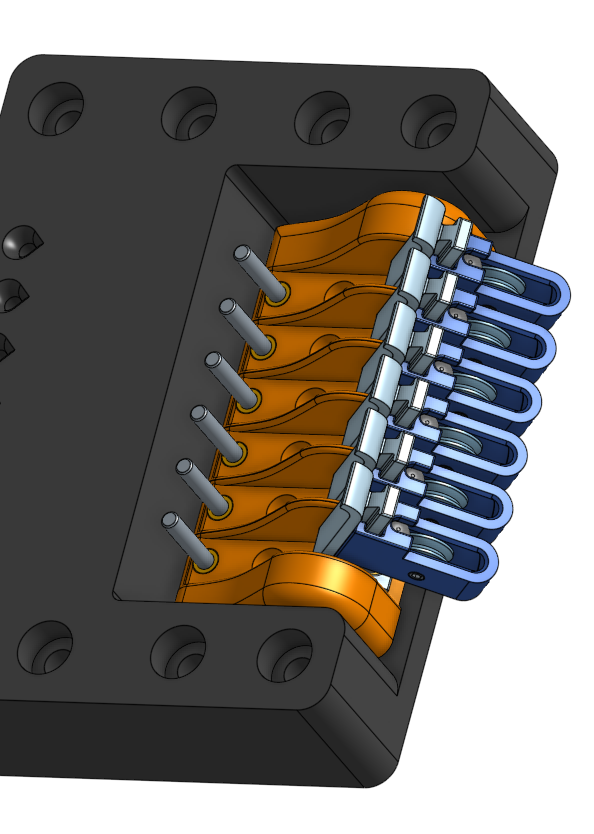
[picture p232: models/Bridge/Thru-Body Bridge Plate - Bearing Bridge/exploded views/Step 3b - Example of screws going thru.png]


## Step 4: Insert Slide In Nuts
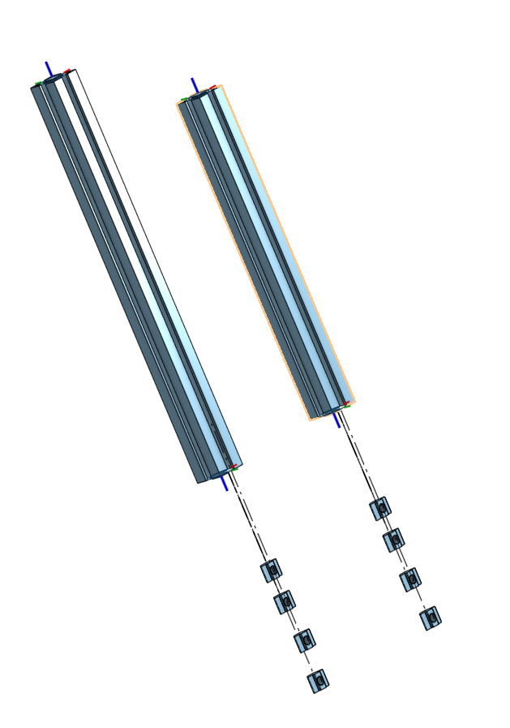
[picture p233: models/Bridge/Thru-Body Bridge Plate - Bearing Bridge/exploded views/Step 4 - Insert Slide In Nuts.png]


## Step 5: Attach Bridge to 2020
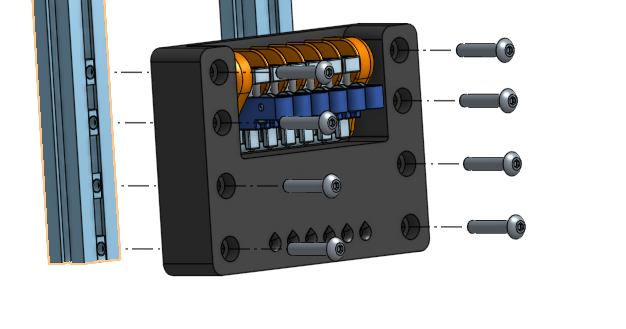
[picture p234: models/Bridge/Thru-Body Bridge Plate - Bearing Bridge/exploded views/Step 5 - Attach Bridge to 2020.png]


## Step 6: Solder wire to M4 Heat Set Inserts
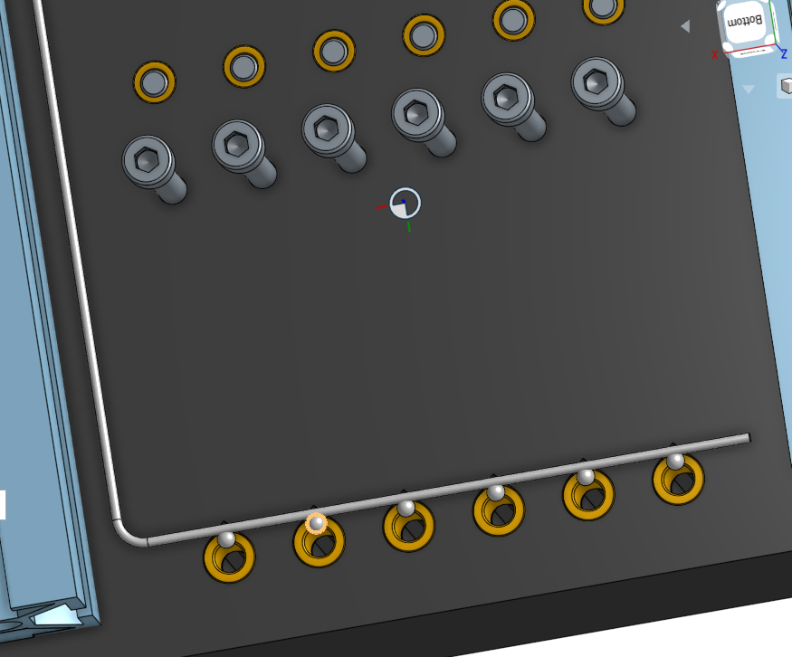
[picture p235: models/Bridge/Thru-Body Bridge Plate - Bearing Bridge/exploded views/Step 6 - Solder ground wire.png]
