spikeon/exoguitar/models/Face Plates/Single Humbucker - Bridge/ASSEMBLY.md

# Assembly
The assembly process is the same for all electronic faceplates, just with different pickups.  Example images contain Single Humbucker setup, but the rest are the same just with different hardware. 

## Step 1: Insert Slide In Nuts
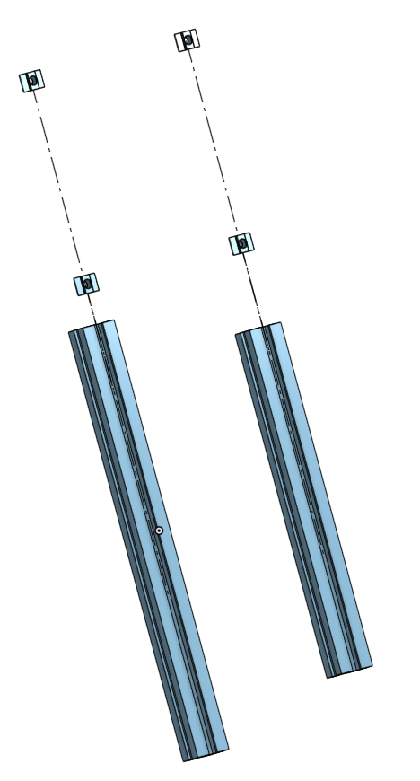
[picture p236: models/Face Plates/Single Humbucker - Bridge/exploded views/Step 1 - Insert Slide In Nuts.png]


## Step 2: Attach Faceplate to 2020
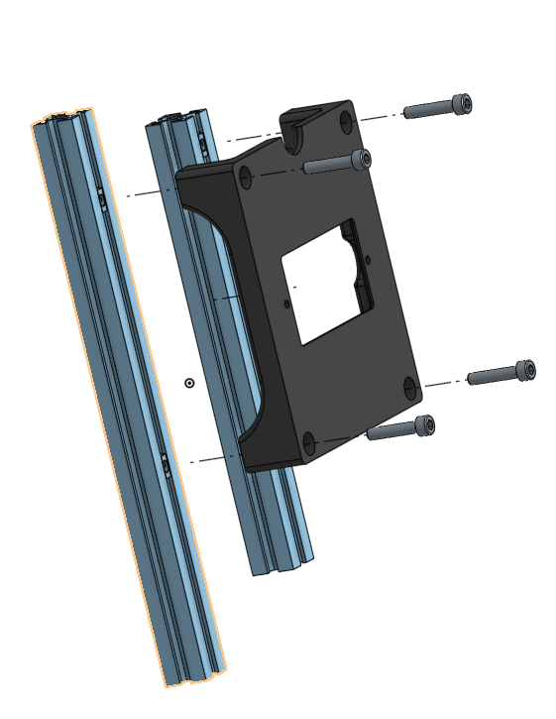
[picture p237: models/Face Plates/Single Humbucker - Bridge/exploded views/Step 2 - Attach Faceplate to 2020.png]


## Step 3: Attach Electronics
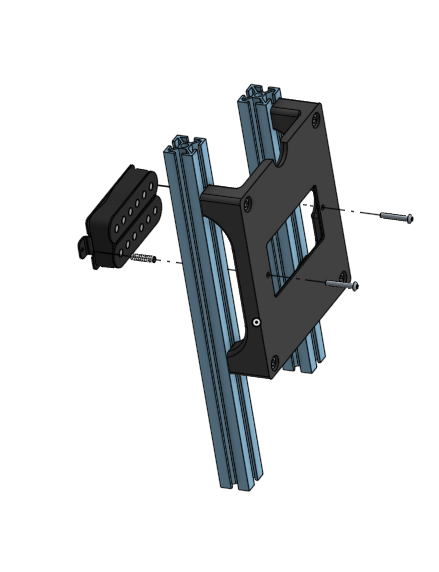
[picture p238: models/Face Plates/Single Humbucker - Bridge/exploded views/Step 3 - Attach Electronics.png]
