spikeon/exoguitar/models/Bridge/Bearing Bridge/ASSEMBLY.md

# Assembly

## Step 1: Assemble all Saddles
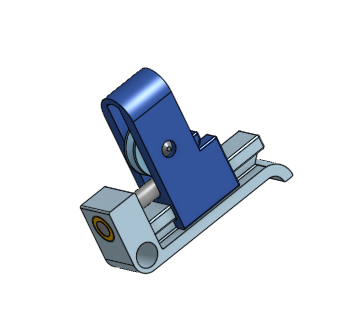
[picture p239: models/Bridge/Bearing Bridge/exploded views/Finished Saddle Assembly.png]
Finished Saddle


Do thie following steps 6 times: 

### Step 1a: Insert Horizontal Adjustment Screw
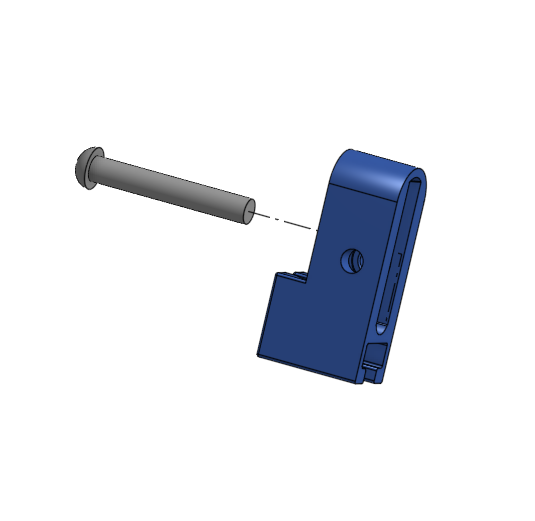
[picture p240: models/Bridge/Bearing Bridge/exploded views/Step 1 - Insert Horizontal Adjustment Screw.png]


### Step 1b: Install Bearing
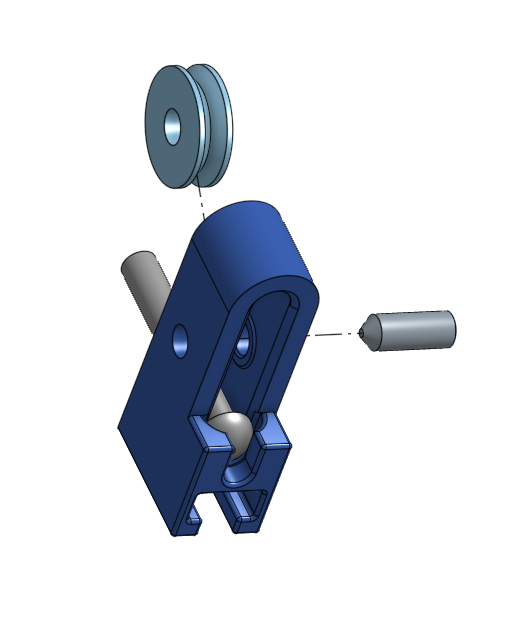
[picture p241: models/Bridge/Bearing Bridge/exploded views/Step 2 - Install Bearing.png]


### Step 1c: Insert M3 Heat Set Insert to Saddle
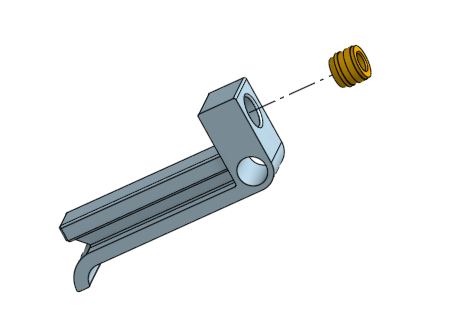
[picture p242: models/Bridge/Bearing Bridge/exploded views/Step 3 - Install Heat Insert.png]


### Step 1d: Put Slide on Rail
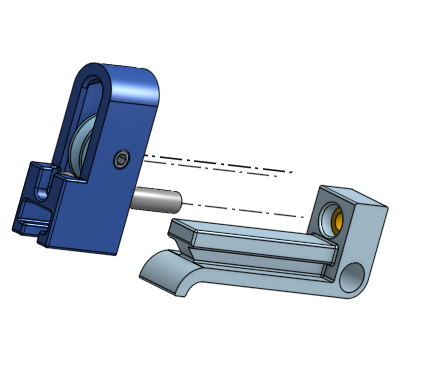
[picture p243: models/Bridge/Bearing Bridge/exploded views/Step 4 - Put slide on Rail.png]


## Step 2: Put in M4 Heat Set Inserts to Bridge
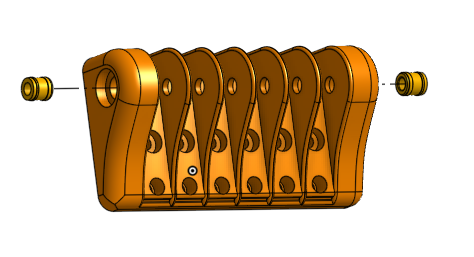
[picture p244: models/Bridge/Bearing Bridge/exploded views/Step 5 - Install M4 Heat Inserts.png]


## Step 3: Insert M3 Heat Set Inserts to Bridge
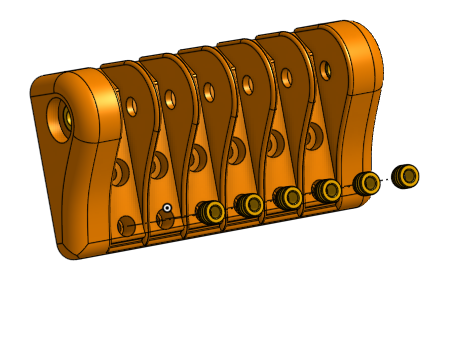
[picture p245: models/Bridge/Bearing Bridge/exploded views/Step 6 - Install M3 Heat Inserts.png]


## Step 4: Install Saddles
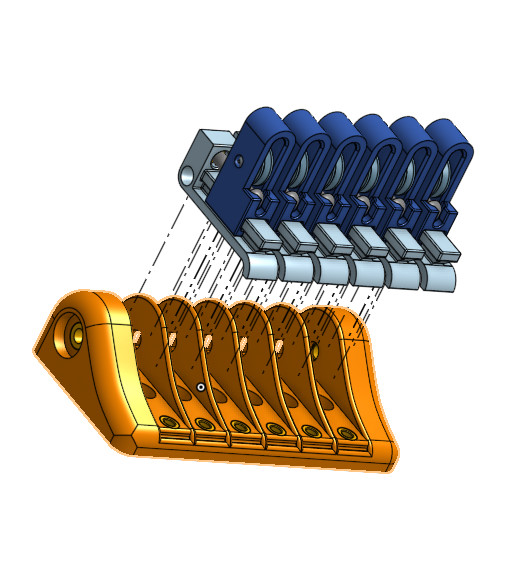
[picture p246: models/Bridge/Bearing Bridge/exploded views/Step 7 - Install Saddle Assemblies.png]


## Step 5: Insert M4 Screws
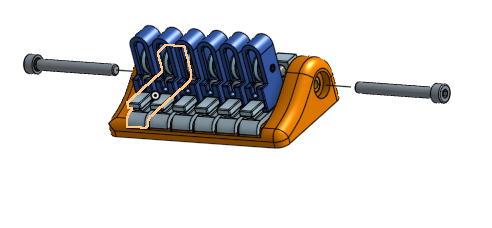
[picture p247: models/Bridge/Bearing Bridge/exploded views/Step 8 - Install M4 Screws.png]
