spikeon/exoguitar/models/Face Plates/Acoustic/ASSEMBLY.md

# Assembly

## Step 1: Insert Heat Set Inserts
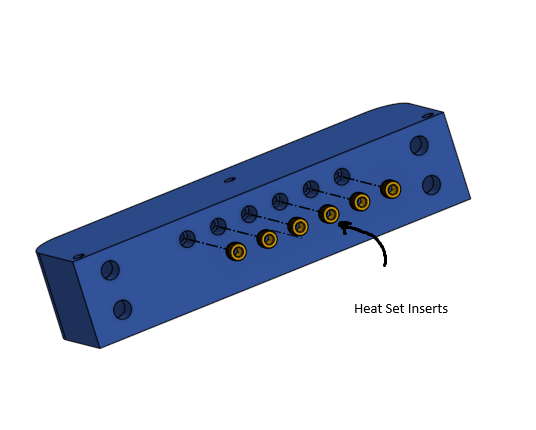
[picture p248: models/Face Plates/Acoustic/exploded views/Step 1.png]


## Step 2: Attach Chamber Isolation Plate
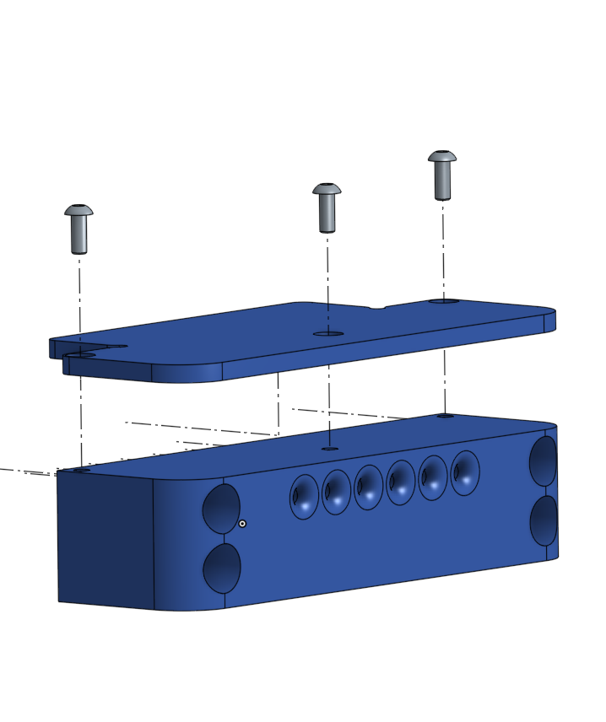
[picture p249: models/Face Plates/Acoustic/exploded views/Step 2.png]


## Step 3: Insert 2020 Slide In Nuts
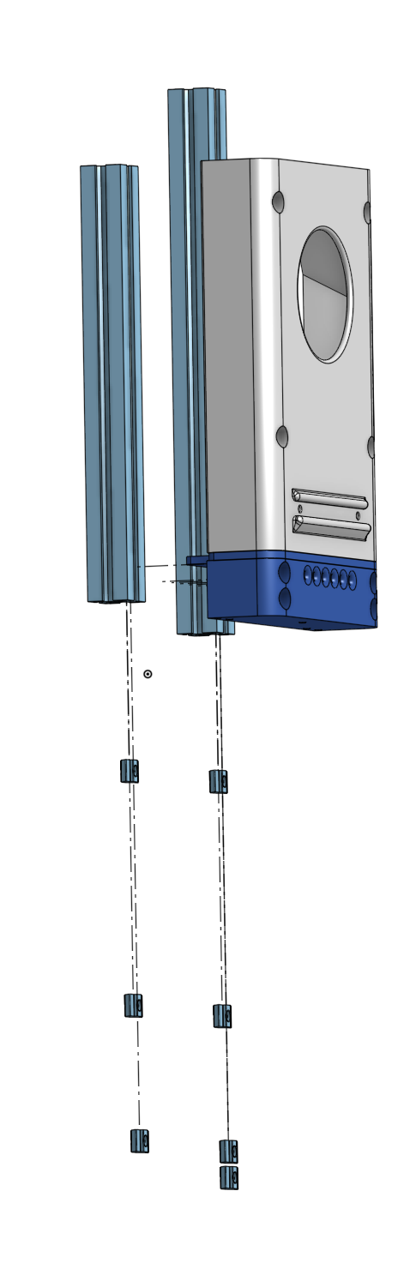
[picture p250: models/Face Plates/Acoustic/exploded views/Step 3.png]


## Step 4: Assemble Bridge
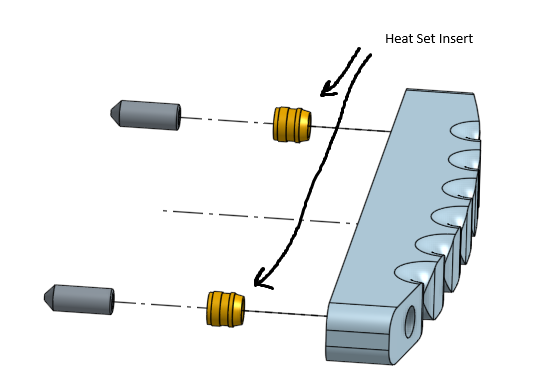
[picture p251: models/Face Plates/Acoustic/exploded views/Step 4.png]


## Step 5: Attach Face Plate and Bridge to 2020 Extrusion
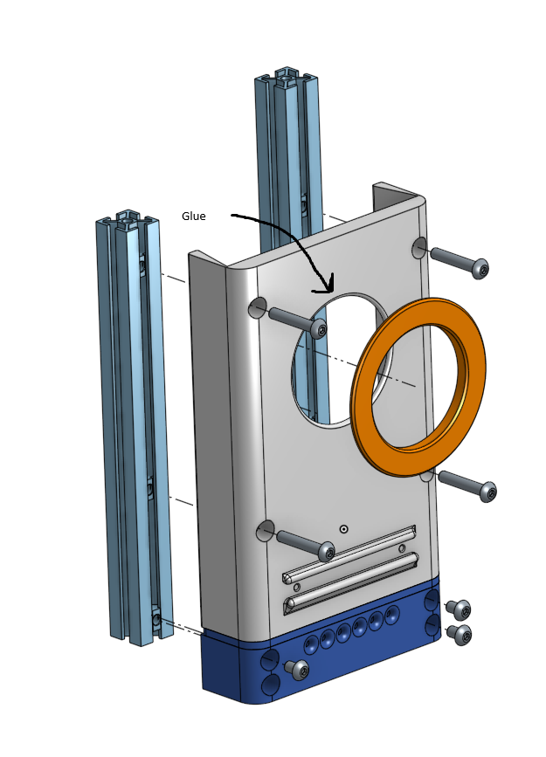
[picture p252: models/Face Plates/Acoustic/exploded views/Step 5.png]


Also, this is a good time to glue in the decorative ring

## Step 6: Insert Rear 2020 Slide In Inserts
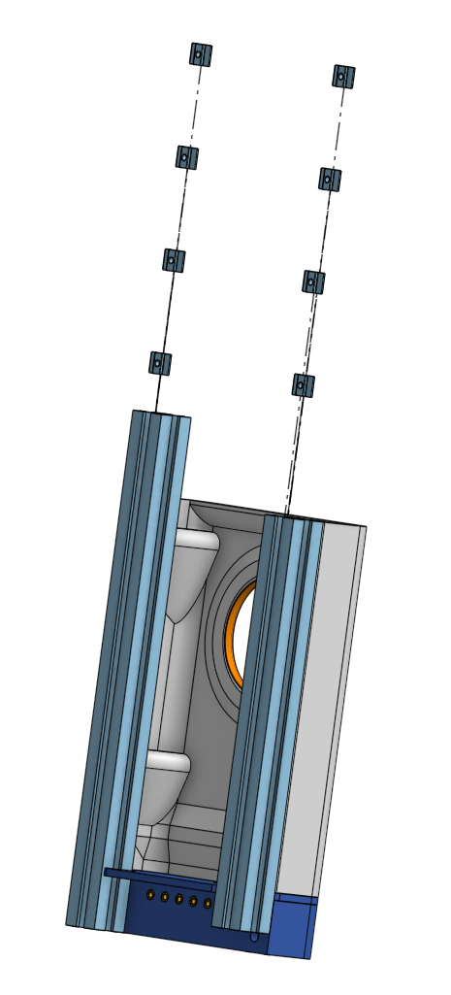
[picture p253: models/Face Plates/Acoustic/exploded views/Step 6.png]


## Step 7: Attach Back Plate
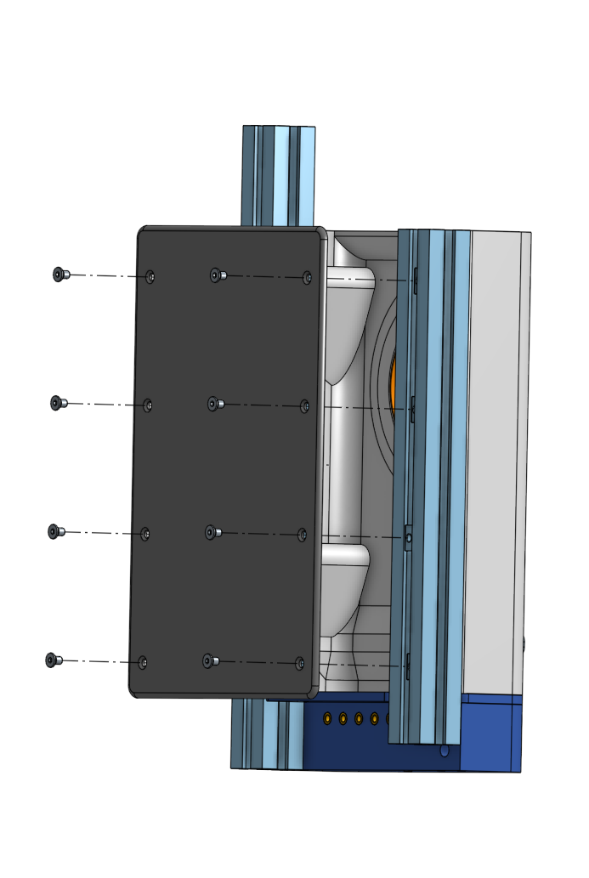
[picture p254: models/Face Plates/Acoustic/exploded views/Step 7.png]
