spikeon/exoguitar/models/Head/Headless/ASSEMBLY.md

# Assembly

## Step 1: Insert Heat Set Inserts
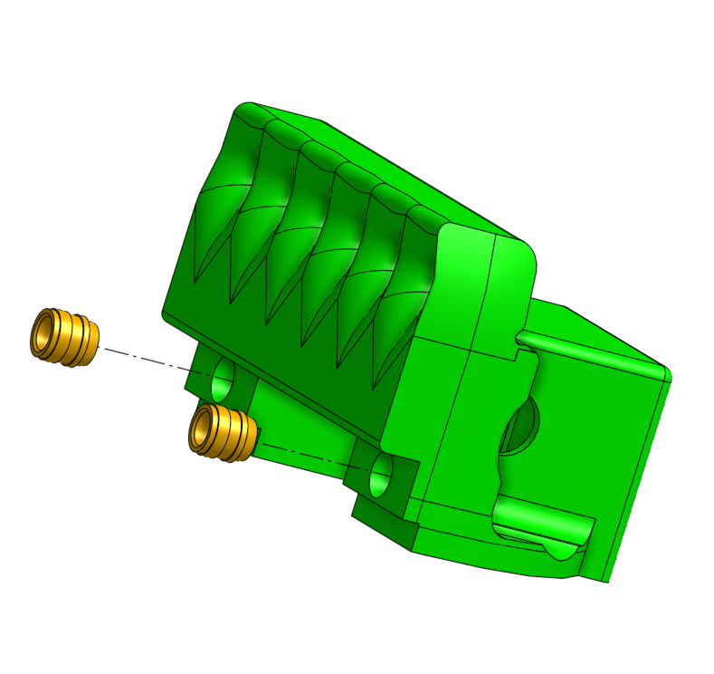
[picture p255: models/Head/Headless/exploded views/Step 1 - Heat Set Inserts - Front.png]
Front

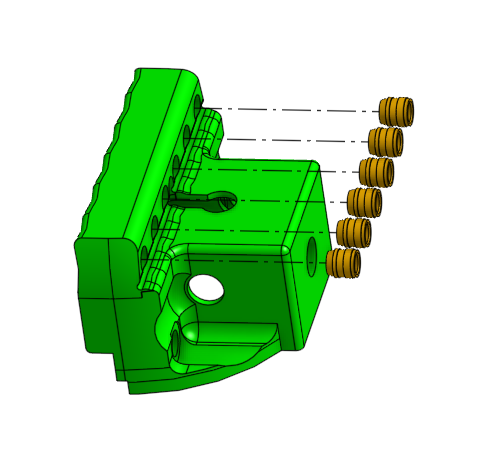
[picture p256: models/Head/Headless/exploded views/Step 1 - Heat Set Inserts - Back.png]
Back


## Step 2: Install Ground wire

Solder this wire to the heat set inserts. 

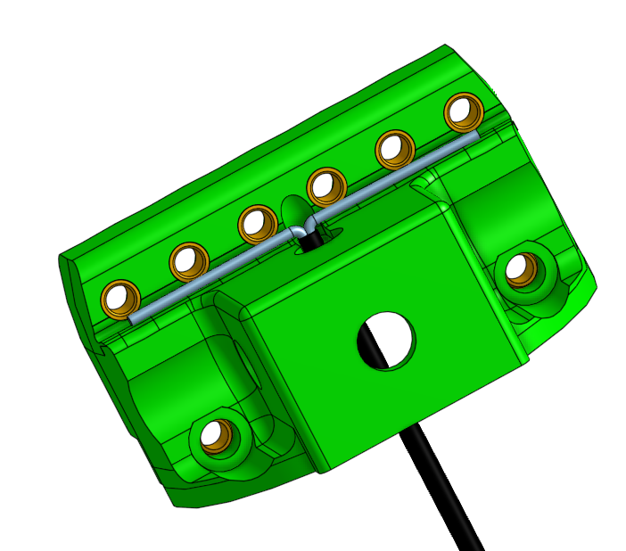
[picture p257: models/Head/Headless/exploded views/Step 2 - Install Ground Wire.png]
Wire


## Step 3: Install Nut Adjustment Screws
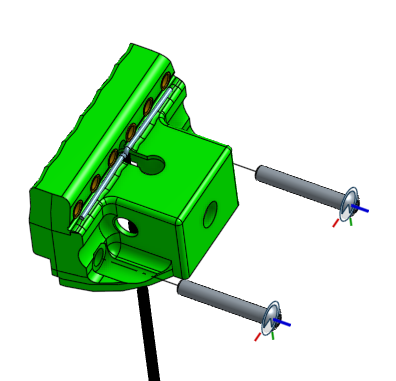
[picture p258: models/Head/Headless/exploded views/Step 3 - Install Nut Adjustment Screws.png]
Nut Adjust


## Step 4: Install 2020
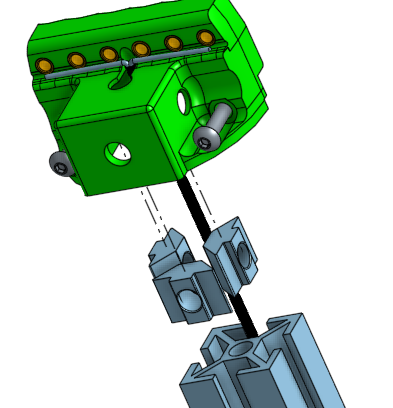
[picture p259: models/Head/Headless/exploded views/Step 4 - Attach 2020.png]

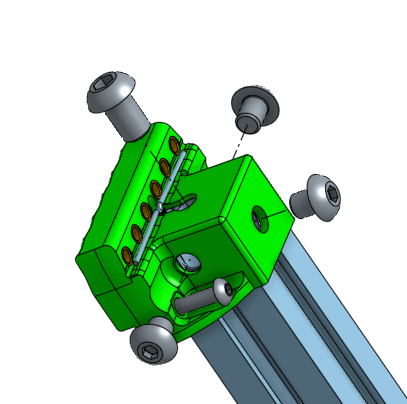
[picture p260: models/Head/Headless/exploded views/Step 5 - Attach 2020 Screws.png]
2020 Screw
