spikeon/exoguitar/models/Head/Arrow/ASSEMBLY.md

# Assembly

## Step 1: Put in Heat Set Inserts
Heat Inserts - Front Exploded View
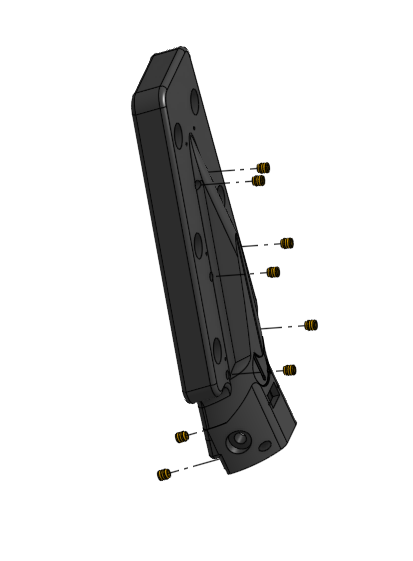
[picture p261: models/Head/Arrow/exploded views/Step 1 - Insert Heat Set Inserts Back.png]
Heat Inserts - Back Exploded View


## Step 2: Put in Tuning Pegs
Bearings - Exploded View

## Step 3: Install Trees
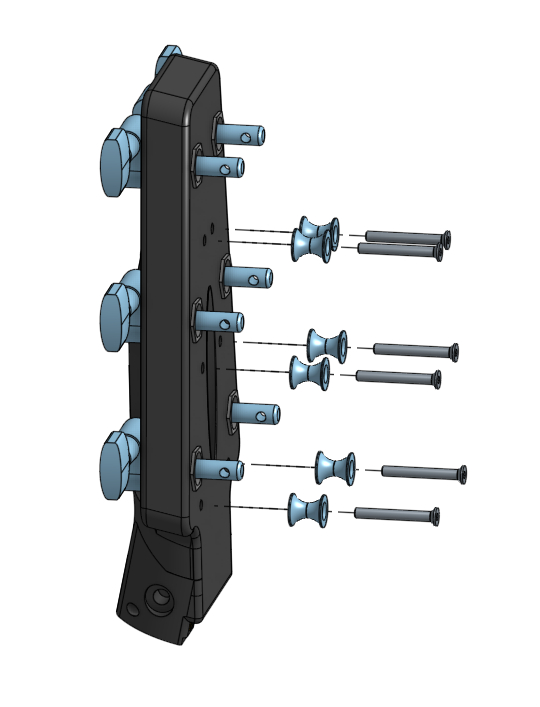
[picture p262: models/Head/Arrow/exploded views/Step 3 - Install Trees.png]
Trees


## Step 4: Put in Nut Adjusment Screws
Nut Adjusters

## Step 5: Attach 2020


## Step 6: Attach 2020 Screws
2020 Screws

## Step 7: Put in M5x45 Screws
M5x45
