spikeon/exoguitar/models/Head/Arasaka/exploded views/Assembled.png

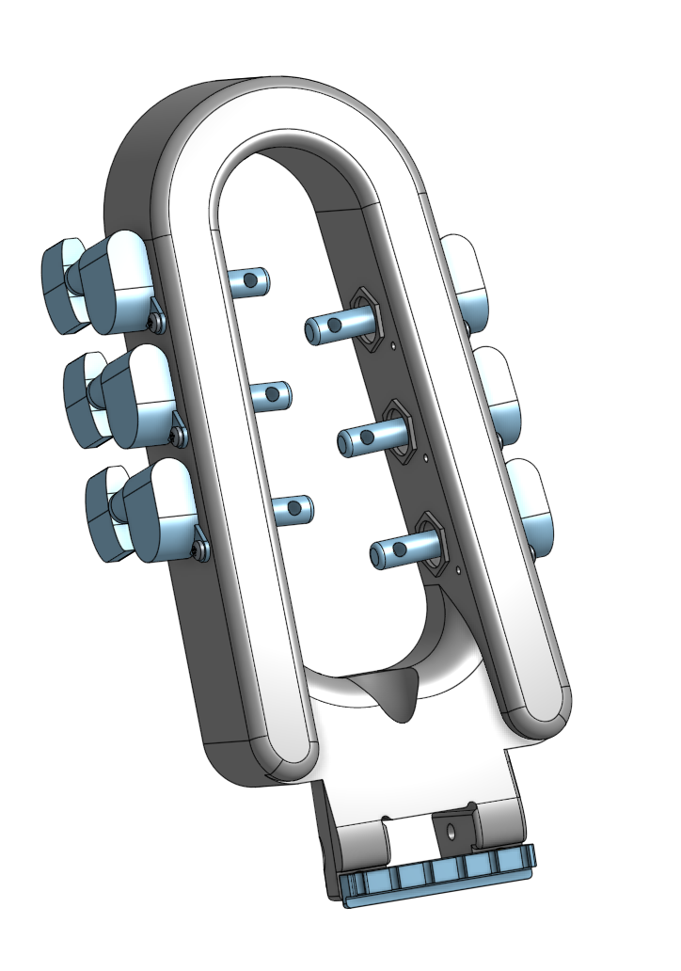
models/Head/Arasaka/exploded views/Assembled.png
