spikeon/exoguitar/models/Wing Sets/Arasaka/Wiring Diagram.png

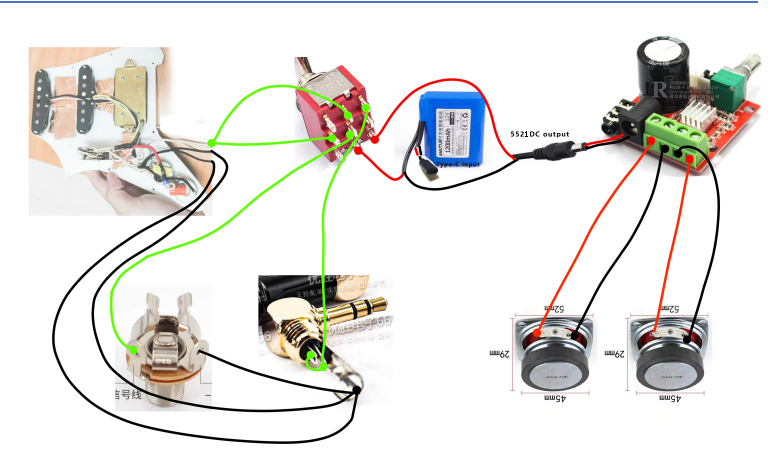
models/Wing Sets/Arasaka/Wiring Diagram.png
