spikeon/exoguitar/models/Bridge/Tune O' Matic - Single Plate/photos/thumb.tall.png

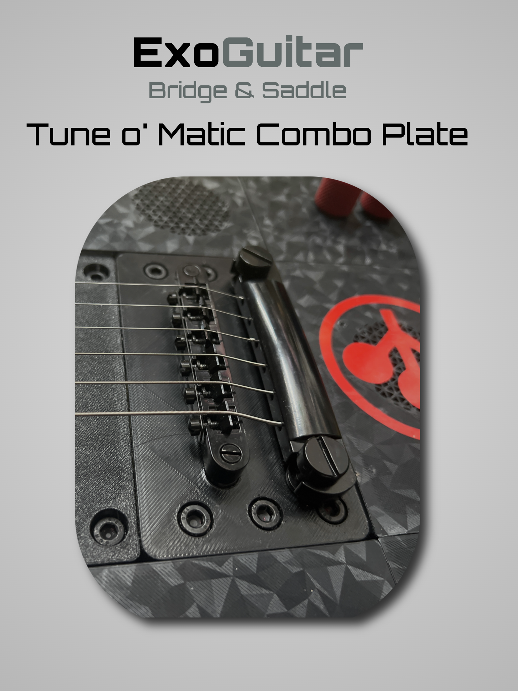
models/Bridge/Tune O' Matic - Single Plate/photos/thumb.tall.png
