spikeon/exoguitar/models/Bridge/Tune O' Matic - Single Plate/photos/thumb.wide.png

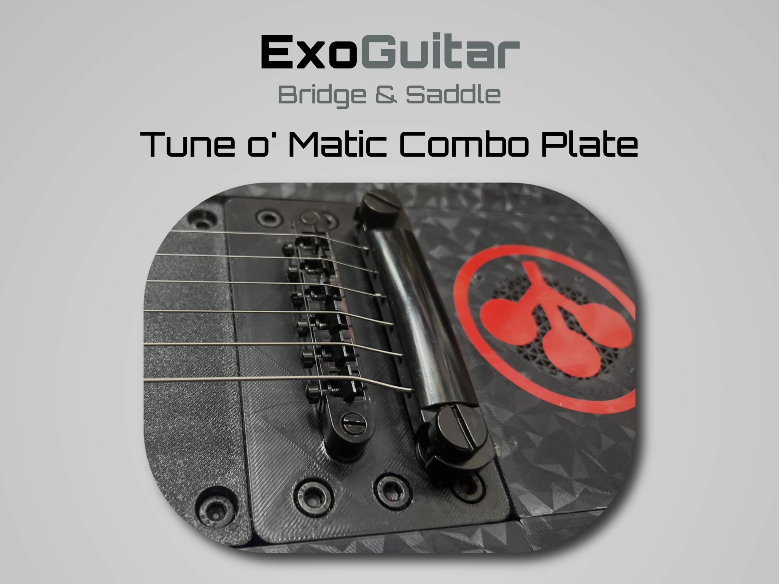
models/Bridge/Tune O' Matic - Single Plate/photos/thumb.wide.png
